ten-point-nine/freETarget/Documentation/Multi Function Switches.docx

# freETarget

Application Note: Multi Function Switches

SUMMARY

freETarget supports a pair of push button switches that can be used to customize the operation of the unit while in the target holder.

MULTIFUNCTION SWITCHES

There are two switches that can be used interchangeably, ie what can be done with A can be done with B. The JSON string {“MFS”:VVVVV} controls the function of the switches in tap or hold as shown in Table 1. The functions available are shown in Table 2.

Table 1: MFS Control

Value | Use
Vxxxx | Value controls hold on Switches 1 & 2
xVxxx | Value controls Tap on Switch 2
xxVxx | Value controls Tap on Switch 1
xxVx | Value controls Hold on Switch 2
xxxxV | Value controls Hold on Switch 1

Table 2: MFS Values

Value | Use
0 | Tap to wake up from sleep
1 | Paper feed witness paper
2 | Adjust LED brightness
3 | Advance paper one shot cycle
4 | PC Shot Test
5 | Put target to sleep or wake it up
6
7
8
9

OPERATION

The operation of the switches is controlled by how long the switches are pressed for

Tap: Press switch for less than ½ second

Hold: Press and hold the switch for more than ½ second

Holding 1&2 and resetting the power will put the configuration back to the factory defaults.

EXAMPLES

Example: 20351

2 – Hold 1 & 2 to adjust LED brightness

0 – Tap 2 to wake up from sleep

3 – Tap 1 to advance paper one shot cycle

5 – Hold 2 to put target to sleep

1 – Hold 1 to load paper feed
