ten-point-nine/freETarget/Documentation/Pictures/50 Meter Pistol Target.docx

# freETarget

Application Note: 50 Meter Pistol Target

SUMMARY

freeETarget can be used as a 50 meter pistol target with the same hardware as the conventional 10 meter target. The differences being the use of a semi-ridgid backing material and setting the sensors for the larger paper.

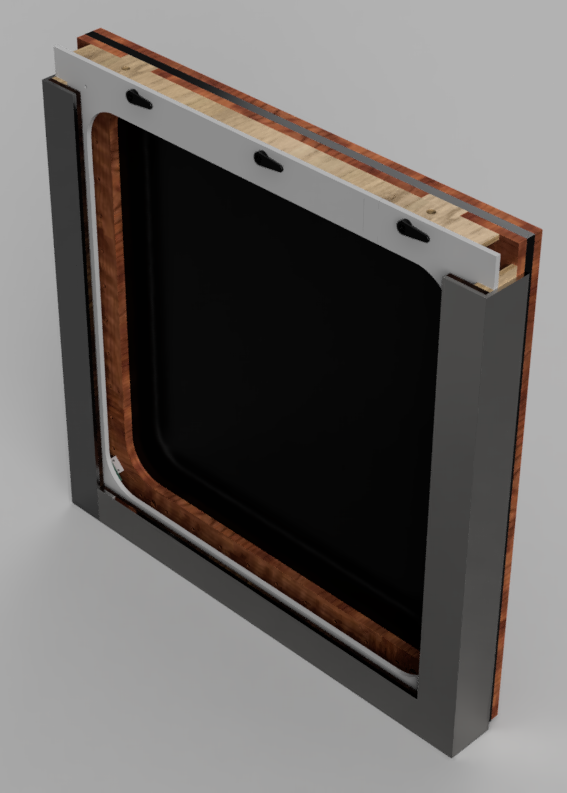
[picture p22: figure]

Figure 1” 50 Meter Pistol Target

CONSTRUCTION

Construction follows the same process as a simple 10 meter air target. The differences are:

- Larger 778 mm sensor spacing
- No lights or witness paper
- Heavy rubber mat before the bullet trap

The target is constructed by laminating a series of items together. The construction is shown in Figure 2 and itemized in Table

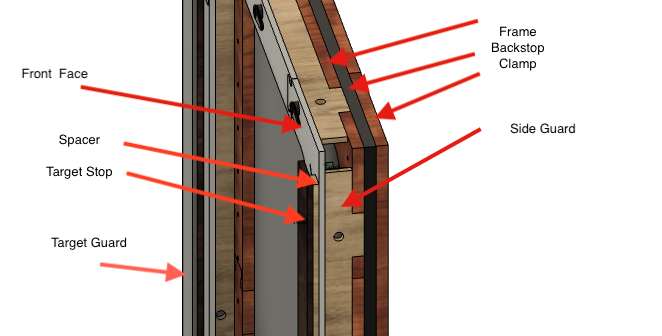
[picture p23: figure]

Figure 2: Target Build Up

Table 1: Target Components

Item | Description | Material
Frame | Rectangular frame to assemble target | ½” Plywood
Backstop | Rubber mat to sound projectile | ¼” Neoprene truck liner
Clamp | Rectangular frame to hold backstop | ½ Plywood
Sensor Mount | Plywood sensor mount (not shown) | ½” Plywood
Sensor | Electronic circuit (not shown)
Sie Guard | Prevent debris from getting to sensors | ¼” Plywood
Front Face | Rectangular frame to hold target in place | ¼” Plywood
Spacer | Strip of material spce cardboard backer | ¼” Plywood
Target Stop | Strip of material to hold target in place | ¼” Plywood
Target Guard | 1/8” Steel L bracket to protect from shots | 2”x2”x1/8 Steel L bracket

Start by construction a target frame large enough to support the target. The frame illustrated in Figure 3 is 650 mm x 650mm ½” plywood. To save on wood and fit into a small workshop, the frame is made from four hocky-stick segments

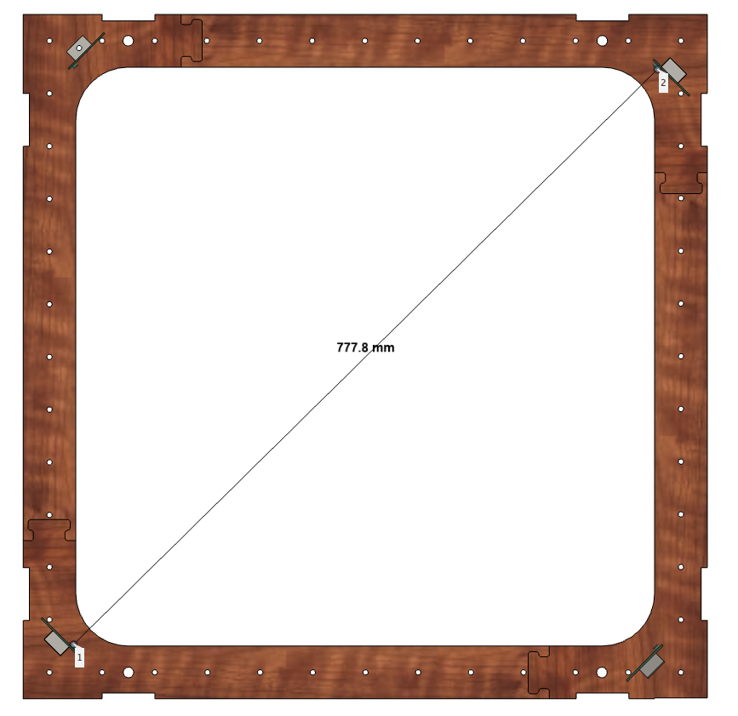
[picture p24: figure]

Figure 3: Sensor Location

Build the clamp using the same construction as the frame. If you made the frame from four segments as shown in Figure 3, reverse the segments to that the joints don’t line up.

Locate the rubber backstop between the frame and clamp. Drill 5mm holes between the frame and clamp, through the rubber every 50mm. Use 5x40mm bolts from the front to the back and tighten with nuts. When finished the target will be a ridged frame

Attach the sensors and cables to the sensor mounts

Build the front face using ¼” plywood similar to the frame.

Align the front face to the frame and drill 5mm holes through the sensor mounts
