ten-point-nine/freETarget/Documentation/Technical/freETarget Layout.pdf

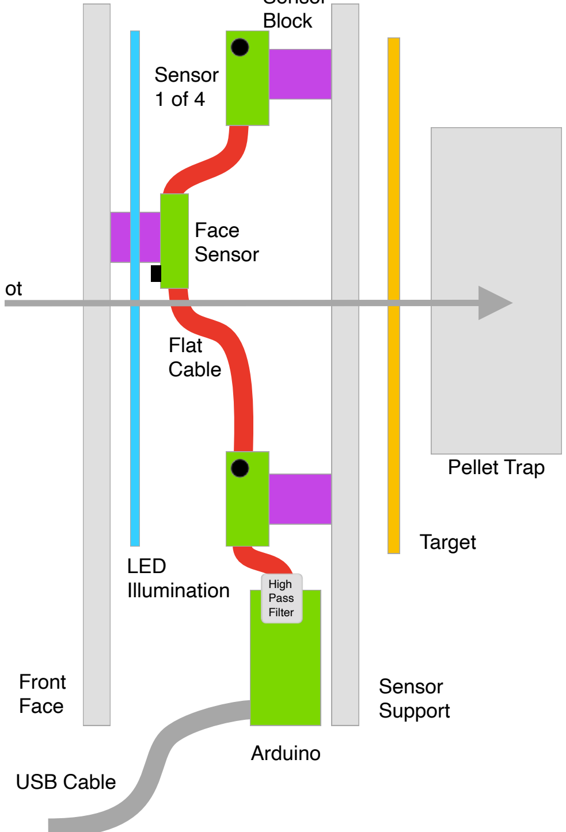
[picture p29: figure]
Front Face; LED Illumination; Flat Cable; Sensor Support; Arduino; Block; Face Sensor; Sensor 1 of 4; Target; Pellet Trap; USB Cable; High Pass Filter; Shot

Sensor
