ten-point-nine/freETarget/Documentation/Technical/Sensor Geometry.pdf

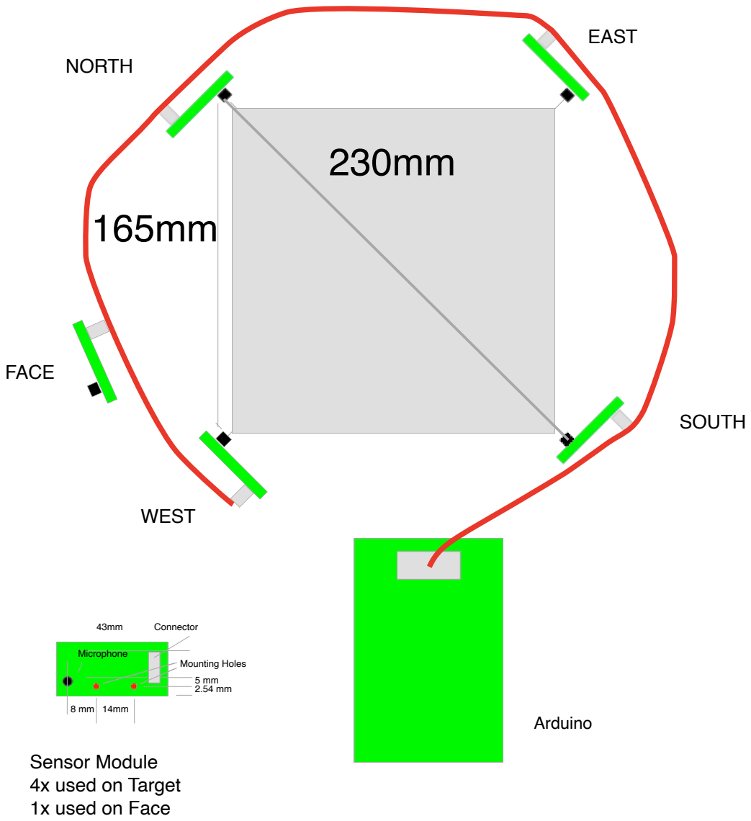
[picture p30: figure]
EAST; NORTH; SOUTH; WEST; 230 mm Dia; Microphone; Mounting Holes; Sensor Module 4x used on Target 1x used on Face; Arduino; Connector; FACE
