ten-point-nine/freETarget/Documentation/Pictures/Illustrations/Sensor Template.pdf

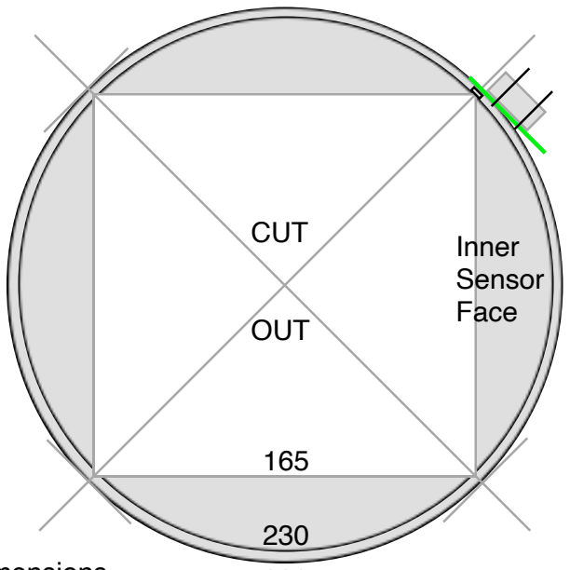
[picture p32: figure]
CUT; OUT; Inner Sensor Face

45.5

2.5
15 14

3dia

7.5

23

7.5

50mm
x
50mm
Print
Reference
All dimensions | 239
in mm

Outer
Block
Face
