ten-point-nine/freETarget/Mechanical/CNC/6mm Panel/Door Dimensions.pdf

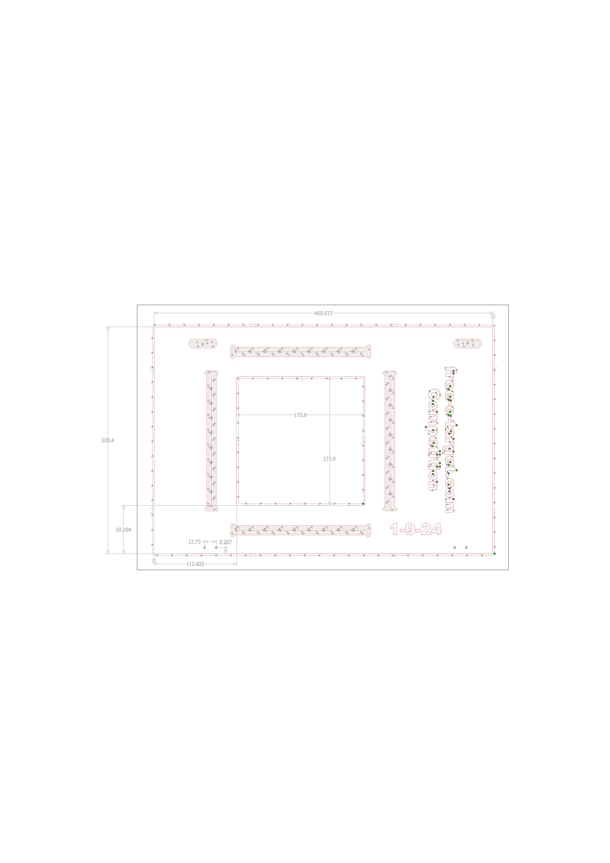
[picture p33: page 1]
