ten-point-nine/freETarget/Documentation/Technical/Sample Calculations.pdf

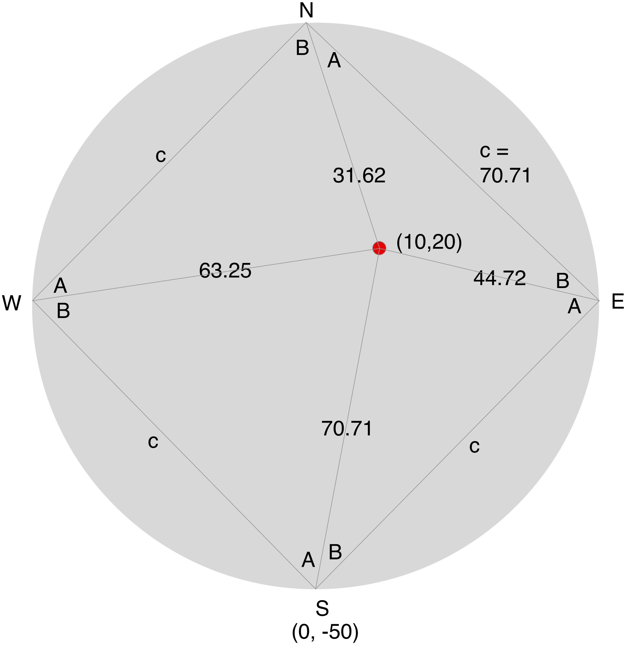
[picture p34: figure]

(50,0)
(-50,0)

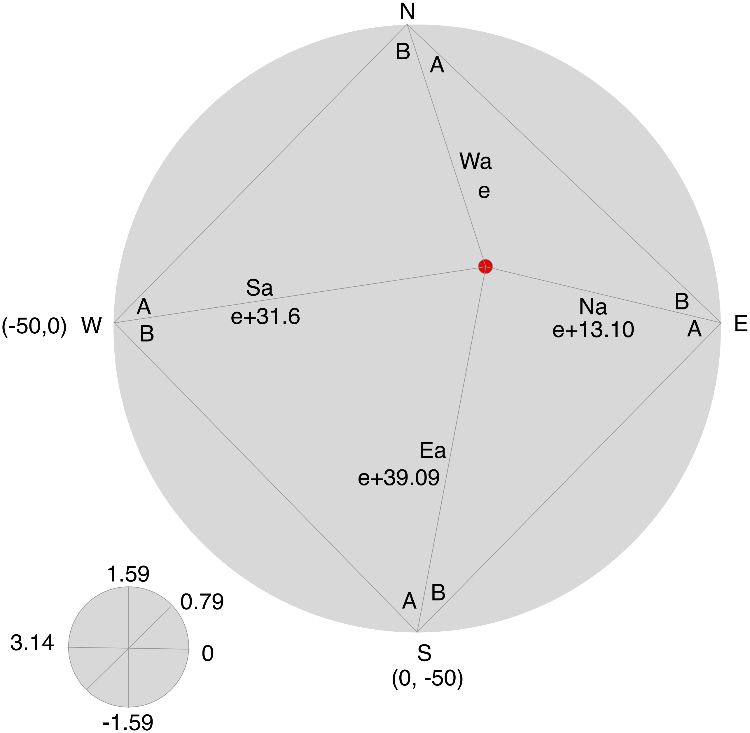
[picture p35: figure]

(50,0)

(50,0)

A

a

C

B

b

c

a^2 = b^2 + c^2 - 2bc*cos(A)

cos(A) = a^2 - b^2 -c^2
-2bc

( a^2 - b^2 - c^2 )
( | -2bc. | )

A = cos-1
