ten-point-nine/freETarget/Documentation/Pictures/Illustrations/Annotated Circuit.pdf

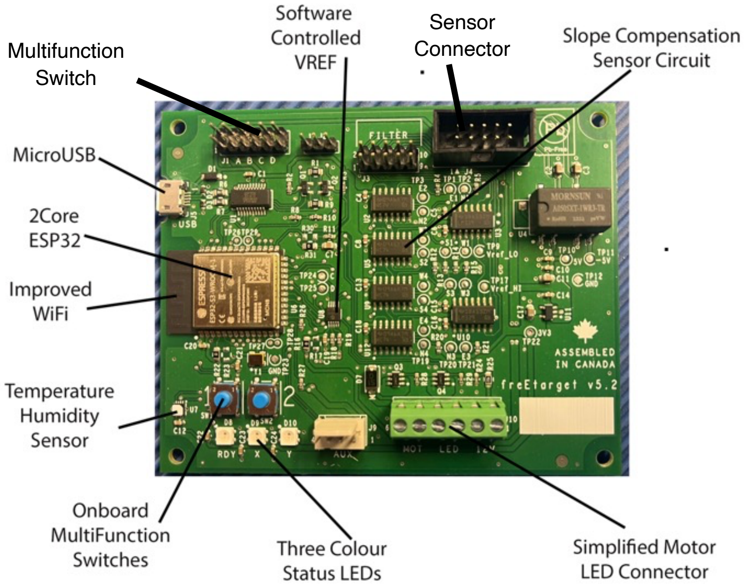
[picture p36: page 1]
