ten-point-nine/freETarget/Documentation/Pictures/15 Meter USB Cable.jpg

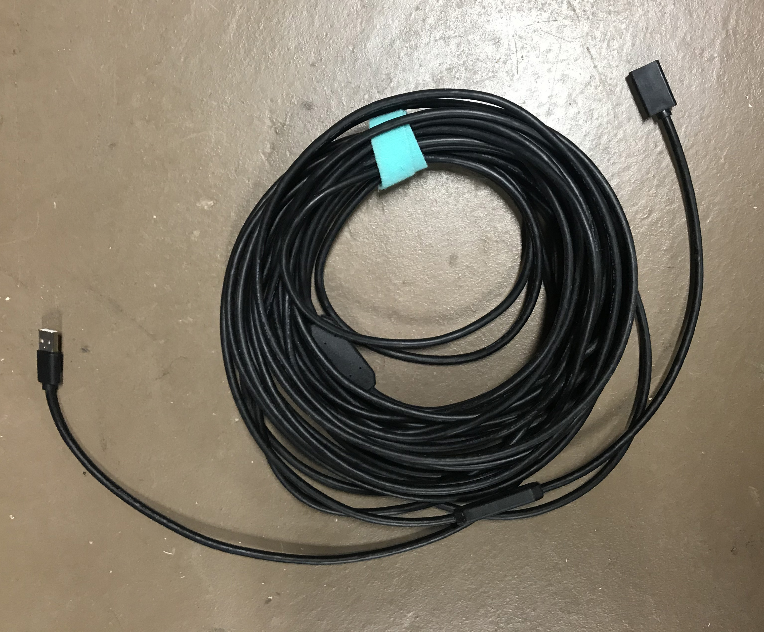
Documentation/Pictures/15 Meter USB Cable.jpg
