ten-point-nine/freETarget/Documentation/Pictures/Accessory Connector.png

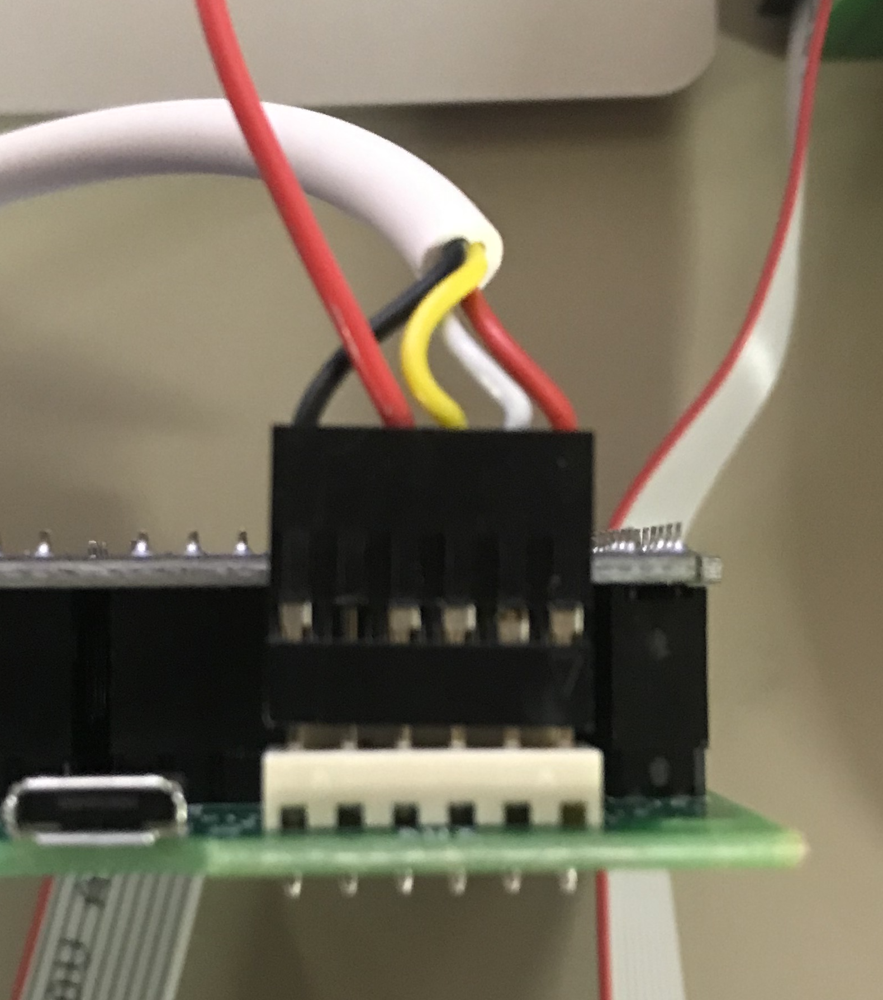
Documentation/Pictures/Accessory Connector.png
