ten-point-nine/freETarget/Documentation/Pictures/Board.jpg

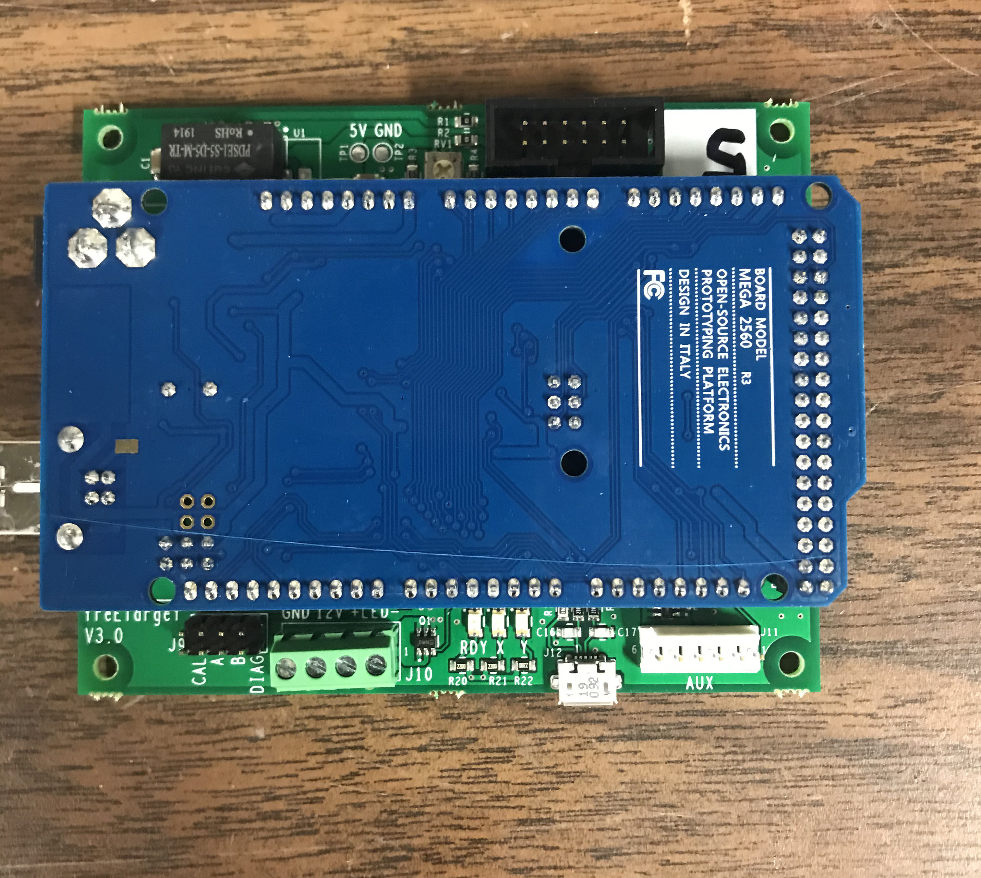
Documentation/Pictures/Board.jpg
