ten-point-nine/freETarget/Documentation/Pictures/Cut Cardboard.png

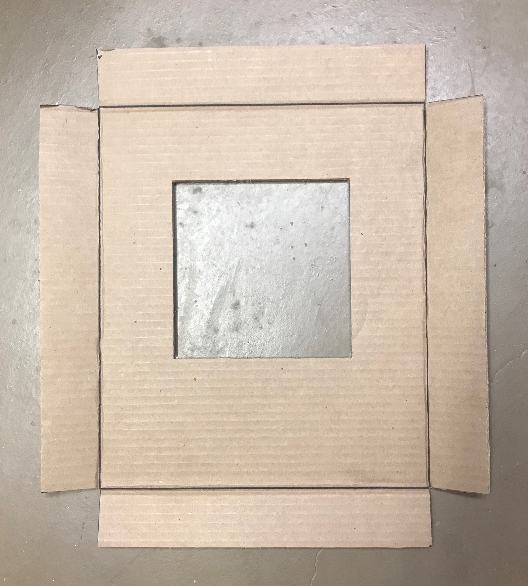
Documentation/Pictures/Cut Cardboard.png
