ten-point-nine/freETarget/Documentation/Pictures/DC Motor Connection II.png

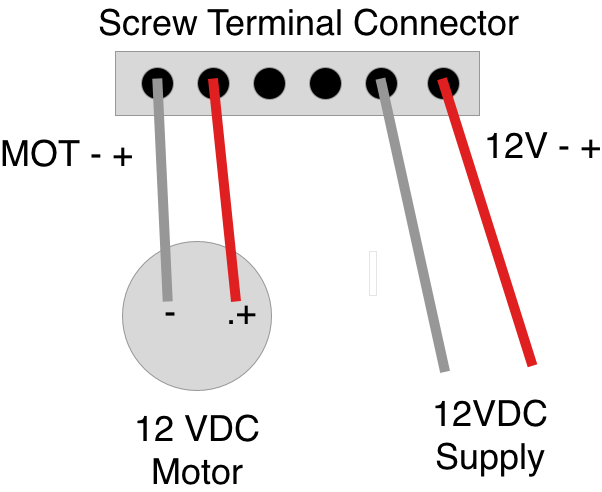
Documentation/Pictures/DC Motor Connection II.png
