ten-point-nine/freETarget/Documentation/Pictures/Folded Cardboard.png

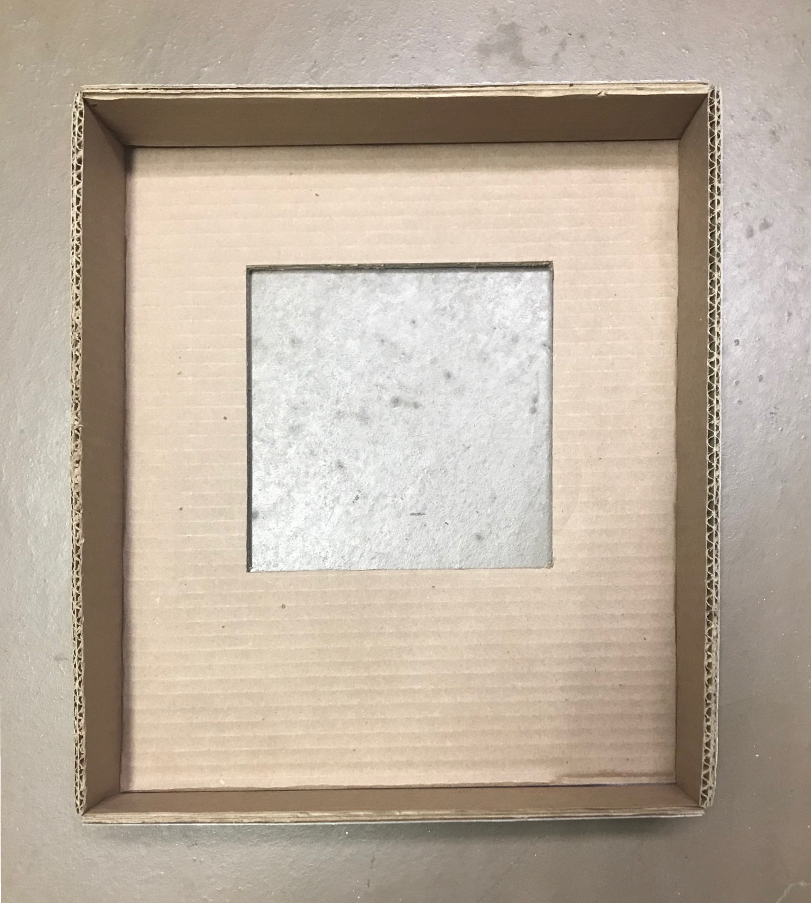
Documentation/Pictures/Folded Cardboard.png
