ten-point-nine/freETarget/Documentation/Pictures/freETarget Rapid Fire.png

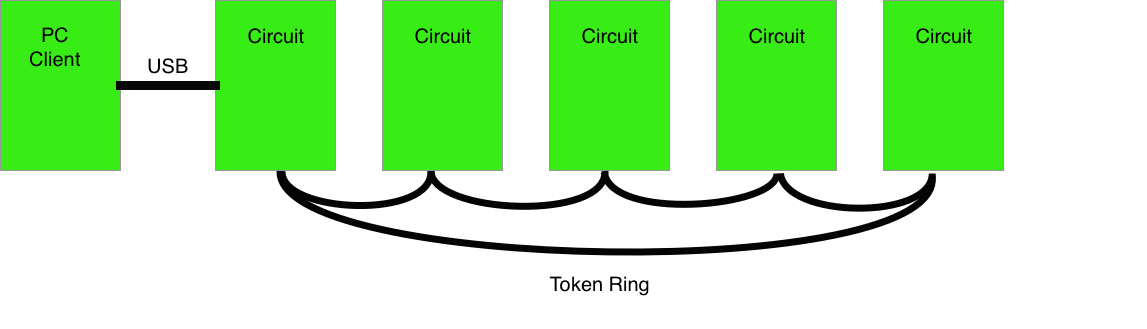
Documentation/Pictures/freETarget Rapid Fire.png
