ten-point-nine/freETarget/Documentation/Pictures/freETarget.jpg

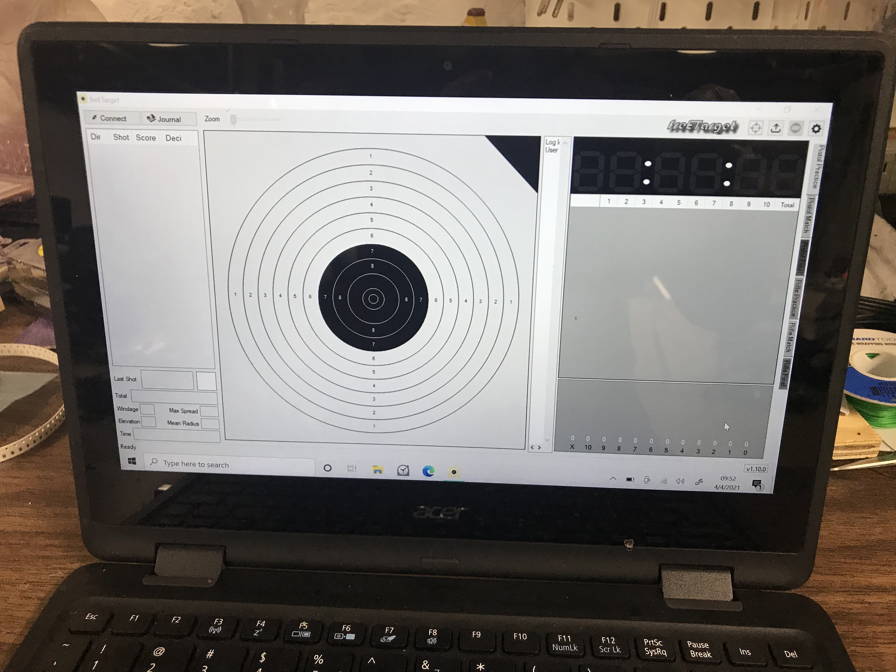
Documentation/Pictures/freETarget.jpg
