ten-point-nine/freETarget/Documentation/Pictures/GRID_PATTERN.jpg

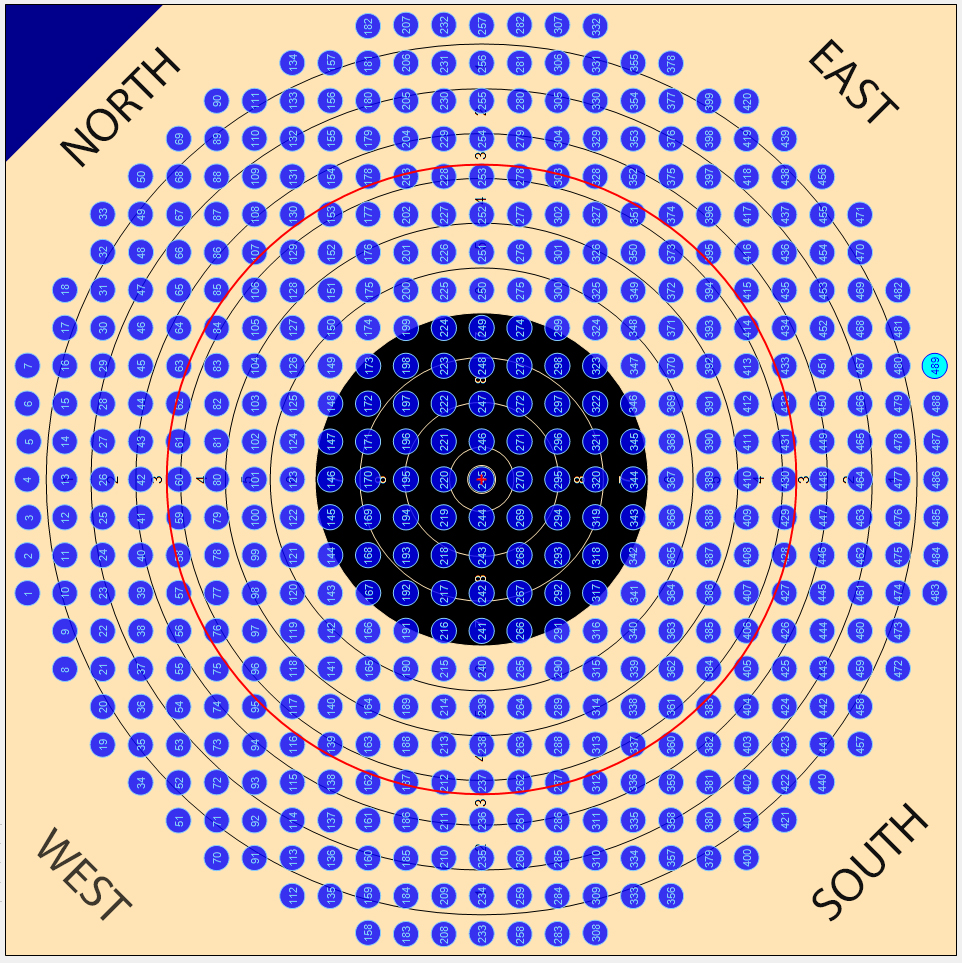
Documentation/Pictures/GRID_PATTERN.jpg
