ten-point-nine/freETarget/Documentation/Pictures/Illustrations/Application Configuration.png

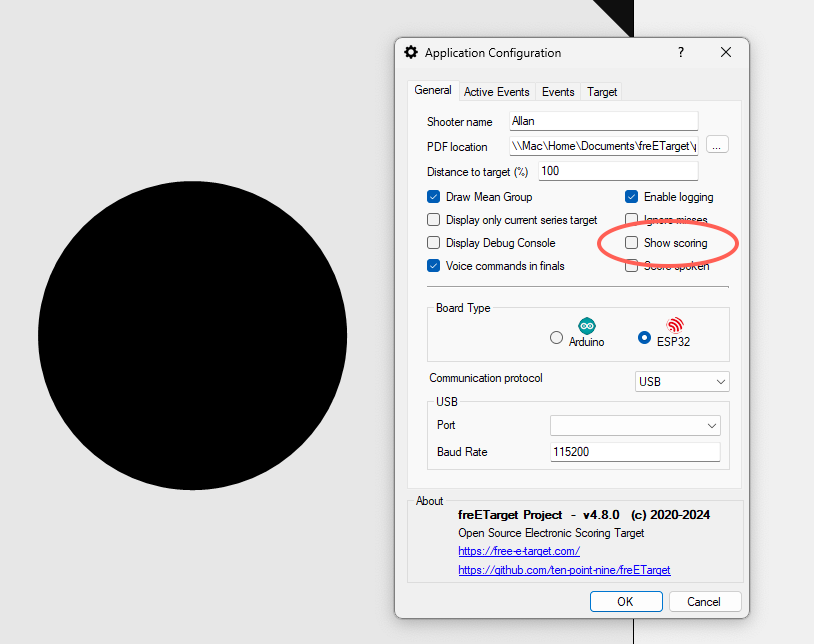
Documentation/Pictures/Illustrations/Application Configuration.png
