ten-point-nine/freETarget/Documentation/Pictures/Illustrations/Ethernet Cable V5 Harness.png

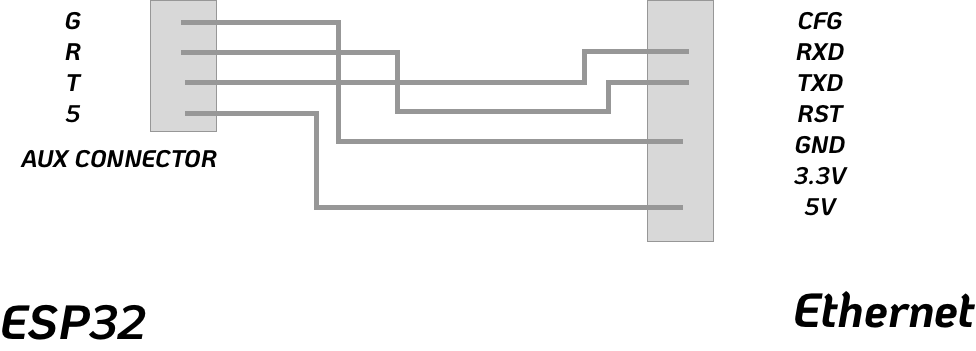
Documentation/Pictures/Illustrations/Ethernet Cable V5 Harness.png
