ten-point-nine/freETarget/Documentation/Pictures/Illustrations/Flat Cable.png

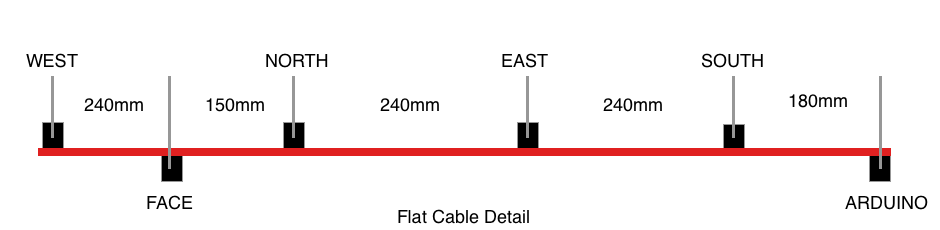
Documentation/Pictures/Illustrations/Flat Cable.png
