ten-point-nine/freETarget/Documentation/Pictures/Illustrations/freETarget Basic Layout.png

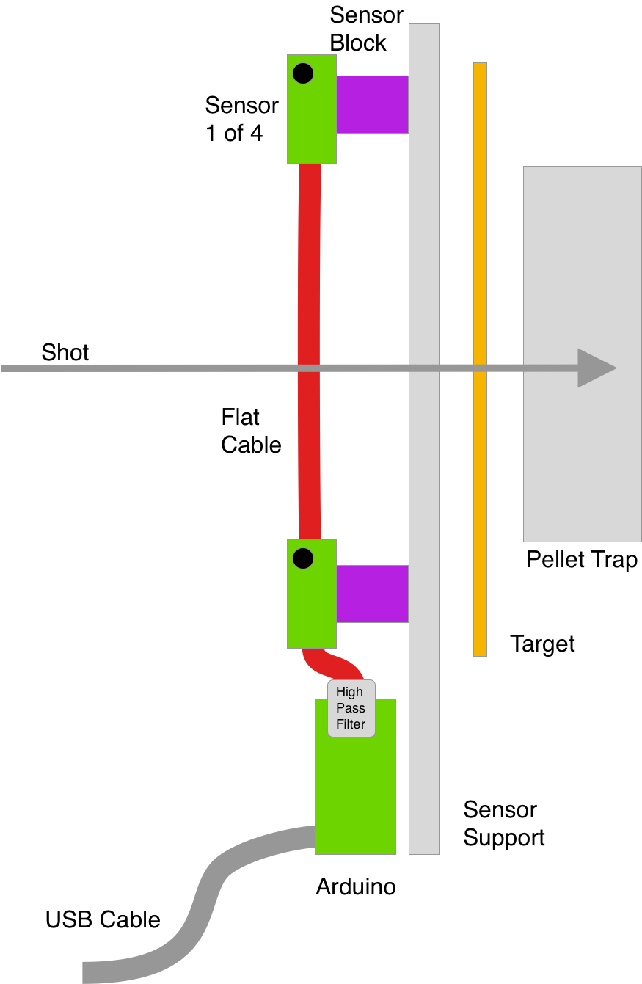
Documentation/Pictures/Illustrations/freETarget Basic Layout.png
