ten-point-nine/freETarget/Documentation/Pictures/Illustrations/freETarget Layout.png

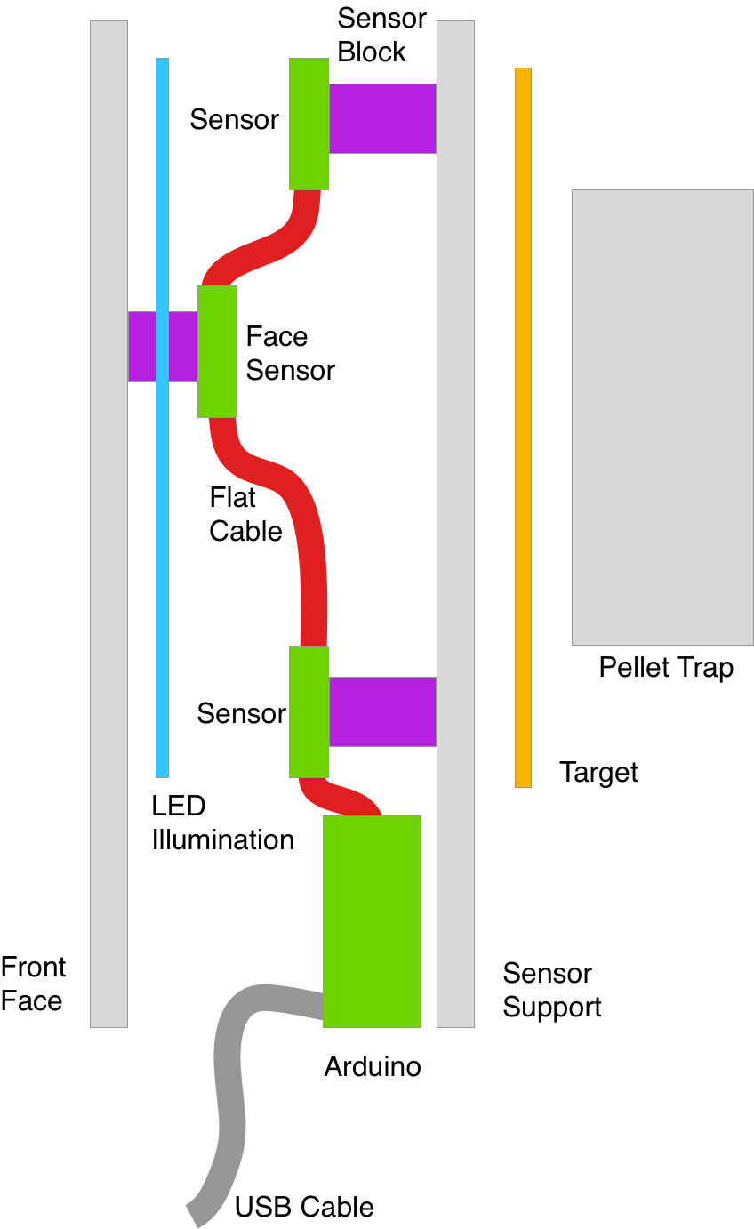
Documentation/Pictures/Illustrations/freETarget Layout.png
