ten-point-nine/freETarget/Documentation/Pictures/Illustrations/Front View.png

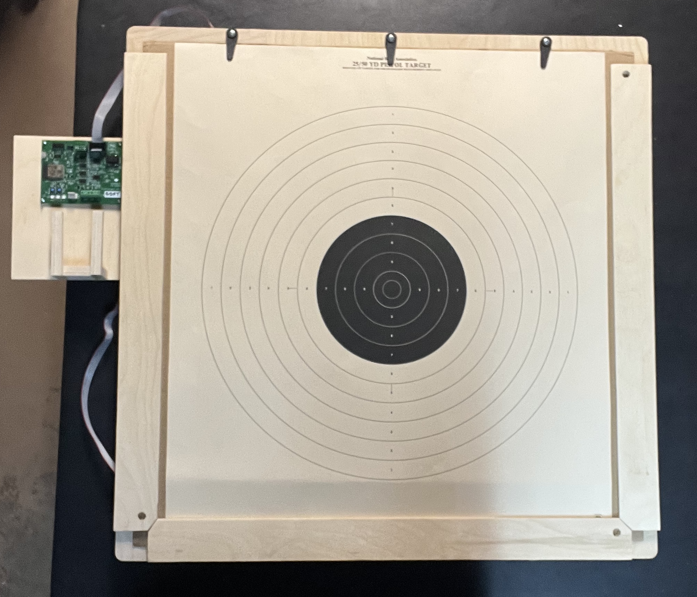
Documentation/Pictures/Illustrations/Front View.png
