ten-point-nine/freETarget/Documentation/Pictures/Illustrations/Interiour Sheves.png

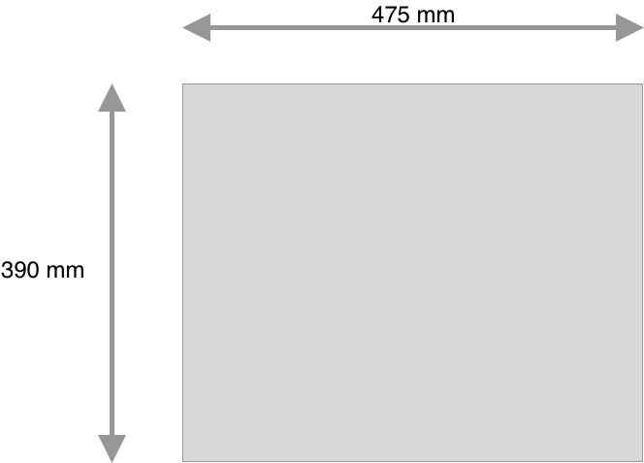
Documentation/Pictures/Illustrations/Interiour Sheves.png
