ten-point-nine/freETarget/Documentation/Pictures/Illustrations/LiveTarget.png

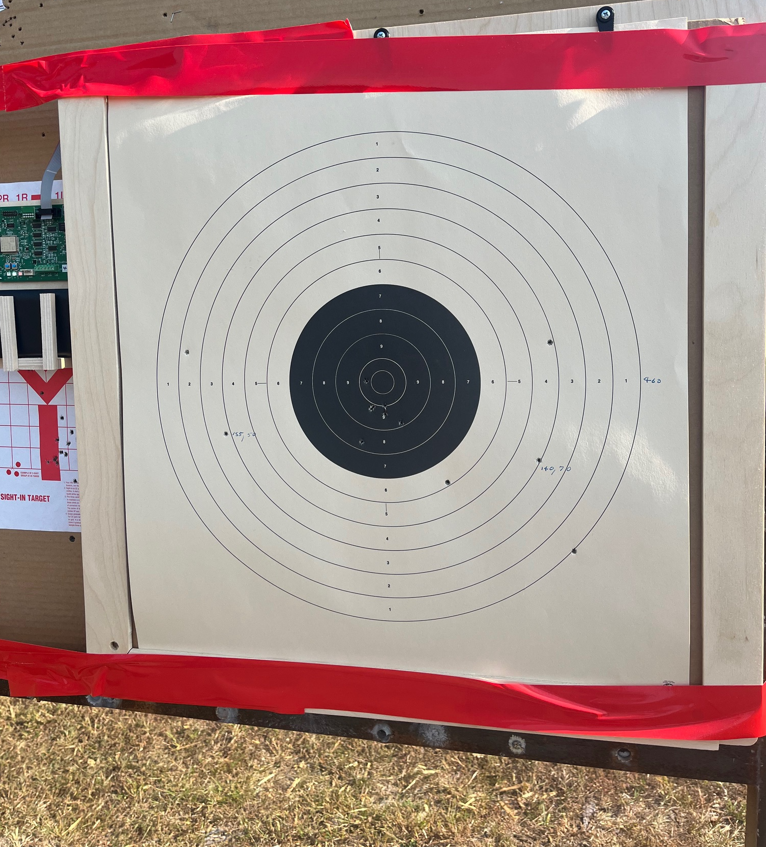
Documentation/Pictures/Illustrations/LiveTarget.png
