ten-point-nine/freETarget/Documentation/Pictures/Illustrations/Multi Function Connector.png

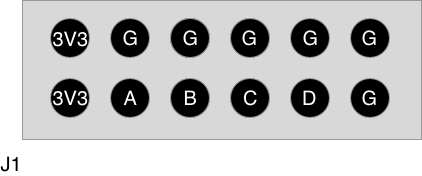
Documentation/Pictures/Illustrations/Multi Function Connector.png
