ten-point-nine/freETarget/Documentation/Pictures/Illustrations/PC Client.png

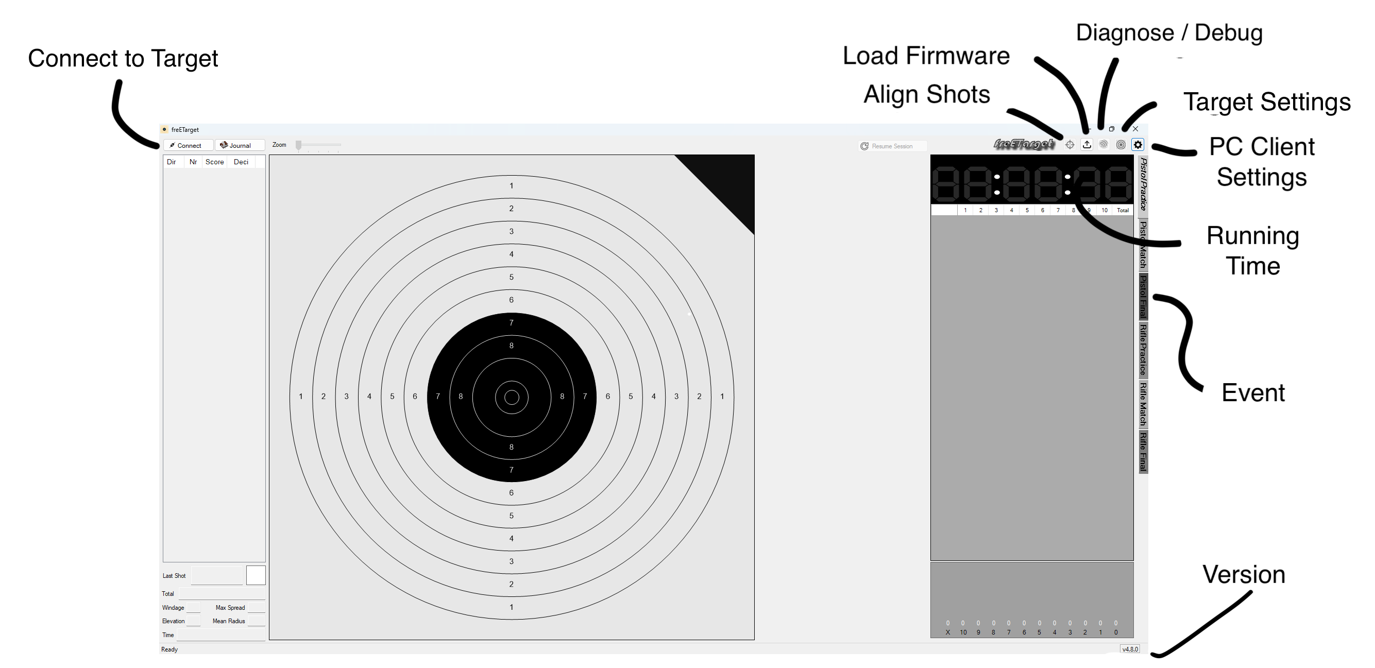
Documentation/Pictures/Illustrations/PC Client.png
