ten-point-nine/freETarget/Documentation/Pictures/Illustrations/Ribbon Cable.png

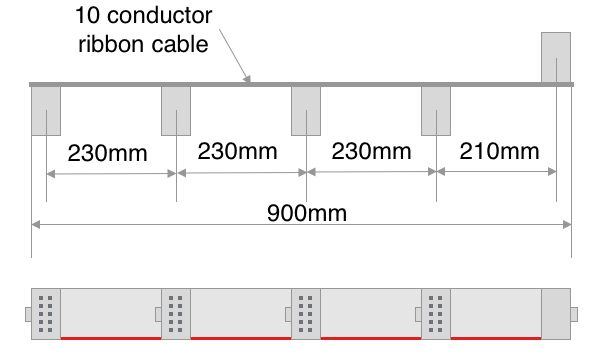
Documentation/Pictures/Illustrations/Ribbon Cable.png
