ten-point-nine/freETarget/Documentation/Pictures/Illustrations/RS485 Cable Harness.png

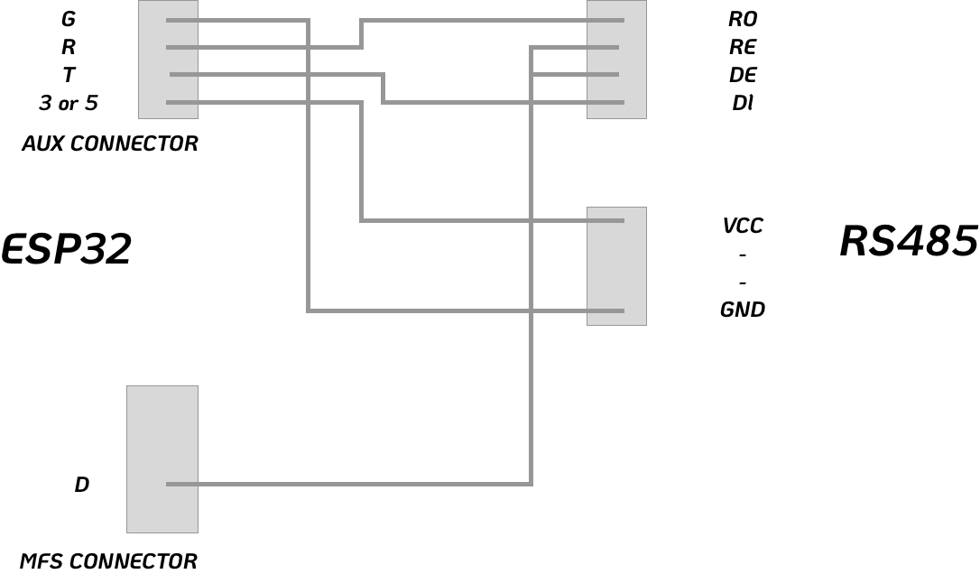
Documentation/Pictures/Illustrations/RS485 Cable Harness.png
