ten-point-nine/freETarget/Documentation/Pictures/Illustrations/RS485.png

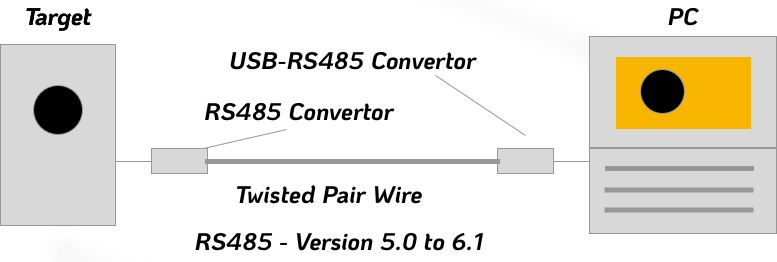
Documentation/Pictures/Illustrations/RS485.png
