ten-point-nine/freETarget/Documentation/Pictures/Illustrations/RS485V5.png

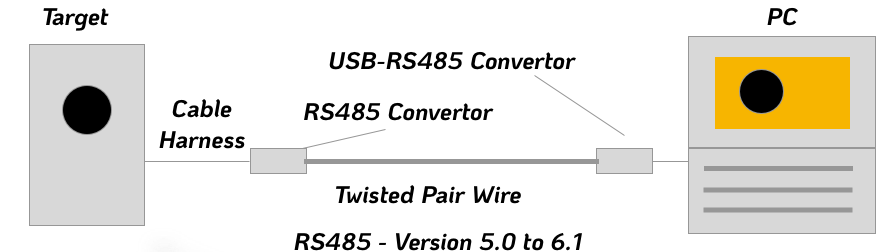
Documentation/Pictures/Illustrations/RS485V5.png
