ten-point-nine/freETarget/Documentation/Pictures/Illustrations/RS485V6.png

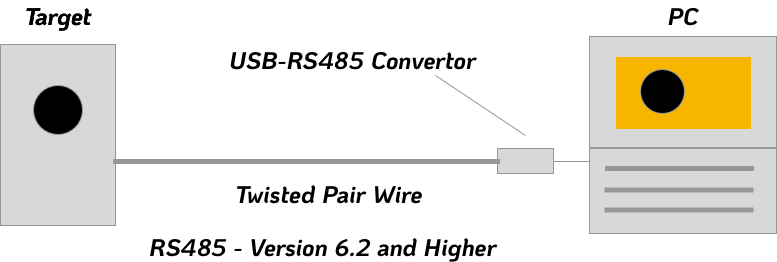
Documentation/Pictures/Illustrations/RS485V6.png
