ten-point-nine/freETarget/Documentation/Pictures/Illustrations/RS488 Cable Harness.png

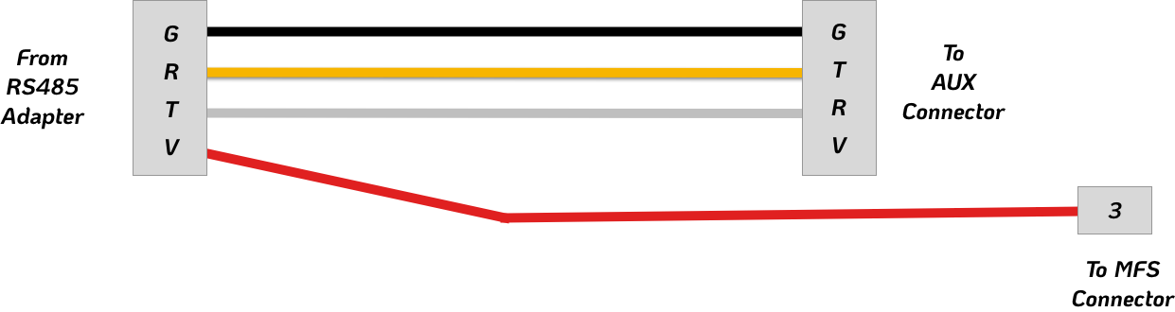
Documentation/Pictures/Illustrations/RS488 Cable Harness.png
