ten-point-nine/freETarget/Documentation/Pictures/Illustrations/Sensor Dimensions.png

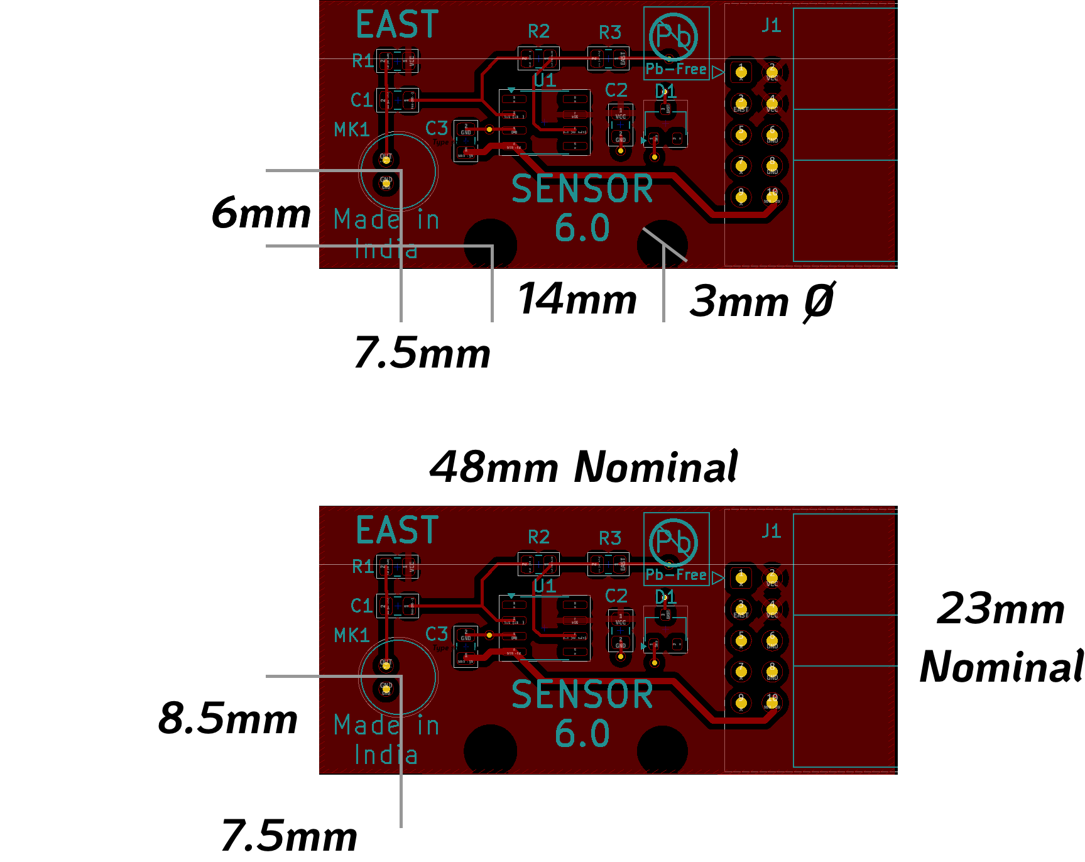
Documentation/Pictures/Illustrations/Sensor Dimensions.png
