ten-point-nine/freETarget/Documentation/Pictures/Illustrations/Shelves.png

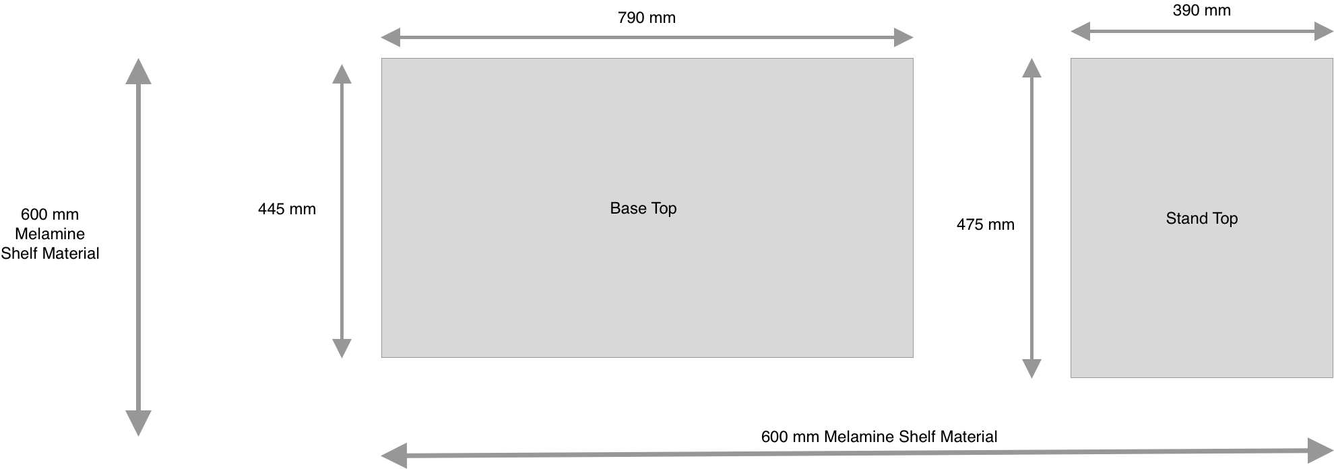
Documentation/Pictures/Illustrations/Shelves.png
