ten-point-nine/freETarget/Documentation/Pictures/Illustrations/Shooting Table.png

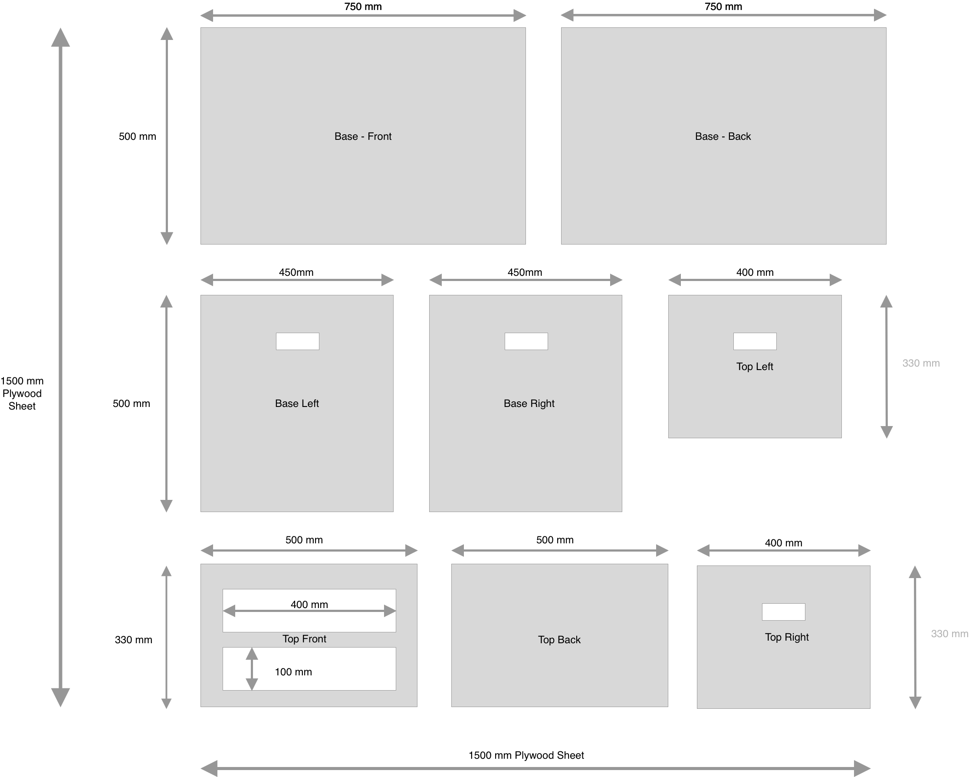
Documentation/Pictures/Illustrations/Shooting Table.png
