ten-point-nine/freETarget/Documentation/Pictures/Illustrations/Stepper Motor Drive.png

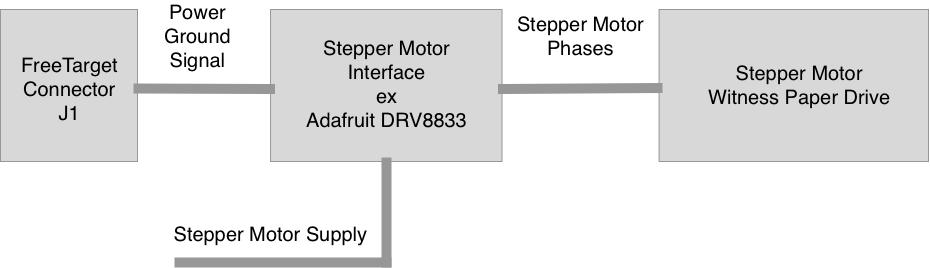
Documentation/Pictures/Illustrations/Stepper Motor Drive.png
