ten-point-nine/freETarget/Documentation/Pictures/Illustrations/Target Range Basic.png

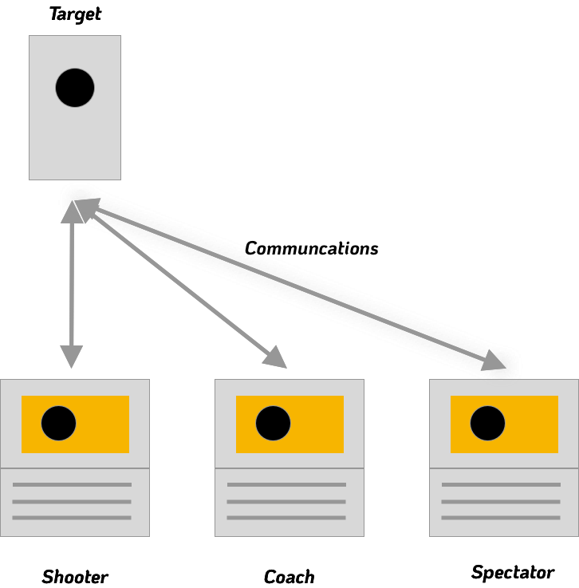
Documentation/Pictures/Illustrations/Target Range Basic.png
