ten-point-nine/freETarget/Documentation/Pictures/Illustrations/Target Range Ethernet Adapter.png

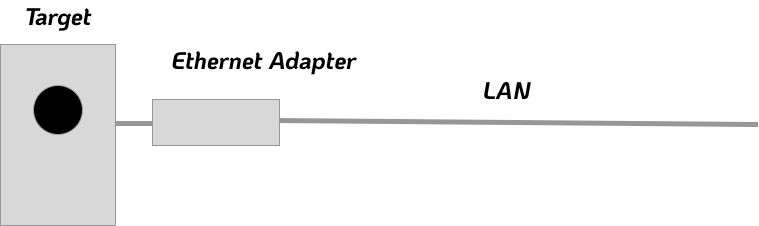
Documentation/Pictures/Illustrations/Target Range Ethernet Adapter.png
