ten-point-nine/freETarget/Documentation/Pictures/Illustrations/Target Range Ethernet.png

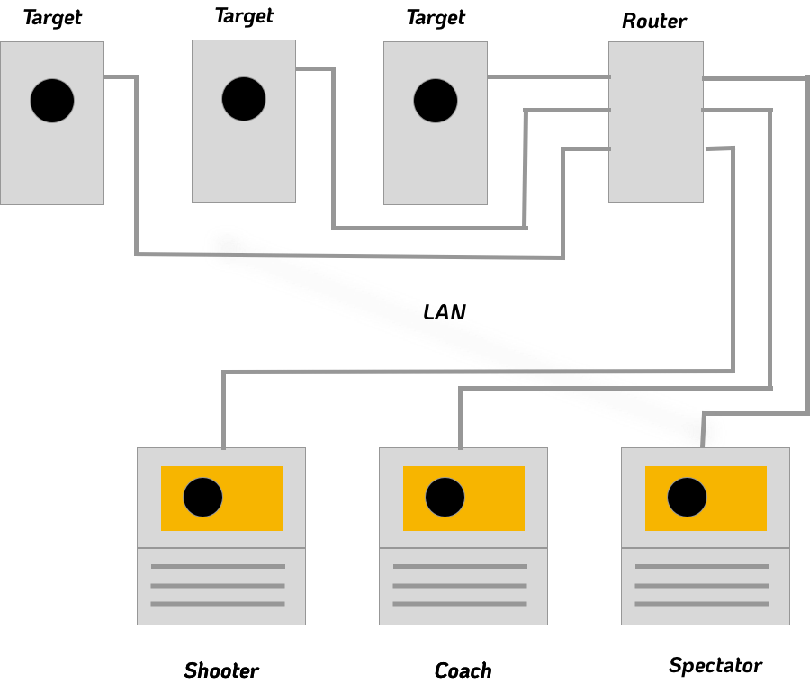
Documentation/Pictures/Illustrations/Target Range Ethernet.png
