ten-point-nine/freETarget/Documentation/Pictures/Illustrations/Target Range Simple.png

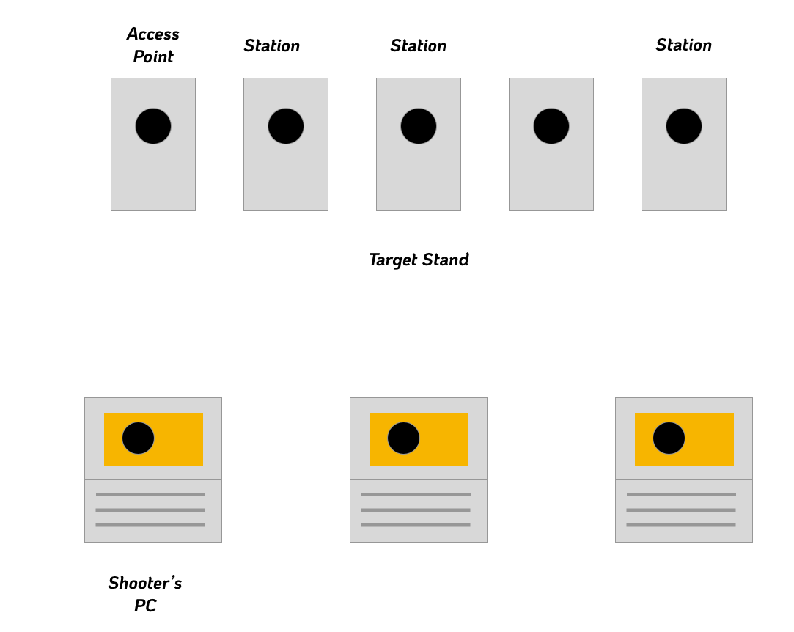
Documentation/Pictures/Illustrations/Target Range Simple.png
