ten-point-nine/freETarget/Documentation/Pictures/Illustrations/Target Range Single.png

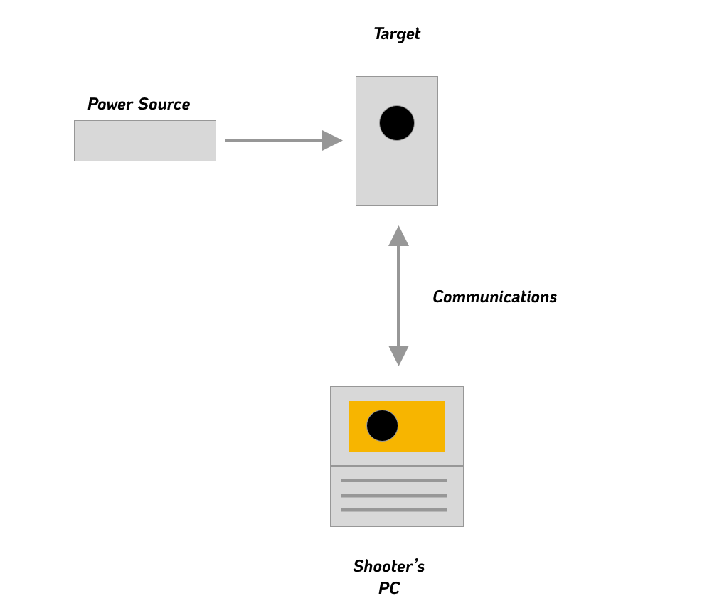
Documentation/Pictures/Illustrations/Target Range Single.png
