ten-point-nine/freETarget/Documentation/Pictures/Illustrations/Target Range.png

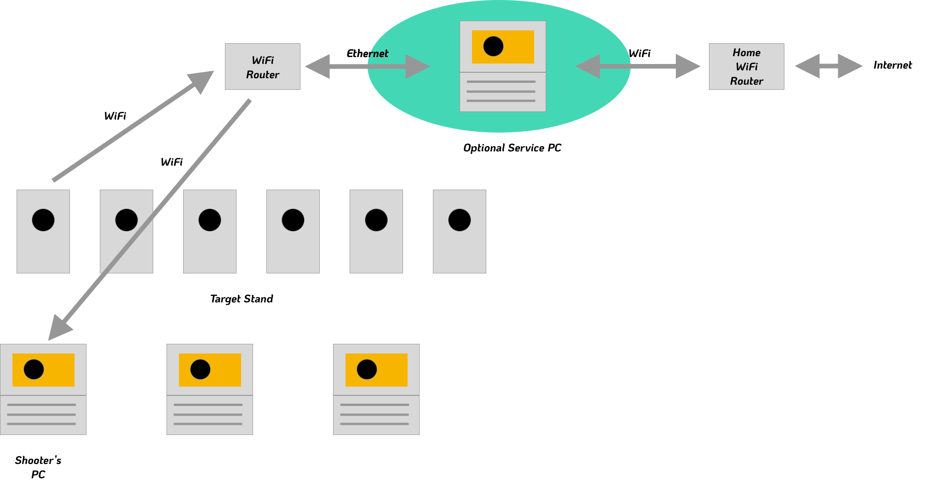
Documentation/Pictures/Illustrations/Target Range.png
