ten-point-nine/freETarget/Documentation/Pictures/Illustrations/USB Extender.png

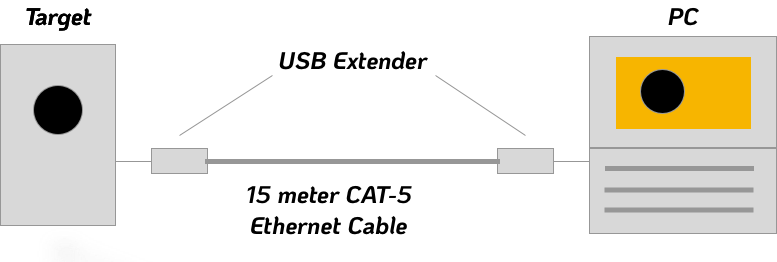
Documentation/Pictures/Illustrations/USB Extender.png
