ten-point-nine/freETarget/Documentation/Pictures/Illustrations/Z_OFFSET.png

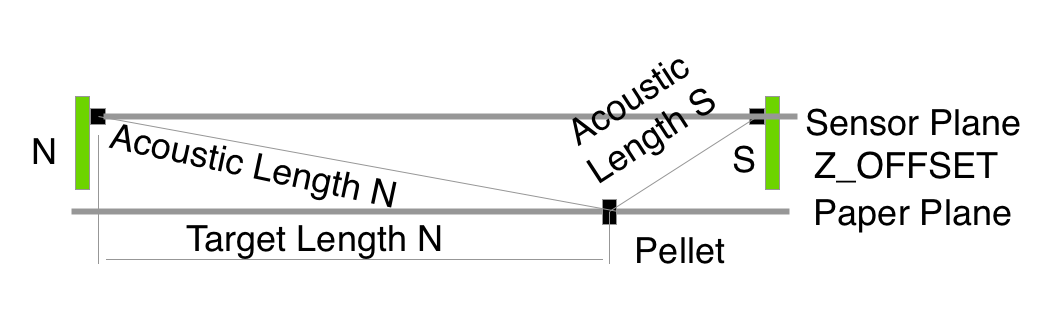
Documentation/Pictures/Illustrations/Z_OFFSET.png
