ten-point-nine/freETarget/Documentation/Pictures/Laptop.jpg

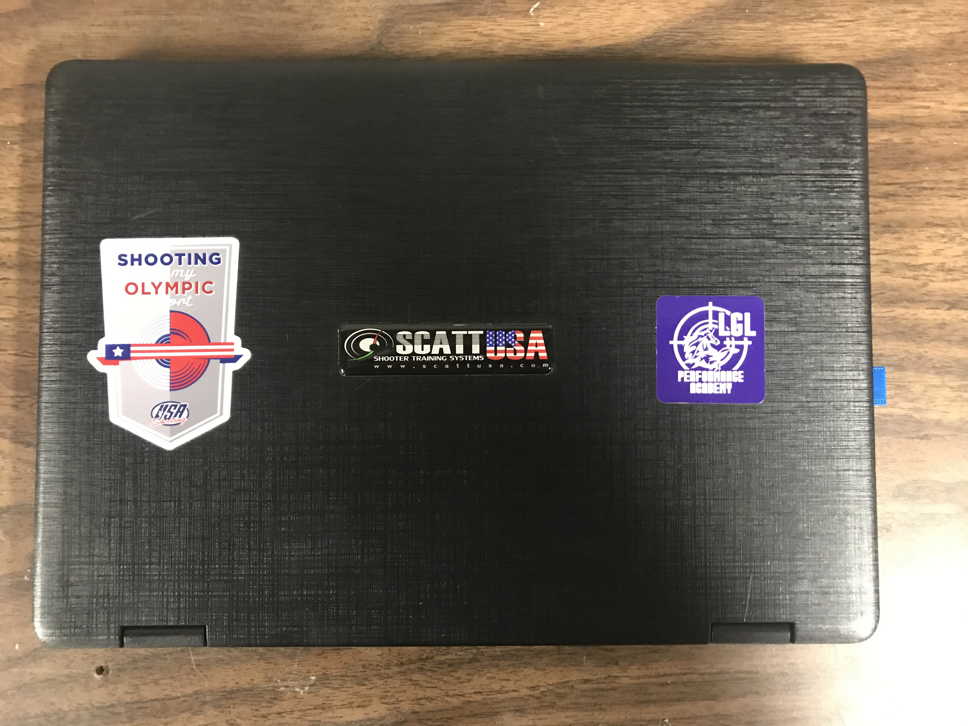
Documentation/Pictures/Laptop.jpg
