ten-point-nine/freETarget/Documentation/Pictures/Marked Cardboard.png

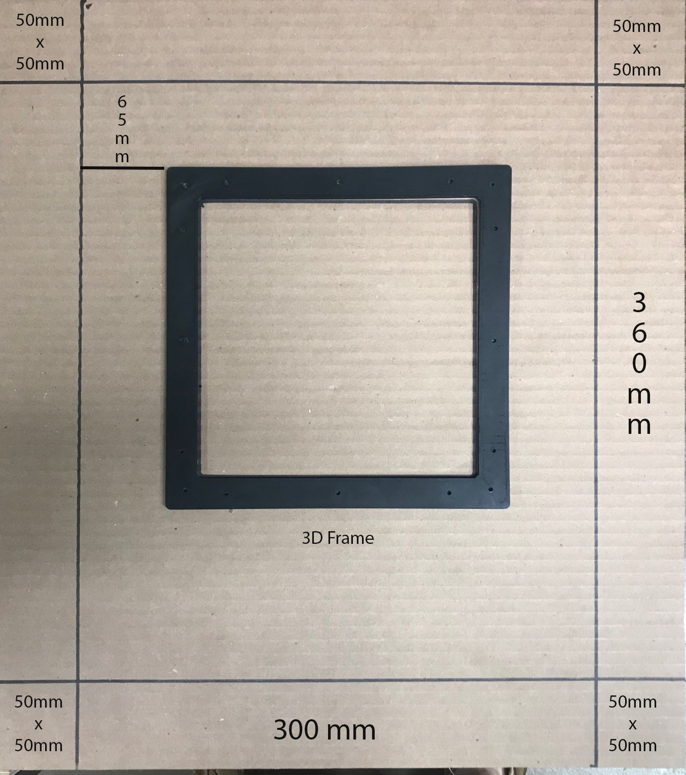
Documentation/Pictures/Marked Cardboard.png
