ten-point-nine/freETarget/Documentation/Pictures/Overlay_60.jpg

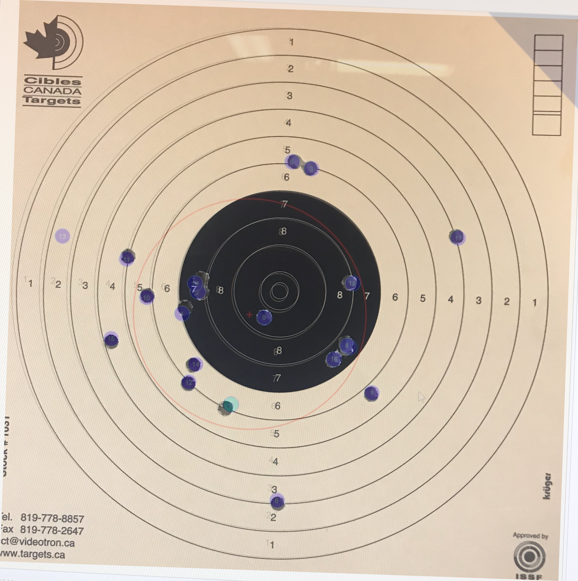
Documentation/Pictures/Overlay_60.jpg
