ten-point-nine/freETarget/Documentation/Pictures/Sample Target.png

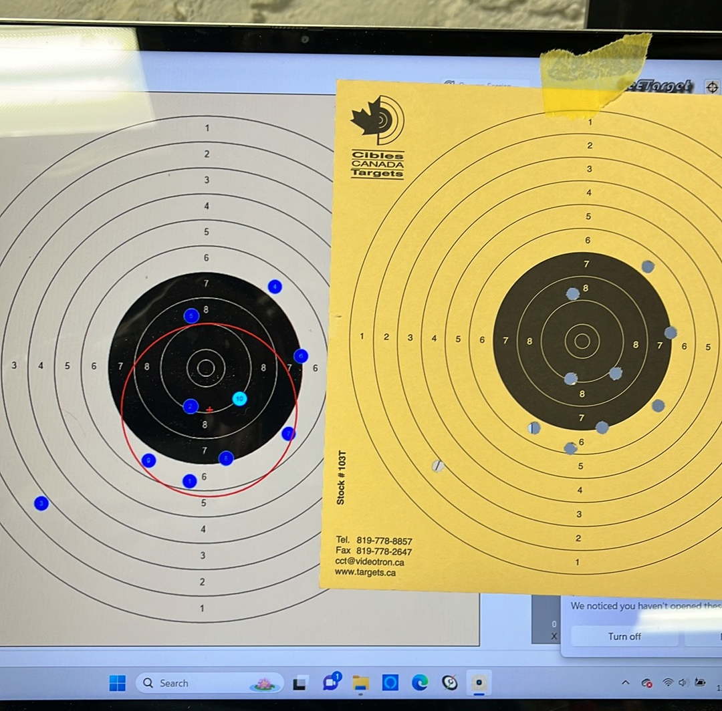
Documentation/Pictures/Sample Target.png
