ten-point-nine/freETarget/Documentation/Pictures/scope traces/SDS00003.bmp

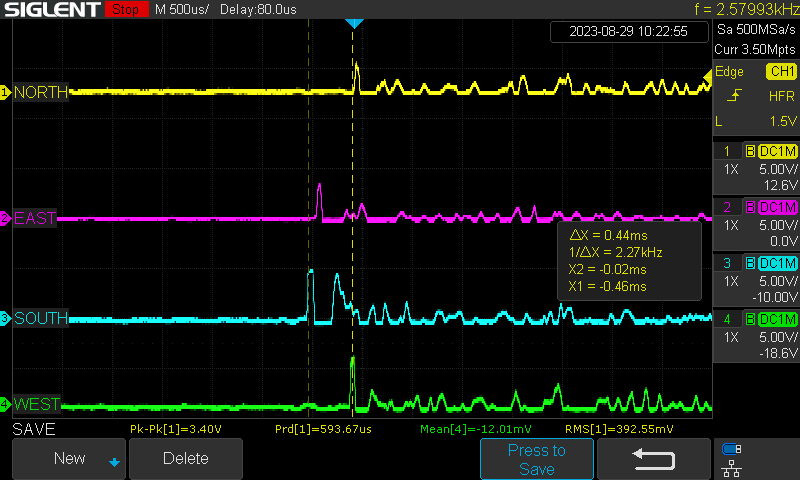
Documentation/Pictures/scope traces/SDS00003.bmp
