ten-point-nine/freETarget/Documentation/Pictures/scope traces/SDS00005.bmp

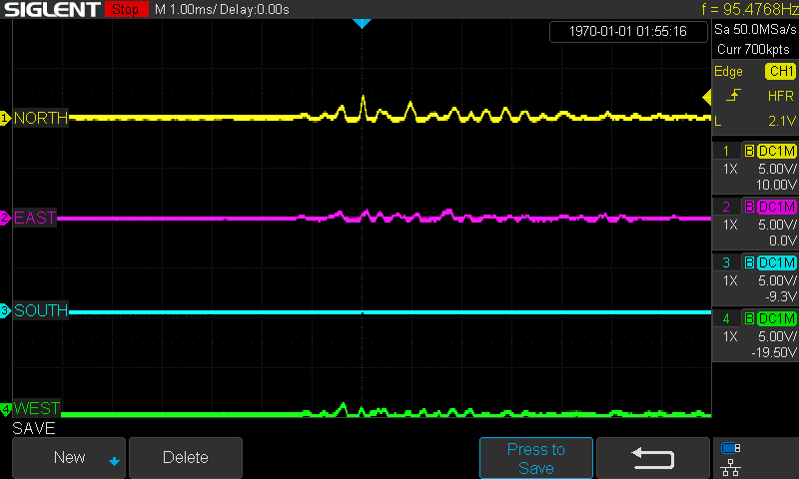
Documentation/Pictures/scope traces/SDS00005.bmp
