ten-point-nine/freETarget/Documentation/Pictures/scope traces/SDS00006.bmp

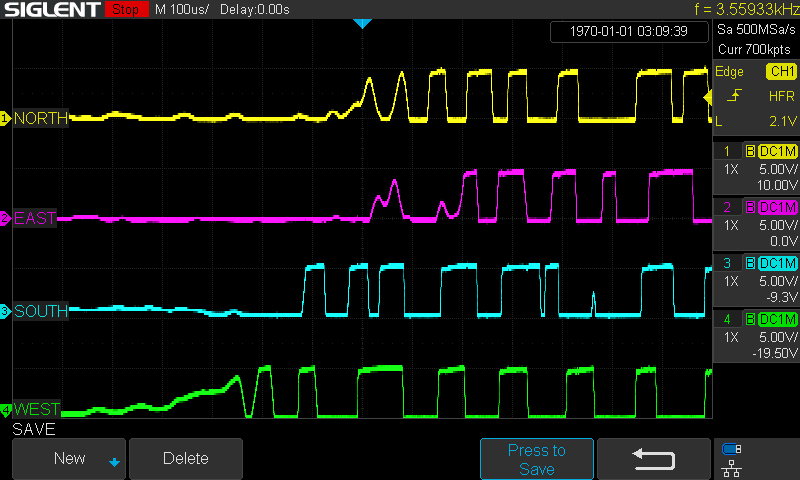
Documentation/Pictures/scope traces/SDS00006.bmp
