ten-point-nine/freETarget/Documentation/Pictures/scope traces/SDS00007.bmp

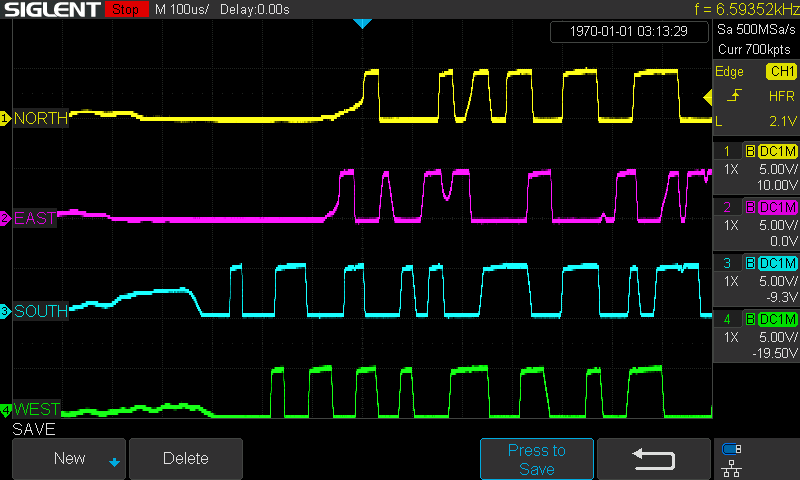
Documentation/Pictures/scope traces/SDS00007.bmp
