ten-point-nine/freETarget/Documentation/Pictures/scope traces/SDS00008.bmp

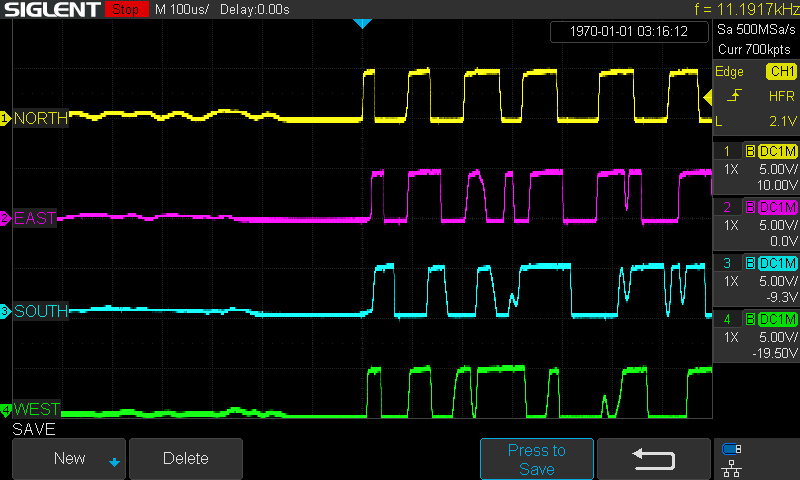
Documentation/Pictures/scope traces/SDS00008.bmp
