ten-point-nine/freETarget/Documentation/Pictures/scope traces/SDS00009.bmp

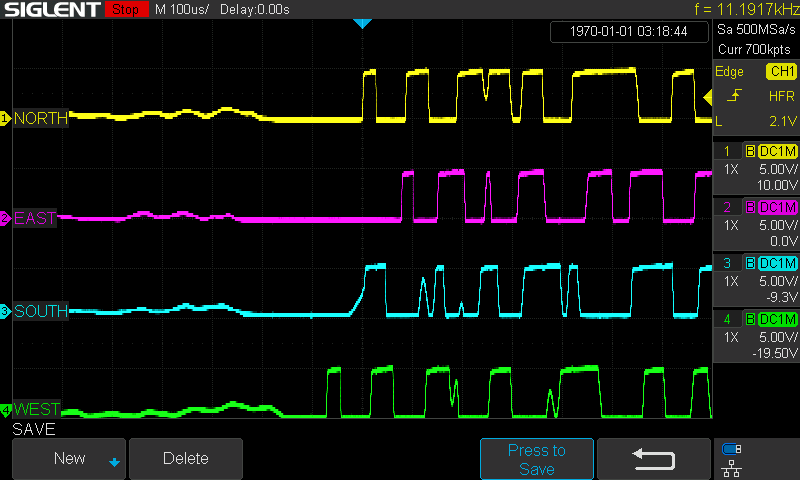
Documentation/Pictures/scope traces/SDS00009.bmp
