ten-point-nine/freETarget/Documentation/Pictures/scope traces/SDS00010.bmp

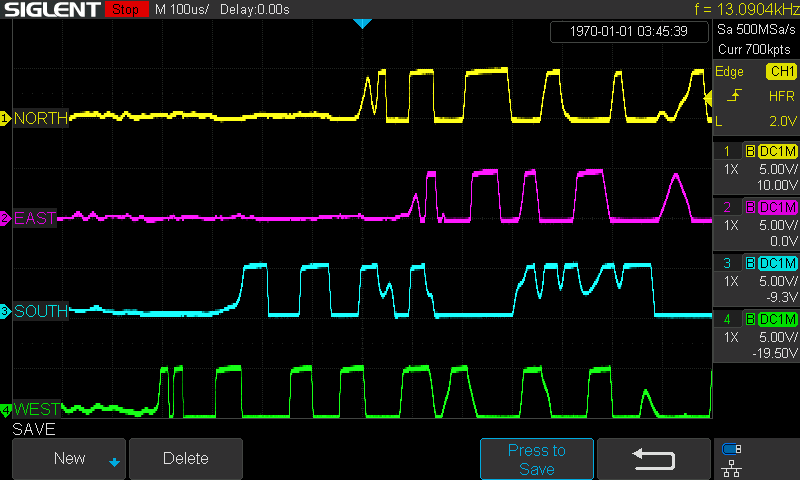
Documentation/Pictures/scope traces/SDS00010.bmp
