ten-point-nine/freETarget/Documentation/Pictures/scope traces/SDS00011.bmp

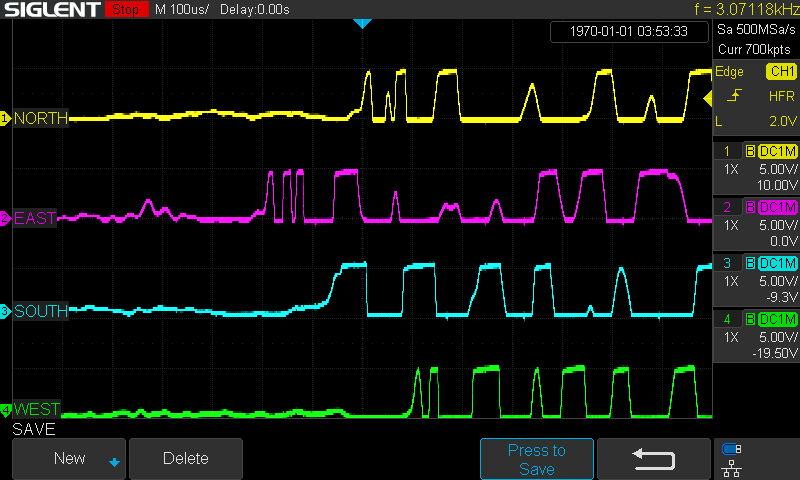
Documentation/Pictures/scope traces/SDS00011.bmp
