ten-point-nine/freETarget/Documentation/Pictures/scope traces/SDS00012.bmp

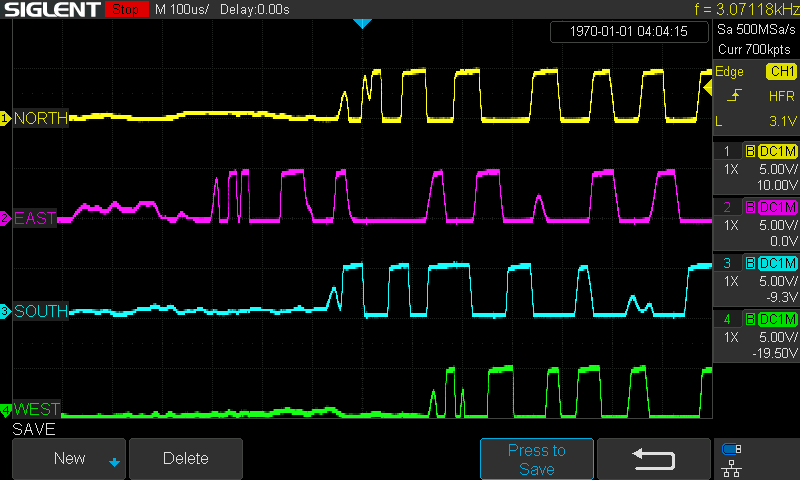
Documentation/Pictures/scope traces/SDS00012.bmp
