ten-point-nine/freETarget/Documentation/Pictures/scope traces/SDS00013.bmp

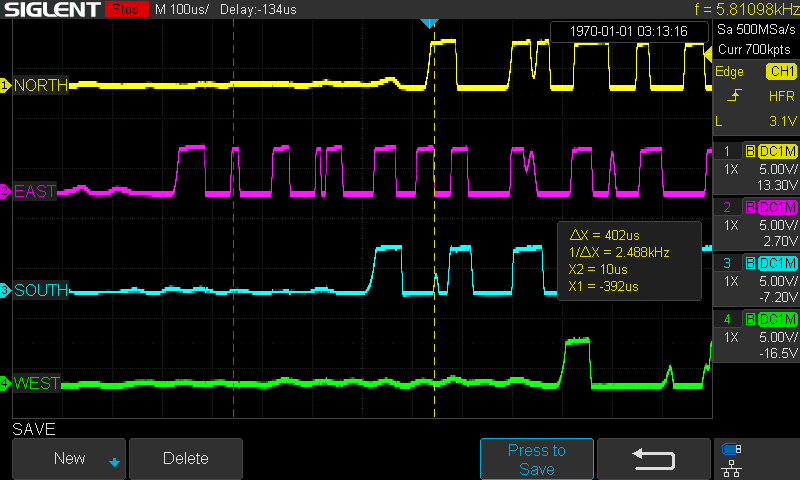
Documentation/Pictures/scope traces/SDS00013.bmp
