ten-point-nine/freETarget/Documentation/Pictures/scope traces/SDS00014.bmp

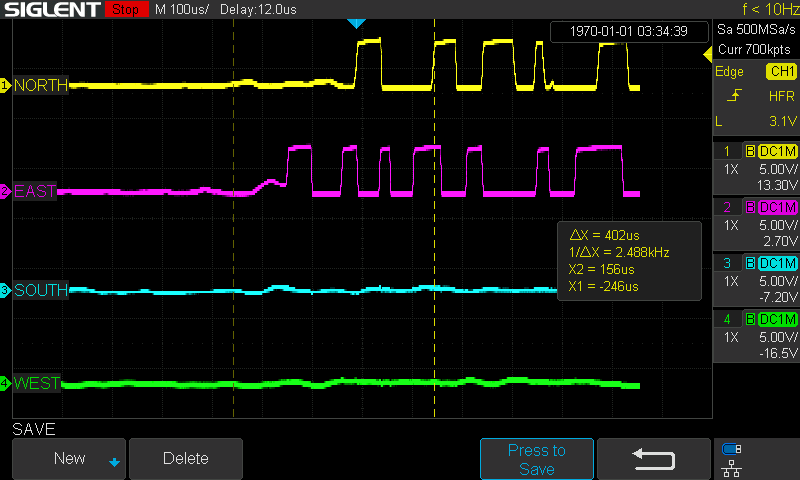
Documentation/Pictures/scope traces/SDS00014.bmp
