ten-point-nine/freETarget/Documentation/Pictures/scope traces/SDS00016.bmp

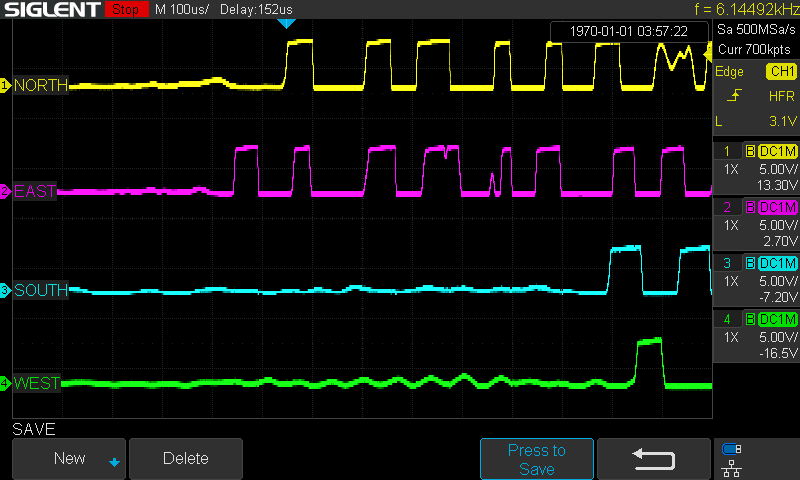
Documentation/Pictures/scope traces/SDS00016.bmp
