ten-point-nine/freETarget/Documentation/Pictures/scope traces/SDS00017.bmp

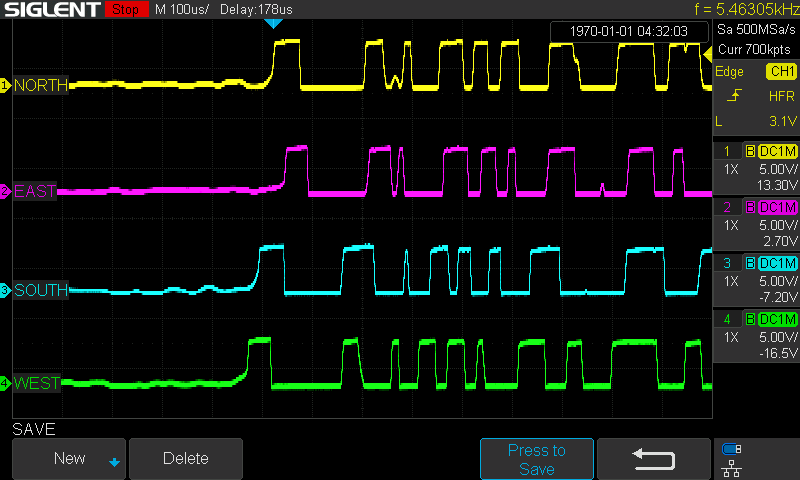
Documentation/Pictures/scope traces/SDS00017.bmp
