ten-point-nine/freETarget/Documentation/Pictures/scope traces/SDS00019.bmp

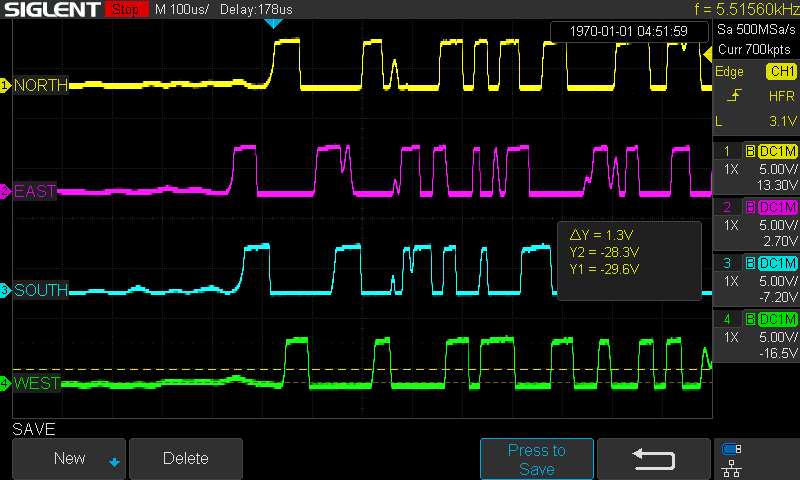
Documentation/Pictures/scope traces/SDS00019.bmp
