ten-point-nine/freETarget/Documentation/Pictures/scope traces/SDS00020.bmp

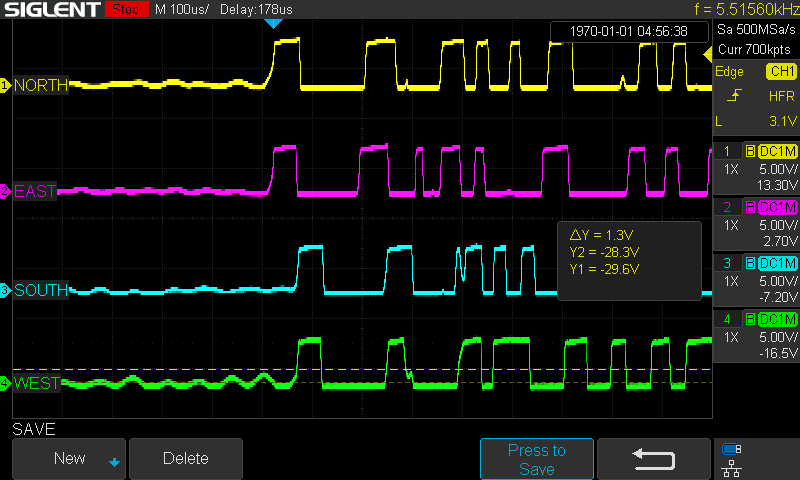
Documentation/Pictures/scope traces/SDS00020.bmp
