ten-point-nine/freETarget/Documentation/Pictures/scope traces/SDS00021.bmp

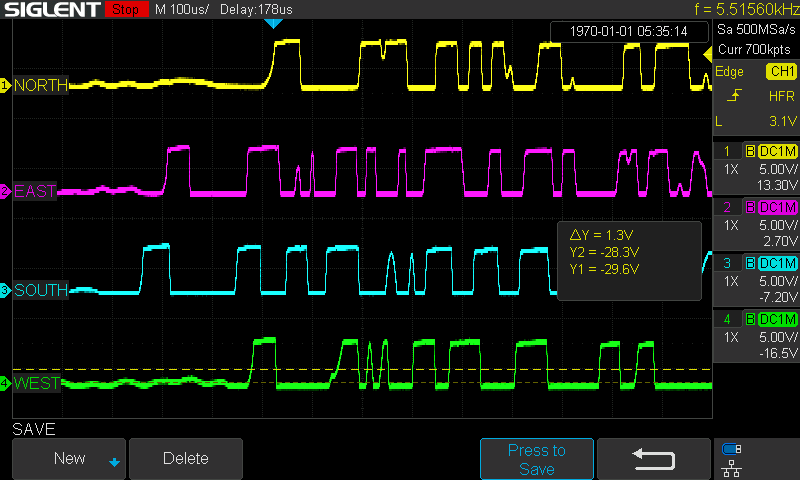
Documentation/Pictures/scope traces/SDS00021.bmp
