ten-point-nine/freETarget/Documentation/Pictures/scope traces/Shot_2.bmp

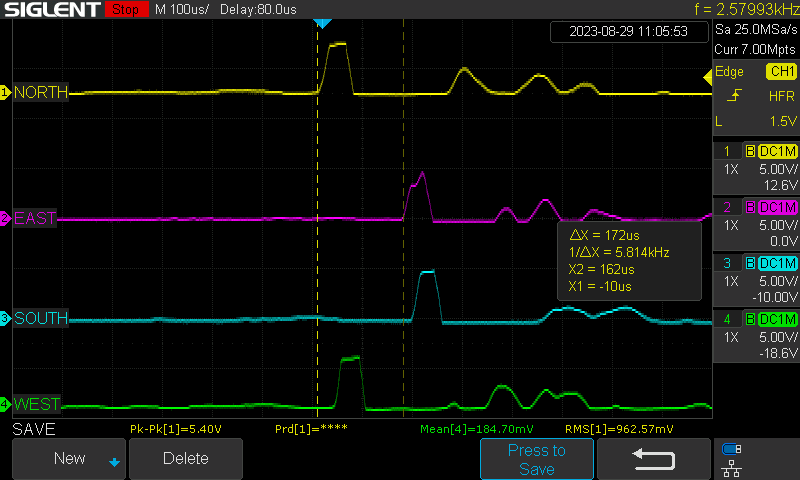
Documentation/Pictures/scope traces/Shot_2.bmp
