ten-point-nine/freETarget/Documentation/Pictures/Sensor Geometry.png

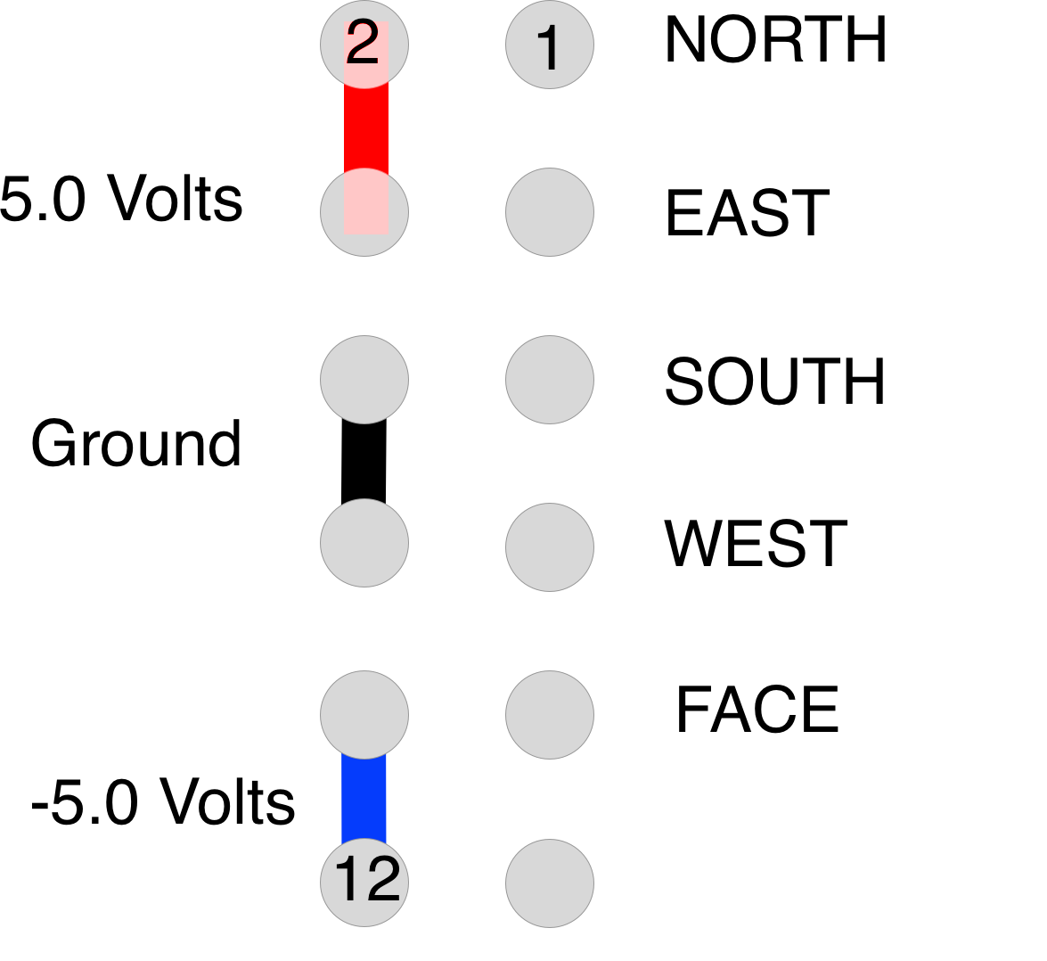
Documentation/Pictures/Sensor Geometry.png
