ten-point-nine/freETarget/Documentation/Pictures/Sensor Template.png

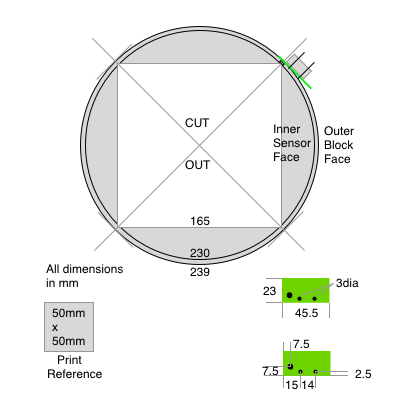
Documentation/Pictures/Sensor Template.png
