ten-point-nine/freETarget/Documentation/Pictures/Target Elements.png

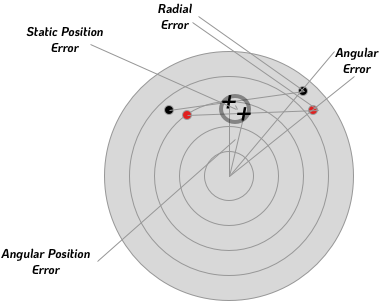
Documentation/Pictures/Target Elements.png
