ten-point-nine/freETarget/Documentation/Pictures/Target Holder.jpg

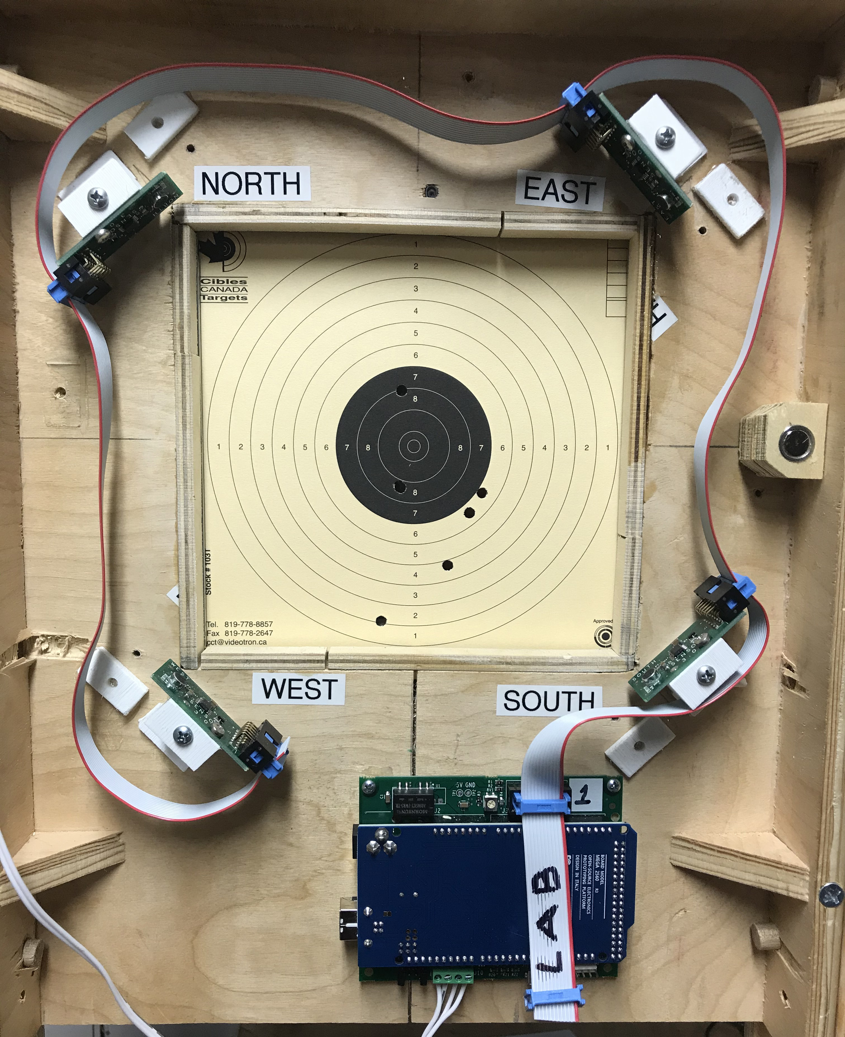
Documentation/Pictures/Target Holder.jpg
