ten-point-nine/freETarget/Documentation/Pictures/TokenRing.png

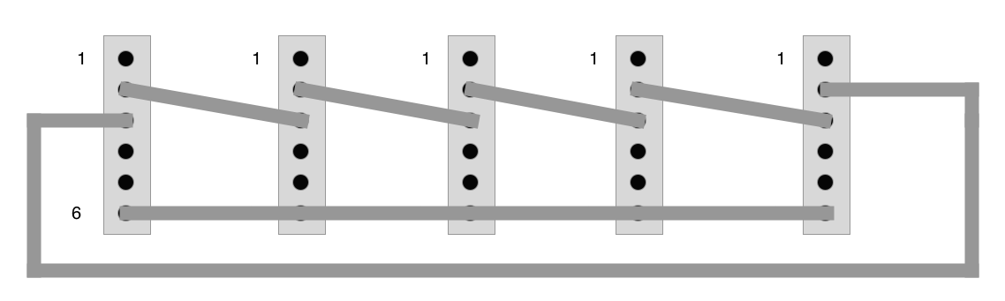
Documentation/Pictures/TokenRing.png
