ten-point-nine/freETarget/Documentation/Pictures/Triangles.png

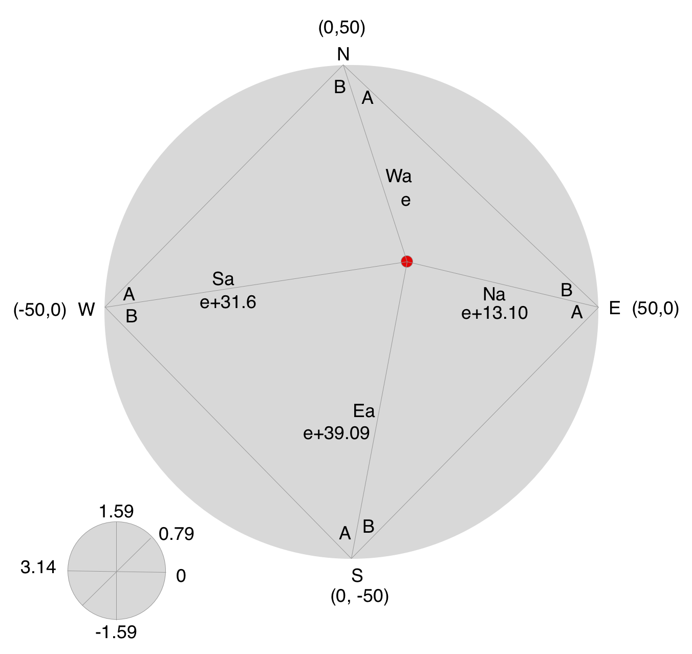
Documentation/Pictures/Triangles.png
