ten-point-nine/freETarget/Documentation/Pictures/UK1.JPG

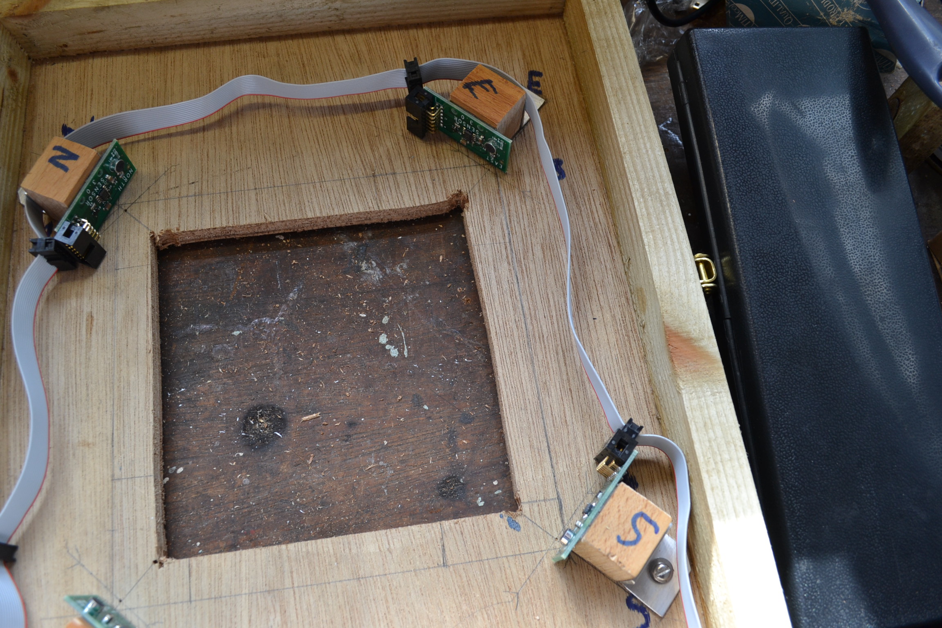
Documentation/Pictures/UK1.JPG
