ten-point-nine/freETarget/Documentation/Pictures/UK2.JPG

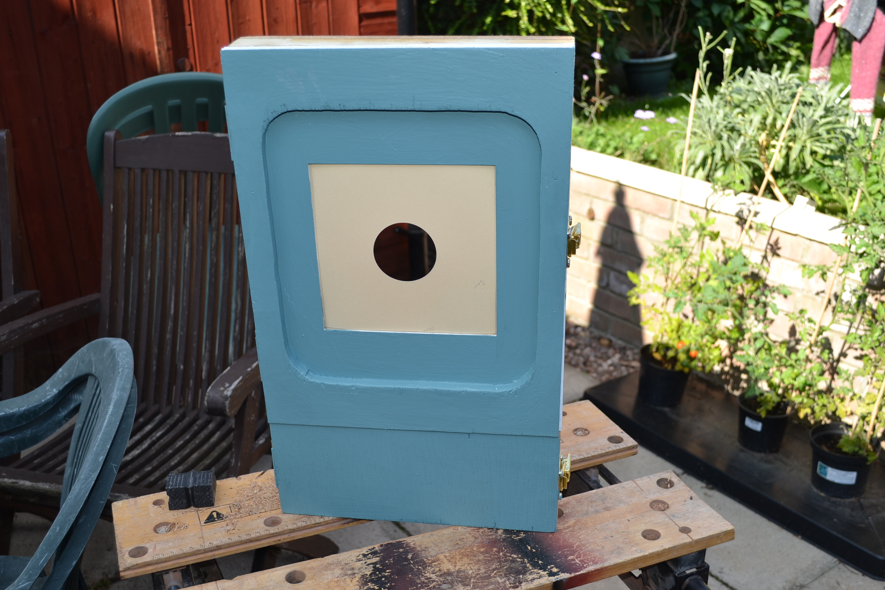
Documentation/Pictures/UK2.JPG
