ten-point-nine/freETarget/Documentation/Pictures/USB A to B.jpg

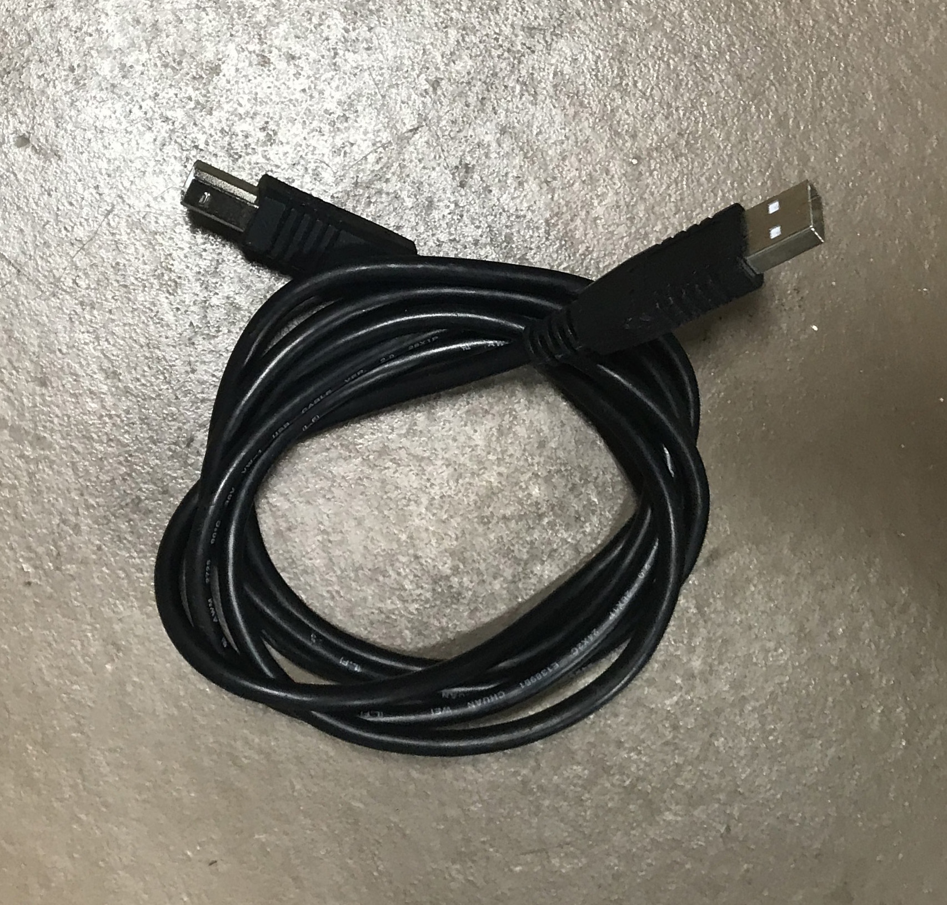
Documentation/Pictures/USB A to B.jpg
