ten-point-nine/freETarget/Mechanical/CAD Files/Club Target Holder.png

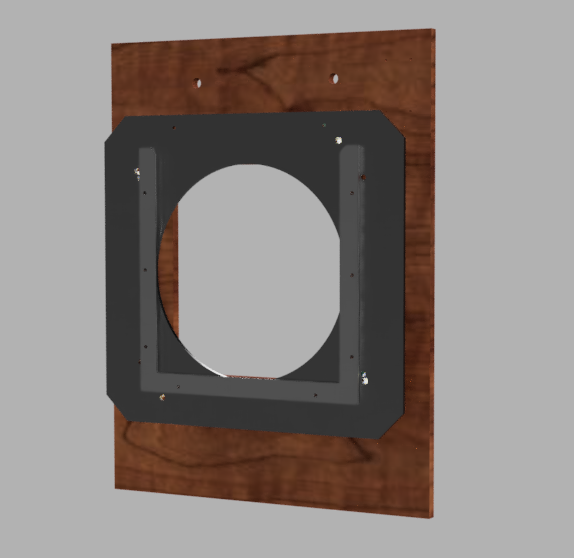
Mechanical/CAD Files/Club Target Holder.png
