ten-point-nine/freETarget/Mechanical/CAD Files/Club_Target_Holder.png

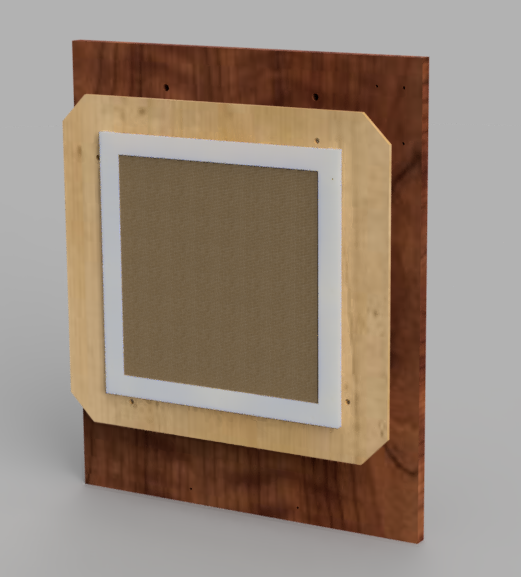
Mechanical/CAD Files/Club_Target_Holder.png
