ten-point-nine/freETarget/Software/C#/freETarget/cog-512.png

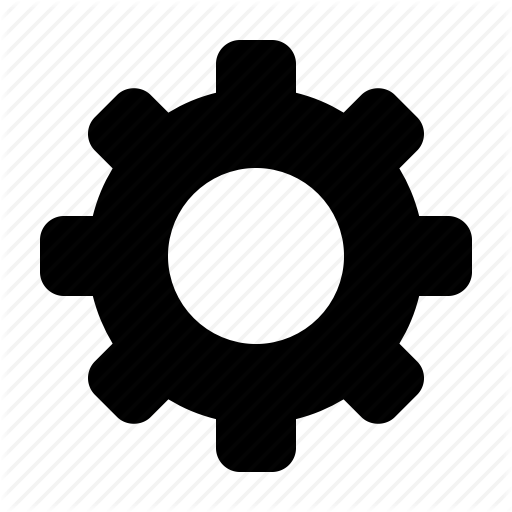
Software/C#/freETarget/cog-512.png
