ten-point-nine/freETarget/Software/C#/freETarget/divider.jpg

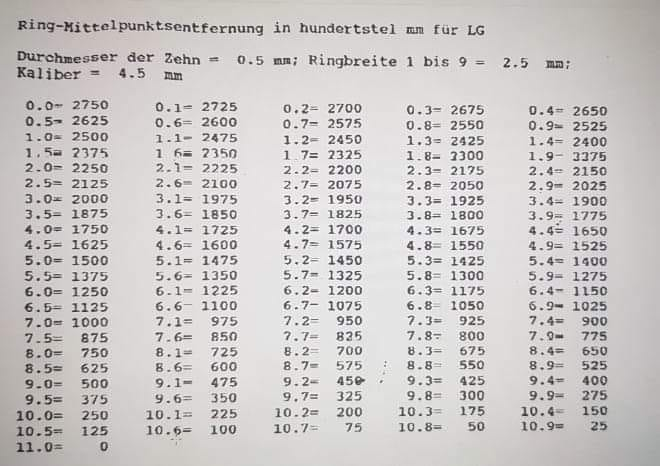
Software/C#/freETarget/divider.jpg
