ten-point-nine/freETarget/Software/C#/freETarget/page2.jpg

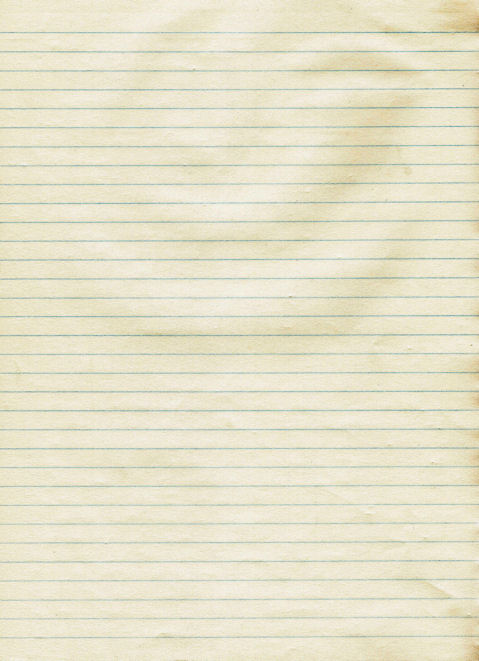
Software/C#/freETarget/page2.jpg
