ten-point-nine/freETarget/Software/C#/freETarget/page.jpg

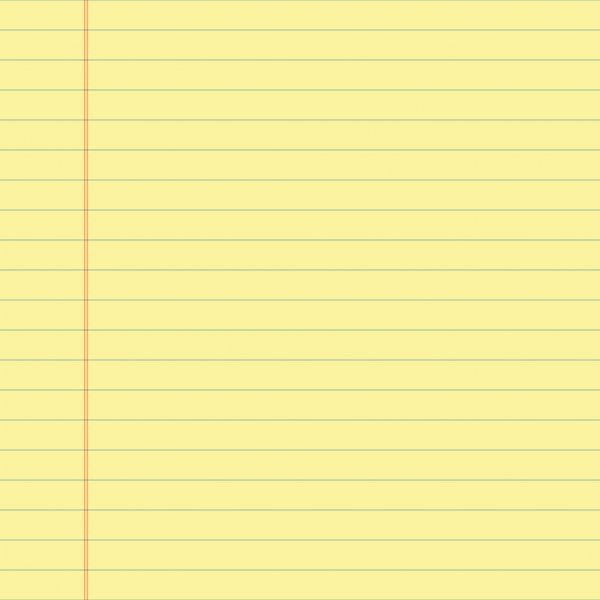
Software/C#/freETarget/page.jpg
