ten-point-nine/freETarget/Software/C#/freETarget/pistol_target.png

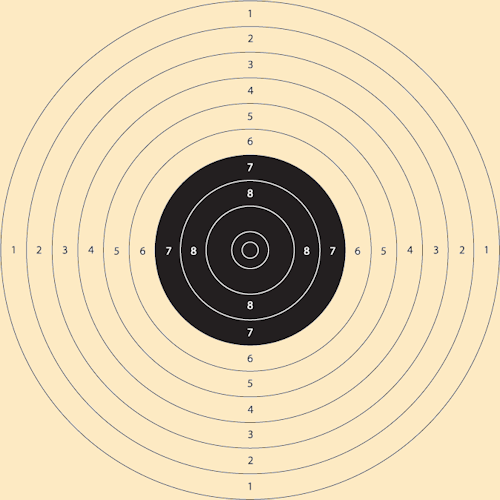
Software/C#/freETarget/pistol_target.png
