ten-point-nine/freETarget/Software/C#/freETarget/rifle_target.png

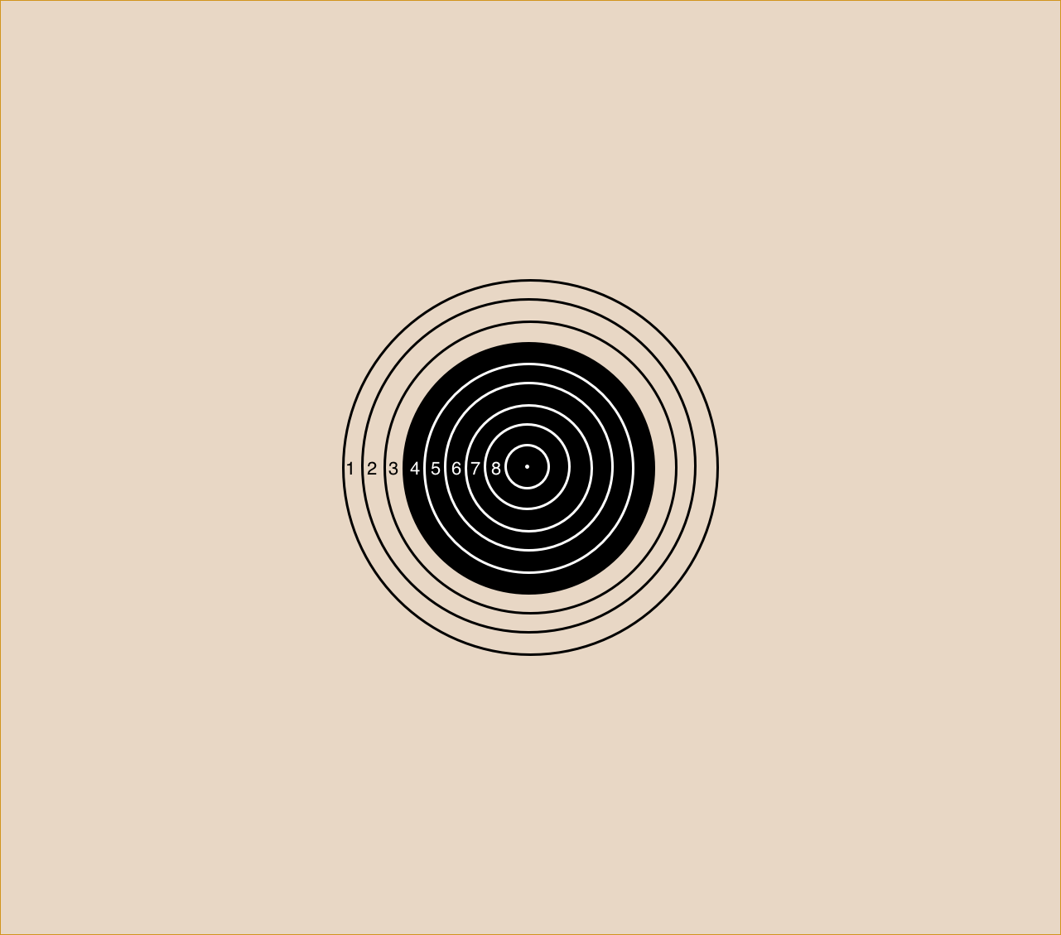
Software/C#/freETarget/rifle_target.png
