ten-point-nine/freETarget/Software/C#/freETarget/sensors2.png

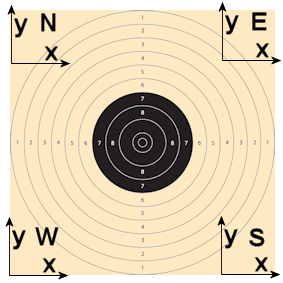
Software/C#/freETarget/sensors2.png
