ten-point-nine/freETarget/Software/C#/freETarget/sensors.png

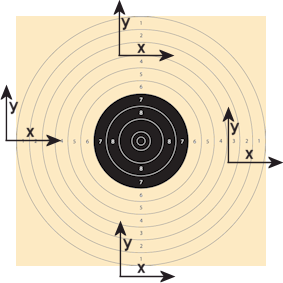
Software/C#/freETarget/sensors.png
