ten-point-nine/freETarget/Software/C#/freETarget/target.png

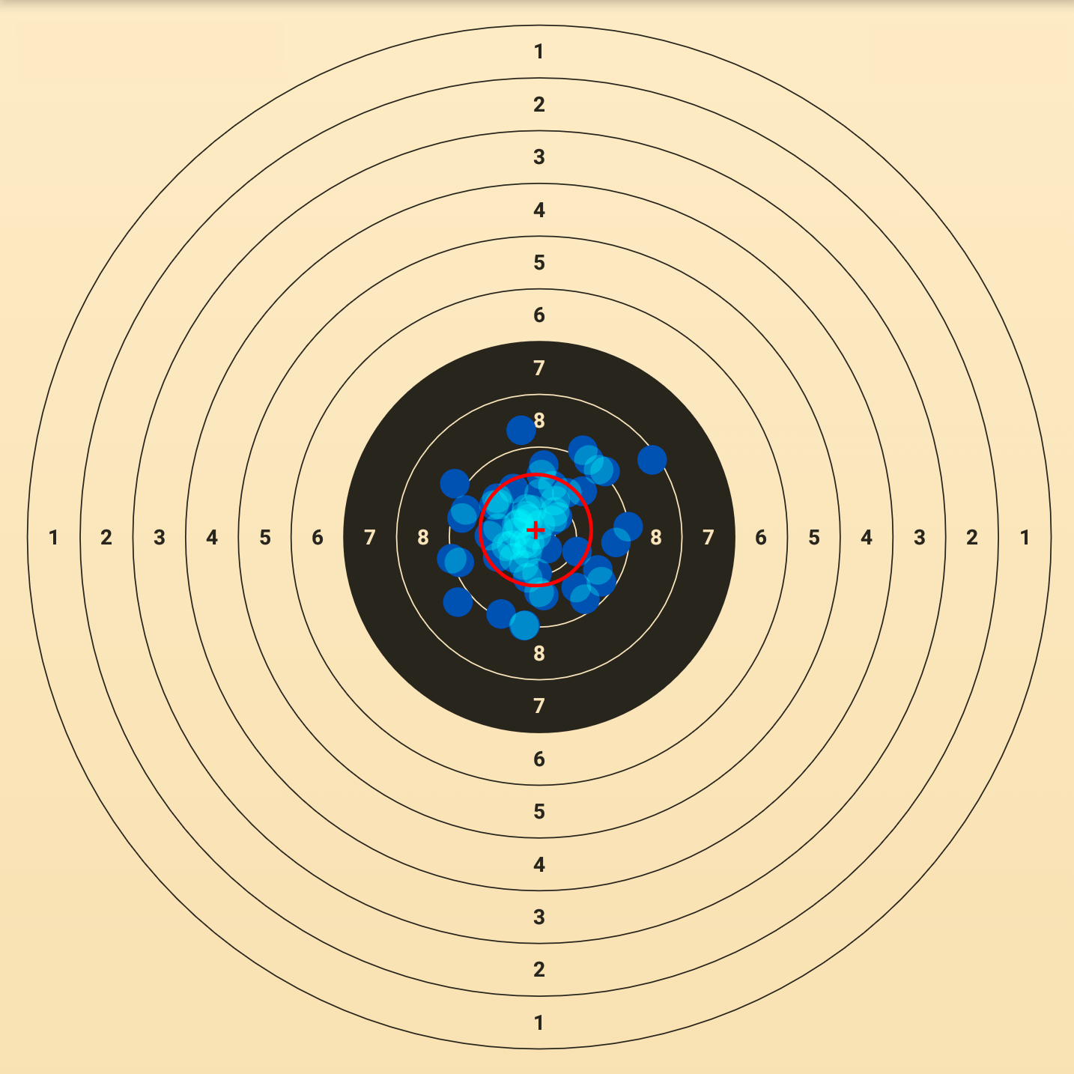
Software/C#/freETarget/target.png
