ten-point-nine/freETarget/Software/C#/freETarget/upload.png

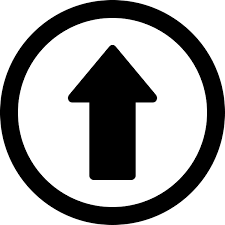
Software/C#/freETarget/upload.png
