ten-point-nine/freETarget/Documentation/Pictures/3D Parts Installed.png

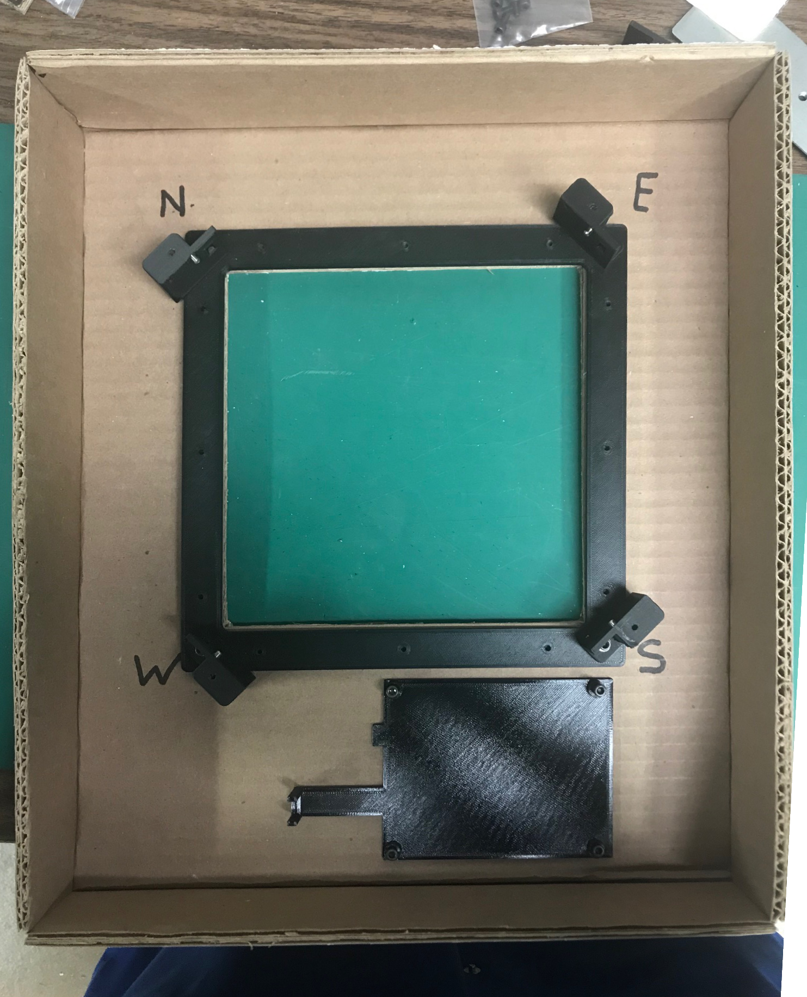
Documentation/Pictures/3D Parts Installed.png
