ten-point-nine/freETarget/Mechanical/Community Parts/Piece Parts/ArduinoBase.JPG

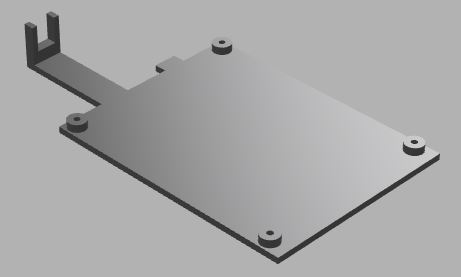
Mechanical/Community Parts/Piece Parts/ArduinoBase.JPG
