ten-point-nine/freETarget/Mechanical/Community Parts/Piece Parts/ArduinoCover.jpg

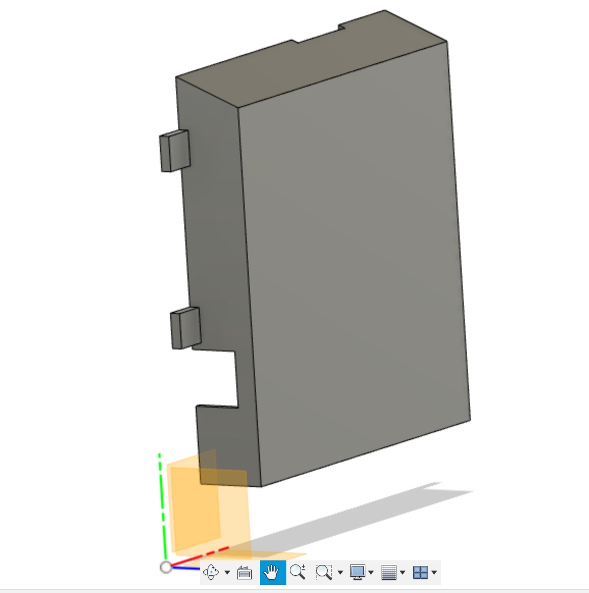
Mechanical/Community Parts/Piece Parts/ArduinoCover.jpg
