ten-point-nine/freETarget/Mechanical/Community Parts/Piece Parts/Cover and Face.png

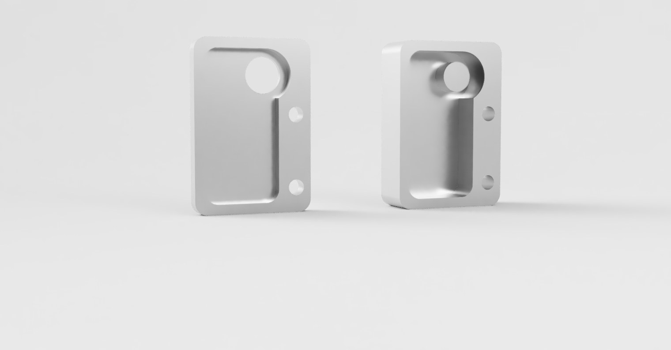
Mechanical/Community Parts/Piece Parts/Cover and Face.png
