ten-point-nine/freETarget/Mechanical/Community Parts/Piece Parts/ESP-01WiFIMount.JPG

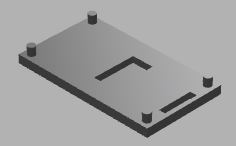
Mechanical/Community Parts/Piece Parts/ESP-01WiFIMount.JPG
