ten-point-nine/freETarget/Mechanical/Community Parts/Piece Parts/LightClip.JPG

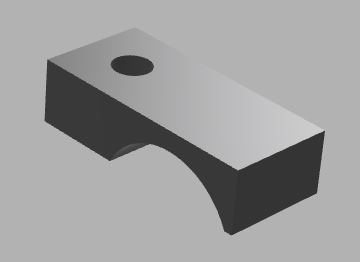
Mechanical/Community Parts/Piece Parts/LightClip.JPG
