ten-point-nine/freETarget/Mechanical/Community Parts/Sensor Mounts/ClipOn.png

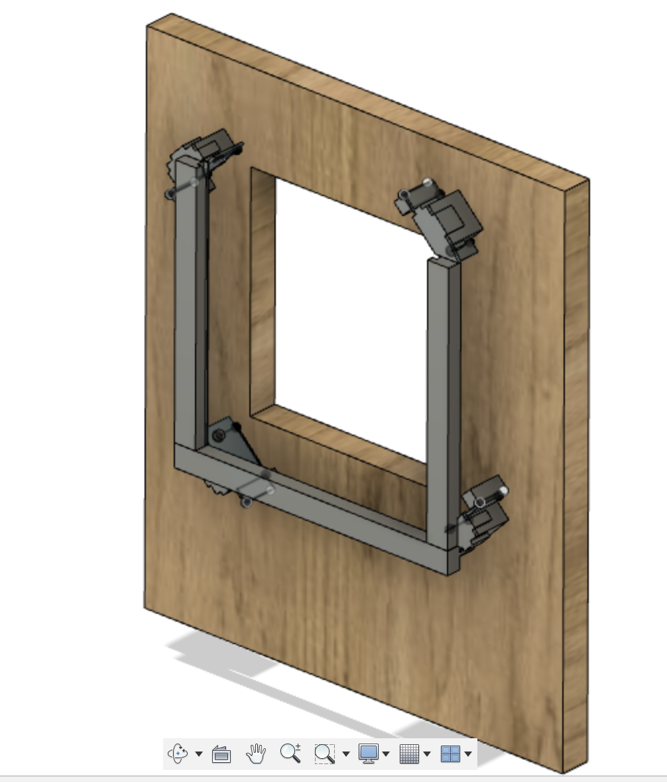
Mechanical/Community Parts/Sensor Mounts/ClipOn.png
