ten-point-nine/freETarget/Mechanical/Community Parts/Sensor Mounts/sensor holder.jpeg

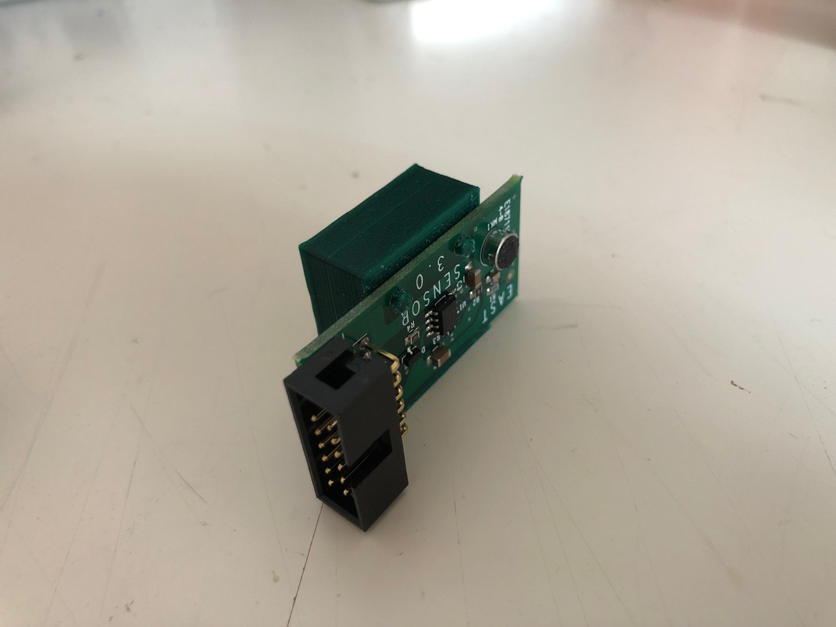
Mechanical/Community Parts/Sensor Mounts/sensor holder.jpeg
