ten-point-nine/freETarget/Mechanical/Community Parts/Sensor Mounts/SensorBase.JPG

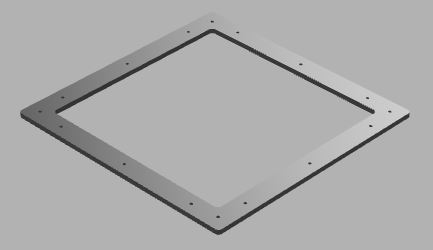
Mechanical/Community Parts/Sensor Mounts/SensorBase.JPG
