ten-point-nine/freETarget/Mechanical/Community Parts/Sensor Mounts/SensorMount.JPG

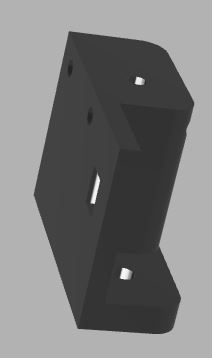
Mechanical/Community Parts/Sensor Mounts/SensorMount.JPG
