ten-point-nine/freETarget/Mechanical/Community Parts/Target Holders/Air Rifle Target Plate.jpg

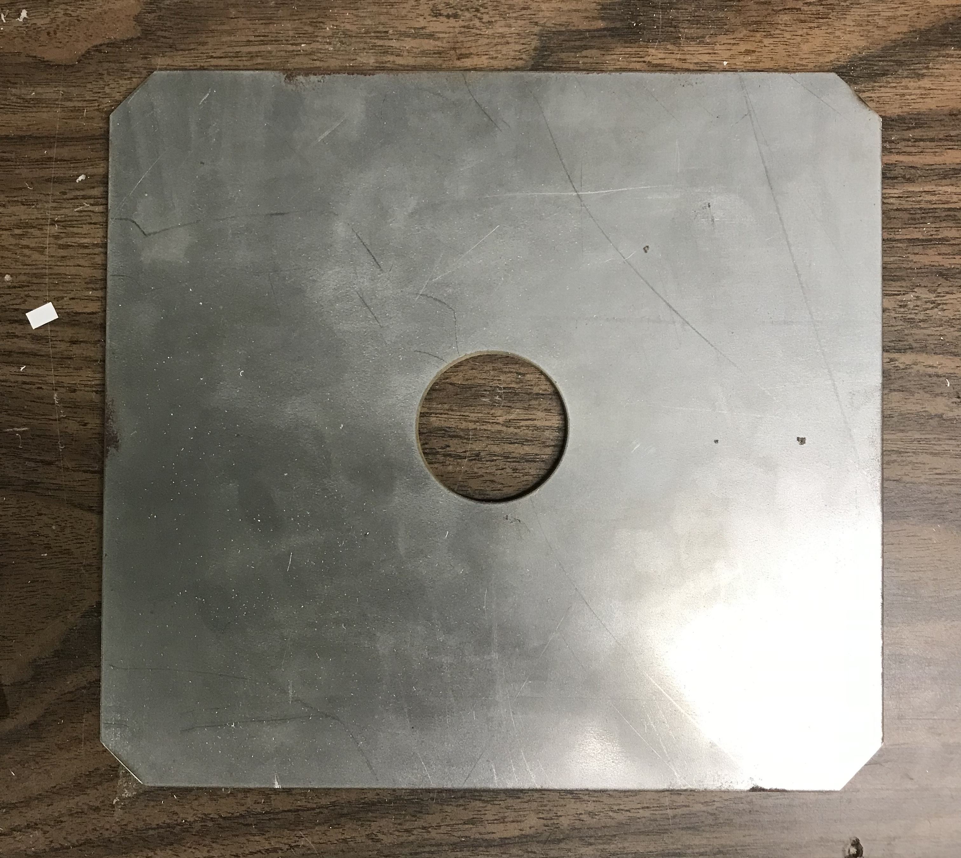
Mechanical/Community Parts/Target Holders/Air Rifle Target Plate.jpg
