ten-point-nine/freETarget/Mechanical/Community Parts/Target Holders/target holder bottom left and right.jpeg

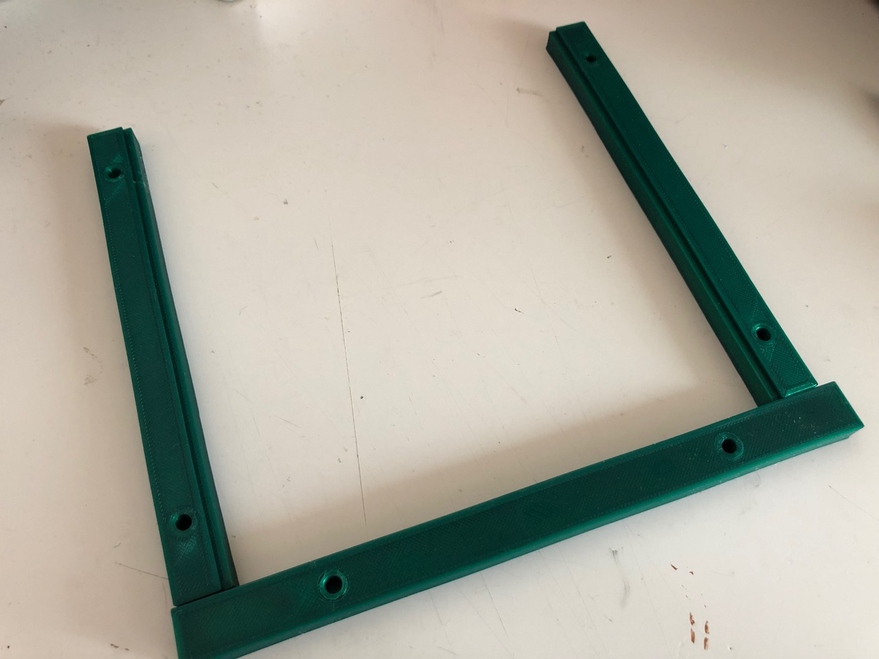
Mechanical/Community Parts/Target Holders/target holder bottom left and right.jpeg
