ten-point-nine/freETarget/Mechanical/CNC/50m Pistol/corner.stl

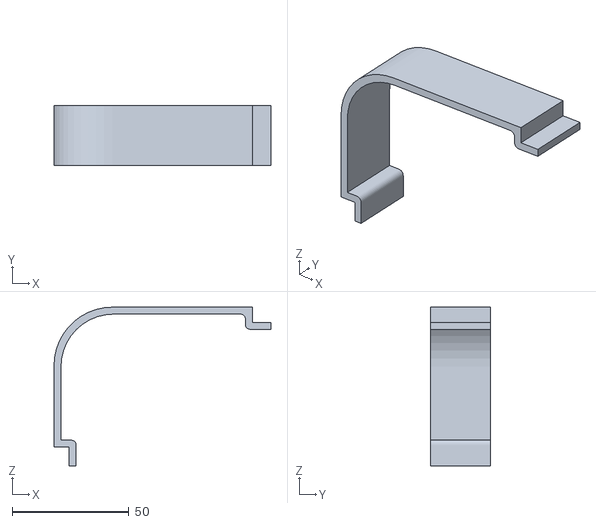
[picture p146: CAD file, 2026-05-19]
Mechanical/CNC/50m Pistol/corner.stl
93.0 x 25.5 x 68.0
