ten-point-nine/freETarget/Mechanical/CNC/6mm Panel/6mm Panel Back.dxf

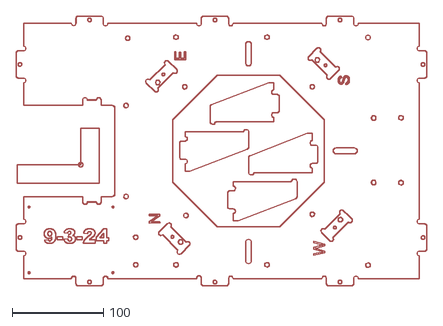
[picture p147: CAD file, 2024-10-11]
Mechanical/CNC/6mm Panel/6mm Panel Back.dxf
450.6 x 296.0
