ten-point-nine/freETarget/Mechanical/CNC/Metal - Plastic/Pellet Holder 2.stl

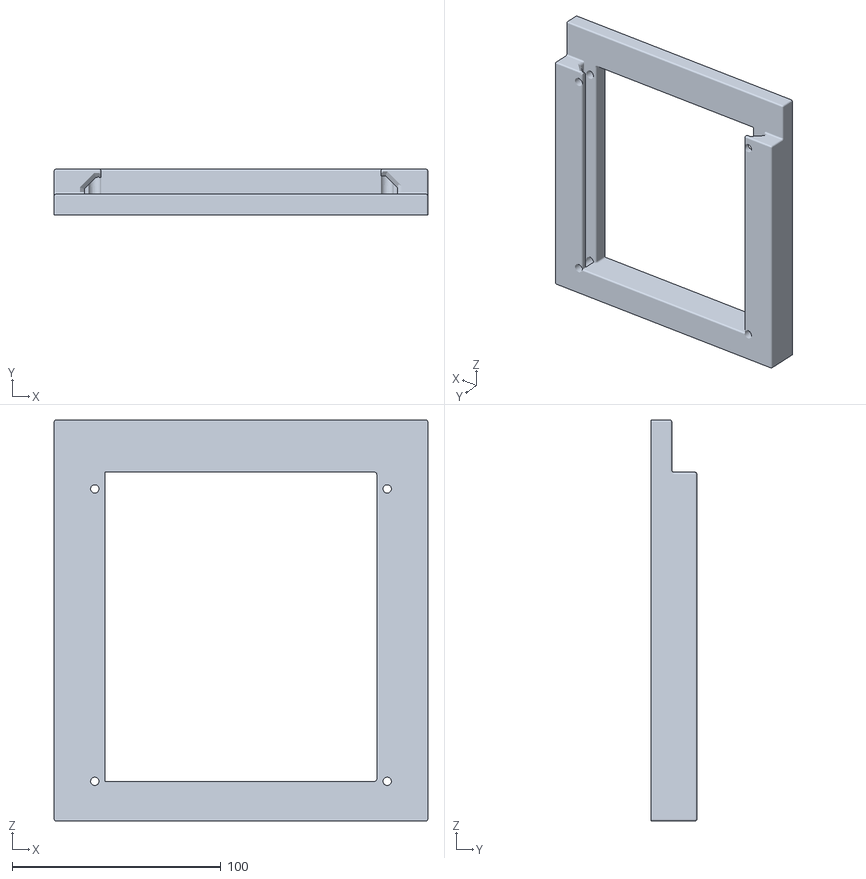
[picture p148: CAD file, 2026-08-26]
Mechanical/CNC/Metal - Plastic/Pellet Holder 2.stl
179.0 x 22.0 x 192.0
