ten-point-nine/freETarget/Mechanical/CNC/Traffic Lights/Traffic Lights.3mf

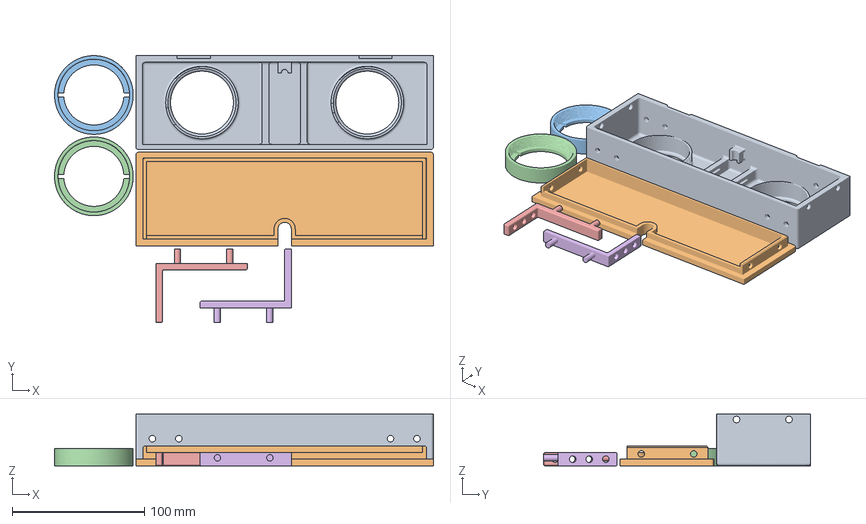
[picture p149: CAD file, 2026-05-19]
Mechanical/CNC/Traffic Lights/Traffic Lights.3mf
286.5 x 201.7 x 39.0 mm
Traffic Lights.stl_1
Back Cover.stl
Traffic Lights.stl_3 x 2
Mounts.stl_2 x 2
