ten-point-nine/freETarget/Mechanical/CNC/Witness Paper Transport/Paper Transport 90mm.dxf

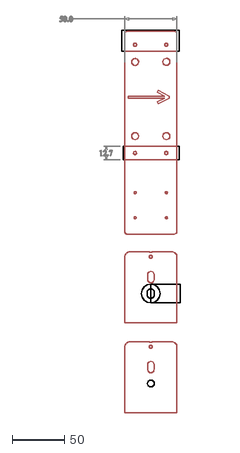
[picture p150: CAD file, 2023-03-27]
Mechanical/CNC/Witness Paper Transport/Paper Transport 90mm.dxf
115.8 x 379.5
