ten-point-nine/freETarget/Mechanical/Community Parts/Piece Parts/LightClip.stl

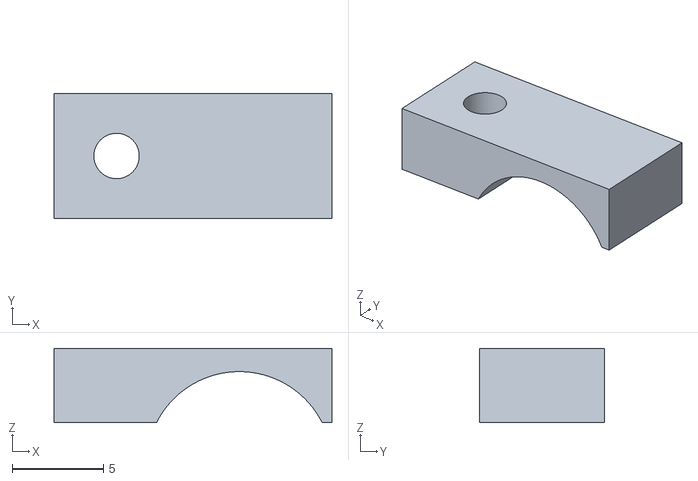
[picture p151: CAD file, 2021-08-28]
Mechanical/Community Parts/Piece Parts/LightClip.stl
15.2 x 6.86 x 4.06
