ten-point-nine/freETarget/Mechanical/Community Parts/Sensor Mounts/Sensor Cover.stl

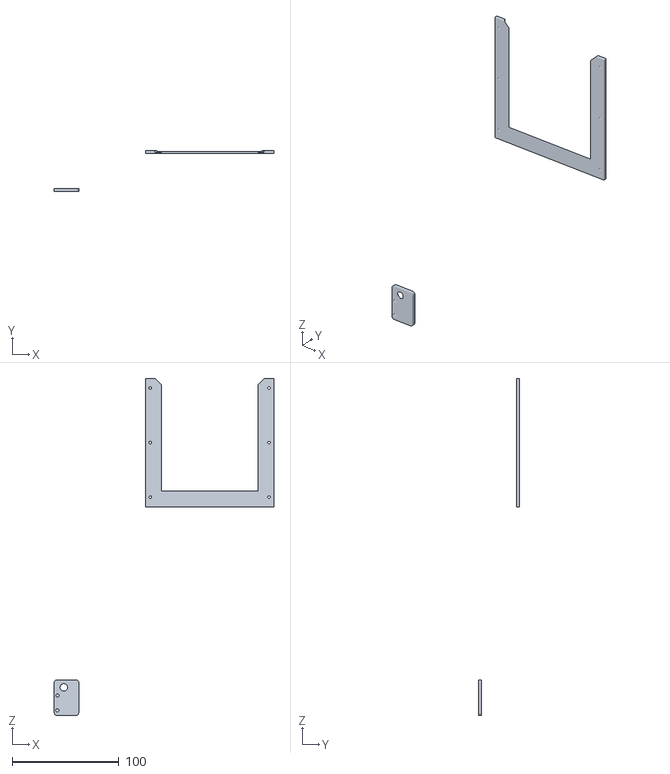
[picture p152: CAD file, 2022-10-30]
Mechanical/Community Parts/Sensor Mounts/Sensor Cover.stl
205.3 x 38.5 x 315.1
