ten-point-nine/freETarget/Mechanical/Community Parts/Target Holders/Pistol Target Holder.stl

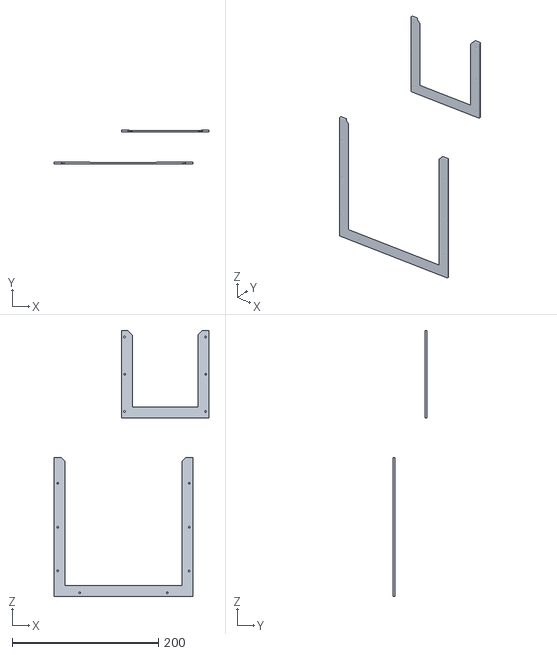
[picture p153: CAD file, 2022-10-30]
Mechanical/Community Parts/Target Holders/Pistol Target Holder.stl
212.1 x 46.6 x 364.2
