ten-point-nine/freETarget/Mechanical/Community Parts/Traffic Lights Cable Clamp.stl

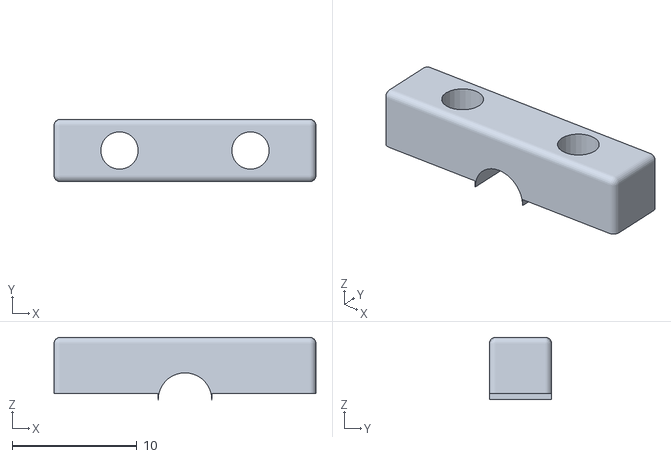
[picture p154: CAD file, 2025-02-21]
Mechanical/Community Parts/Traffic Lights Cable Clamp.stl
21.0 x 5.00 x 5.00
