ten-point-nine/freETarget/Mechanical/CNC/50m Pistol/50m Corners.stl.cxprj.3mf

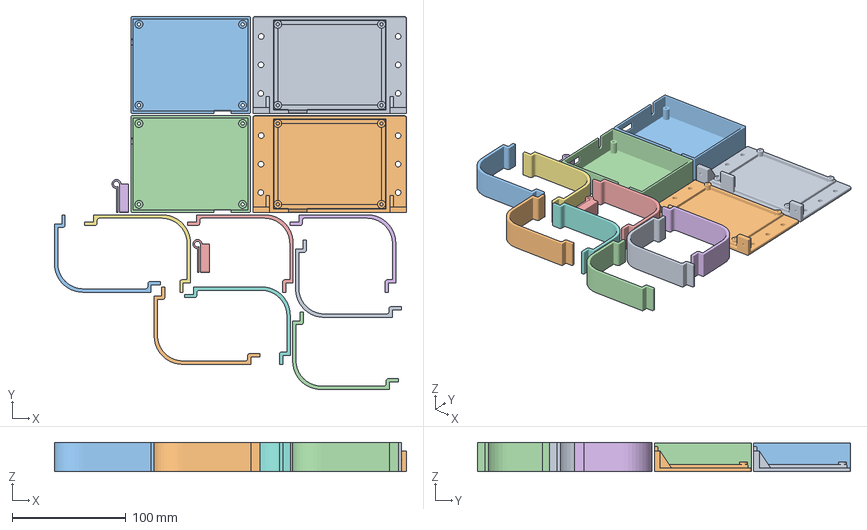
[picture p155: CAD file, 2026-05-19]
Mechanical/CNC/50m Pistol/50m Corners.stl.cxprj.3mf
309.1 x 327.3 x 25.5 mm
50m Pistol.stl_1 x 2
50m Pistol.stl_2 x 2
corner.stl x 8
Cable Clamp.stl x 2
