ten-point-nine/freETarget/Mechanical/CNC/Metal - Plastic/Cable Clamp.stl

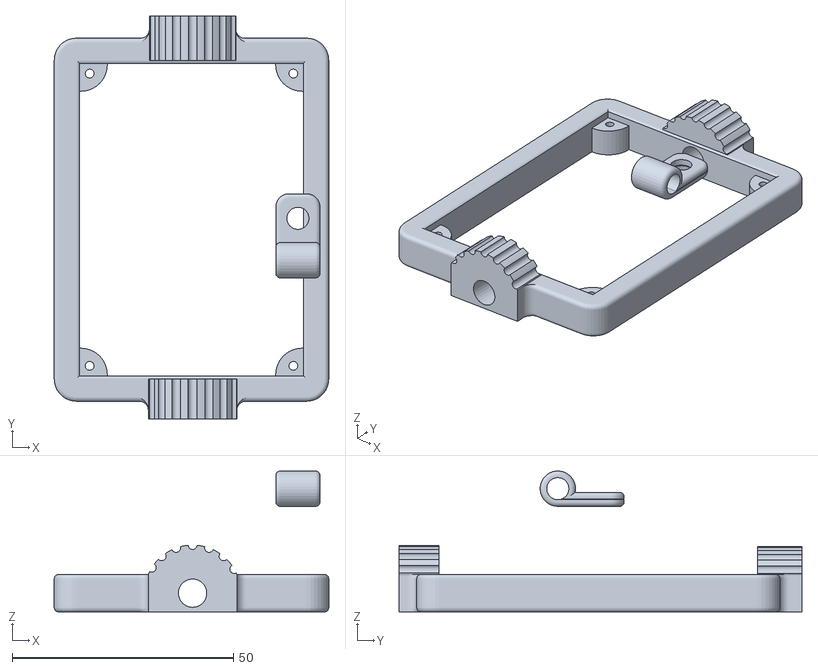
[picture p156: CAD file, 2026-05-19]
Mechanical/CNC/Metal - Plastic/Cable Clamp.stl
62.0 x 91.0 x 31.8
