ten-point-nine/freETarget/Mechanical/CNC/Traffic Lights/Traffic Lights_1.stl

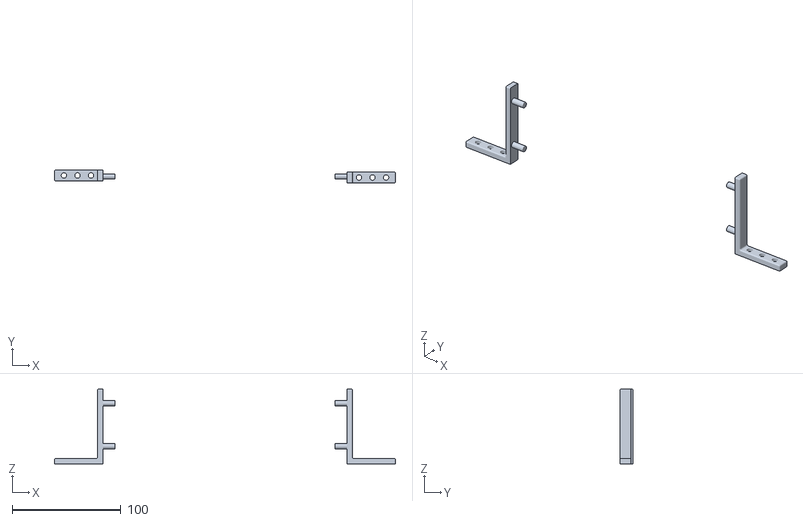
[picture p157: CAD file, 2026-05-19]
Mechanical/CNC/Traffic Lights/Traffic Lights_1.stl
314.3 x 12.0 x 69.0
