ten-point-nine/freETarget/Mechanical/Community Parts/Piece Parts/ArduinoBase.stl

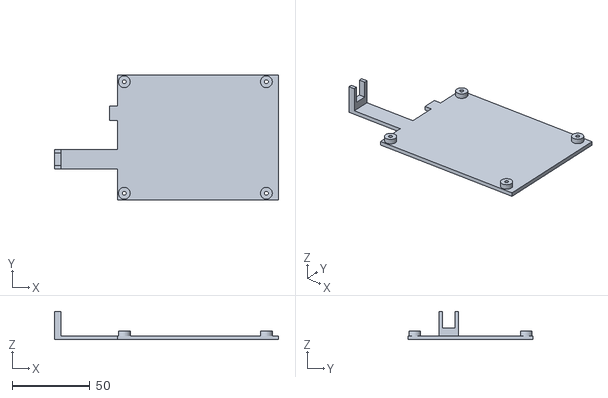
[picture p158: CAD file, 2021-08-28]
Mechanical/Community Parts/Piece Parts/ArduinoBase.stl
143.8 x 80.5 x 18.3
