ten-point-nine/freETarget/Mechanical/Community Parts/Sensor Mounts/sensorFramework.stl

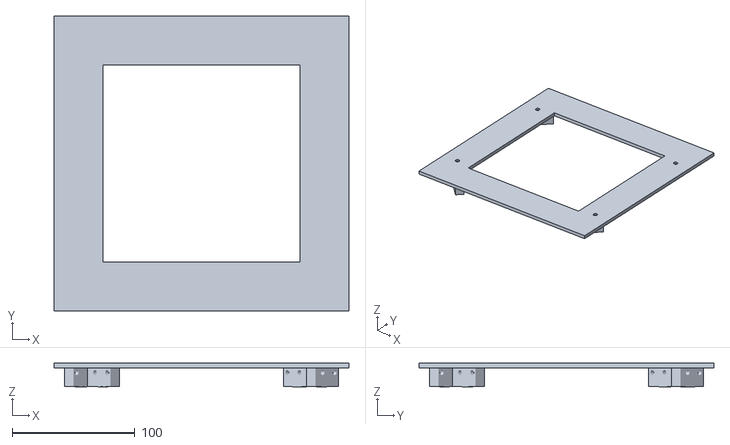
[picture p159: CAD file, 2022-10-30]
Mechanical/Community Parts/Sensor Mounts/sensorFramework.stl
240.0 x 240.0 x 19.5
