ten-point-nine/freETarget/Mechanical/Community Parts/Traffic Lights Cover.stl

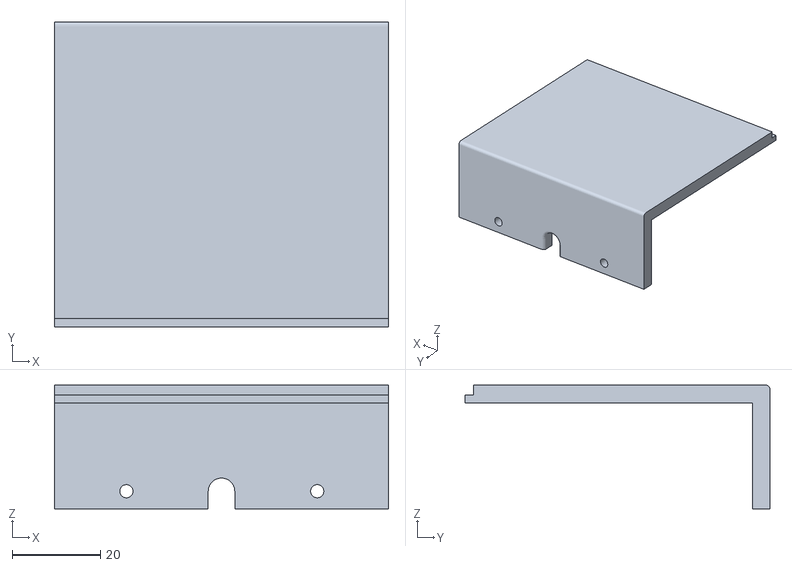
[picture p160: CAD file, 2025-02-21]
Mechanical/Community Parts/Traffic Lights Cover.stl
75.5 x 69.0 x 28.0
