ten-point-nine/freETarget/Mechanical/CNC/50m Pistol/Cable Clamp.stl

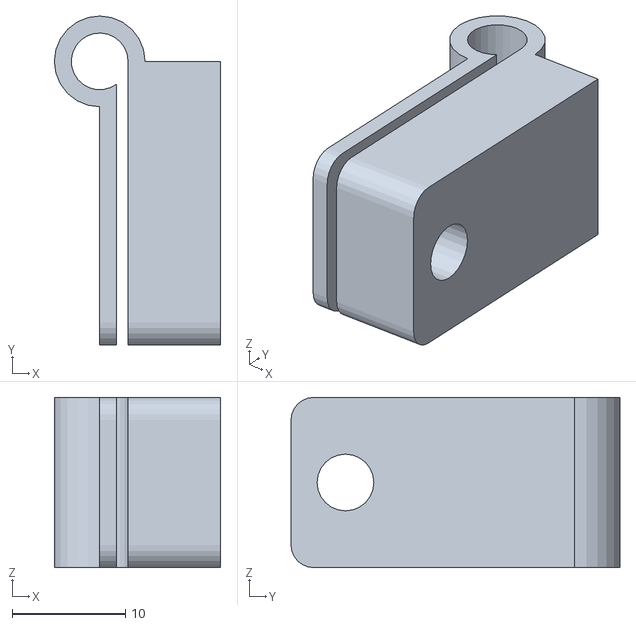
[picture p161: CAD file, 2026-05-19]
Mechanical/CNC/50m Pistol/Cable Clamp.stl
14.7 x 29.0 x 15.0
