ten-point-nine/freETarget/Mechanical/CNC/Metal - Plastic/clamp.stl

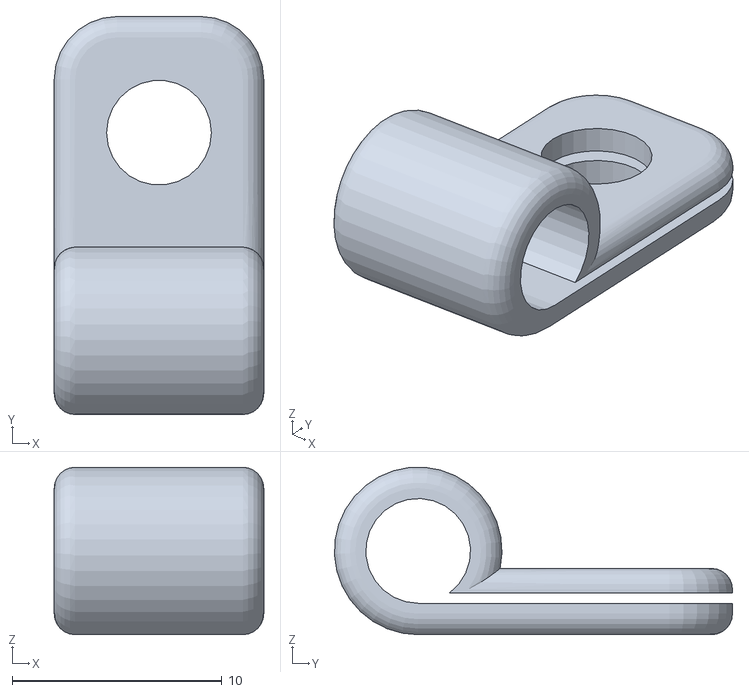
[picture p162: CAD file, 2026-05-19]
Mechanical/CNC/Metal - Plastic/clamp.stl
10.0 x 19.0 x 7.99
