ten-point-nine/freETarget/Mechanical/CNC/Traffic Lights/Mounts.stl

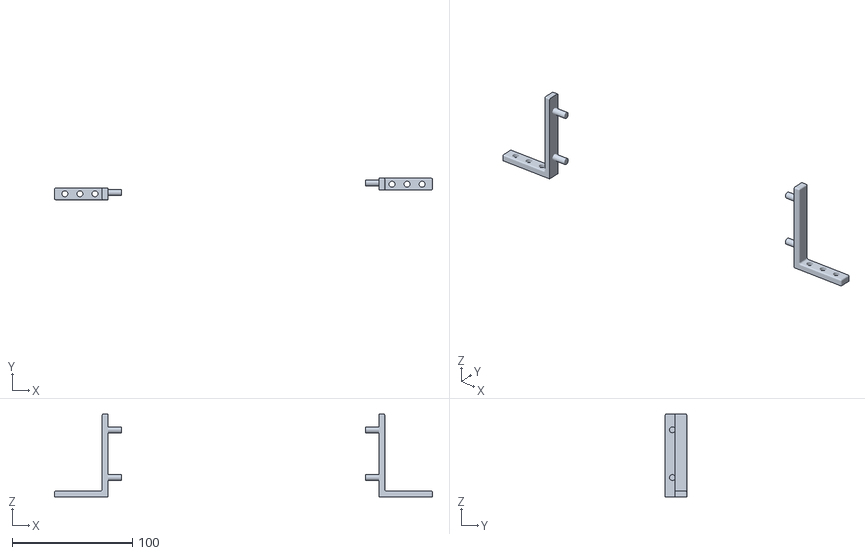
[picture p163: CAD file, 2026-05-19]
Mechanical/CNC/Traffic Lights/Mounts.stl
314.3 x 18.0 x 69.0
