ten-point-nine/freETarget/Mechanical/Community Parts/Piece Parts/ESP-01WiFIMount.stl

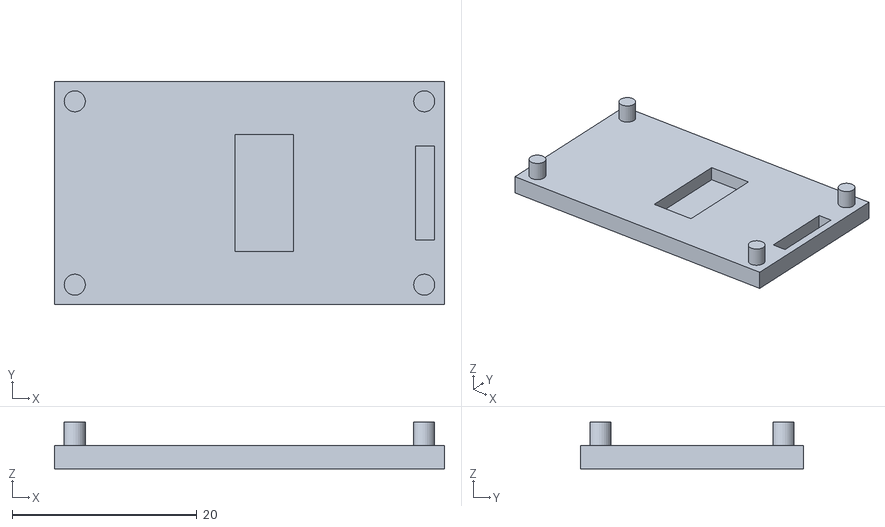
[picture p164: CAD file, 2021-08-28]
Mechanical/Community Parts/Piece Parts/ESP-01WiFIMount.stl
42.2 x 24.2 x 5.08
