ten-point-nine/freETarget/Mechanical/Community Parts/Sensor Mounts/Face Sensor Mount.stl

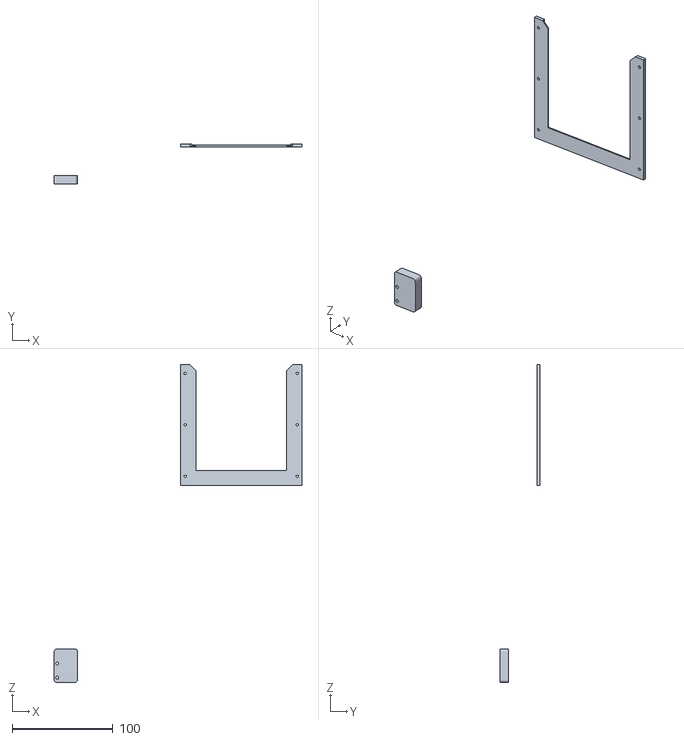
[picture p165: CAD file, 2022-10-30]
Mechanical/Community Parts/Sensor Mounts/Face Sensor Mount.stl
245.3 x 39.5 x 315.1
