ten-point-nine/freETarget/Mechanical/Community Parts/Target Holders/Rifle Target Holder v17.stl

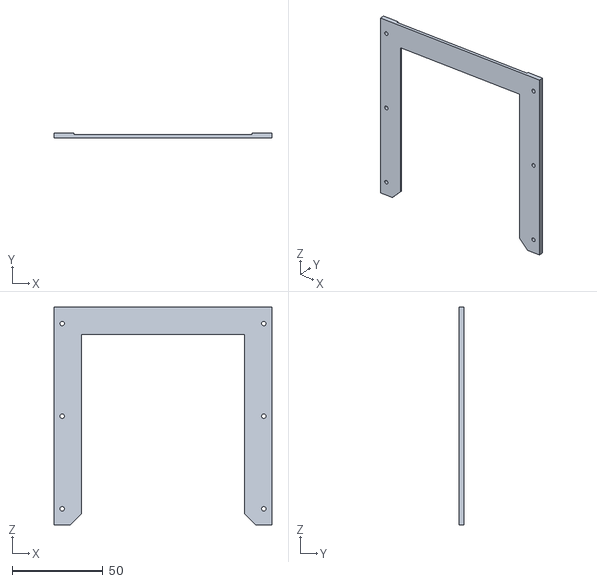
[picture p166: CAD file, 2022-03-11]
Mechanical/Community Parts/Target Holders/Rifle Target Holder v17.stl
120.0 x 3.00 x 120.0
