ten-point-nine/freETarget/Mechanical/Community Parts/Traffic Lights Base.stl

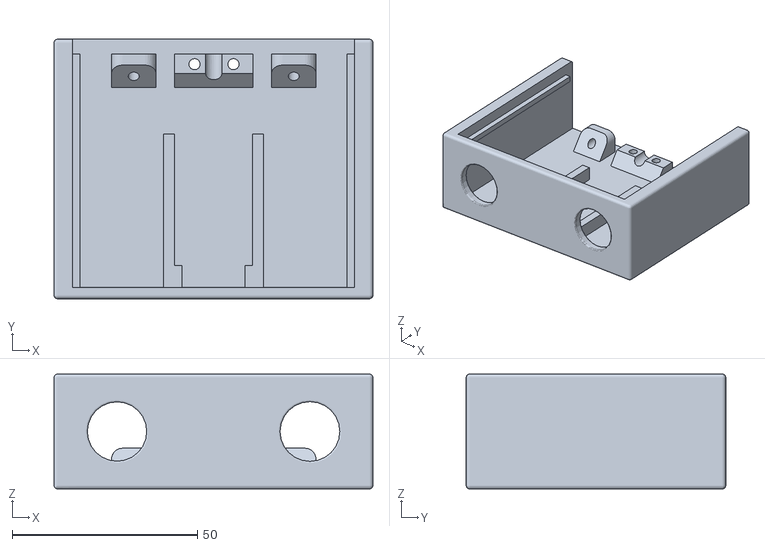
[picture p167: CAD file, 2025-02-21]
Mechanical/Community Parts/Traffic Lights Base.stl
86.0 x 70.0 x 31.0
