ten-point-nine/freETarget/Mechanical/CNC/Metal - Plastic/Face Sensor Spacer.stl

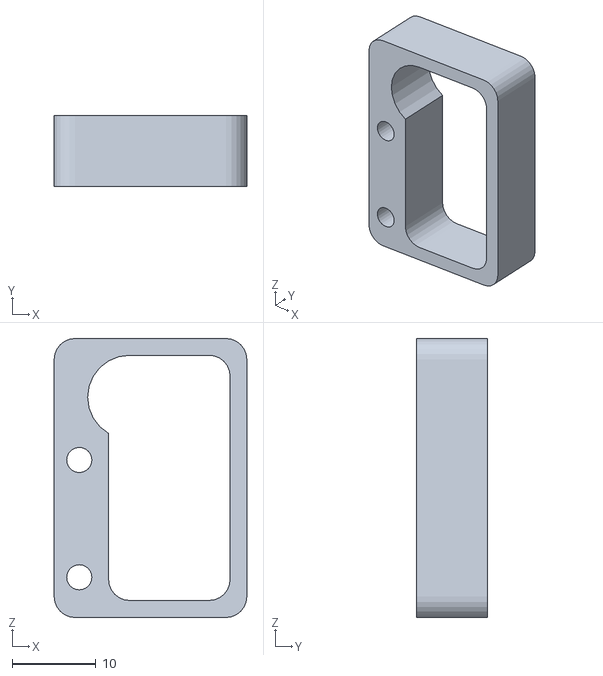
[picture p168: CAD file, 2026-05-12]
Mechanical/CNC/Metal - Plastic/Face Sensor Spacer.stl
23.0 x 8.50 x 33.3
