ten-point-nine/freETarget/Mechanical/CNC/Traffic Lights/Back Cover.stl

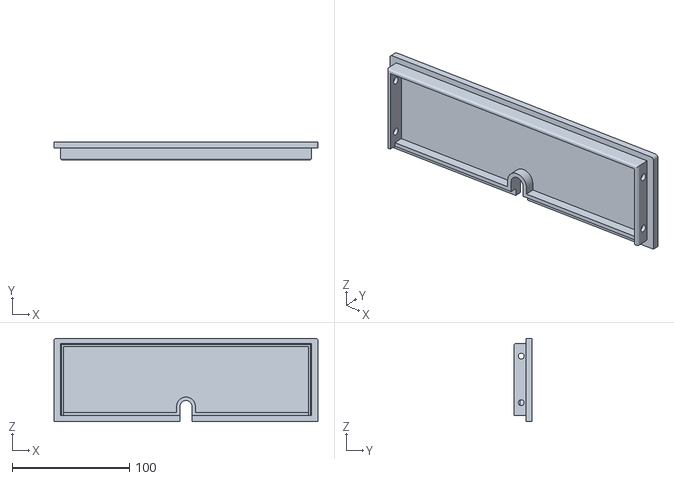
[picture p169: CAD file, 2026-05-12]
Mechanical/CNC/Traffic Lights/Back Cover.stl
225.0 x 15.0 x 71.0
