ten-point-nine/freETarget/Mechanical/Community Parts/Piece Parts/target holder left.stl

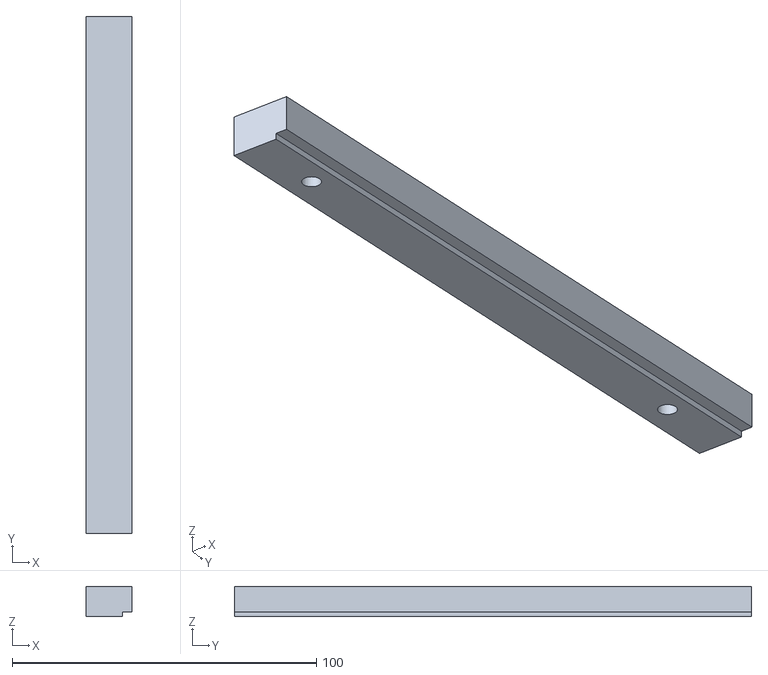
[picture p170: CAD file, 2021-08-04]
Mechanical/Community Parts/Piece Parts/target holder left.stl
15.0 x 170.0 x 10.0
