ten-point-nine/freETarget/Mechanical/Community Parts/Sensor Mounts/ClipOn Target holder right.stl

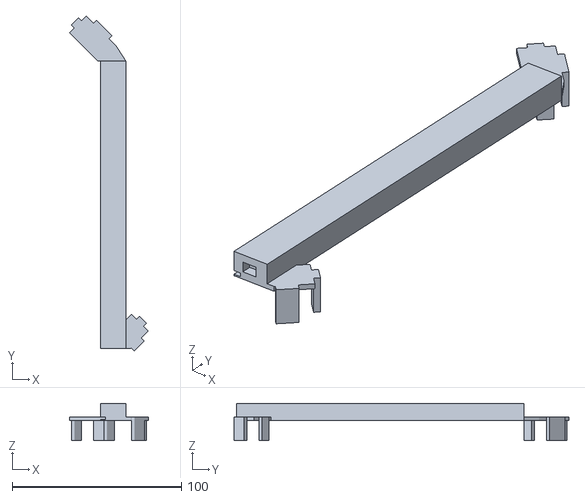
[picture p171: CAD file, 2021-10-19]
Mechanical/Community Parts/Sensor Mounts/ClipOn Target holder right.stl
46.7 x 197.9 x 22.0
