ten-point-nine/freETarget/Mechanical/Community Parts/Target Holders/Target Plate Alignment.DXF

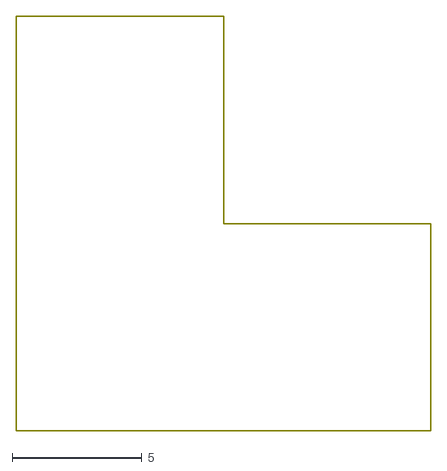
[picture p172: CAD file, 2021-08-28]
Mechanical/Community Parts/Target Holders/Target Plate Alignment.DXF
16.0 x 16.0
