ten-point-nine/freETarget/Mechanical/CNC/50m Pistol/50m Pistol PCB Cover.stl

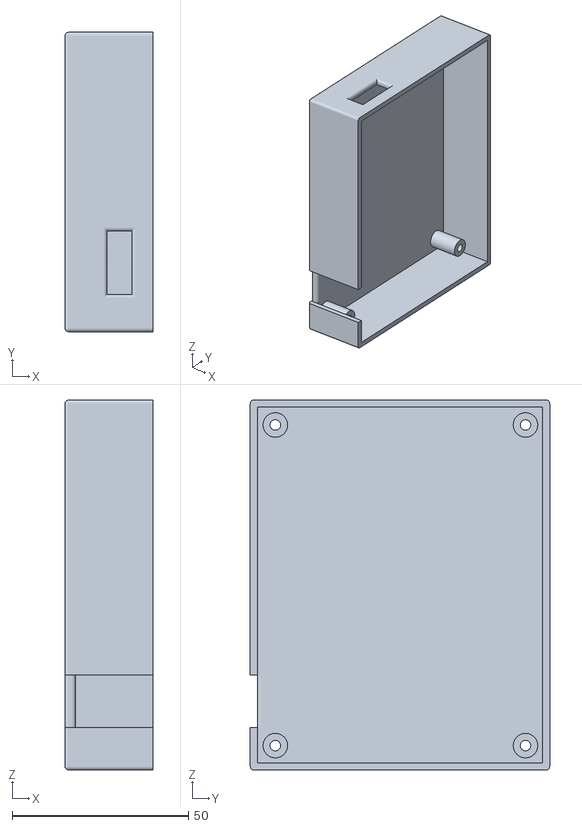
[picture p173: CAD file, 2026-03-02]
Mechanical/CNC/50m Pistol/50m Pistol PCB Cover.stl
25.0 x 85.0 x 105.0
