ten-point-nine/freETarget/Mechanical/CNC/Metal - Plastic/Magnetic Rifle Target.stl

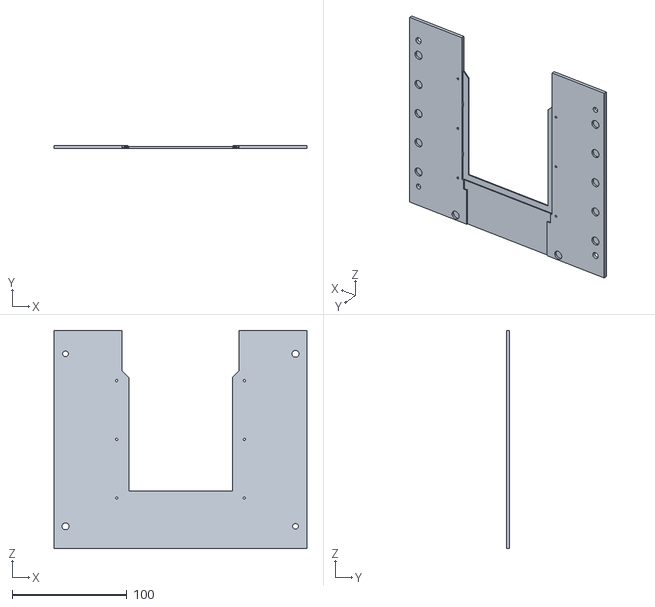
[picture p174: CAD file, 2026-03-23]
Mechanical/CNC/Metal - Plastic/Magnetic Rifle Target.stl
220.0 x 3.00 x 190.0
