ten-point-nine/freETarget/Mechanical/Community Parts/Sensor Mounts/ClipOn Target holder left.stl

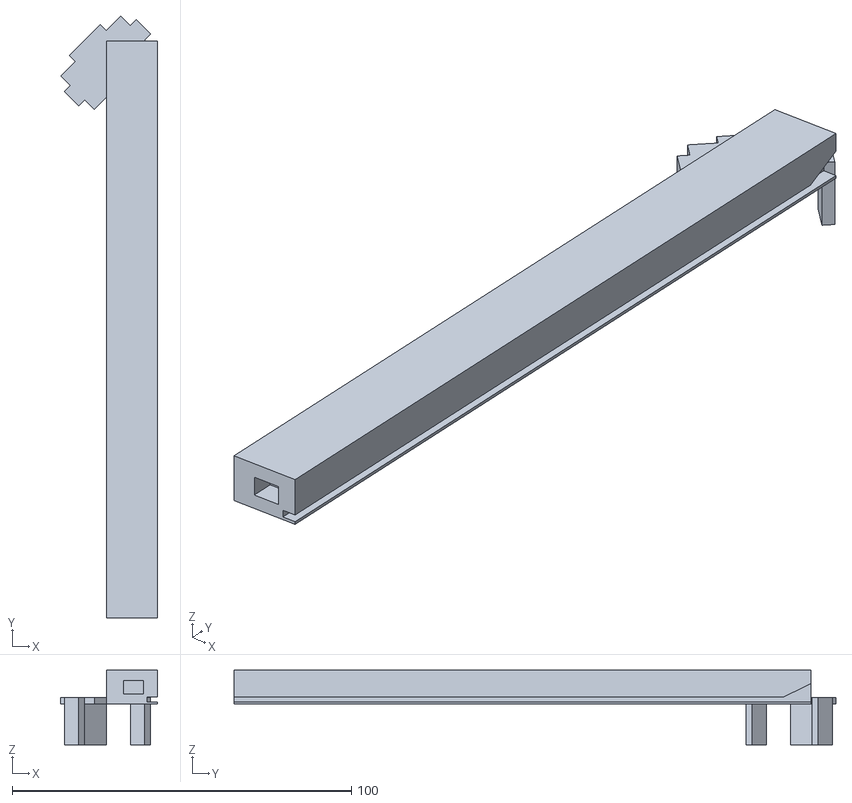
[picture p175: CAD file, 2021-10-19]
Mechanical/Community Parts/Sensor Mounts/ClipOn Target holder left.stl
28.5 x 177.4 x 22.0
