ten-point-nine/freETarget/Mechanical/Community Parts/Target Holders/Air Rifle Target Plate.DXF

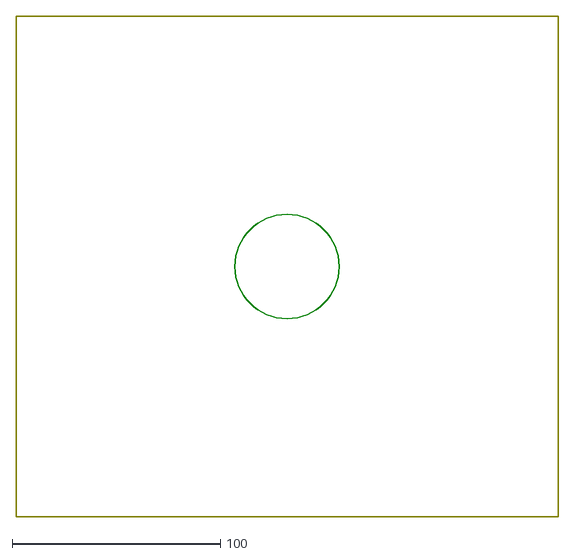
[picture p176: CAD file, 2021-08-28]
Mechanical/Community Parts/Target Holders/Air Rifle Target Plate.DXF
260.0 x 240.0
