ten-point-nine/freETarget/Mechanical/CNC/50m Pistol/PCB Case.stl

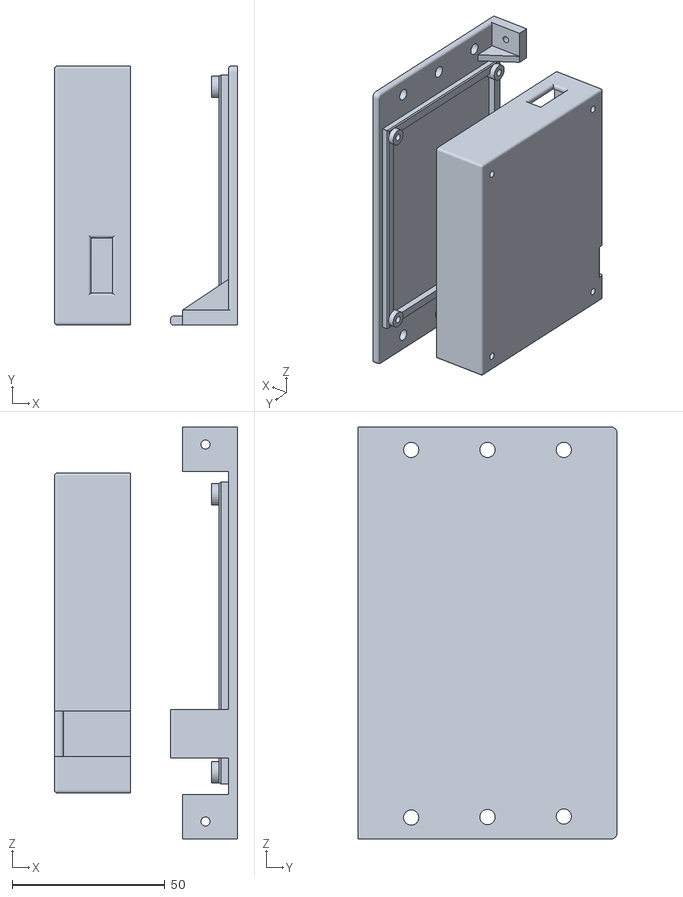
[picture p177: CAD file, 2026-03-02]
Mechanical/CNC/50m Pistol/PCB Case.stl
60.0 x 85.0 x 135.0
