ten-point-nine/freETarget/Mechanical/Community Parts/Sensor Mounts/ClipOn Sensor-Holder.stl

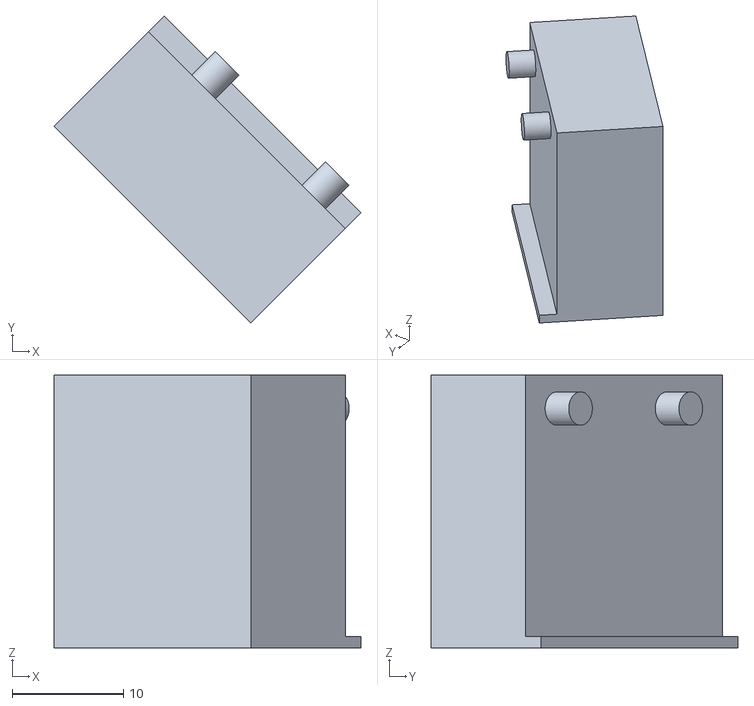
[picture p178: CAD file, 2021-10-19]
Mechanical/Community Parts/Sensor Mounts/ClipOn Sensor-Holder.stl
27.6 x 27.6 x 24.5
