ten-point-nine/freETarget/Mechanical/Community Parts/Target Holders/Air Pistol Target Plate.DXF

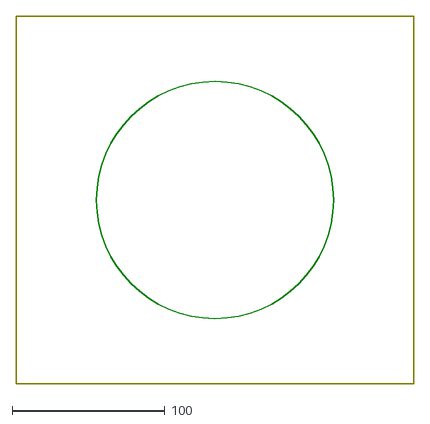
[picture p179: CAD file, 2021-08-28]
Mechanical/Community Parts/Target Holders/Air Pistol Target Plate.DXF
260.0 x 240.0
