ten-point-nine/freETarget/Mechanical/Community Parts/Sensor Mounts/ClipOn Target holder bottom.stl

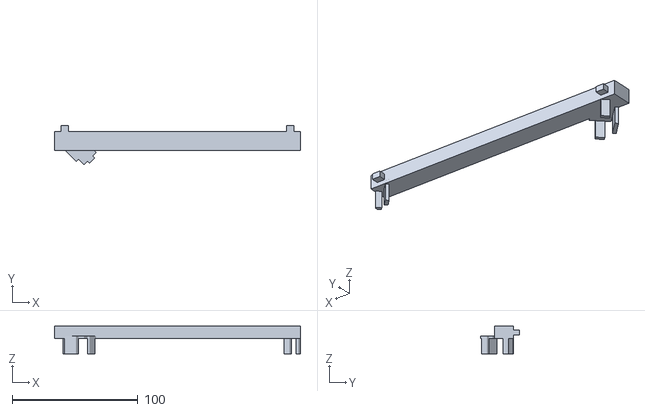
[picture p181: CAD file, 2021-10-19]
Mechanical/Community Parts/Sensor Mounts/ClipOn Target holder bottom.stl
196.0 x 31.4 x 22.0
