ten-point-nine/freETarget/Mechanical/Community Parts/Target Holders/target holder bottom.stl

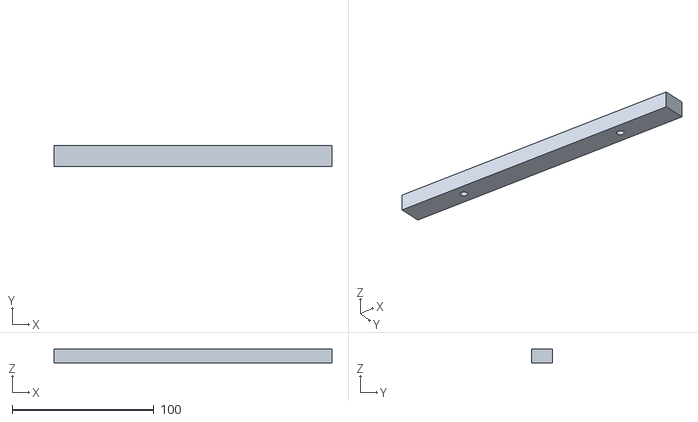
[picture p182: CAD file, 2021-08-04]
Mechanical/Community Parts/Target Holders/target holder bottom.stl
196.0 x 15.0 x 10.0
