ten-point-nine/freETarget/Mechanical/CNC/Metal - Plastic/Pistol Target.3mf

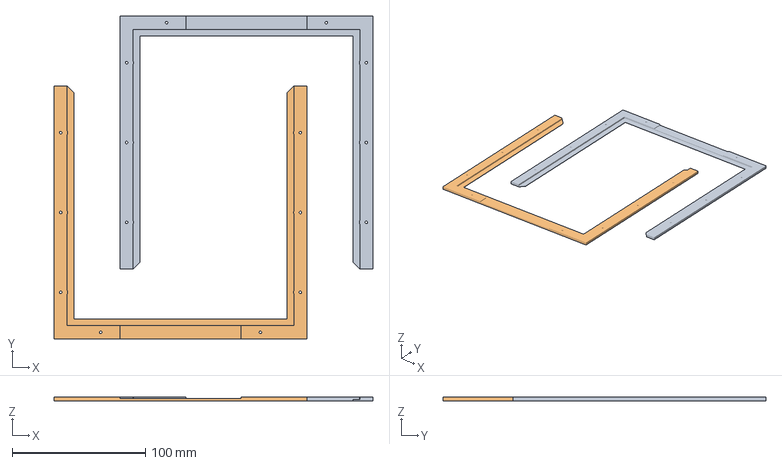
[picture p183: CAD file, 2026-03-23]
Mechanical/CNC/Metal - Plastic/Pistol Target.3mf
239.5 x 242.5 x 3.00 mm
Pistol Target.stl x 2
