ten-point-nine/freETarget/Mechanical/Community Parts/Sensor Mounts/SensorBase.stl

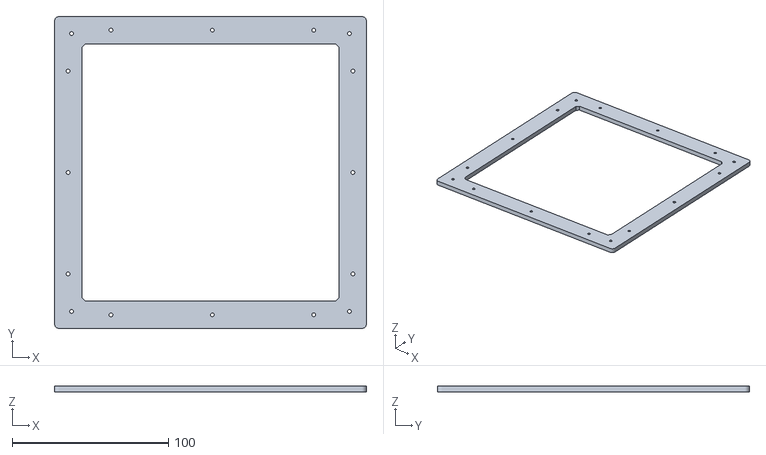
[picture p184: CAD file, 2021-08-28]
Mechanical/Community Parts/Sensor Mounts/SensorBase.stl
200.0 x 200.0 x 4.00
