ten-point-nine/freETarget/Mechanical/CNC/Metal - Plastic/Witness Paper Spacer.stl

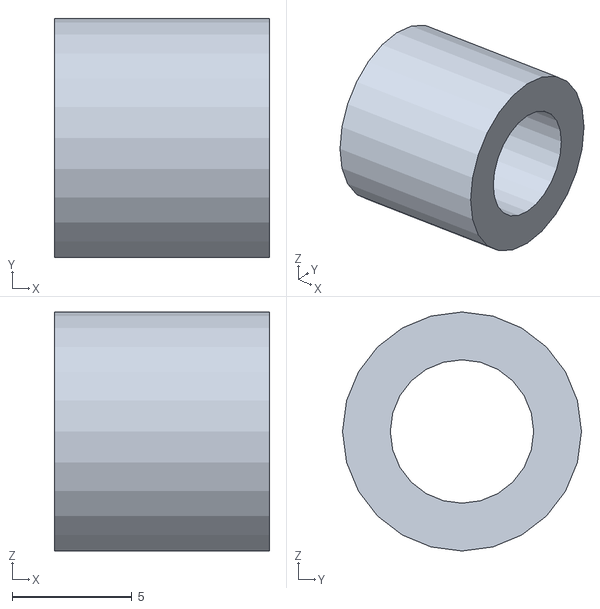
[picture p185: CAD file, 2026-03-23]
Mechanical/CNC/Metal - Plastic/Witness Paper Spacer.stl
9.00 x 10.0 x 10.0
