ten-point-nine/freETarget/Mechanical/Community Parts/Sensor Mounts/quarter sensor holder .stl

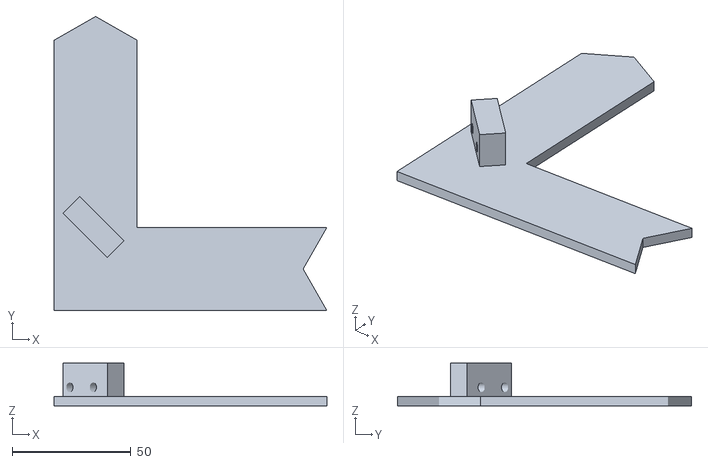
[picture p186: CAD file, 2021-08-28]
Mechanical/Community Parts/Sensor Mounts/quarter sensor holder .stl
115.0 x 124.0 x 18.0
