ten-point-nine/freETarget/Mechanical/Community Parts/Sensor Mounts/SensorMount.stl

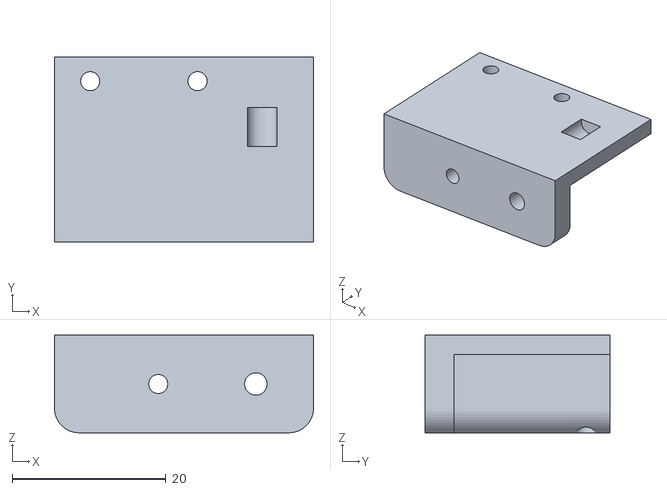
[picture p187: CAD file, 2021-08-28]
Mechanical/Community Parts/Sensor Mounts/SensorMount.stl
33.7 x 24.1 x 12.7
