ten-point-nine/freETarget/Mechanical/Community Parts/Sensor Mounts/sensor holder.stl

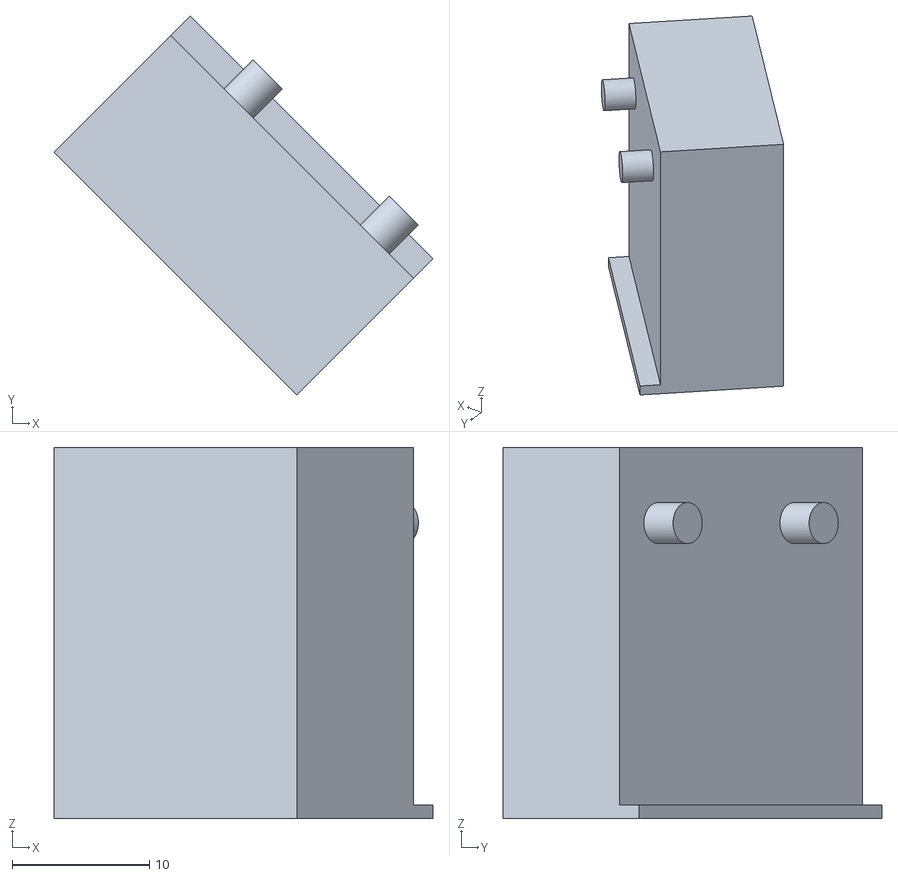
[picture p188: CAD file, 2021-08-04]
Mechanical/Community Parts/Sensor Mounts/sensor holder.stl
27.6 x 27.6 x 27.0
