ten-point-nine/freETarget/Mechanical/CNC/Metal - Plastic/Traffic Lights Case.stl

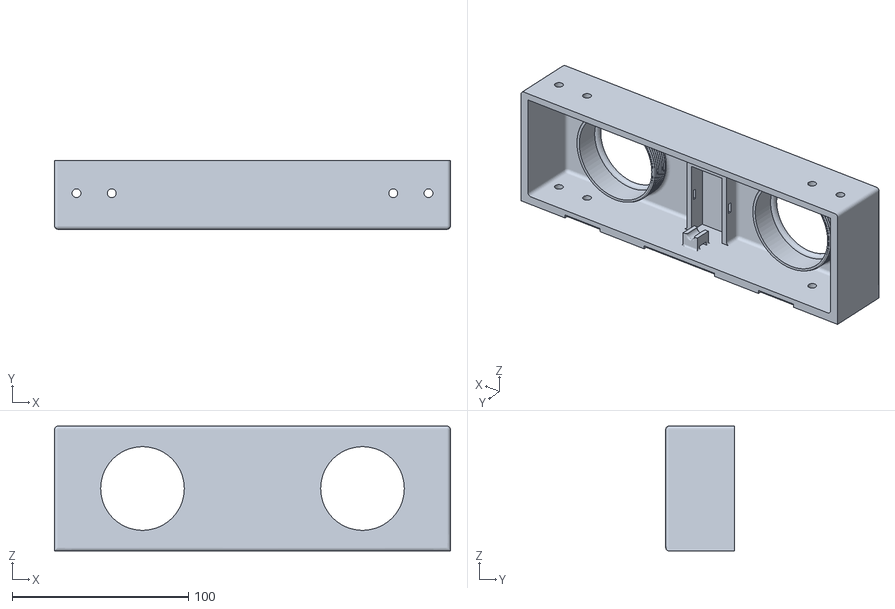
[picture p189: CAD file, 2025-10-30]
Mechanical/CNC/Metal - Plastic/Traffic Lights Case.stl
225.0 x 39.0 x 71.0
