ten-point-nine/freETarget/Mechanical/CNC/Metal - Plastic/Pistol Test Holder.stl

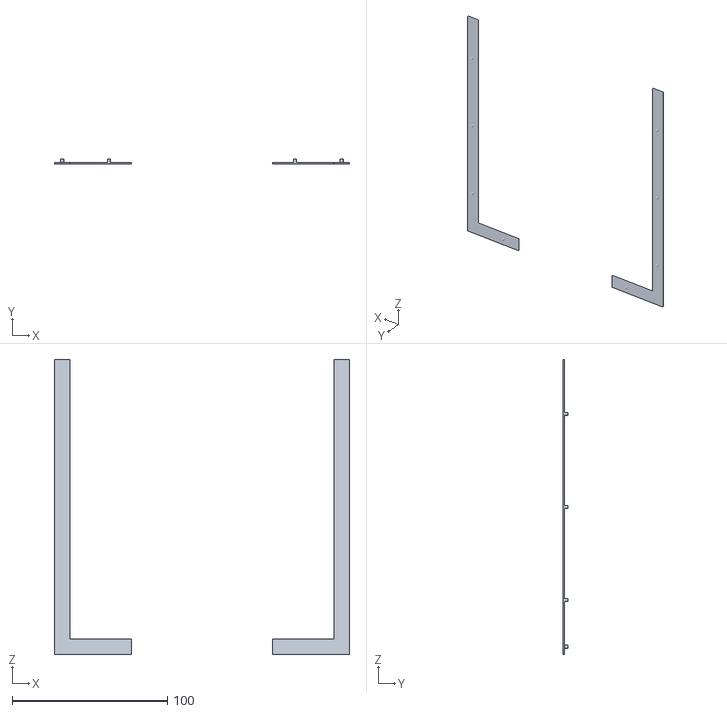
[picture p190: CAD file, 2025-10-30]
Mechanical/CNC/Metal - Plastic/Pistol Test Holder.stl
190.0 x 3.00 x 190.0
