ten-point-nine/freETarget/Mechanical/CNC/Metal - Plastic/Traffic Lights Lock Ring.stl

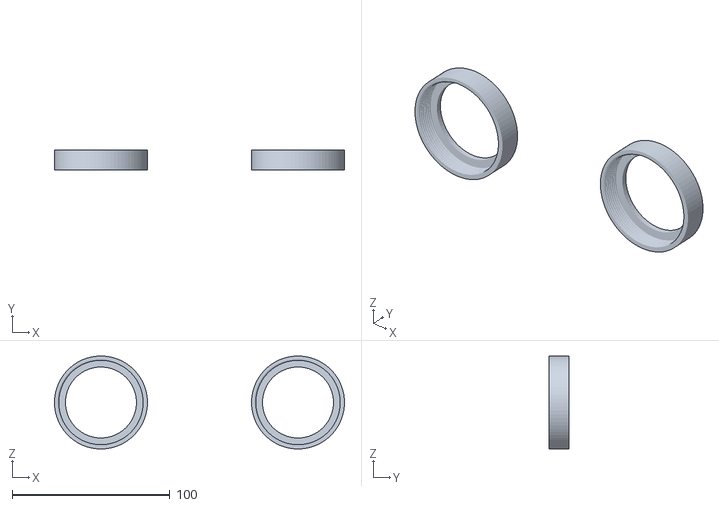
[picture p191: CAD file, 2025-10-30]
Mechanical/CNC/Metal - Plastic/Traffic Lights Lock Ring.stl
184.0 x 13.0 x 59.0
