ten-point-nine/freETarget/Mechanical/CNC/Metal - Plastic/Traffic Lights Back Cover.stl

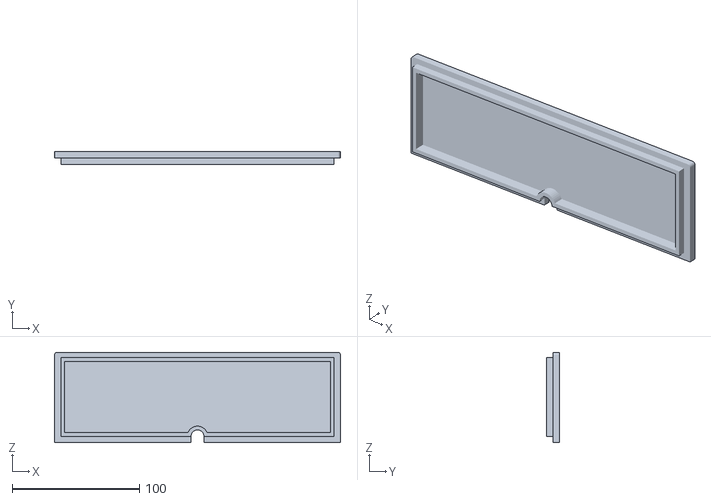
[picture p192: CAD file, 2025-10-30]
Mechanical/CNC/Metal - Plastic/Traffic Lights Back Cover.stl
225.0 x 10.0 x 71.0
