ten-point-nine/freETarget/Mechanical/CNC/Metal - Plastic/ISSF 50m Rifle Target Cover.stl

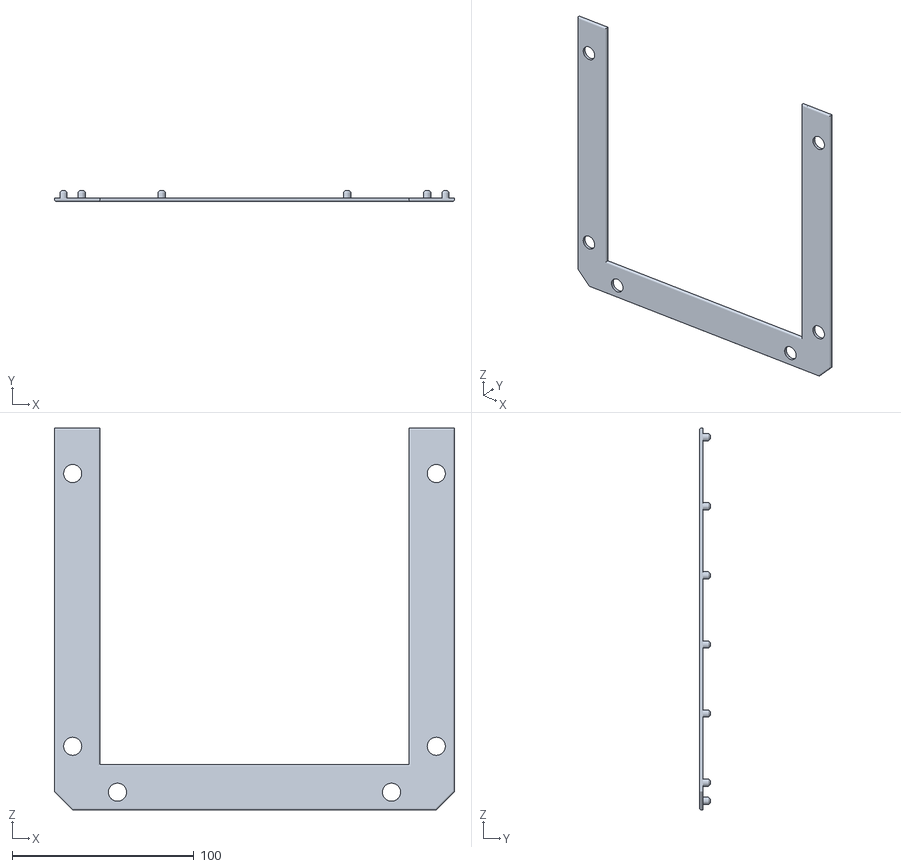
[picture p193: CAD file, 2025-09-09]
Mechanical/CNC/Metal - Plastic/ISSF 50m Rifle Target Cover.stl
220.0 x 6.00 x 210.0
