ten-point-nine/freETarget/Mechanical/CNC/Metal - Plastic/Cover Sprue.stl

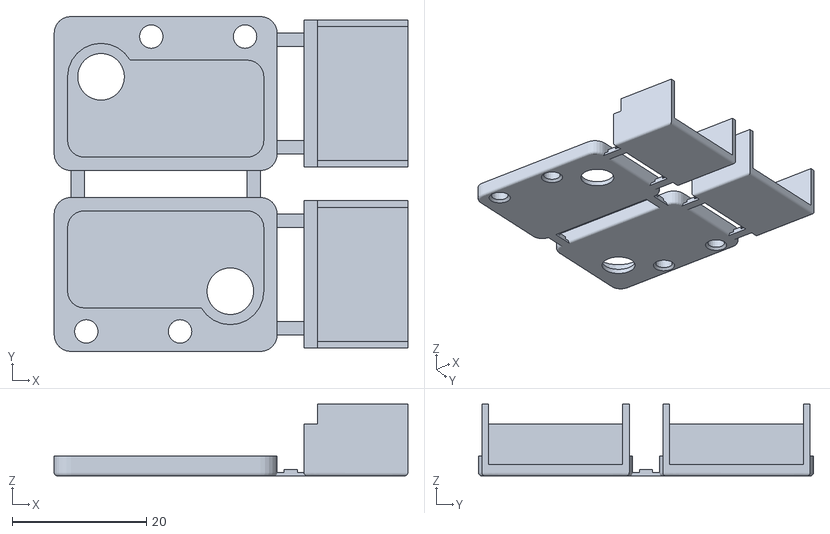
[picture p194: CAD file, 2025-09-09]
Mechanical/CNC/Metal - Plastic/Cover Sprue.stl
52.8 x 50.0 x 10.7
