ten-point-nine/freETarget/Mechanical/CNC/Metal - Plastic/Cable Tie.stl

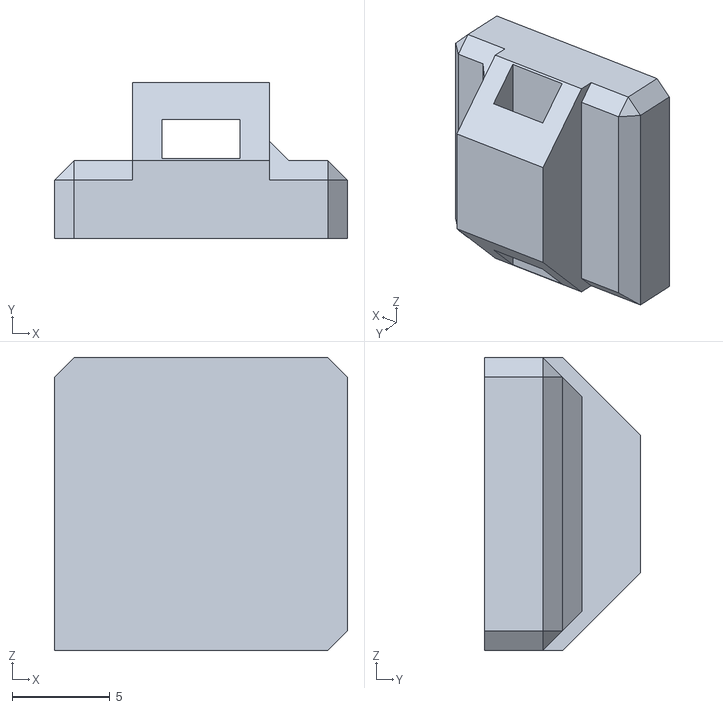
[picture p195: CAD file, 2025-09-09]
Mechanical/CNC/Metal - Plastic/Cable Tie.stl
15.0 x 8.00 x 15.0
