ten-point-nine/freETarget/Mechanical/CNC/Metal - Plastic/50m Corners 2.stl

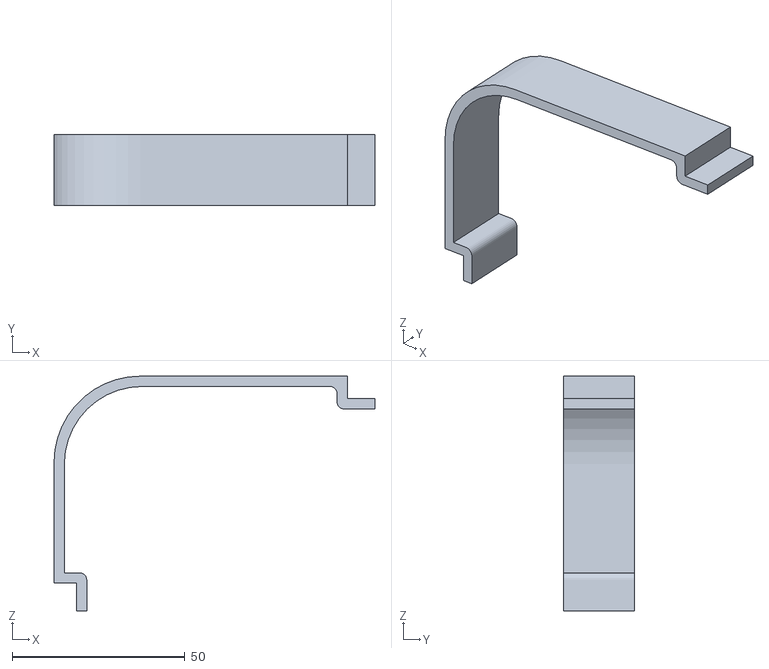
[picture p196: CAD file, 2025-05-21]
Mechanical/CNC/Metal - Plastic/50m Corners 2.stl
93.0 x 20.5 x 68.0
