ten-point-nine/freETarget/Mechanical/CNC/Metal - Plastic/PCB Base 2.stl

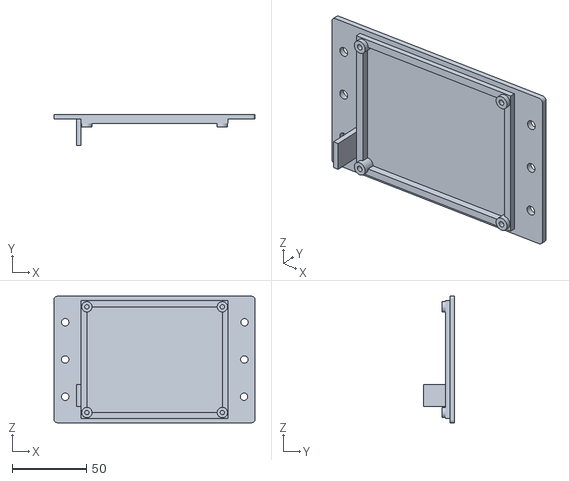
[picture p197: CAD file, 2025-05-21]
Mechanical/CNC/Metal - Plastic/PCB Base 2.stl
135.0 x 21.0 x 85.0
