ten-point-nine/freETarget/Mechanical/CNC/Metal - Plastic/Connector Cover 2.stl

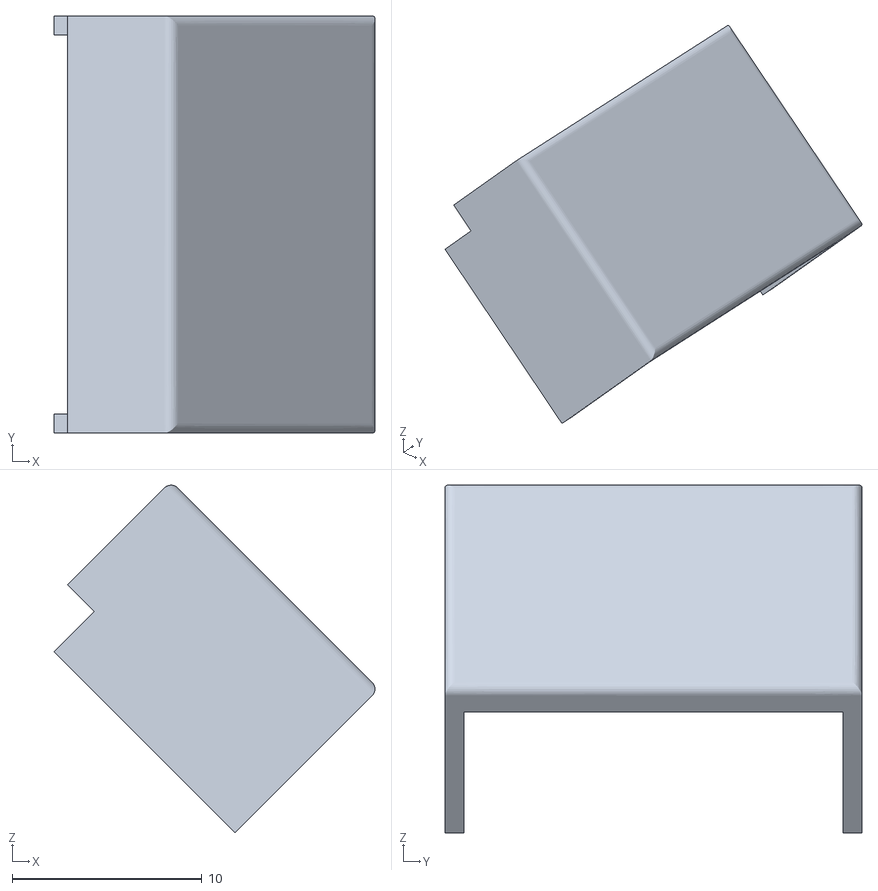
[picture p198: CAD file, 2025-05-21]
Mechanical/CNC/Metal - Plastic/Connector Cover 2.stl
16.9 x 22.0 x 18.3
