ten-point-nine/freETarget/Mechanical/CNC/Metal - Plastic/Sensor Cover.stl

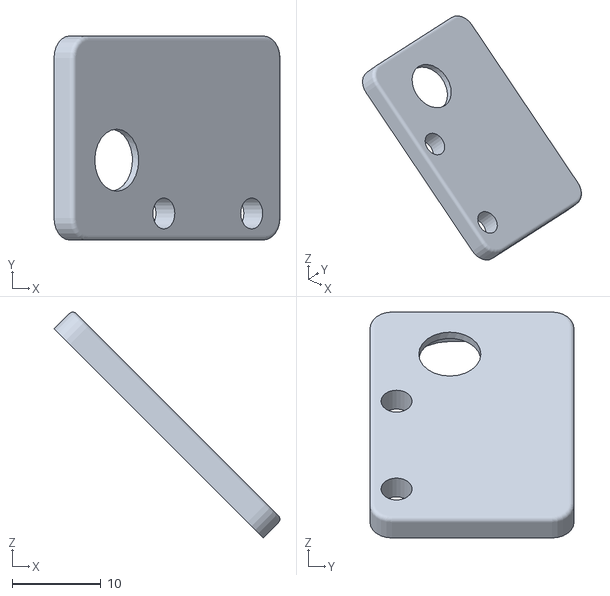
[picture p199: CAD file, 2025-05-21]
Mechanical/CNC/Metal - Plastic/Sensor Cover.stl
25.5 x 23.0 x 25.5
