ten-point-nine/freETarget/Mechanical/CNC/Metal - Plastic/Suis.stl

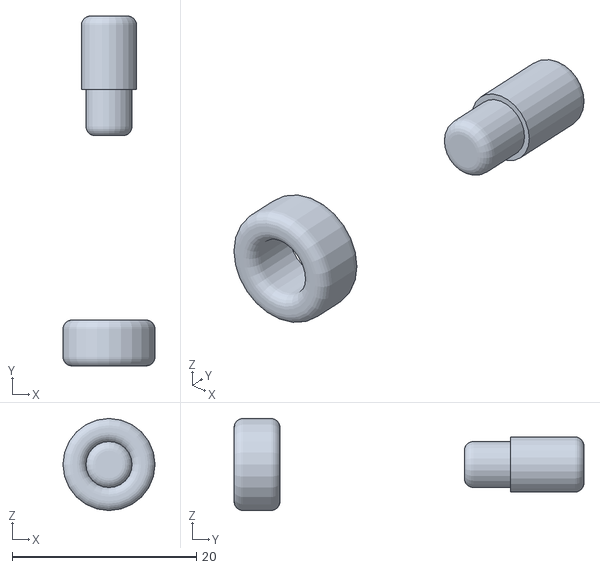
[picture p200: CAD file, 2024-12-17]
Mechanical/CNC/Metal - Plastic/Suis.stl
10.0 x 38.0 x 10.0
