ten-point-nine/freETarget/Mechanical/CNC/Metal - Plastic/50m Pistol Bushing.stl

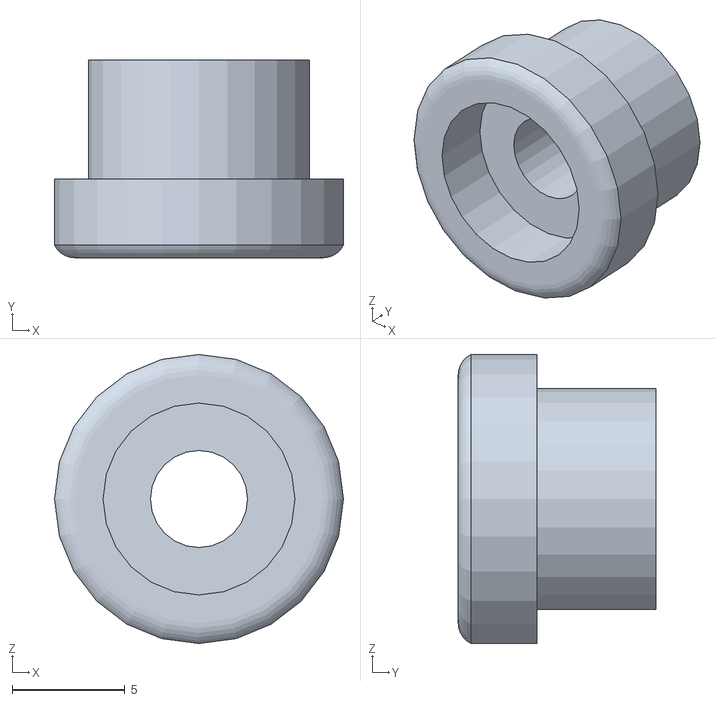
[picture p201: CAD file, 2024-12-17]
Mechanical/CNC/Metal - Plastic/50m Pistol Bushing.stl
12.8 x 8.75 x 12.8
