ten-point-nine/freETarget/Mechanical/CNC/Metal - Plastic/50m Pistol Clamp.stl

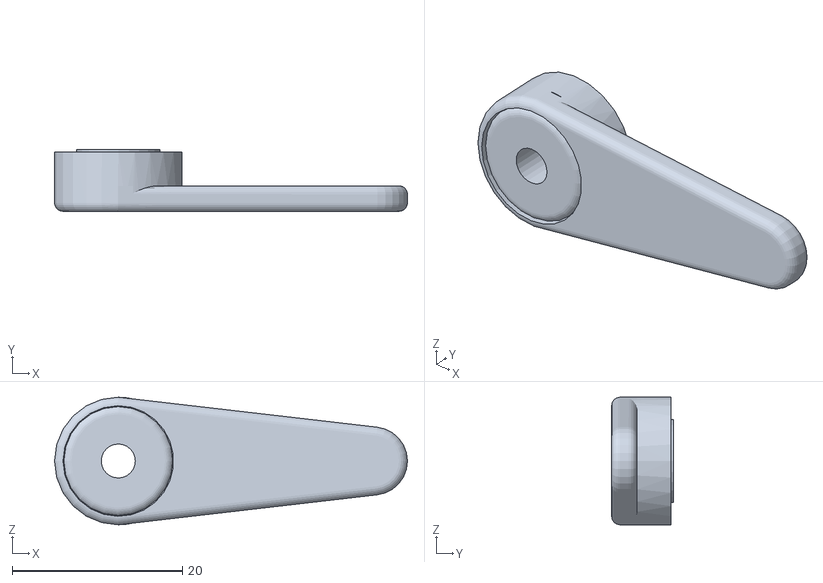
[picture p202: CAD file, 2024-12-17]
Mechanical/CNC/Metal - Plastic/50m Pistol Clamp.stl
41.5 x 7.25 x 15.0
