ten-point-nine/freETarget/Documentation/Pictures/ Cabling Installed.png

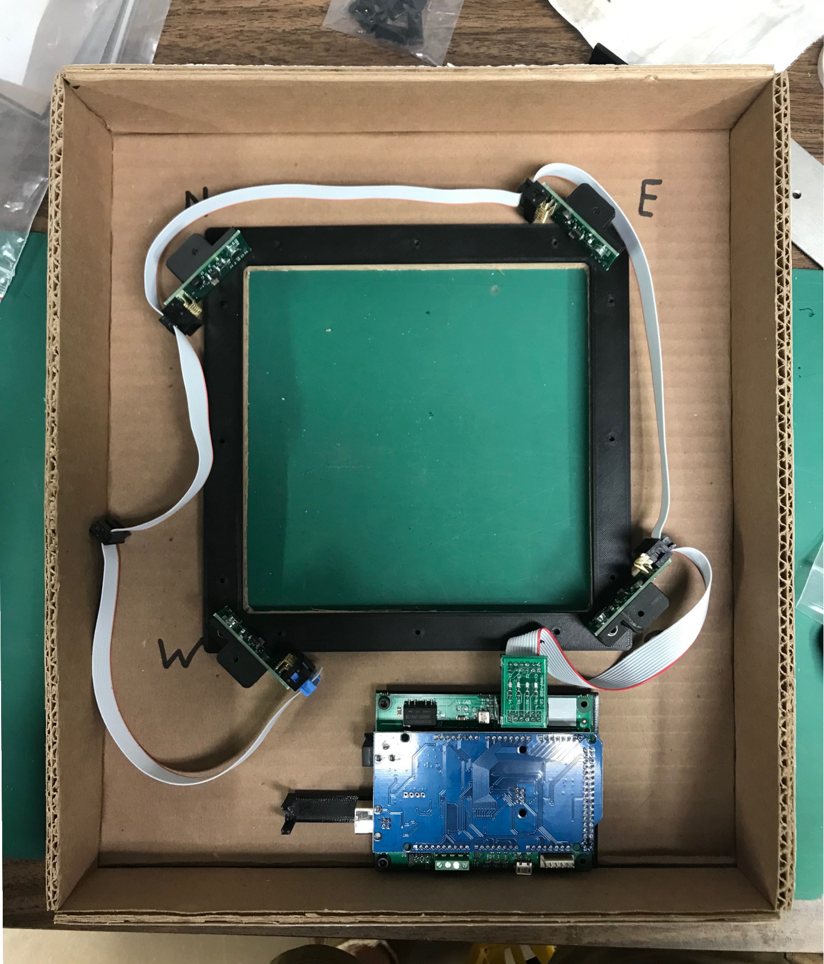
Documentation/Pictures/ Cabling Installed.png
