ten-point-nine/freETarget/Documentation/Pictures/Target Assembly.png

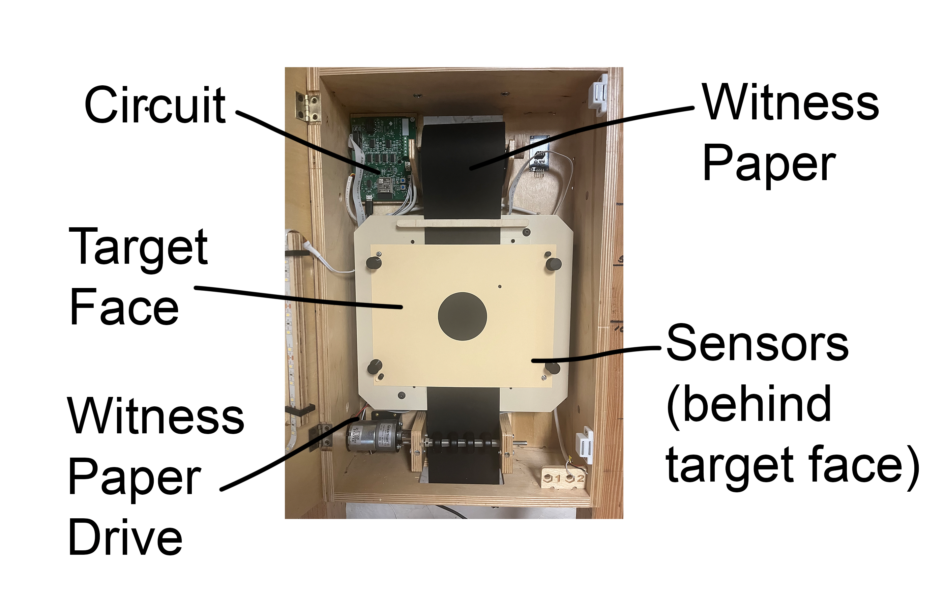
Documentation/Pictures/Target Assembly.png
