ten-point-nine/freETarget/Mechanical/CAD Files/Assembled.png

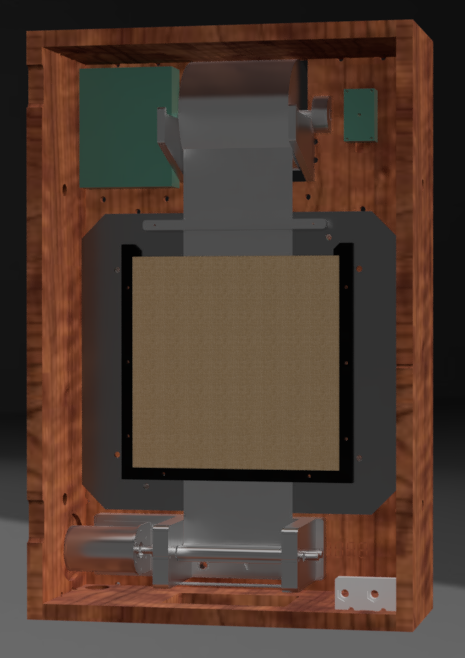
Mechanical/CAD Files/Assembled.png
