ten-point-nine/freETarget/KiCad/Version 3.1 Schematics/SCHEMATIC_freETarget3p1.pdf

INSTALL R10 ONLY HIGH PASS CABLE | FILTER
10 | 13579 R2 | 0R

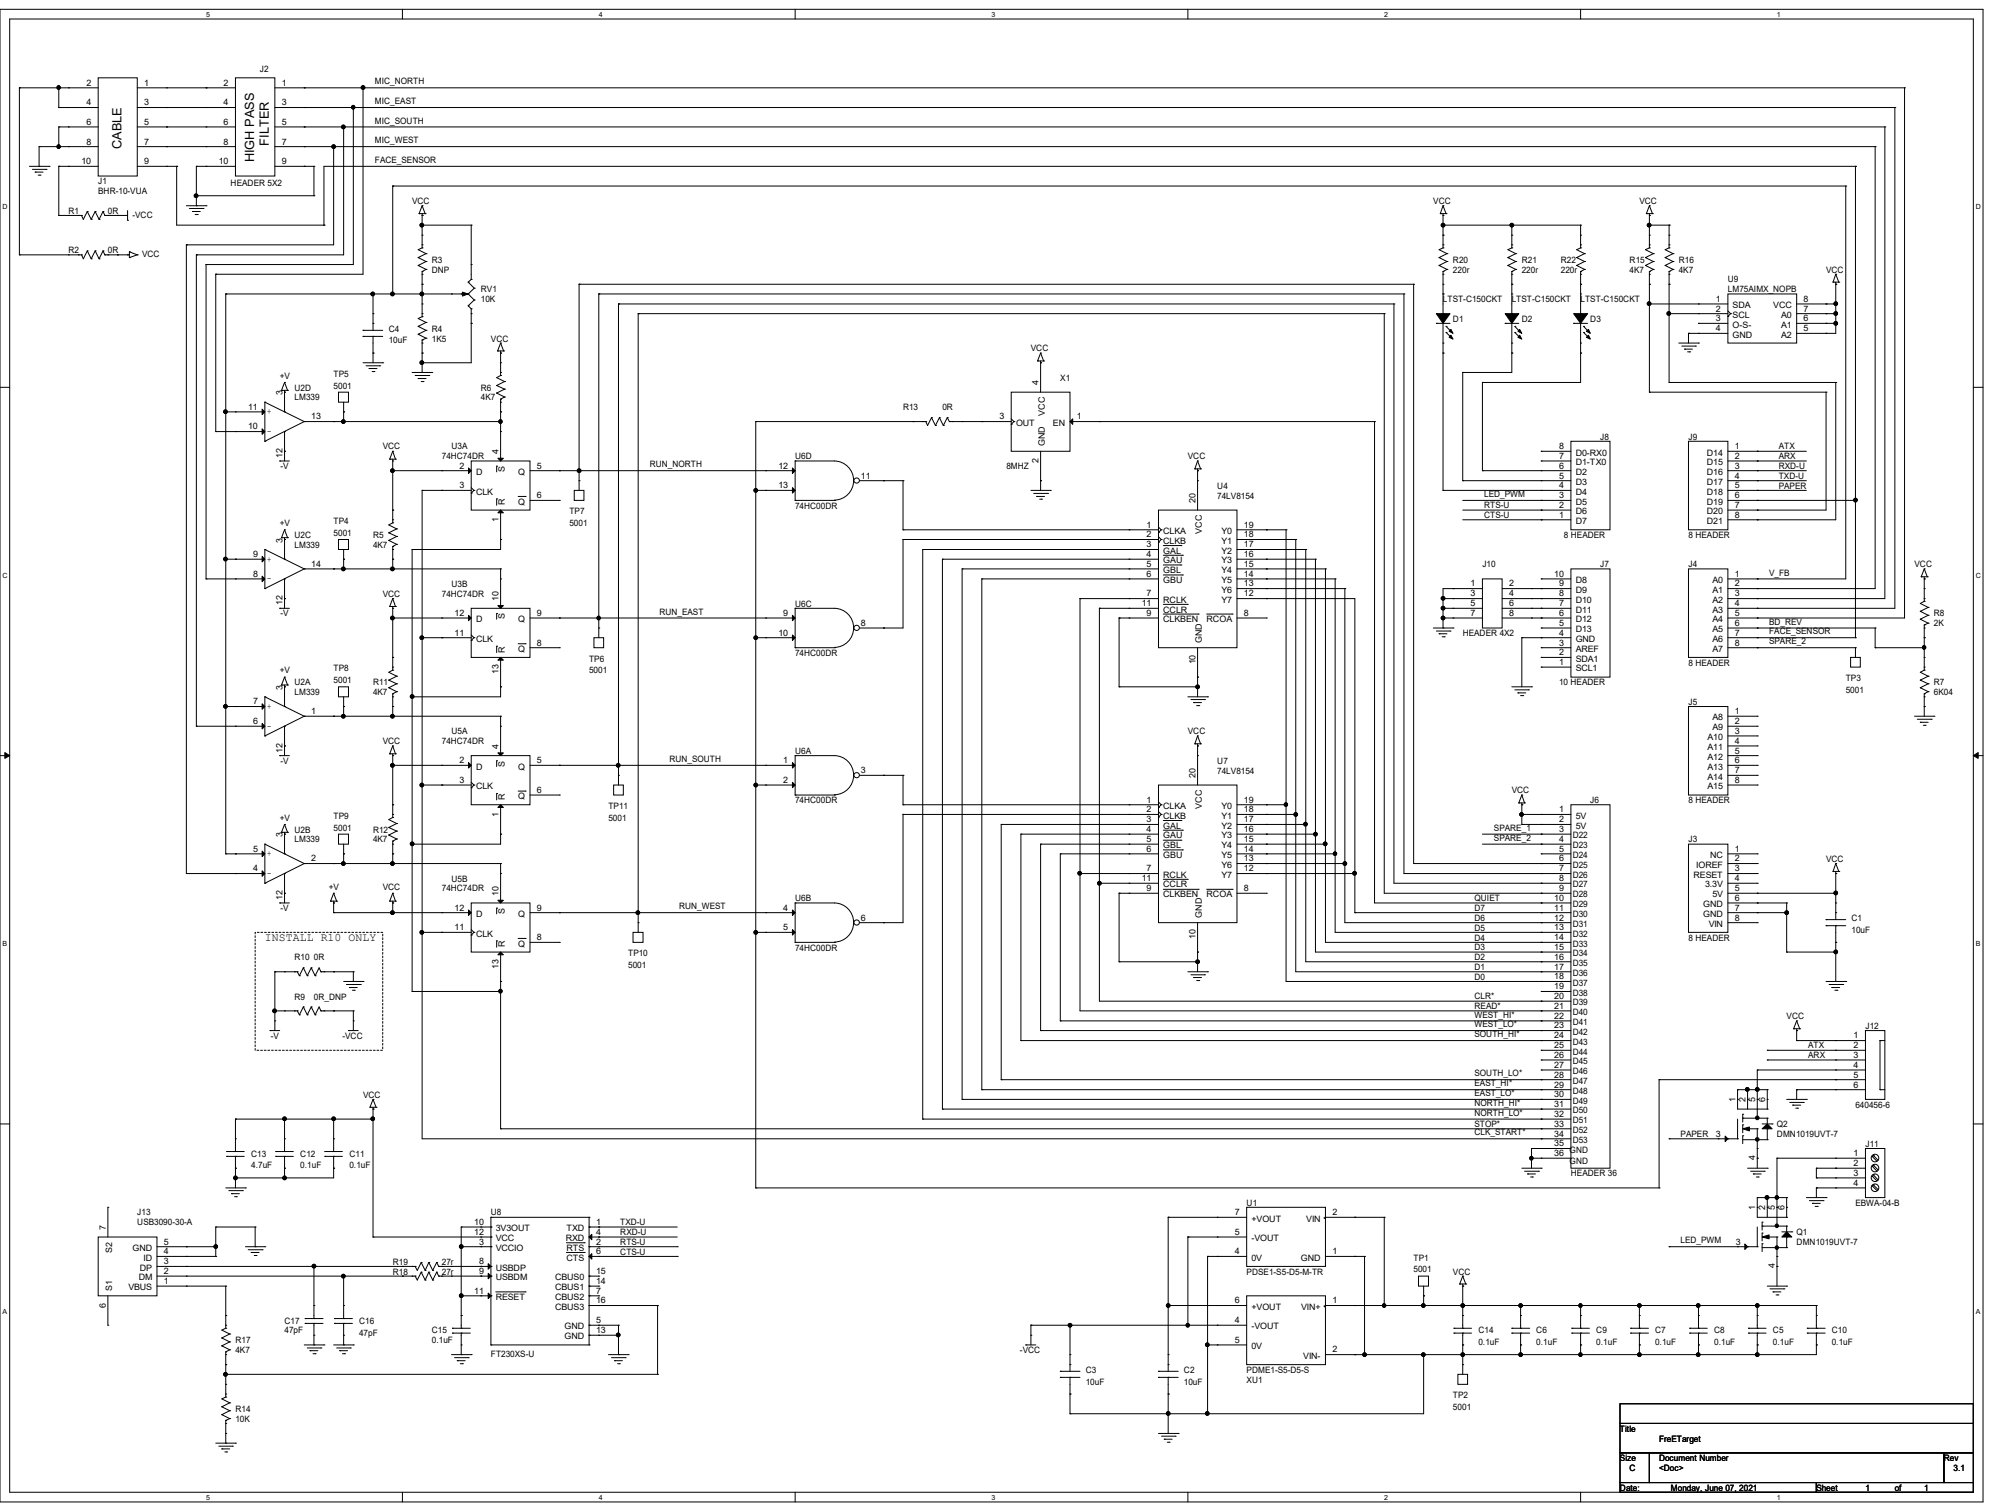
[picture p266: page 1]
