ten-point-nine/freETarget/Mechanical/Dimensioned Drawings/Shooting Table/FET-0225 BASE SHOOTING TAGLE ASSEMBLY.PDF

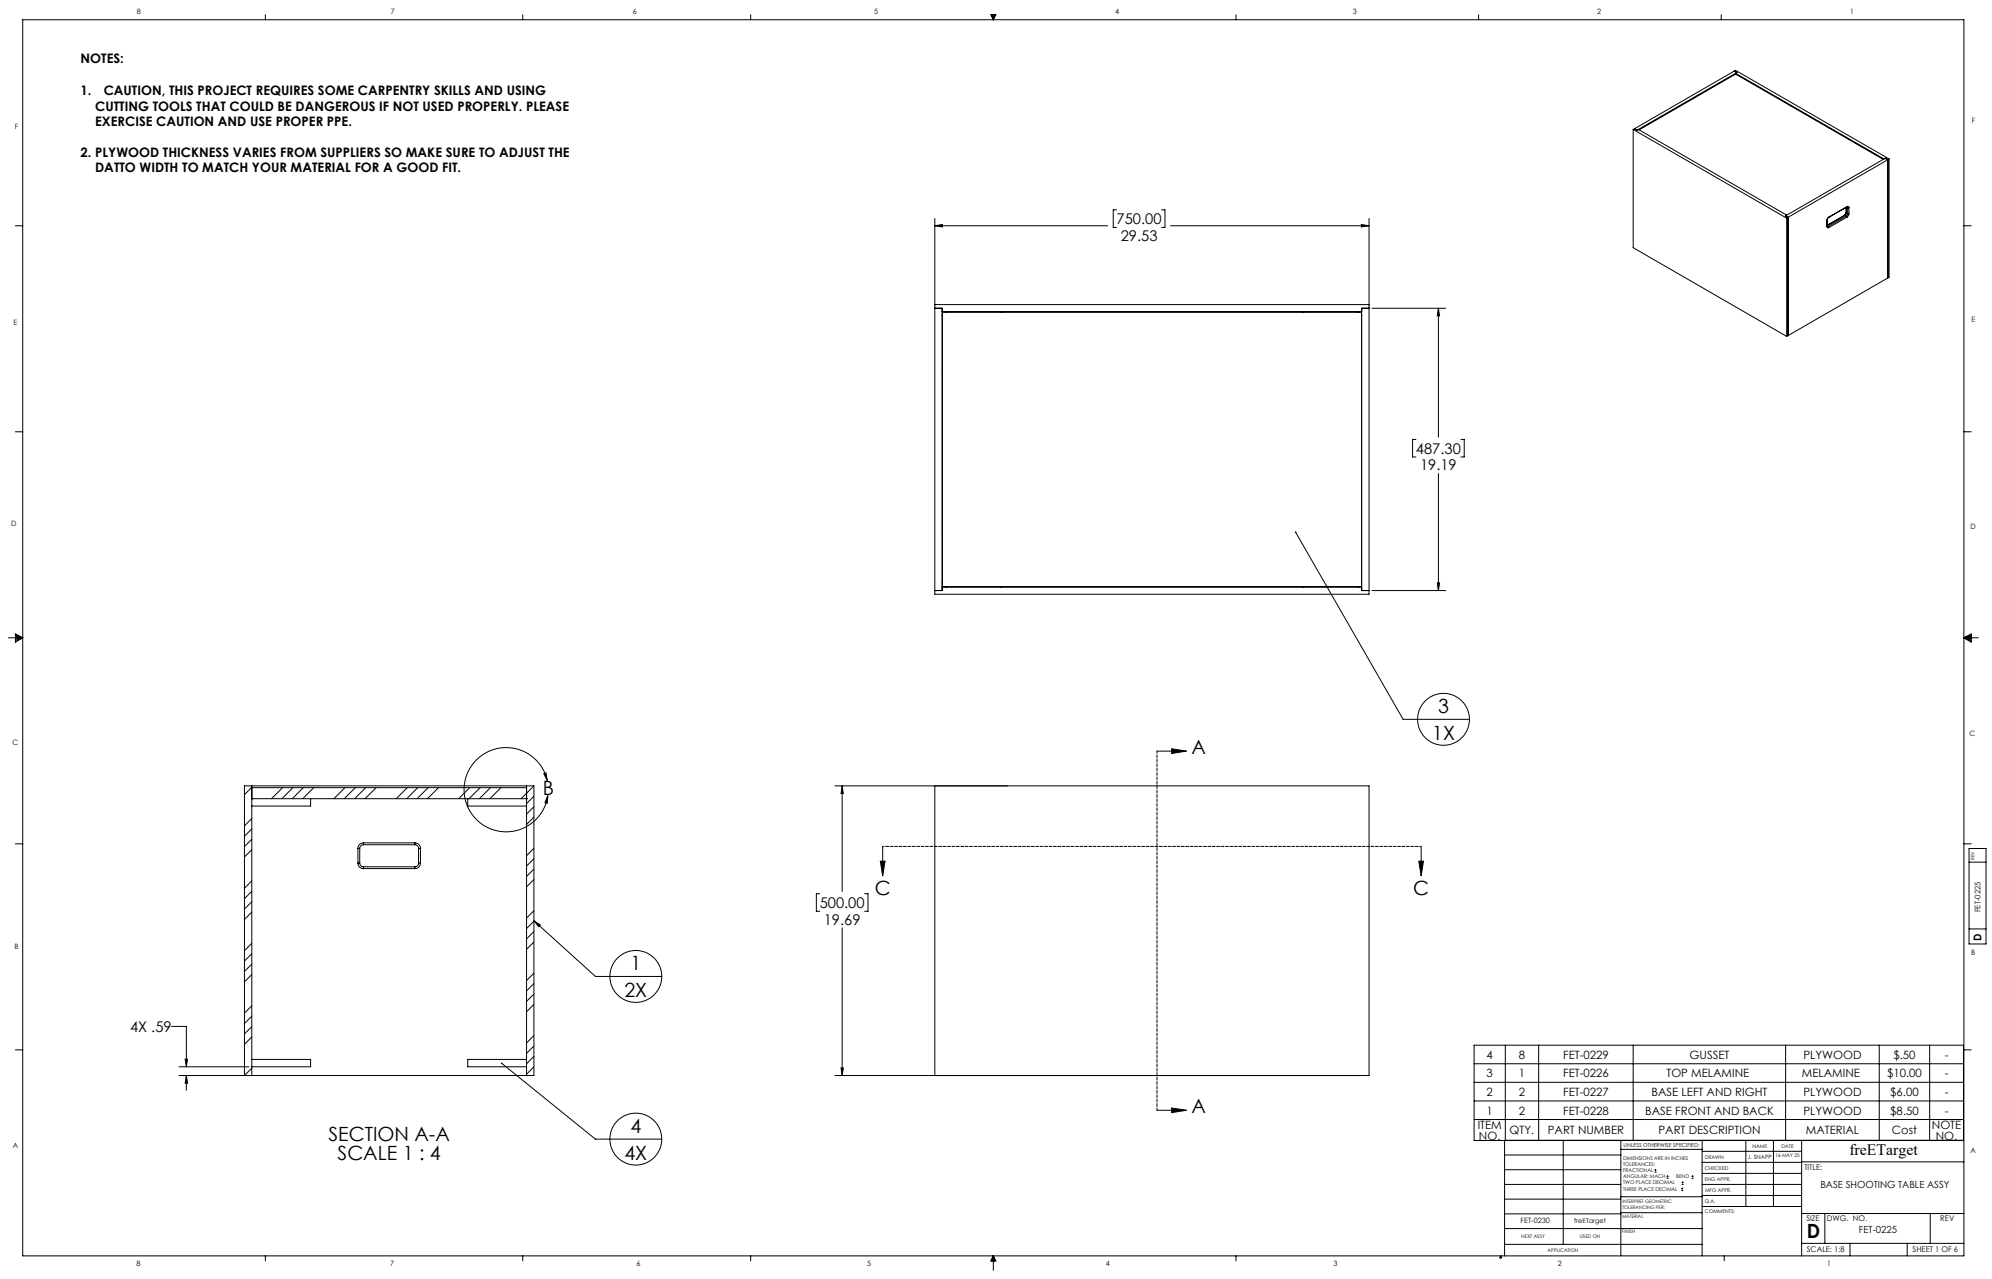
[picture p267: page 1]
SECTION A-A SCALE 1 : 4 A A; FREV FET-0225; SHEET 1 OF 6; J. SNAPP 16 MAY 25; SCALE: 1:8; DWG. NO.; REV; freETarget NAME; DATE; MFG APPR.; ENG APPR.; INTERPRET GEOMETRIC TOLERANCING PER:; ANGULAR: MACH; BEND; NEXT ASSY; USED ON

NOTES:
1. CAUTION, THIS PROJECT REQUIRES SOME CARPENTRY SKILLS AND USING
CUTTING TOOLS THAT COULD BE DANGEROUS IF NOT USED PROPERLY. PLEASE
EXERCISE CAUTION AND USE PROPER PPE.
2. PLYWOOD THICKNESS VARIES FROM SUPPLIERS SO MAKE SURE TO ADJUST THE
DATTO WIDTH TO MATCH YOUR MATERIAL FOR A GOOD FIT.

4 | 8 | FET-0229 | GUSSET | PLYWOOD | $.50 | -
3 | 1 | FET-0226 | TOP MELAMINE | MELAMINE | $10.00 | -
2 | 2 | FET-0227 | BASE LEFT AND RIGHT | PLYWOOD | $6.00 | -
1 | 2 | FET-0228 | BASE FRONT AND BACK | PLYWOOD | $8.50 | -
ITEM NO. | QTY. | PART NUMBER | PART DESCRIPTION | MATERIAL | Cost | NOTE NO.

UNLESS OTHERWISE SPECIFIED:

DIMENSIONS ARE IN INCHES
TOLERANCES:
FRACTIONAL
TWO PLACE DECIMAL
THREE PLACE DECIMAL

TITLE:
BASE SHOOTING TABLE ASSY

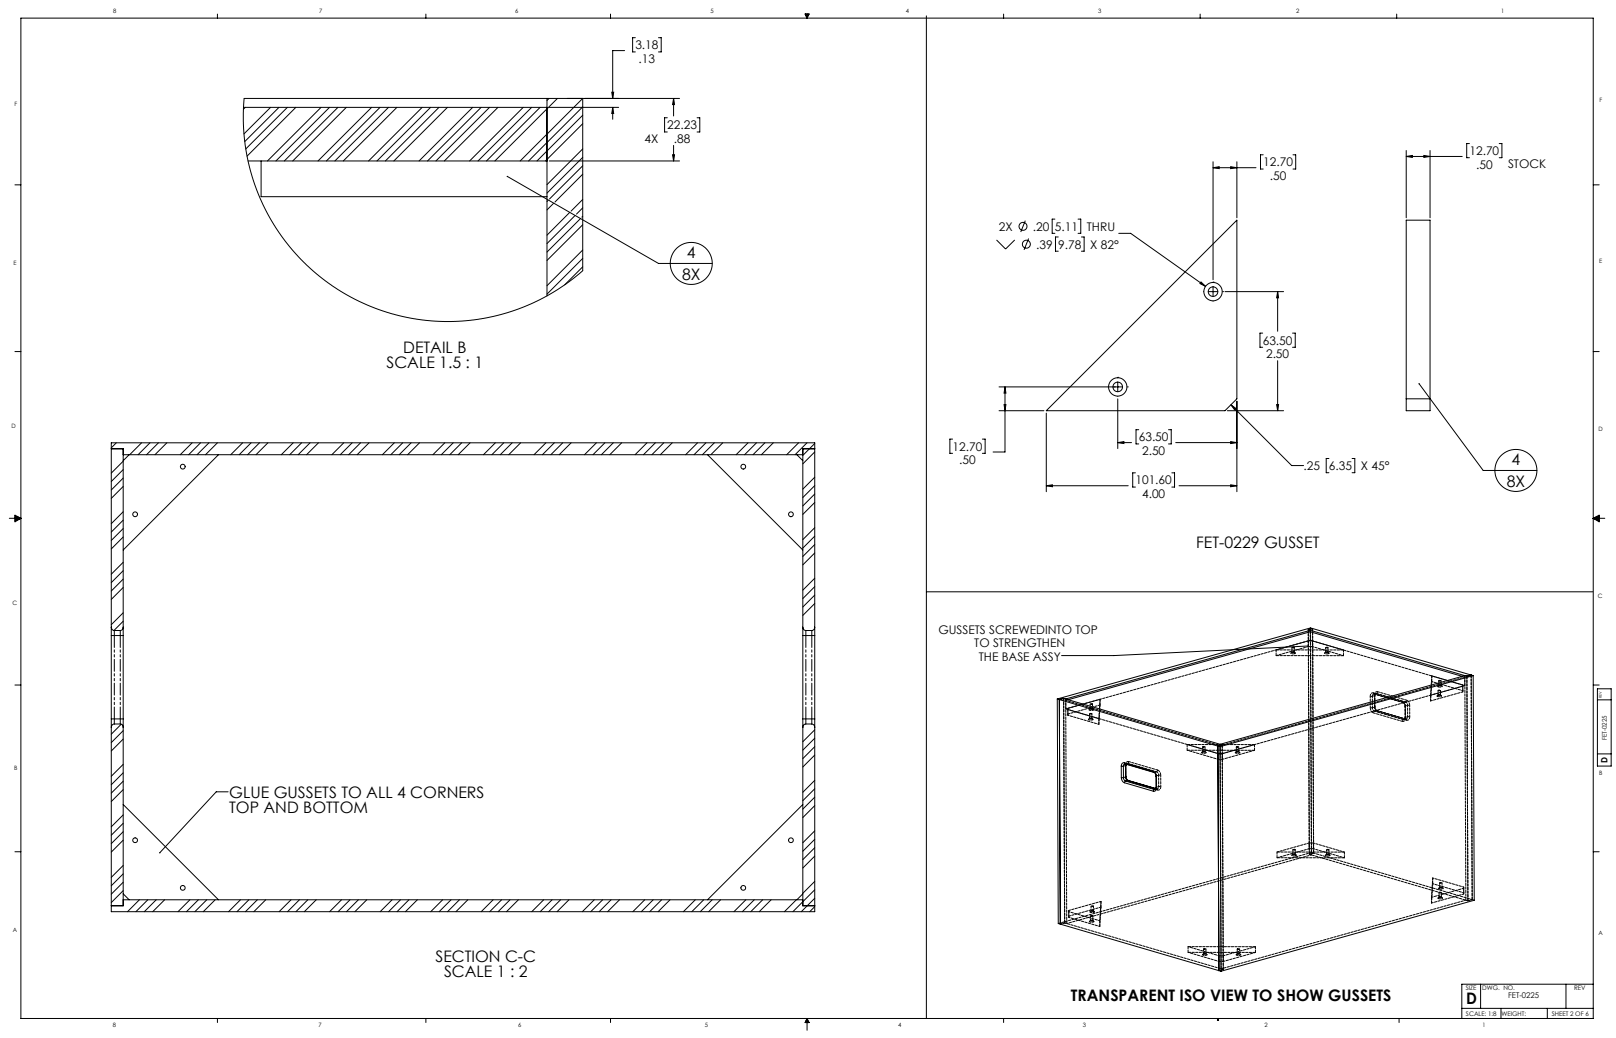
[picture p268: page 2]
SECTION C-C SCALE 1 : 2; .20 5.11 THRU; .50 STOCK; DETAIL B SCALE 1.5 : 1; FET-0229 GUSSET; FREV FET-0225; SCALE: 1:8 WEIGHT:; SHEET 2 OF 6

GUSSETS SCREWEDINTO TOP
TO STRENGTHEN
THE BASE ASSY

GLUE GUSSETS TO ALL 4 CORNERS
TOP AND BOTTOM

TRANSPARENT ISO VIEW TO SHOW GUSSETS

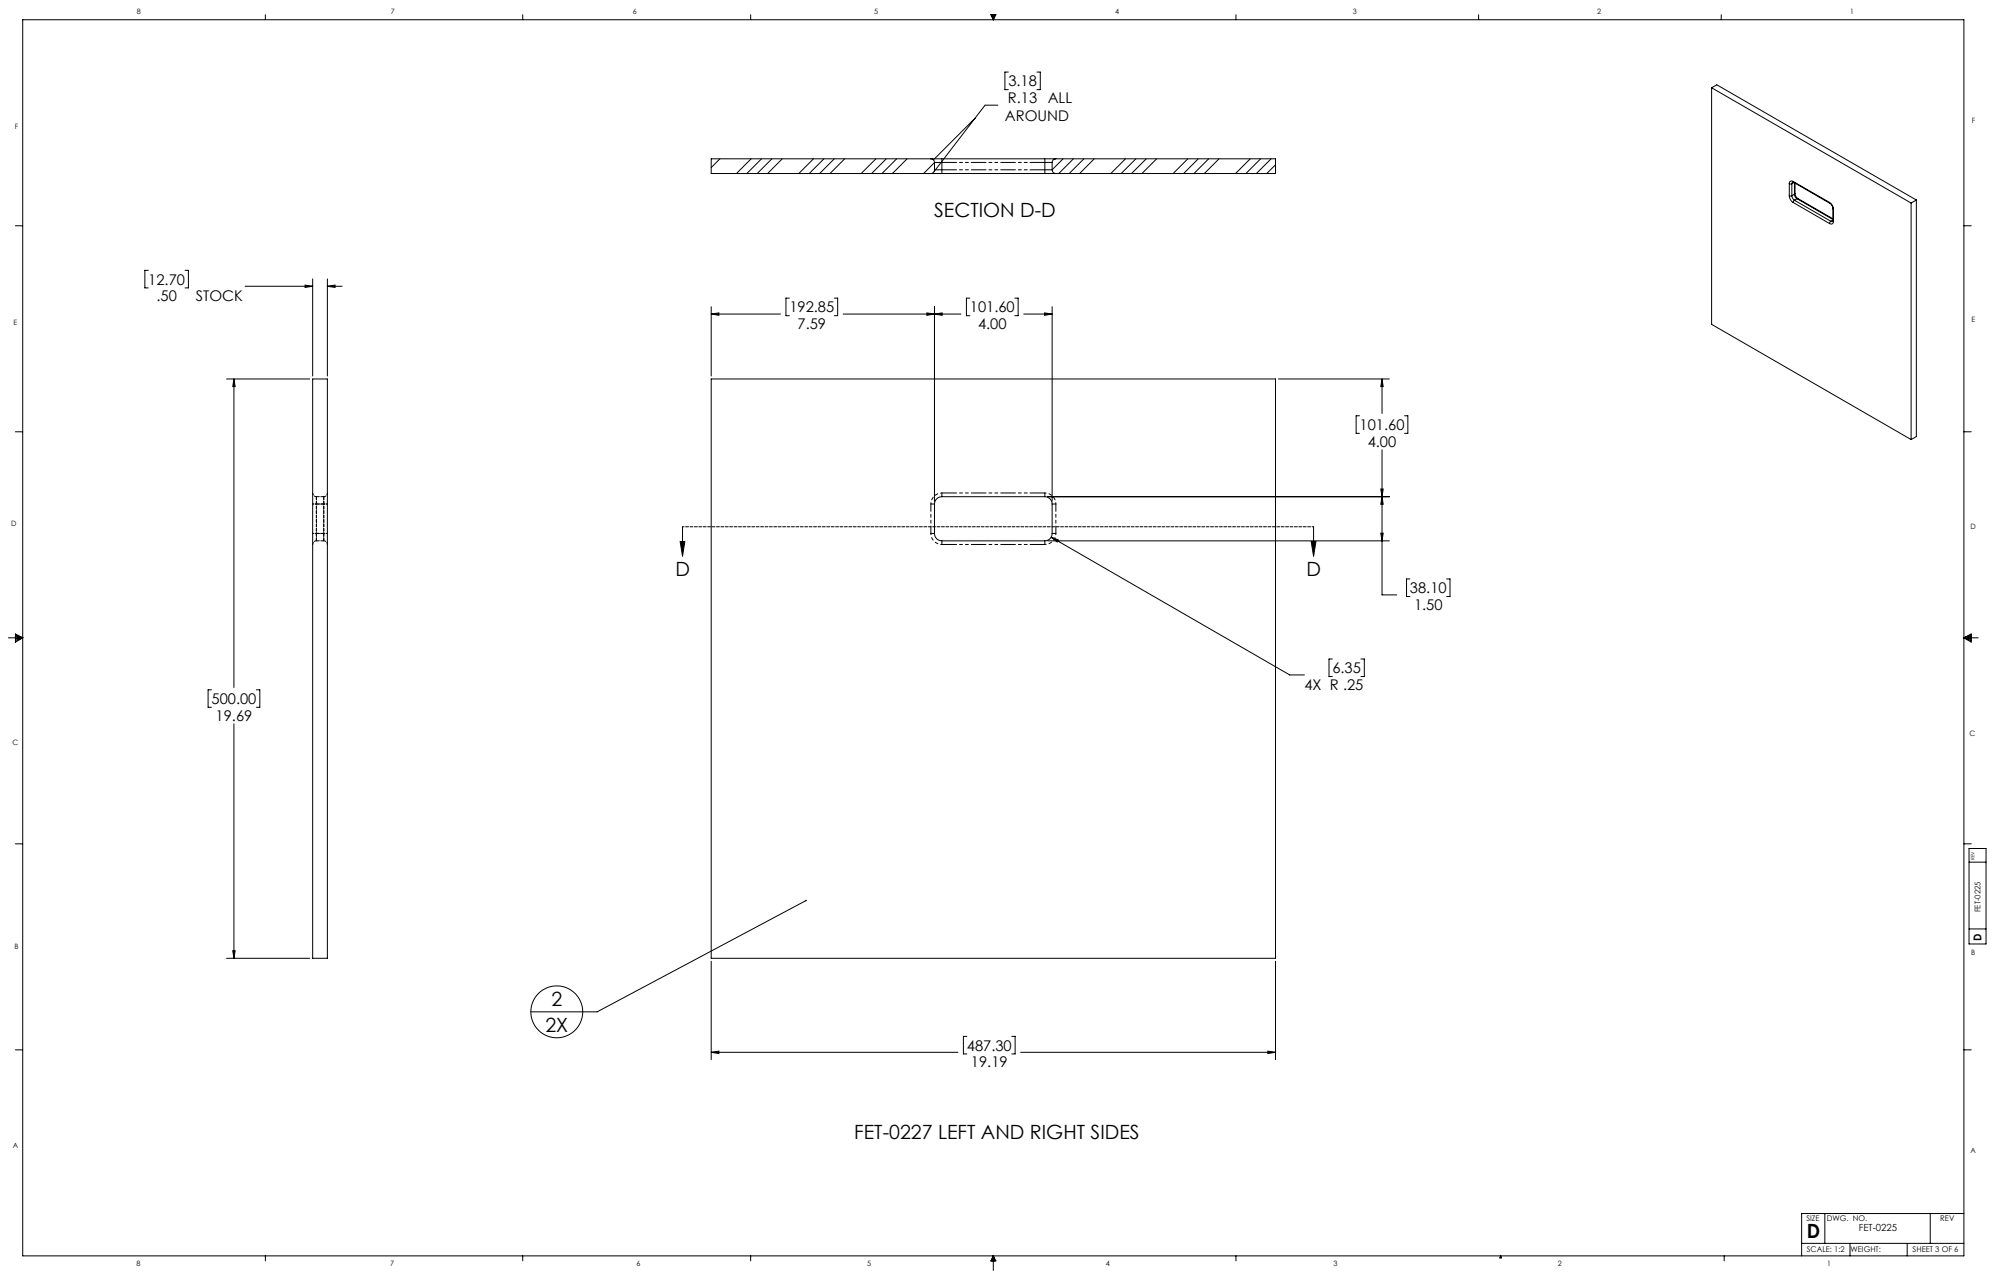
[picture p269: page 3]
.50 STOCK; R.13 ALL; SECTION D-D; FREV FET-0225; SCALE: 1:2 WEIGHT:; SHEET 3 OF 6

FET-0227 LEFT AND RIGHT SIDES

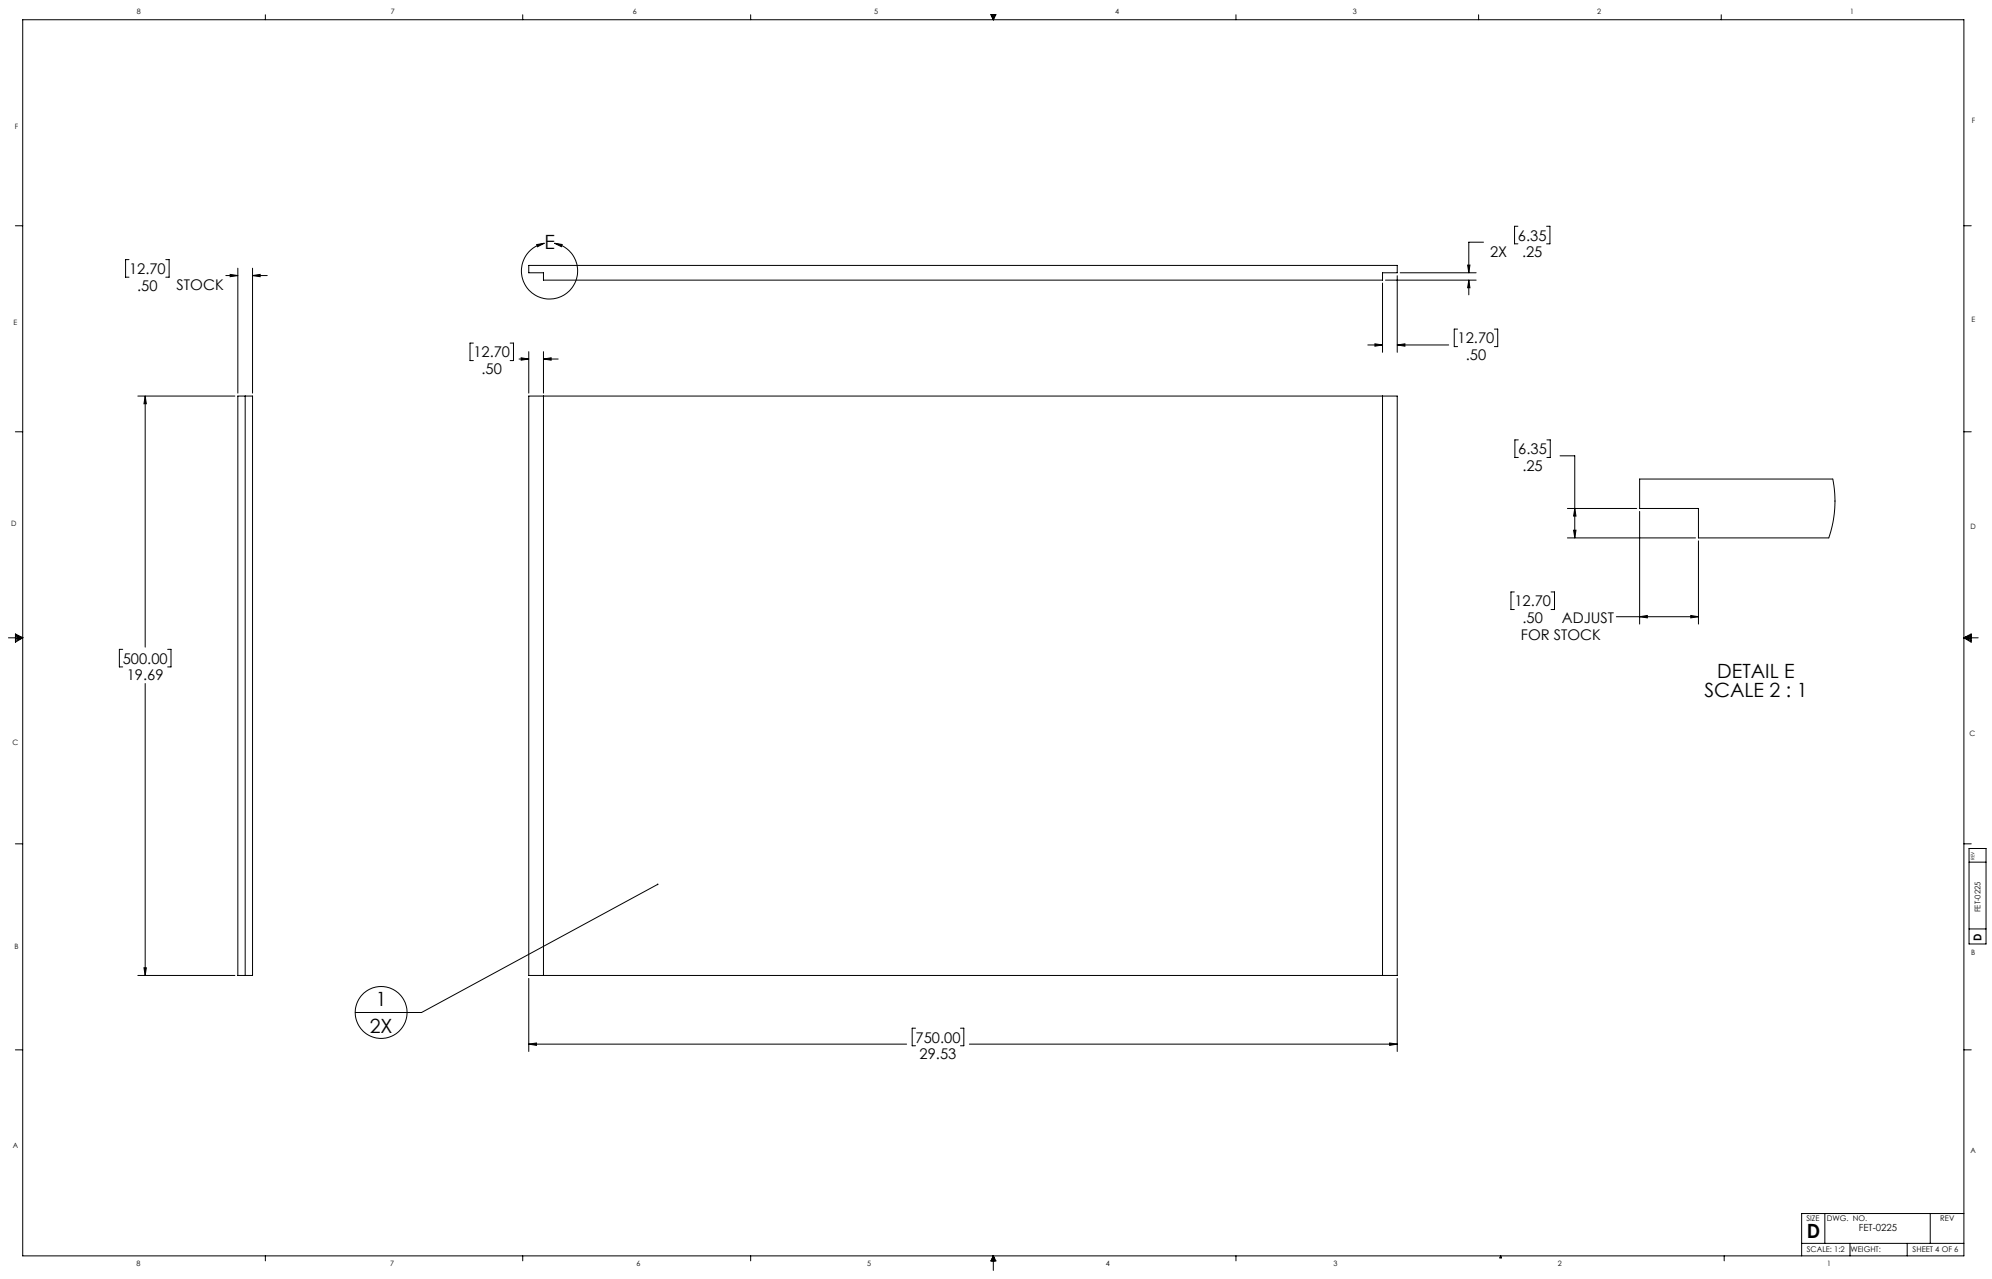
[picture p270: page 4]
.50 STOCK; .50 ADJUST FOR STOCK; DETAIL E SCALE 2 : 1; FREV FET-0225; SCALE: 1:2 WEIGHT:; SHEET 4 OF 6

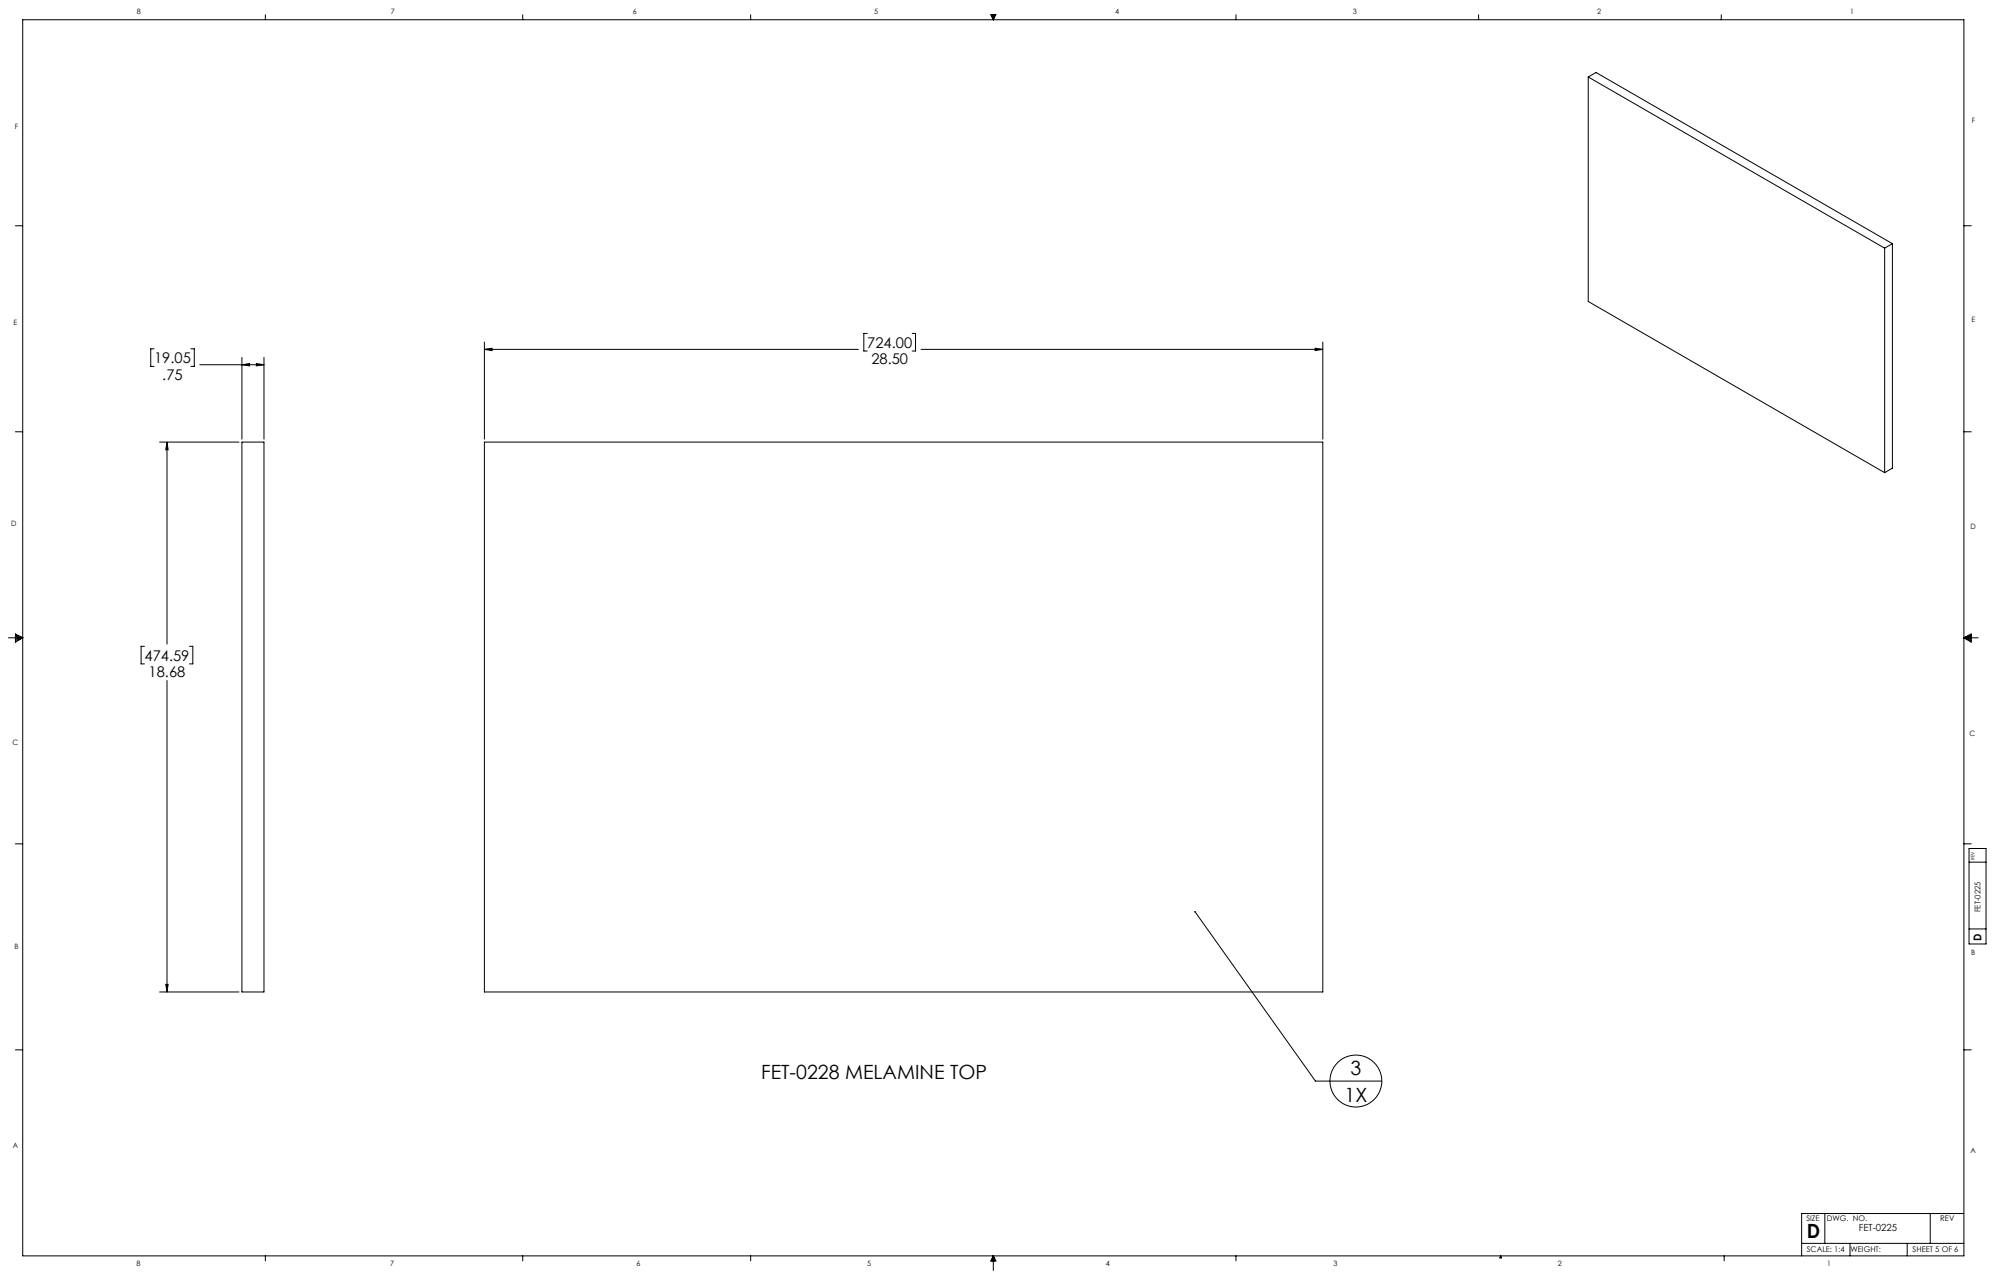
[picture p271: page 5]
FET-0228 MELAMINE TOP; FREV FET-0225; SCALE: 1:4 WEIGHT:; SHEET 5 OF 6

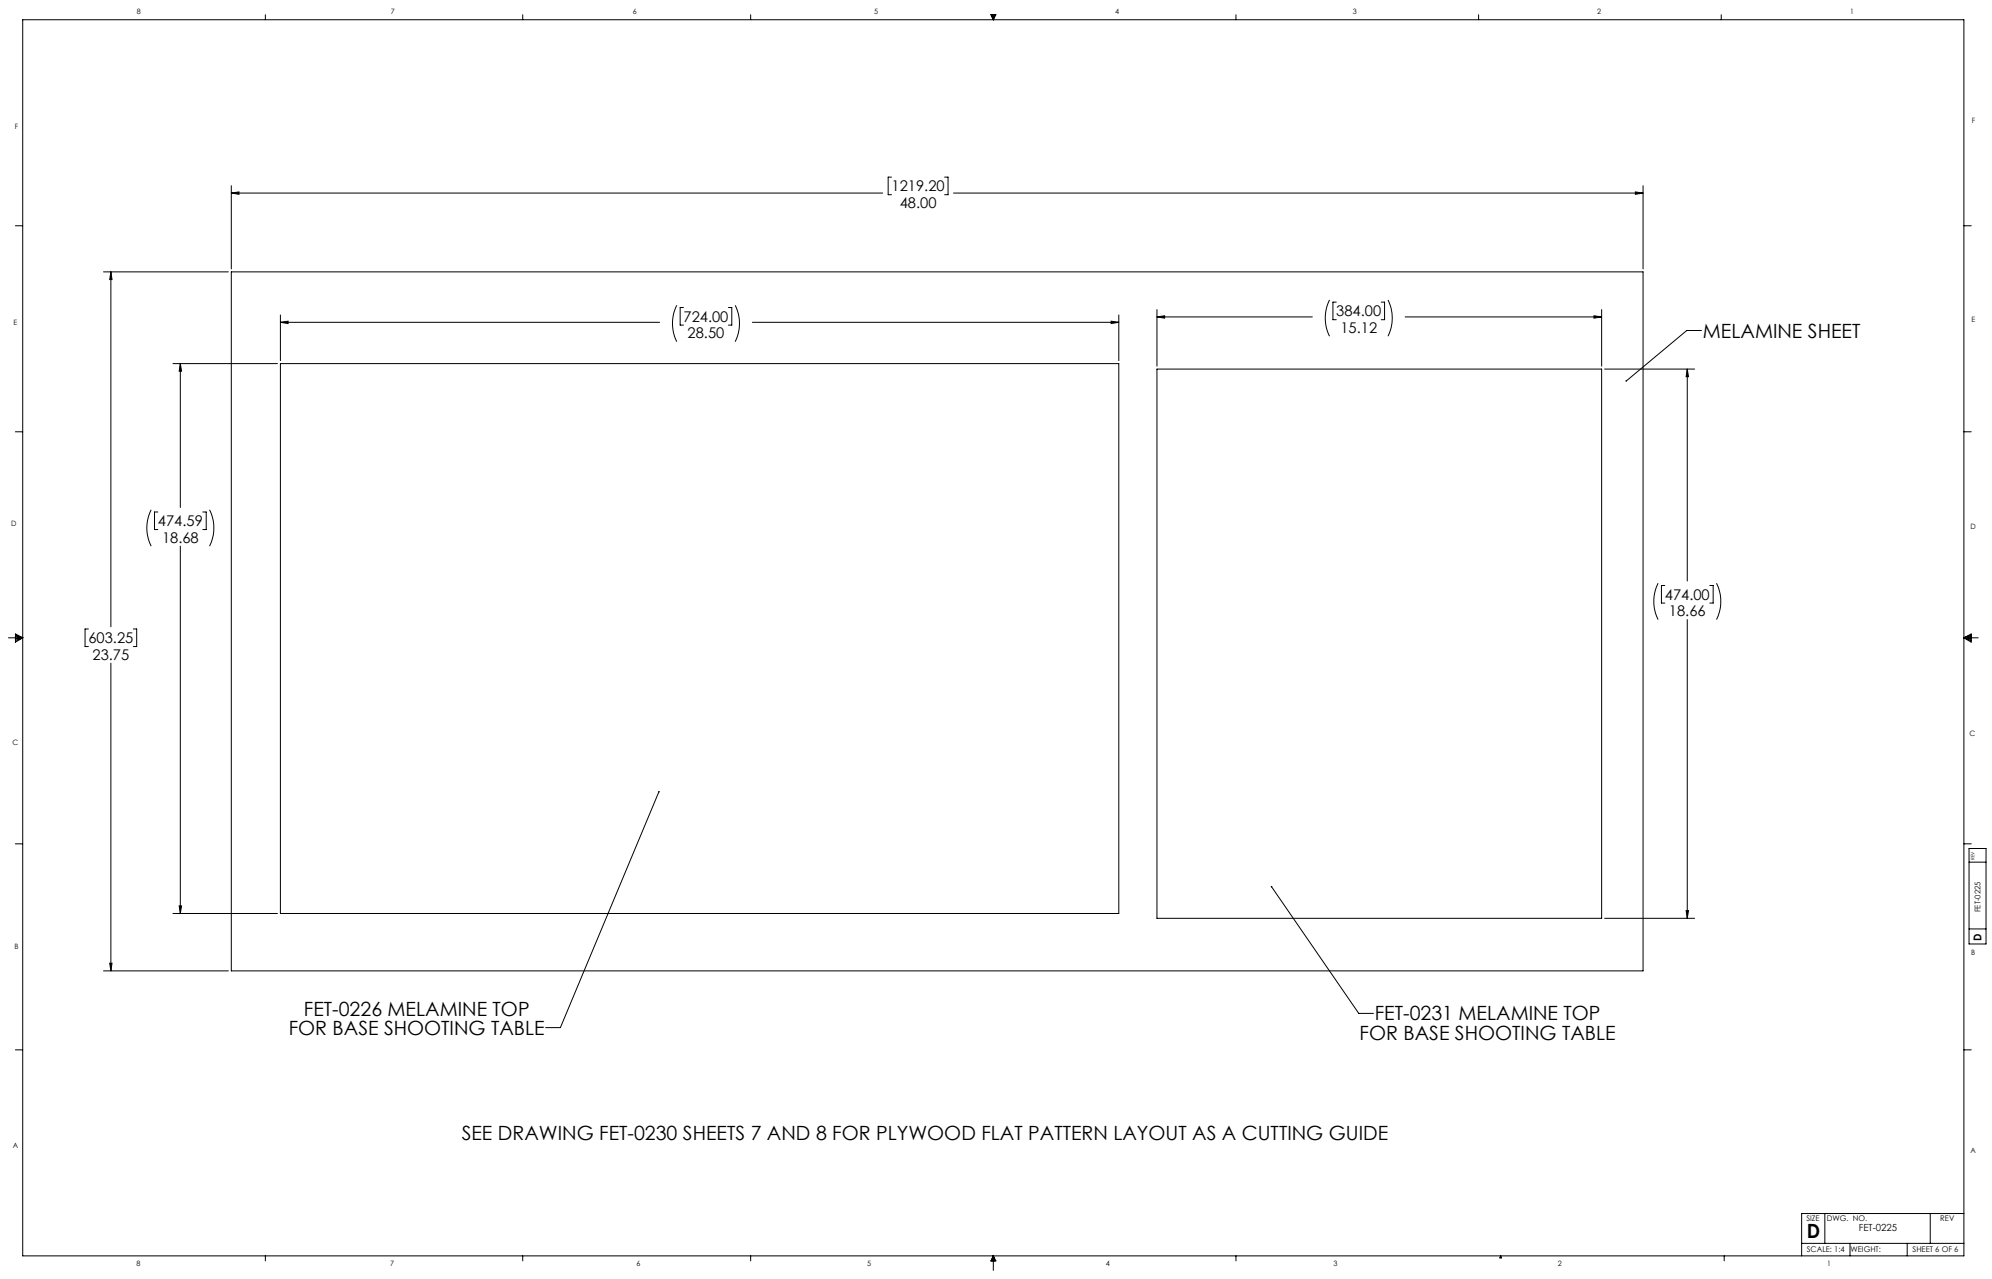
[picture p272: page 6]
MELAMINE SHEET; FOR BASE SHOOTING TABLE; FET-0231 MELAMINE TOP; FREV FET-0225; SCALE: 1:4 WEIGHT:; SHEET 6 OF 6

FET-0226 MELAMINE TOP

FOR BASE SHOOTING TABLE

SEE DRAWING FET-0230 SHEETS 7 AND 8 FOR PLYWOOD FLAT PATTERN LAYOUT AS A CUTTING GUIDE
