ten-point-nine/freETarget/Mechanical/Dimensioned Drawings/Shooting Table/FET-0230 TOP SHOOTING TABLE ASSEMBLY.PDF

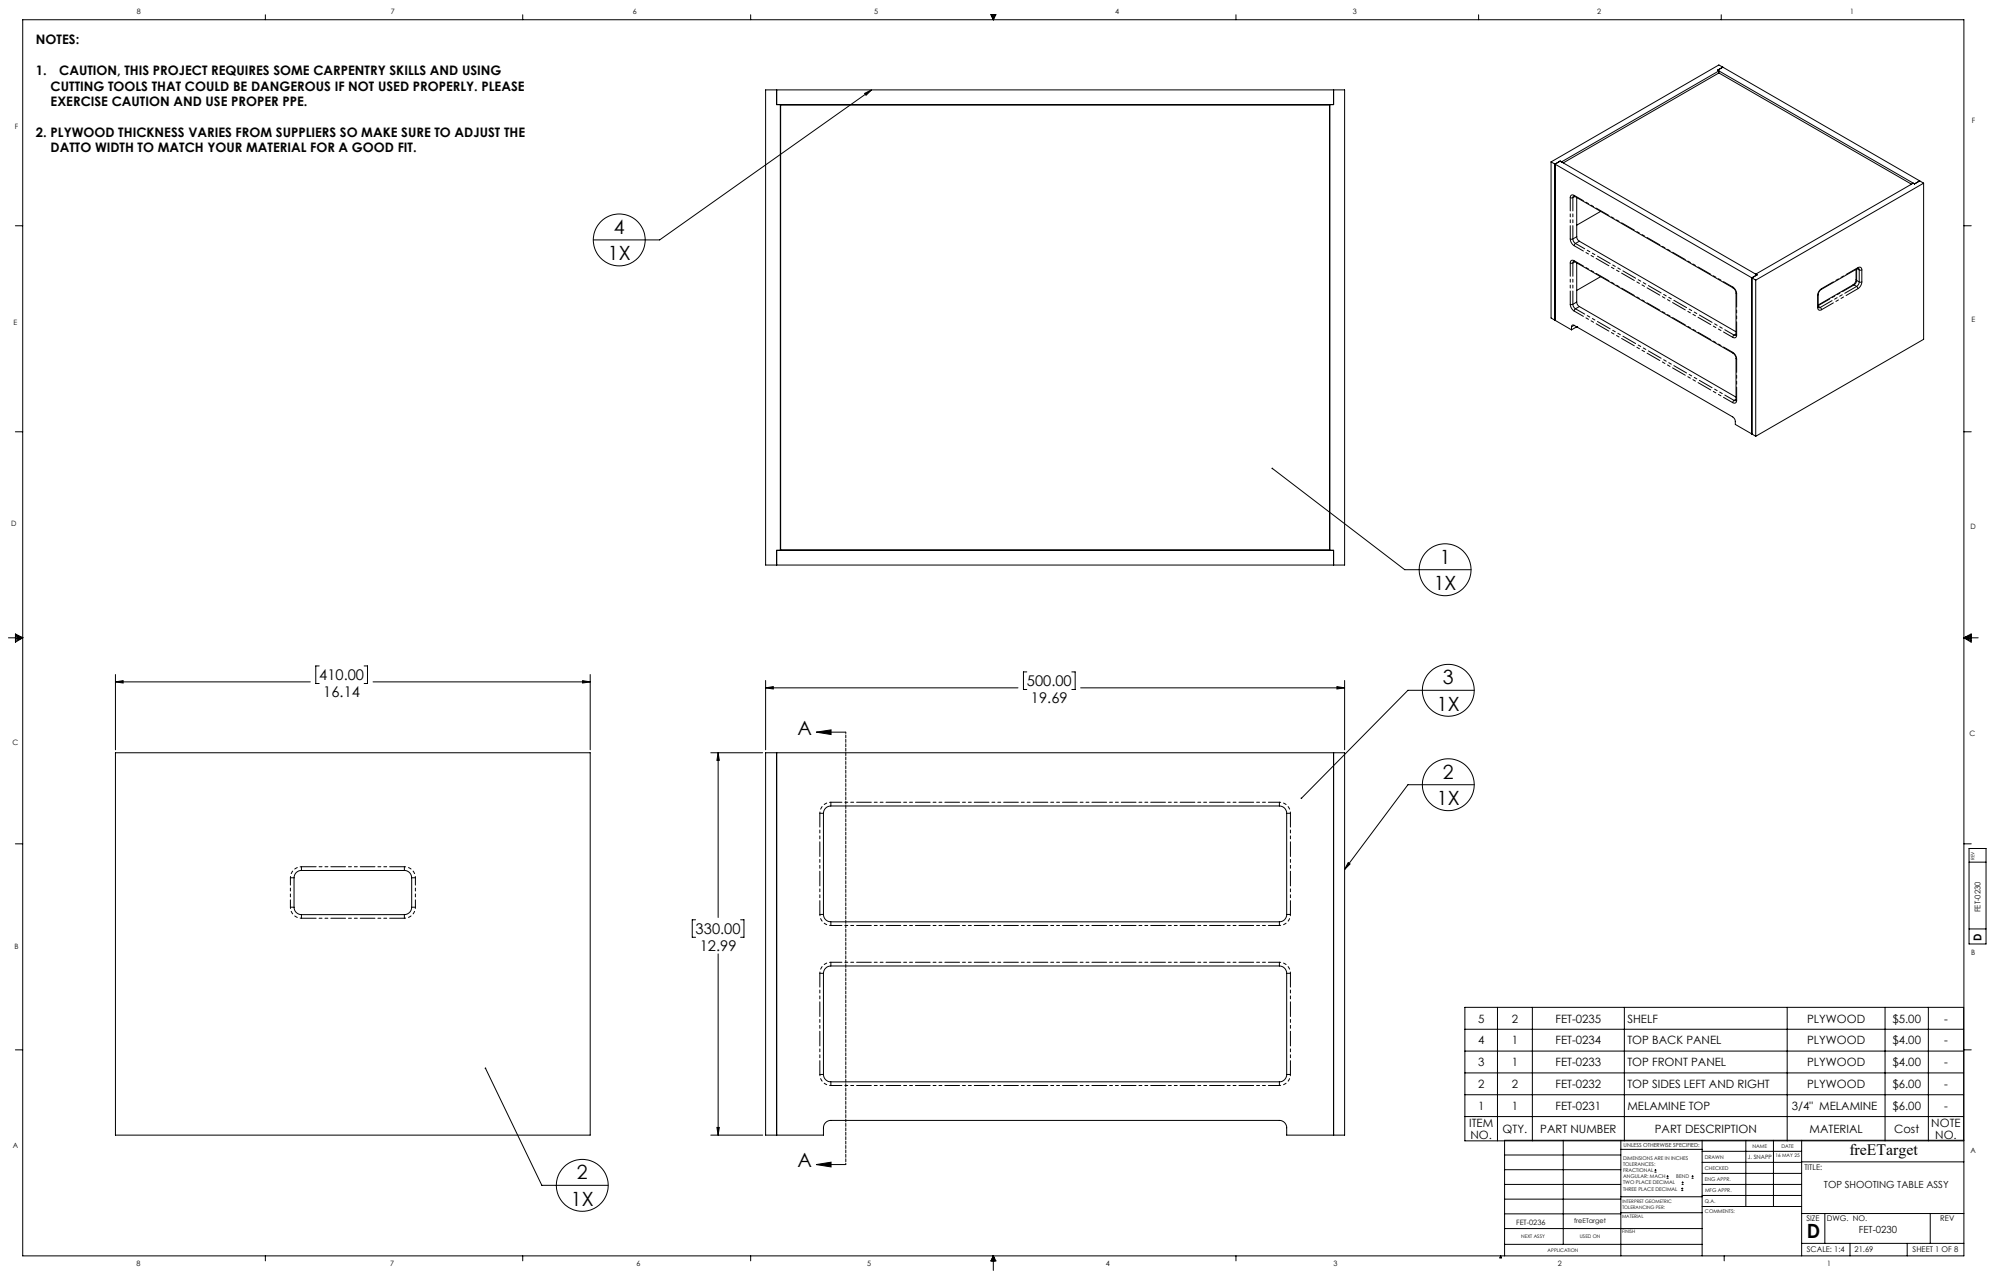
[picture p273: page 1]
FREV FET-0230; SHEET 1 OF 8; J. SNAPP 16 MAY 25; SCALE: 1:4 21.69; DWG. NO.; REV; freETarget NAME; DATE; MFG APPR.; ENG APPR.; INTERPRET GEOMETRIC TOLERANCING PER:; ANGULAR: MACH; BEND; NEXT ASSY; USED ON

NOTES:
1. CAUTION, THIS PROJECT REQUIRES SOME CARPENTRY SKILLS AND USING
CUTTING TOOLS THAT COULD BE DANGEROUS IF NOT USED PROPERLY. PLEASE
EXERCISE CAUTION AND USE PROPER PPE.
2. PLYWOOD THICKNESS VARIES FROM SUPPLIERS SO MAKE SURE TO ADJUST THE
DATTO WIDTH TO MATCH YOUR MATERIAL FOR A GOOD FIT.

5 | 2 | FET-0235 | SHELF | PLYWOOD | $5.00 | -
4 | 1 | FET-0234 | TOP BACK PANEL | PLYWOOD | $4.00 | -
3 | 1 | FET-0233 | TOP FRONT PANEL | PLYWOOD | $4.00 | -
2 | 2 | FET-0232 | TOP SIDES LEFT AND RIGHT | PLYWOOD | $6.00 | -
1 | 1 | FET-0231 | MELAMINE TOP | 3/4" MELAMINE | $6.00 | -
ITEM NO. | QTY. | PART NUMBER | PART DESCRIPTION | MATERIAL | Cost | NOTE NO.

UNLESS OTHERWISE SPECIFIED:

DIMENSIONS ARE IN INCHES
TOLERANCES:
FRACTIONAL
TWO PLACE DECIMAL
THREE PLACE DECIMAL

TITLE:
TOP SHOOTING TABLE ASSY

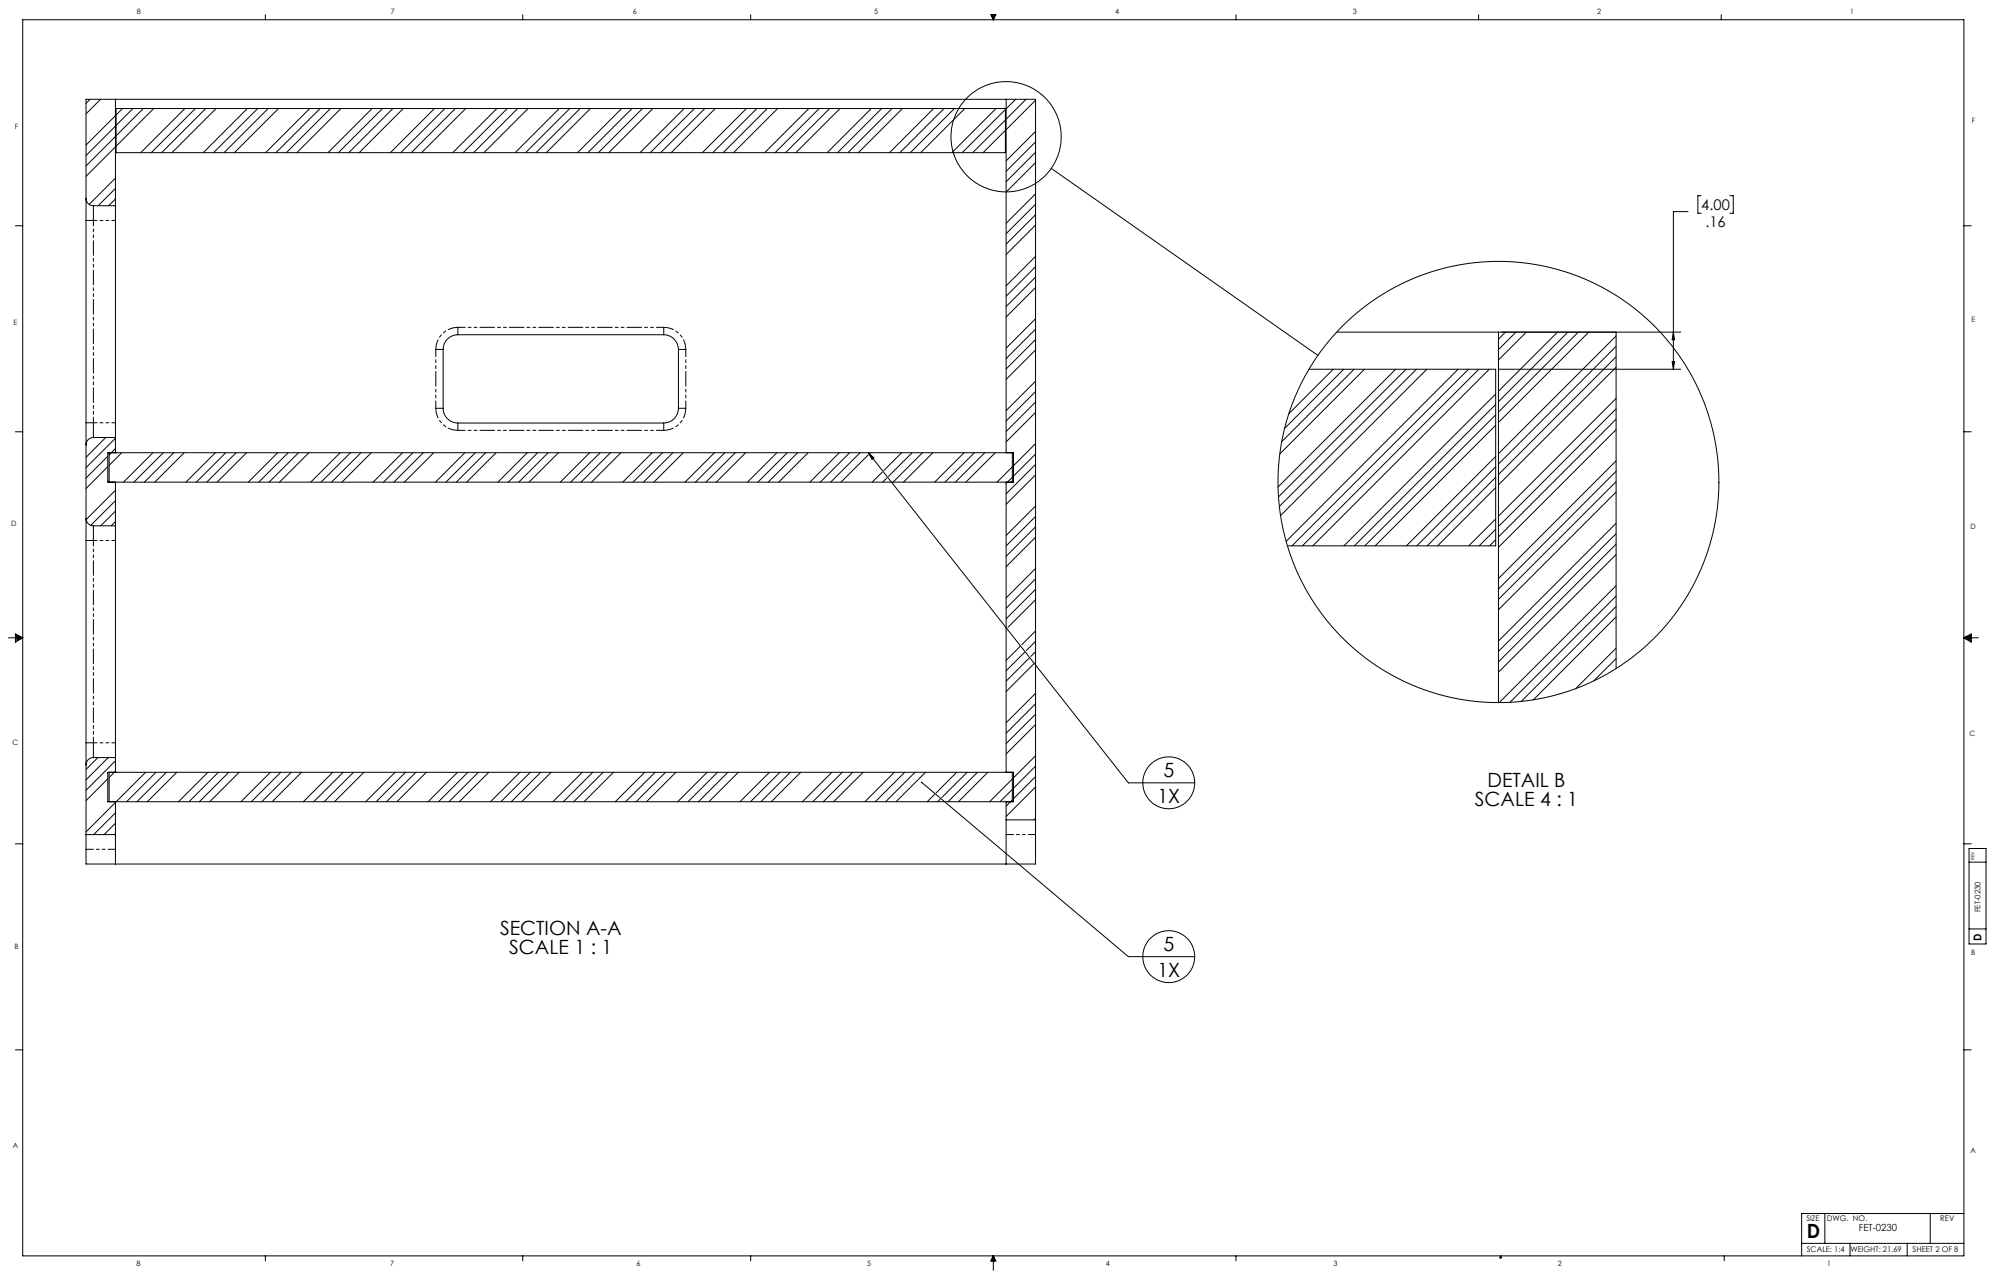
[picture p274: page 2]
SECTION A-A SCALE 1 : 1; DETAIL B SCALE 4 : 1; FREV FET-0230

SCALE: 1:4 WEIGHT: 21.69 SHEET 2 OF 8

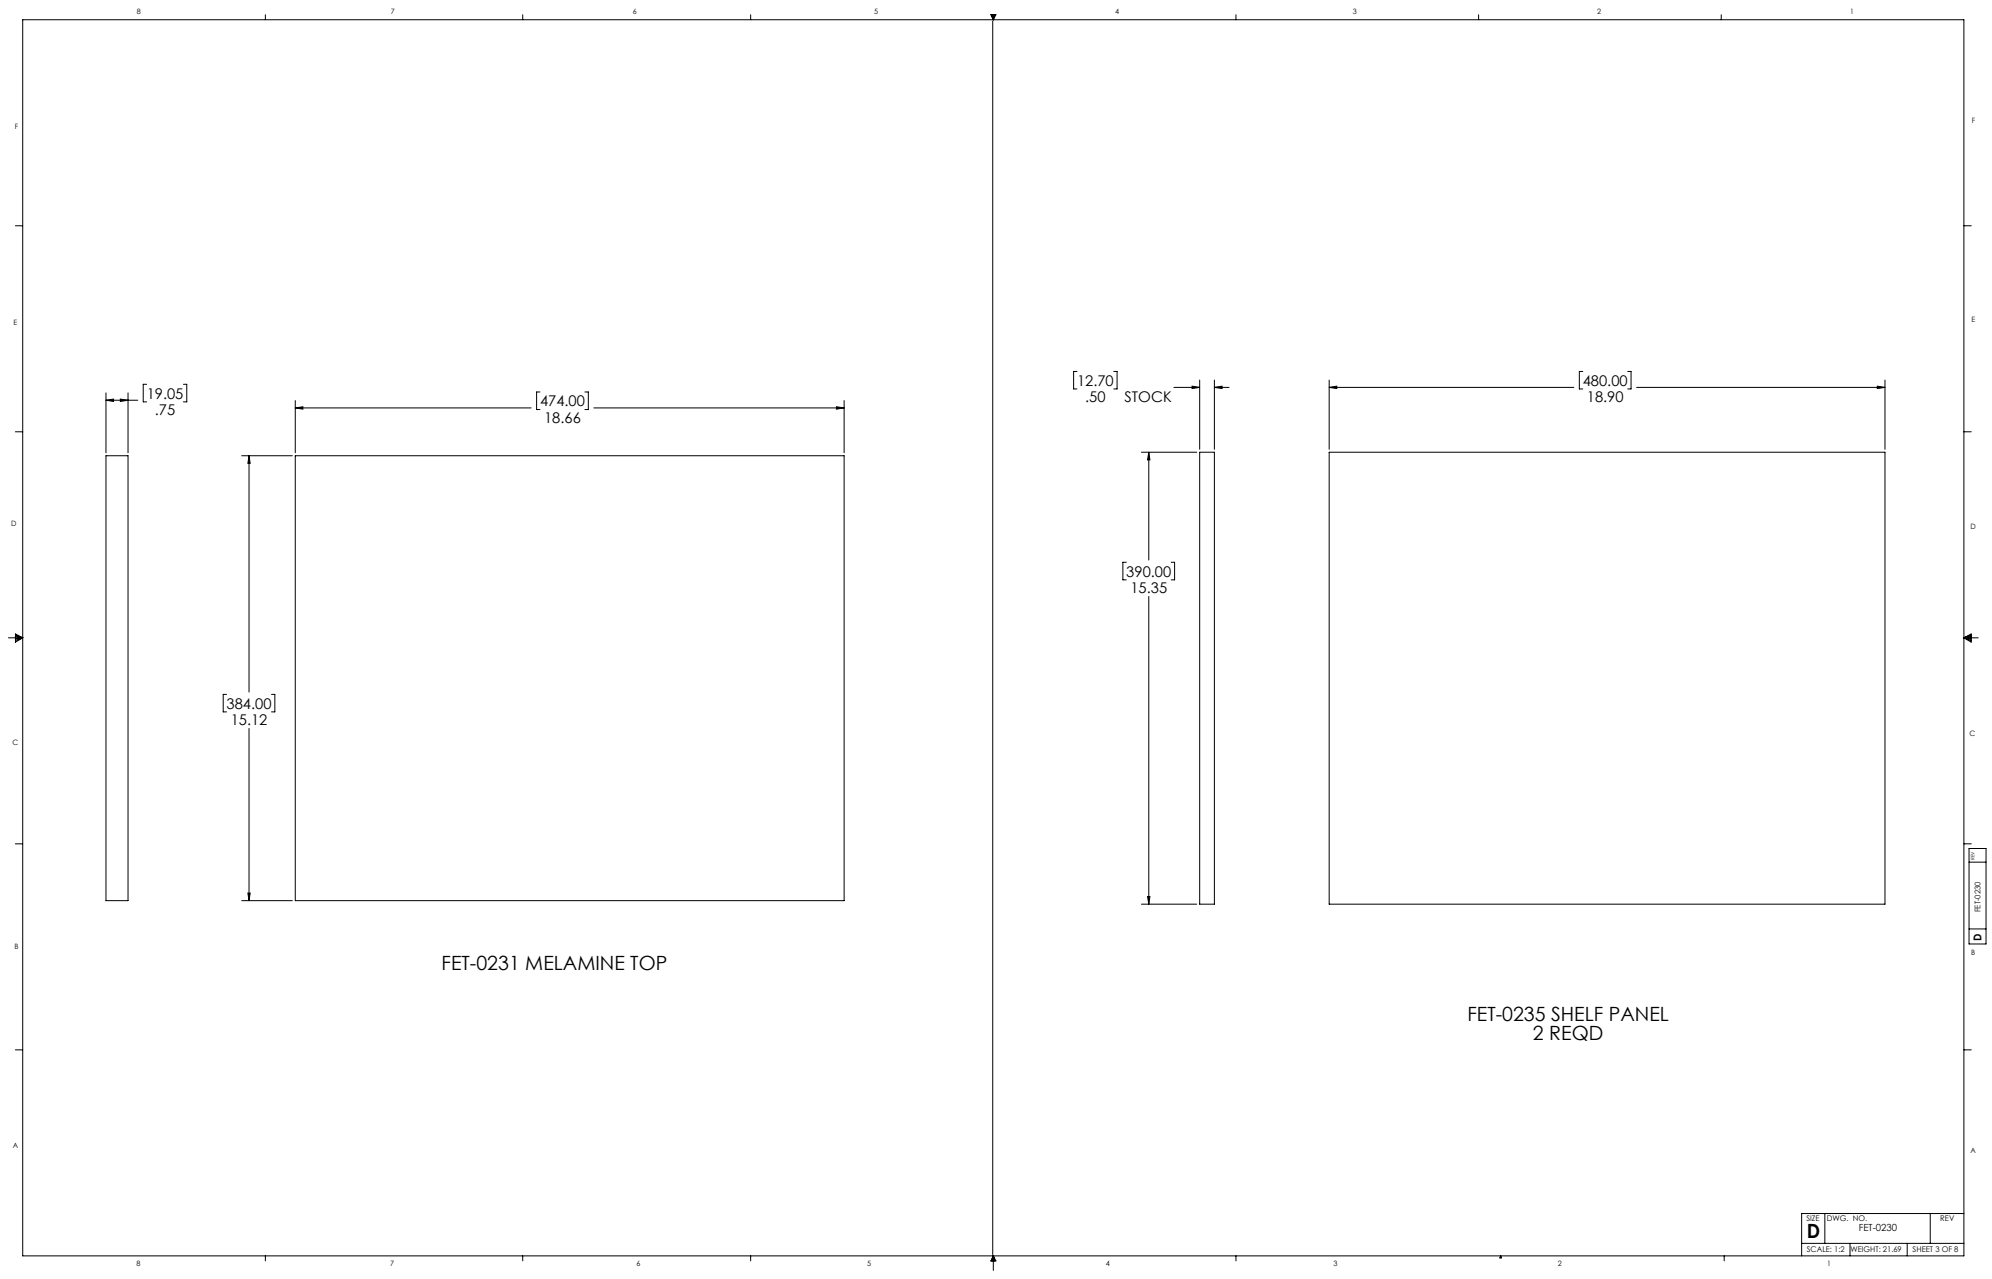
[picture p275: page 3]
.50 STOCK; FREV FET-0230

FET-0231 MELAMINE TOP

FET-0235 SHELF PANEL
2 REQD

SCALE: 1:2 WEIGHT: 21.69 SHEET 3 OF 8

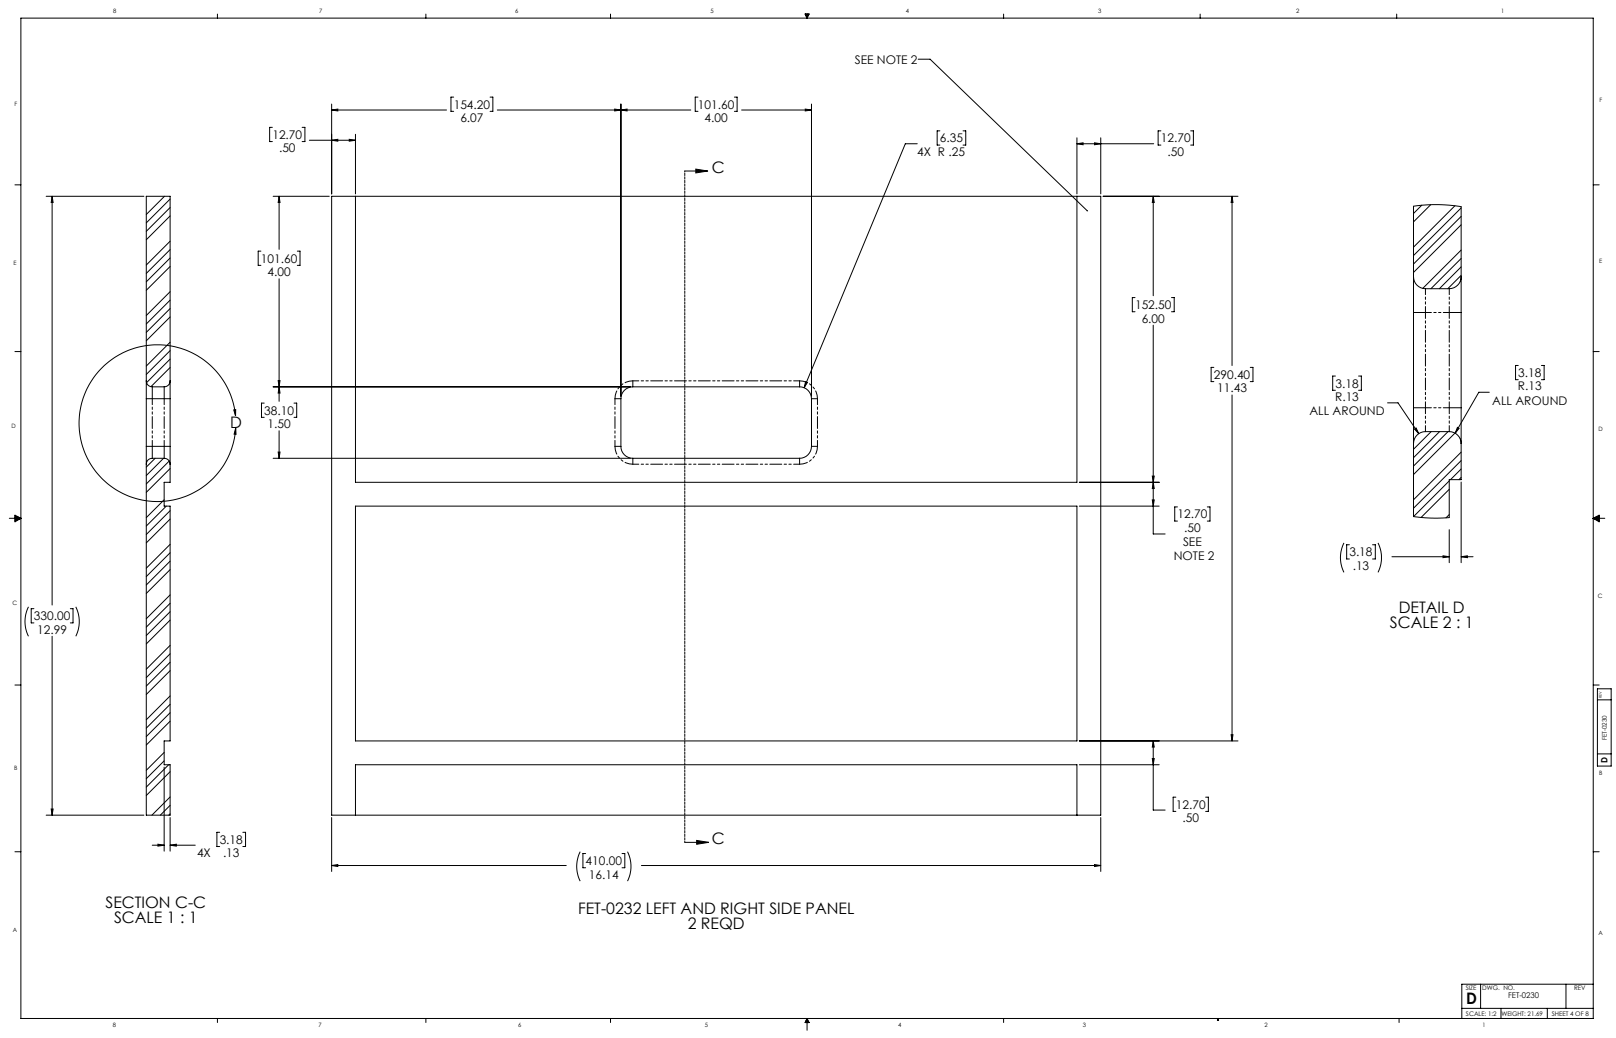
[picture p276: page 4]
NOTE 2; 2 REQD; SEE NOTE 2; SECTION C-C SCALE 1 : 1; ALL AROUND; DETAIL D SCALE 2 : 1; FREV FET-0230

FET-0232 LEFT AND RIGHT SIDE PANEL

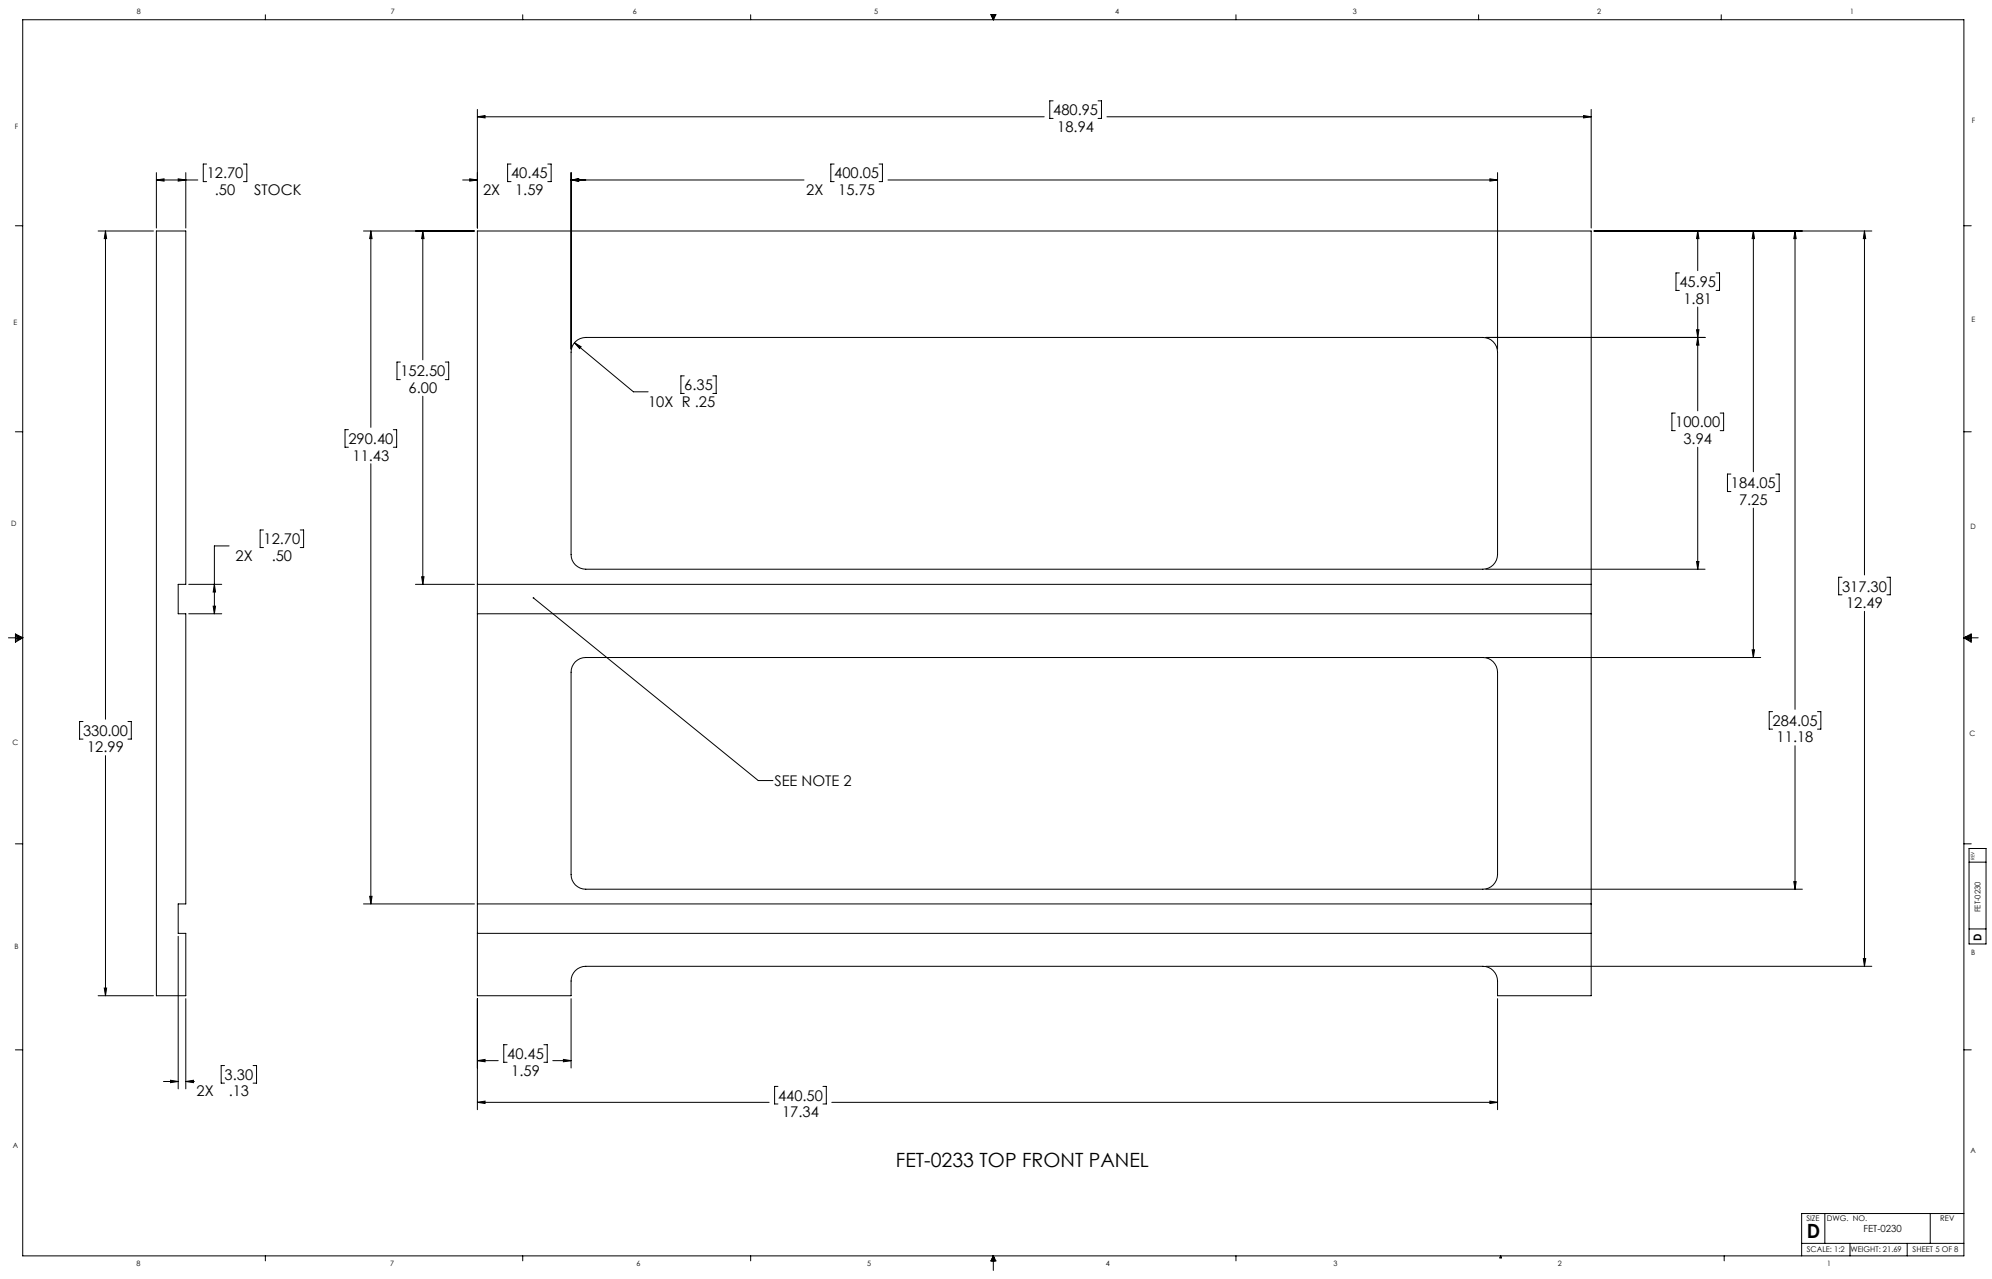
[picture p277: page 5]
SEE NOTE 2; .50 STOCK; FREV FET-0230

FET-0233 TOP FRONT PANEL

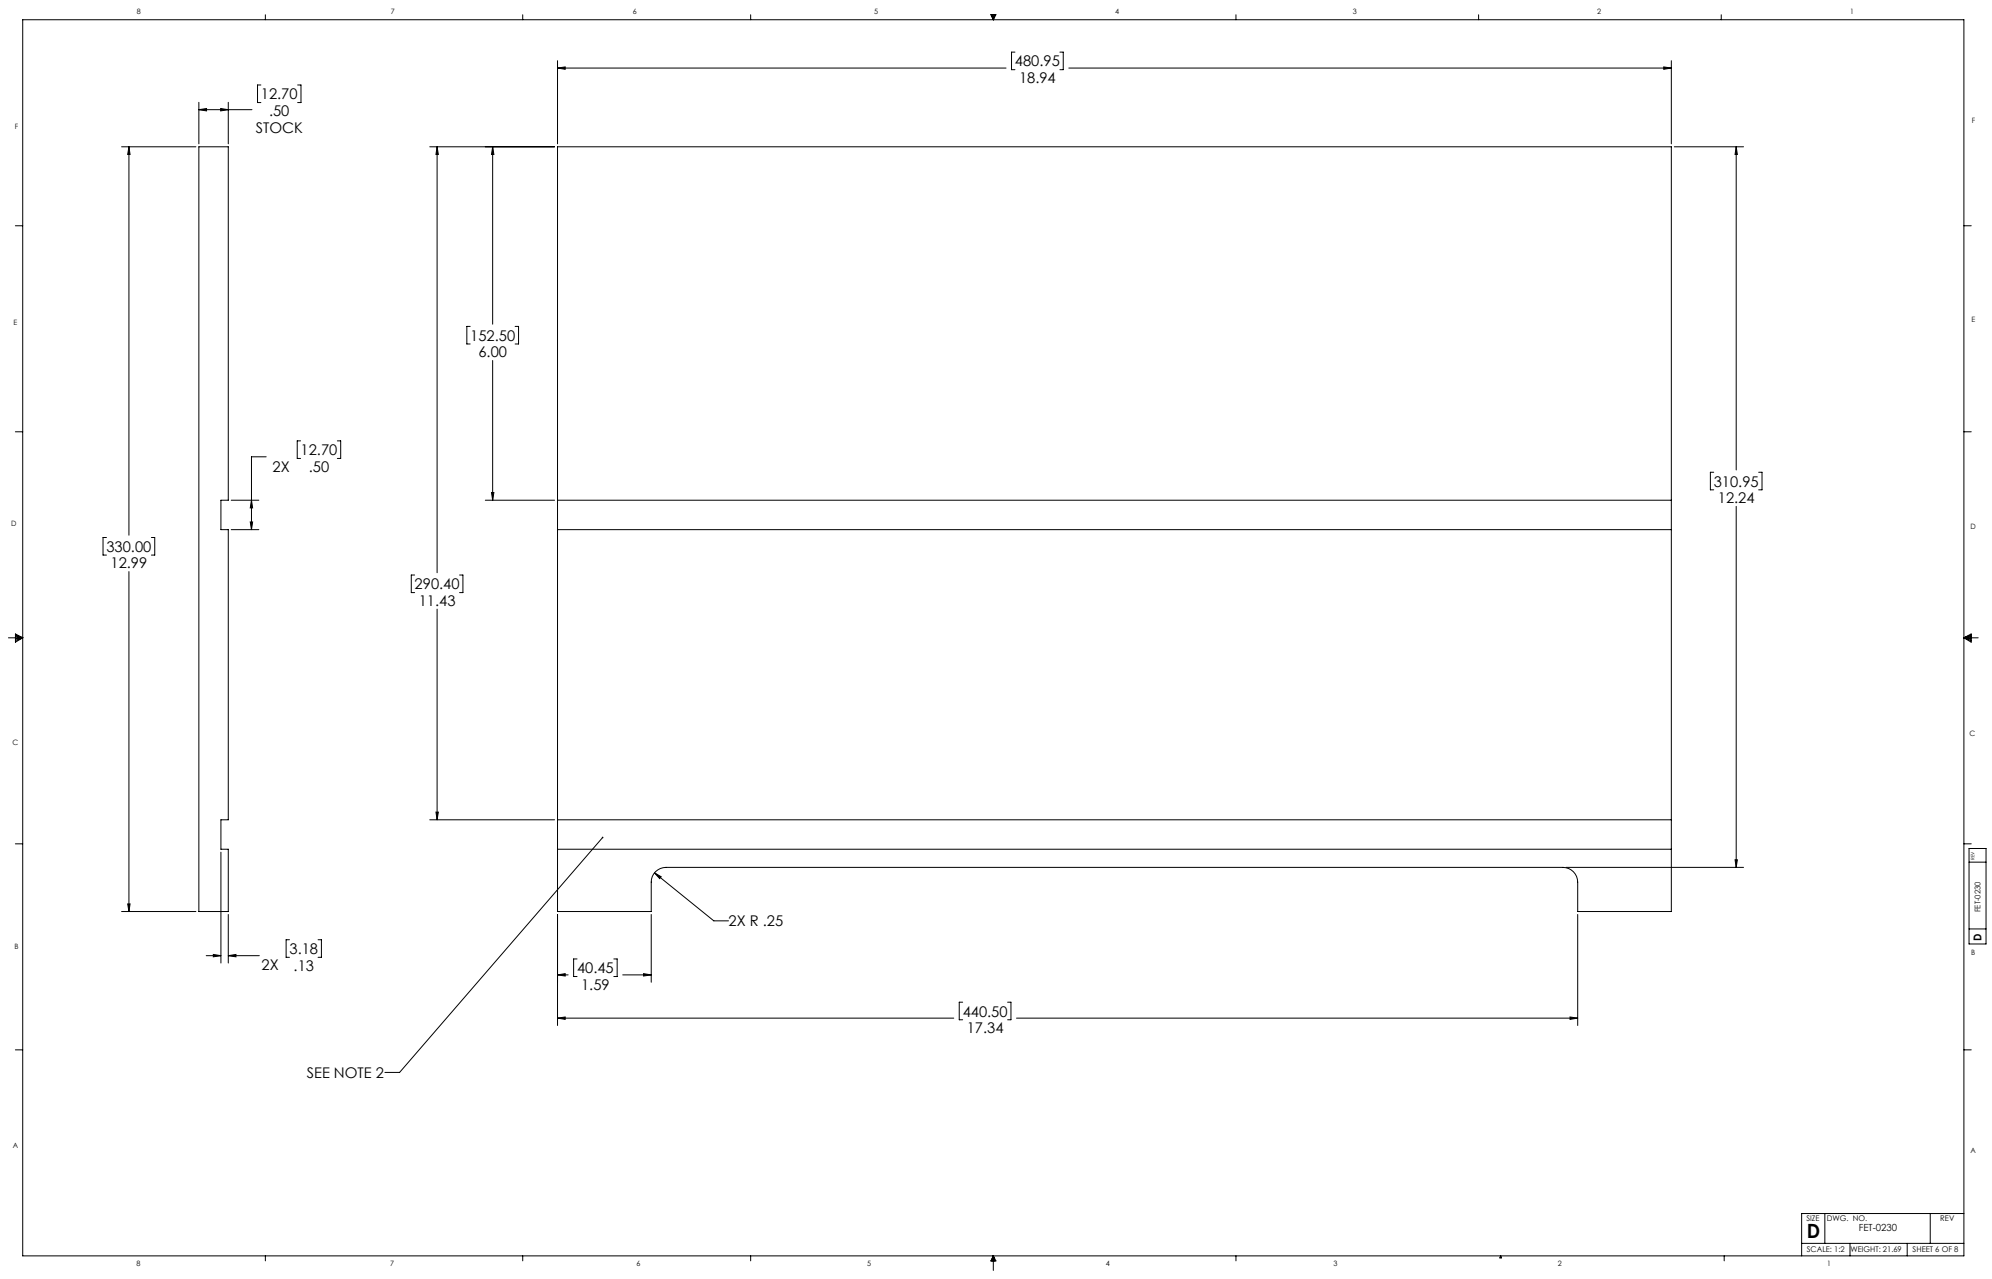
[picture p278: page 6]
SEE NOTE 2; FREV FET-0230

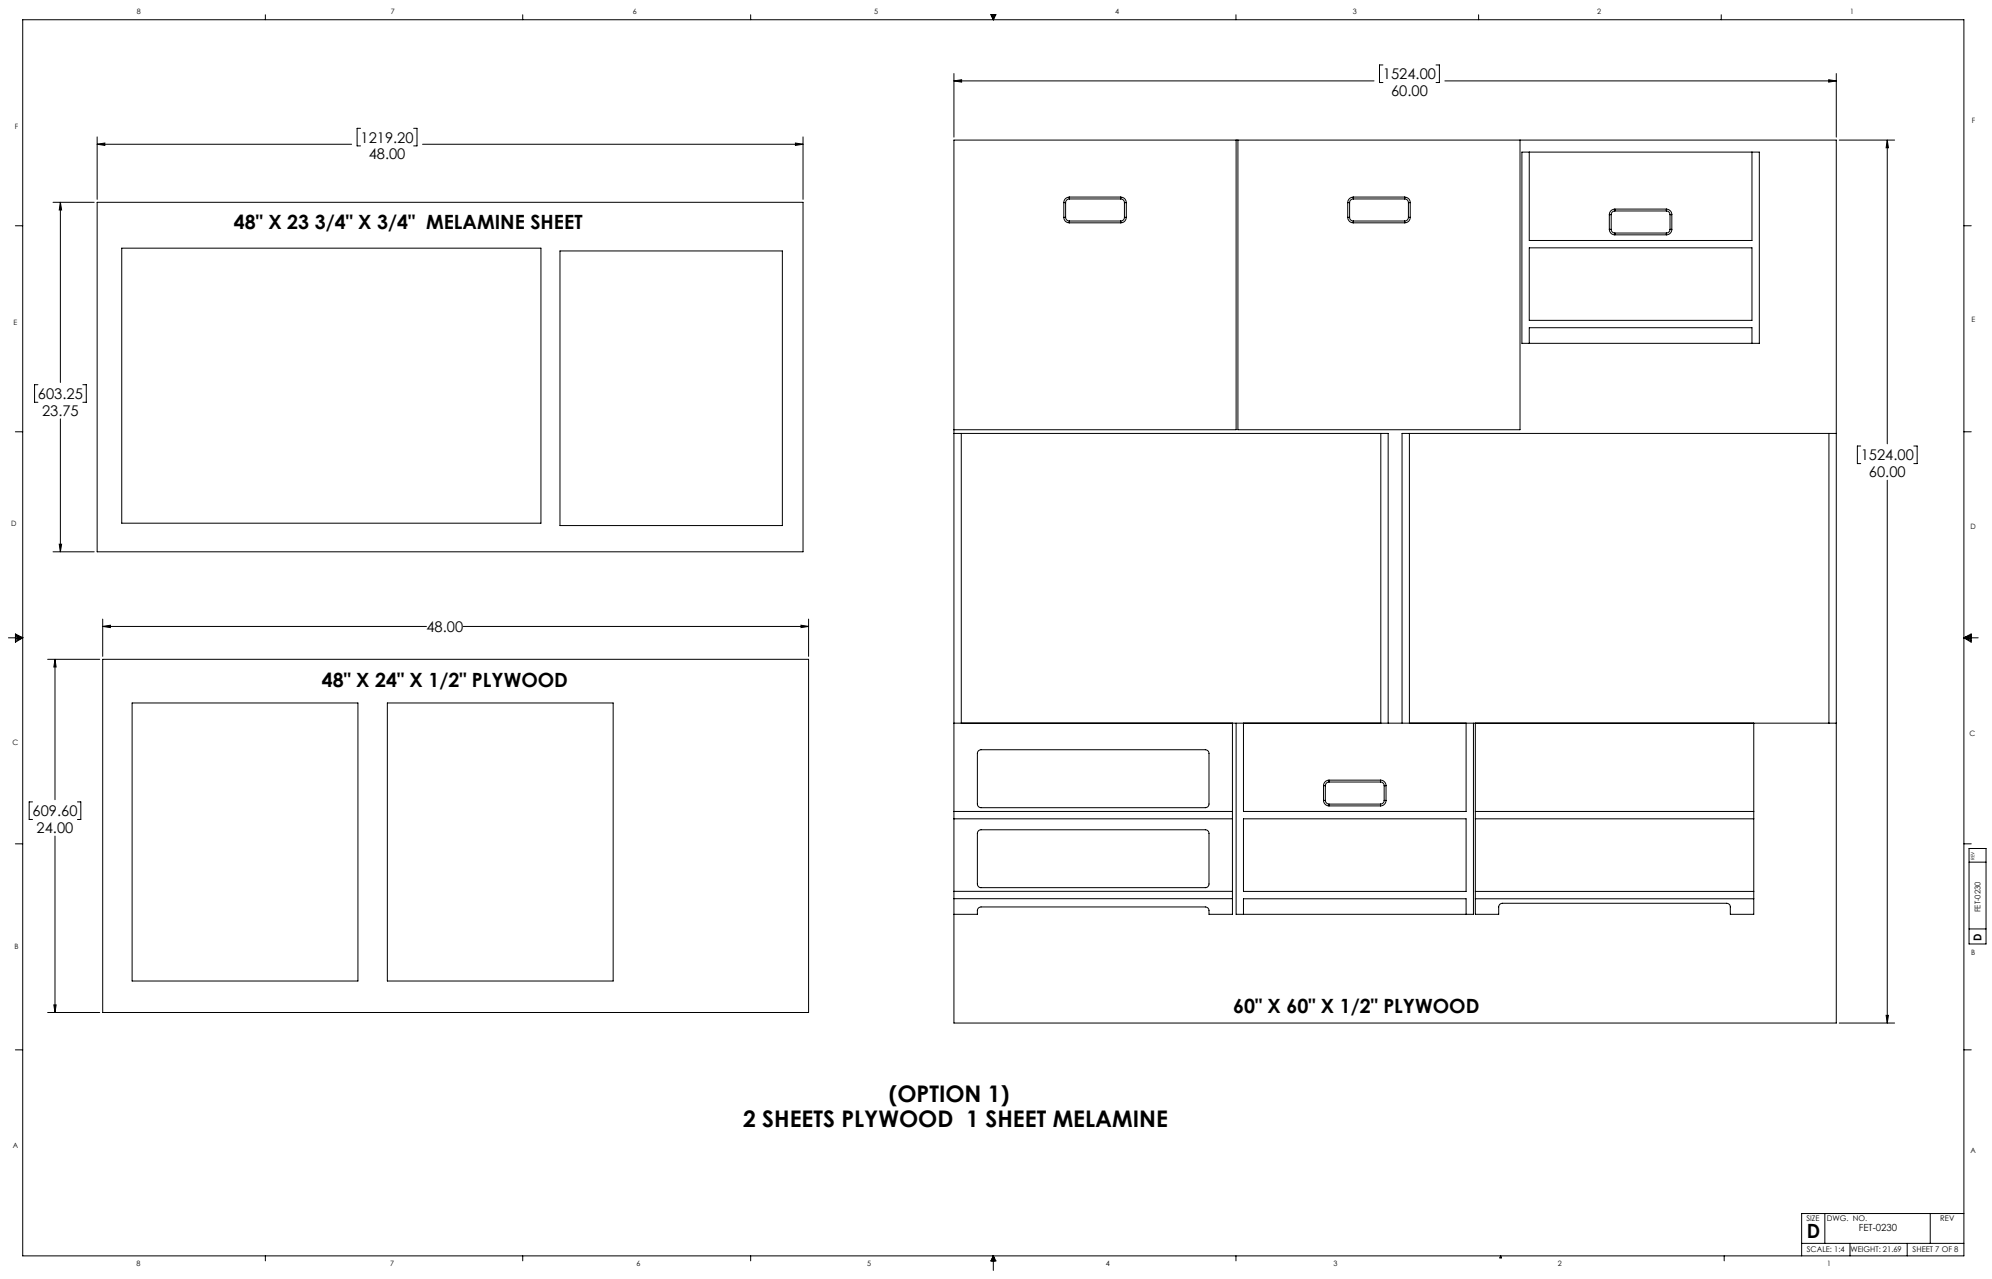
[picture p279: page 7]
48" X 23 3/4" X 3/4" MELAMINE SHEET; 60" X 60" X 1/2" PLYWOOD; 48" X 24" X 1/2" PLYWOOD; (OPTION 1); FREV FET-0230

2 SHEETS PLYWOOD 1 SHEET MELAMINE

SCALE: 1:4 WEIGHT: 21.69 SHEET 7 OF 8

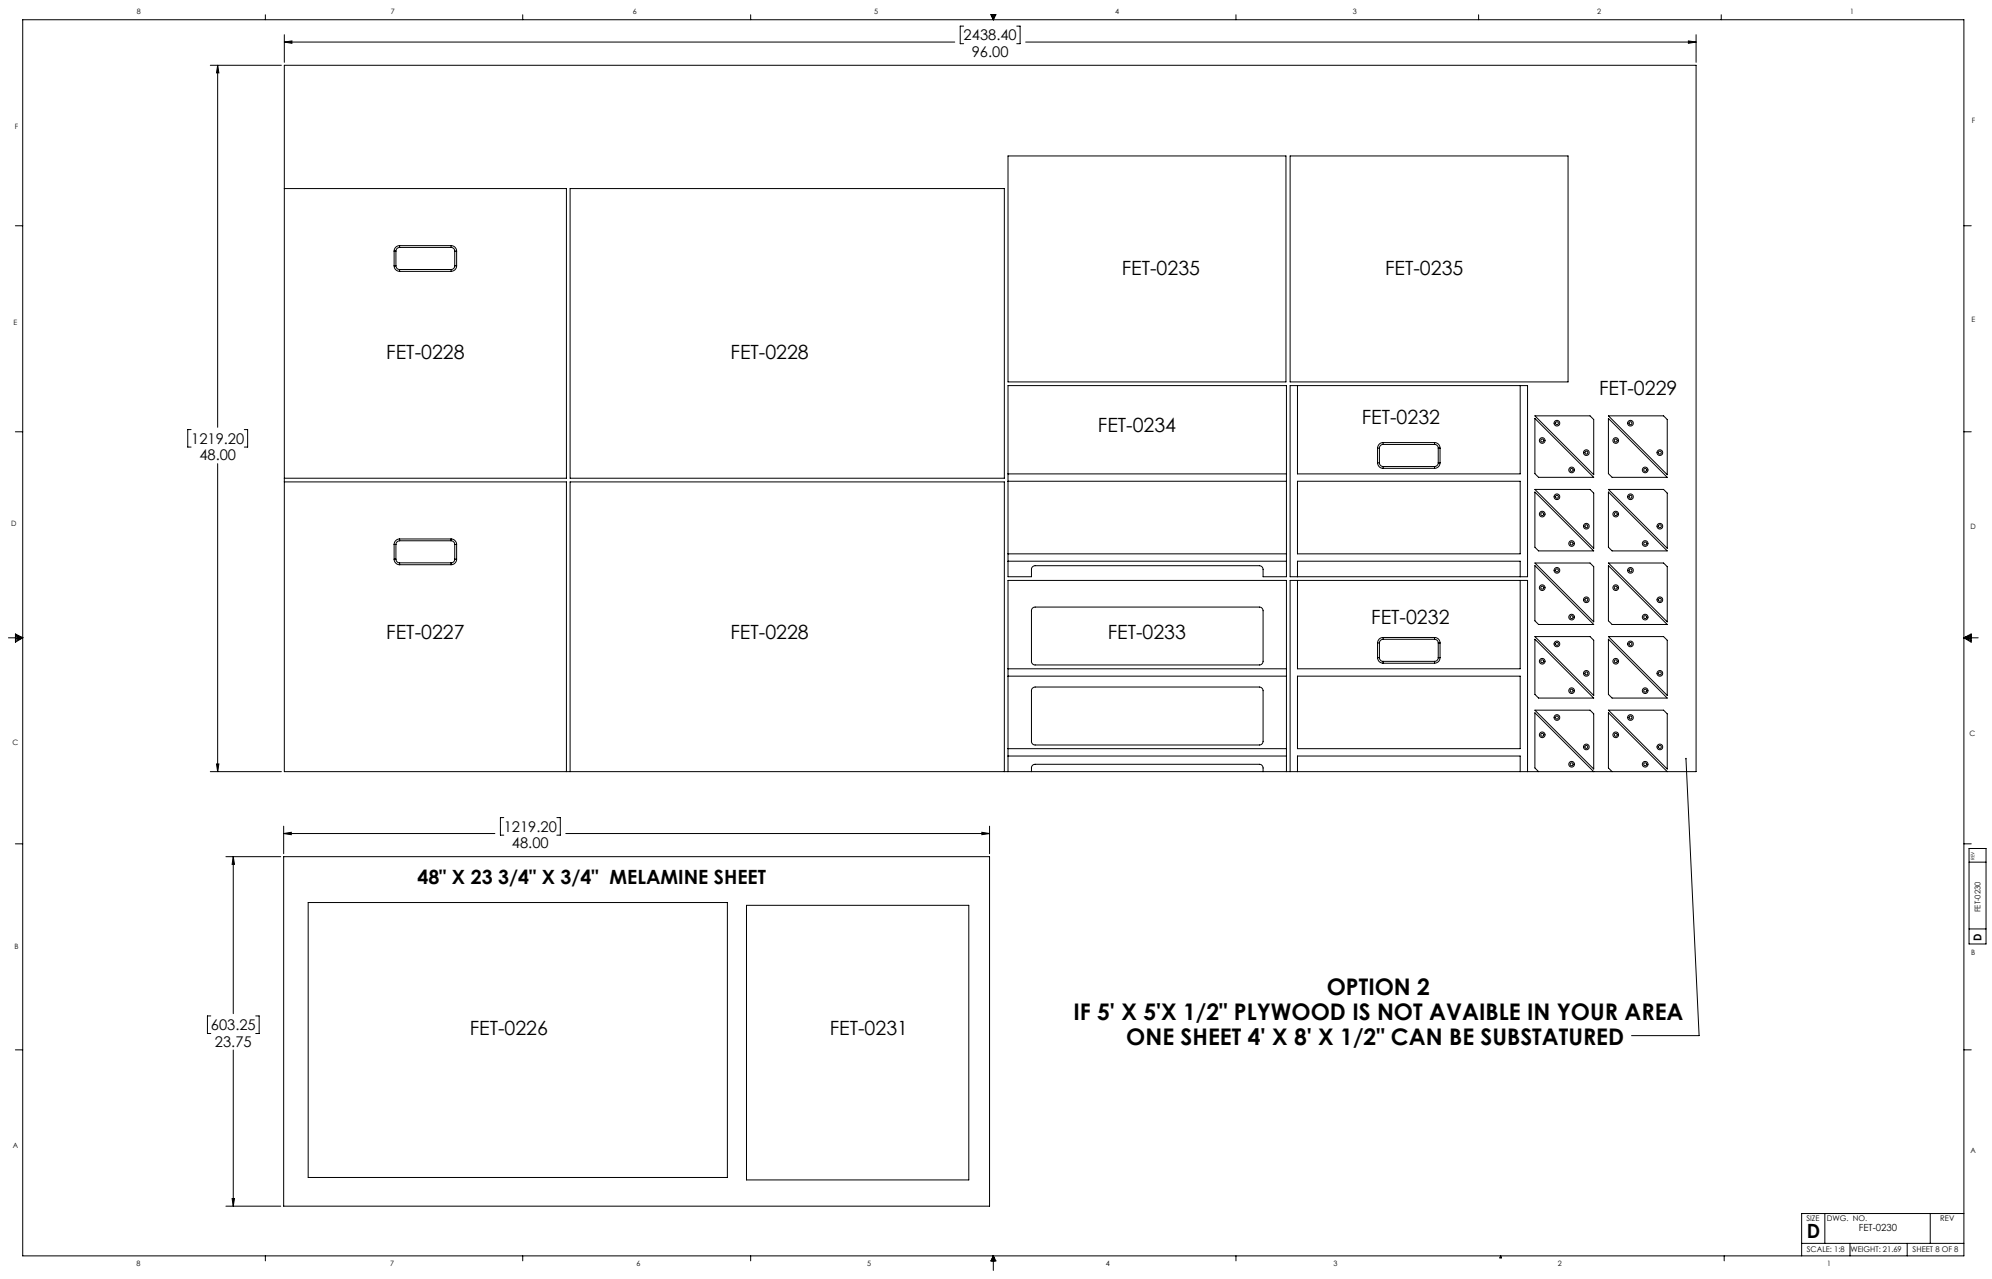
[picture p280: page 8]
OPTION 2; 48" X 23 3/4" X 3/4" MELAMINE SHEET; FREV FET-0230

IF 5' X 5'X 1/2" PLYWOOD IS NOT AVAIBLE IN YOUR AREA

ONE SHEET 4' X 8' X 1/2" CAN BE SUBSTATURED 603.25

SCALE: 1:8 WEIGHT: 21.69 SHEET 8 OF 8
