ten-point-nine/freETarget/Mechanical/Dimensioned Drawings/50m Pistol Target/FET-0201  FRAME FRONT CLAMP.PDF

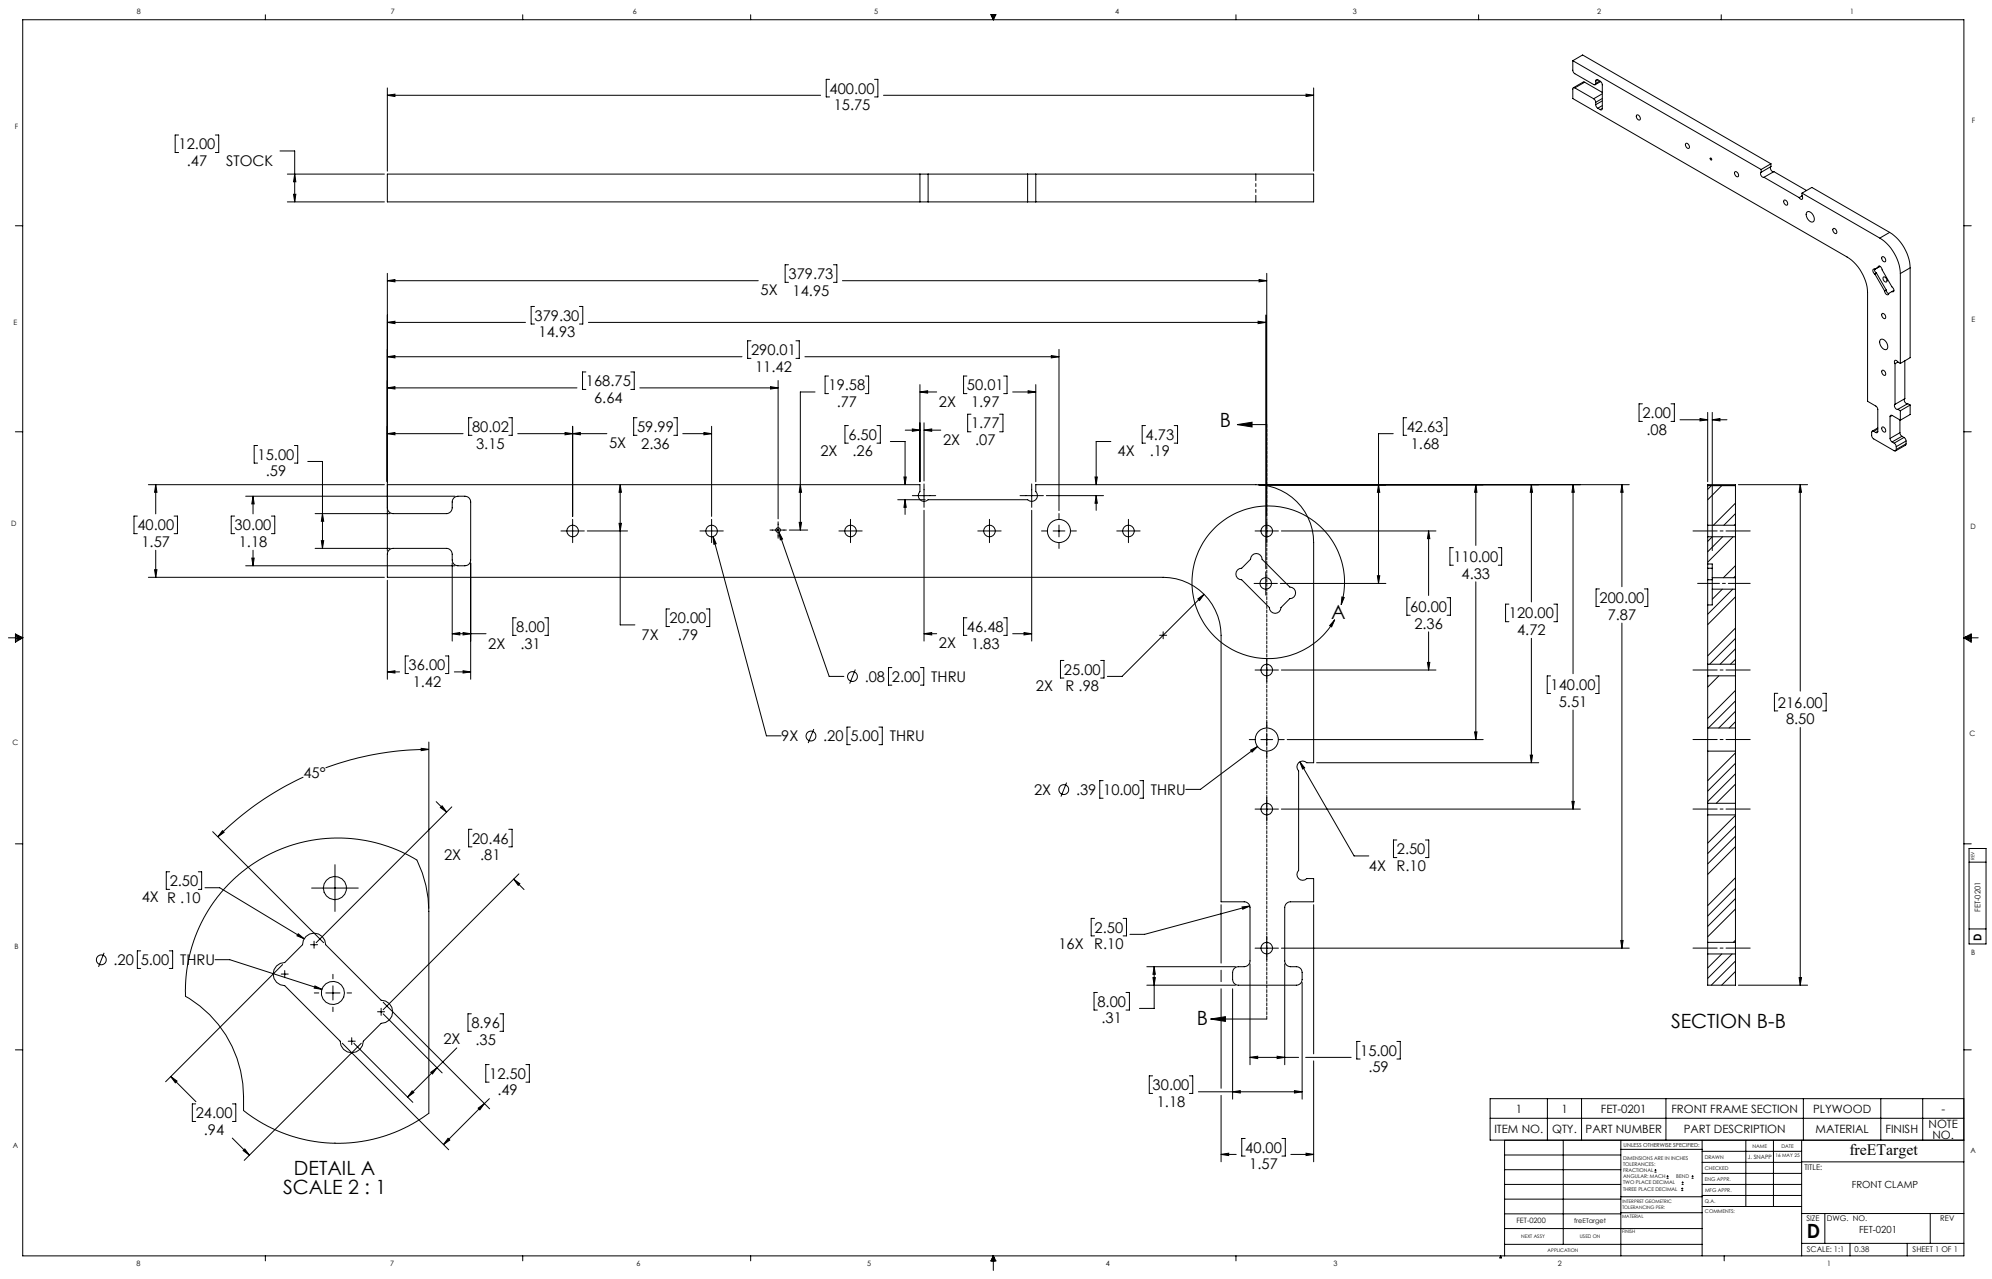
[picture p281: page 1]
.08 2.00 THRU; .20 5.00 THRU; .39 10.00 THRU; .47 STOCK; DETAIL A SCALE 2 : 1; SECTION B-B; FREV FET-0201; SHEET 1 OF 1; FRONT CLAMP; J. SNAPP 16 MAY 25; SCALE: 1:1 0.38; DWG. NO.; REV; freETarget NAME; DATE; MFG APPR.; ENG APPR.; INTERPRET GEOMETRIC TOLERANCING PER:; ANGULAR: MACH; BEND; NEXT ASSY; USED ON

1 | 1 | FET-0201 | FRONT FRAME SECTION | PLYWOOD | | -
ITEM NO. | QTY. | PART NUMBER | PART DESCRIPTION | MATERIAL | FINISH | NOTE NO.

UNLESS OTHERWISE SPECIFIED:

DIMENSIONS ARE IN INCHES
TOLERANCES:
FRACTIONAL
TWO PLACE DECIMAL
THREE PLACE DECIMAL
