ten-point-nine/freETarget/Mechanical/Dimensioned Drawings/50m Pistol Target/FET-0201 FRONT FRAME CLAMP.PDF

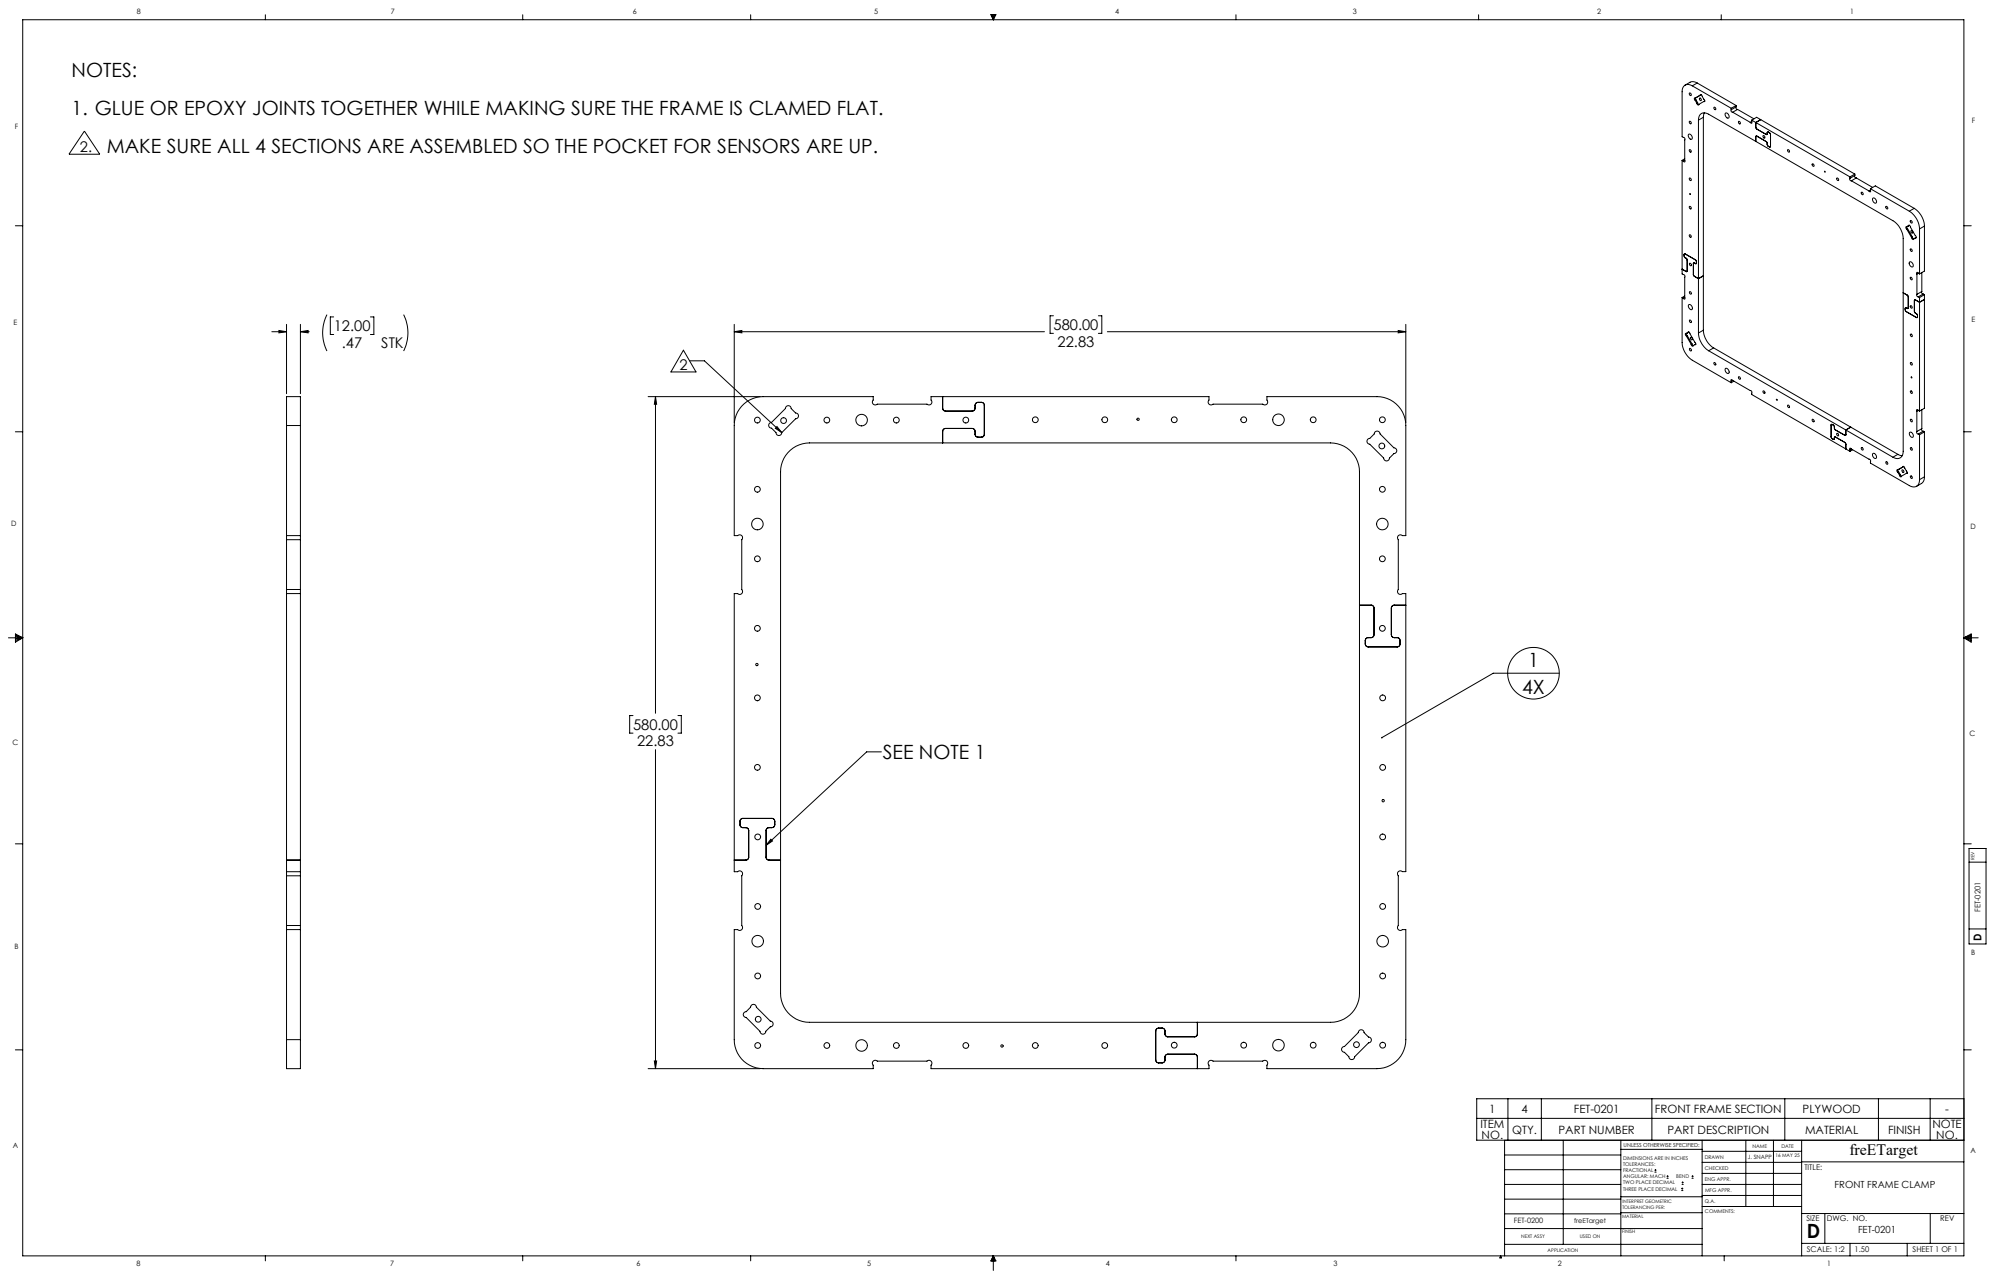
[picture p282: page 1]
SEE NOTE 1; .47 STK; FREV FET-0201; SHEET 1 OF 1; FRONT FRAME CLAMP; J. SNAPP 16 MAY 25; SCALE: 1:2 1.50; DWG. NO.; REV; freETarget NAME; DATE; MFG APPR.; ENG APPR.; INTERPRET GEOMETRIC TOLERANCING PER:; ANGULAR: MACH; BEND; NEXT ASSY; USED ON

NOTES:
1. GLUE OR EPOXY JOINTS TOGETHER WHILE MAKING SURE THE FRAME IS CLAMED FLAT.
2. MAKE SURE ALL 4 SECTIONS ARE ASSEMBLED SO THE POCKET FOR SENSORS ARE UP.

1 | 4 | FET-0201 | FRONT FRAME SECTION | PLYWOOD | | -
ITEM NO. | QTY. | PART NUMBER | PART DESCRIPTION | MATERIAL | FINISH | NOTE NO.

UNLESS OTHERWISE SPECIFIED:

DIMENSIONS ARE IN INCHES
TOLERANCES:
FRACTIONAL
TWO PLACE DECIMAL
THREE PLACE DECIMAL
