ten-point-nine/freETarget/Mechanical/Dimensioned Drawings/50m Pistol Target/FET-0202 FACE PLATE SECTION.PDF

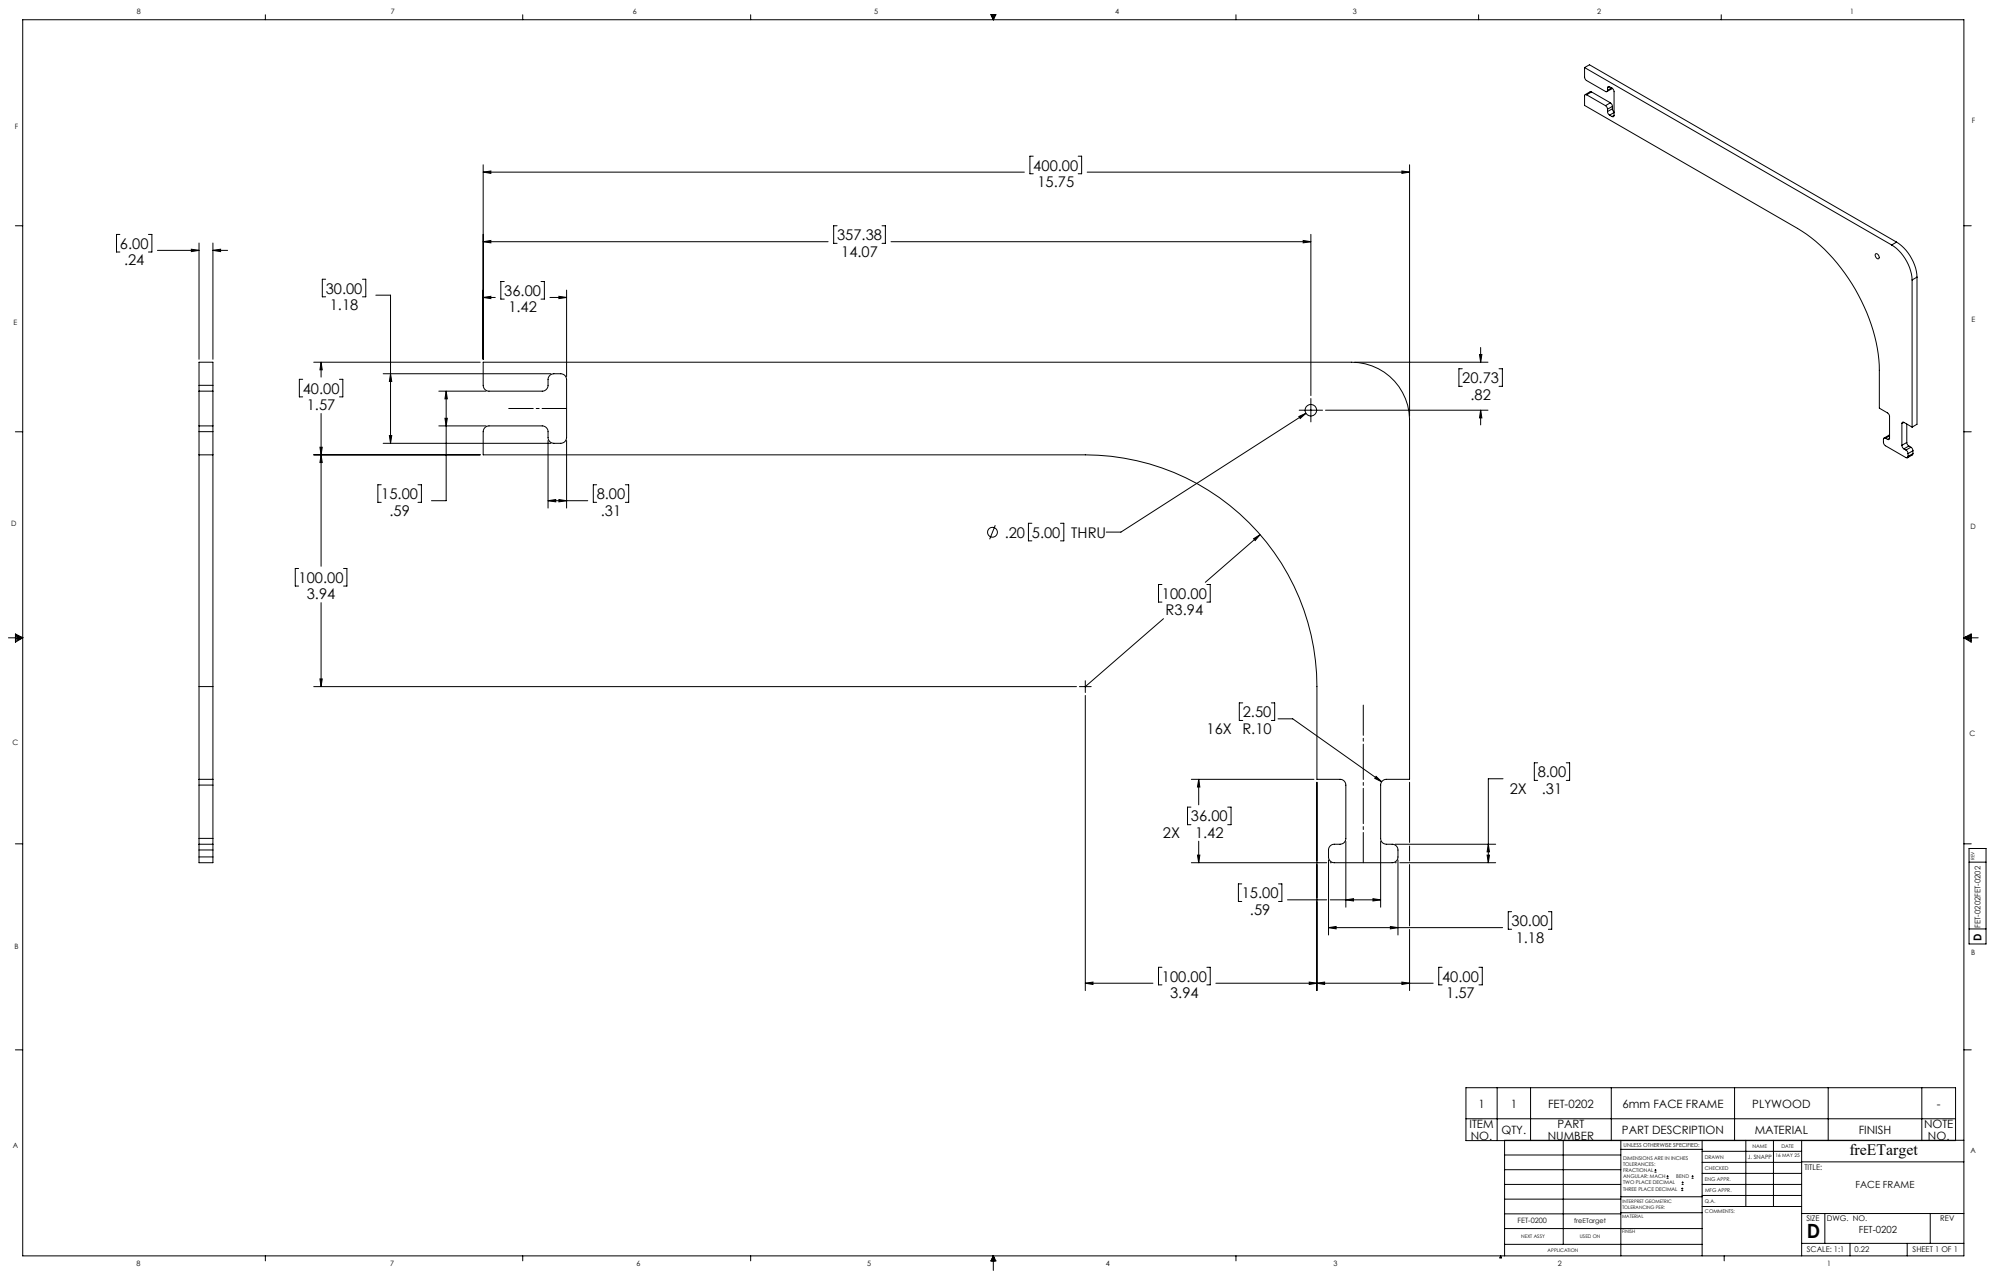
[picture p283: page 1]
.20 5.00 THRU; FREV FET-0202FET-0202; SHEET 1 OF 1; FACE FRAME; J. SNAPP 16 MAY 25; SCALE: 1:1 0.22; DWG. NO.; REV; freETarget NAME; DATE; MFG APPR.; ENG APPR.; INTERPRET GEOMETRIC TOLERANCING PER:; ANGULAR: MACH; BEND; NEXT ASSY; USED ON

1 | 1 | FET-0202 | 6mm FACE FRAME | PLYWOOD | | -
ITEM NO. | QTY. | NUMBER PART | PART DESCRIPTION | MATERIAL | FINISH | NOTE NO.

UNLESS OTHERWISE SPECIFIED:

DIMENSIONS ARE IN INCHES
TOLERANCES:
FRACTIONAL
TWO PLACE DECIMAL
THREE PLACE DECIMAL
