ten-point-nine/freETarget/Mechanical/Dimensioned Drawings/50m Pistol Target/FET-0202 FACE PLATE.PDF

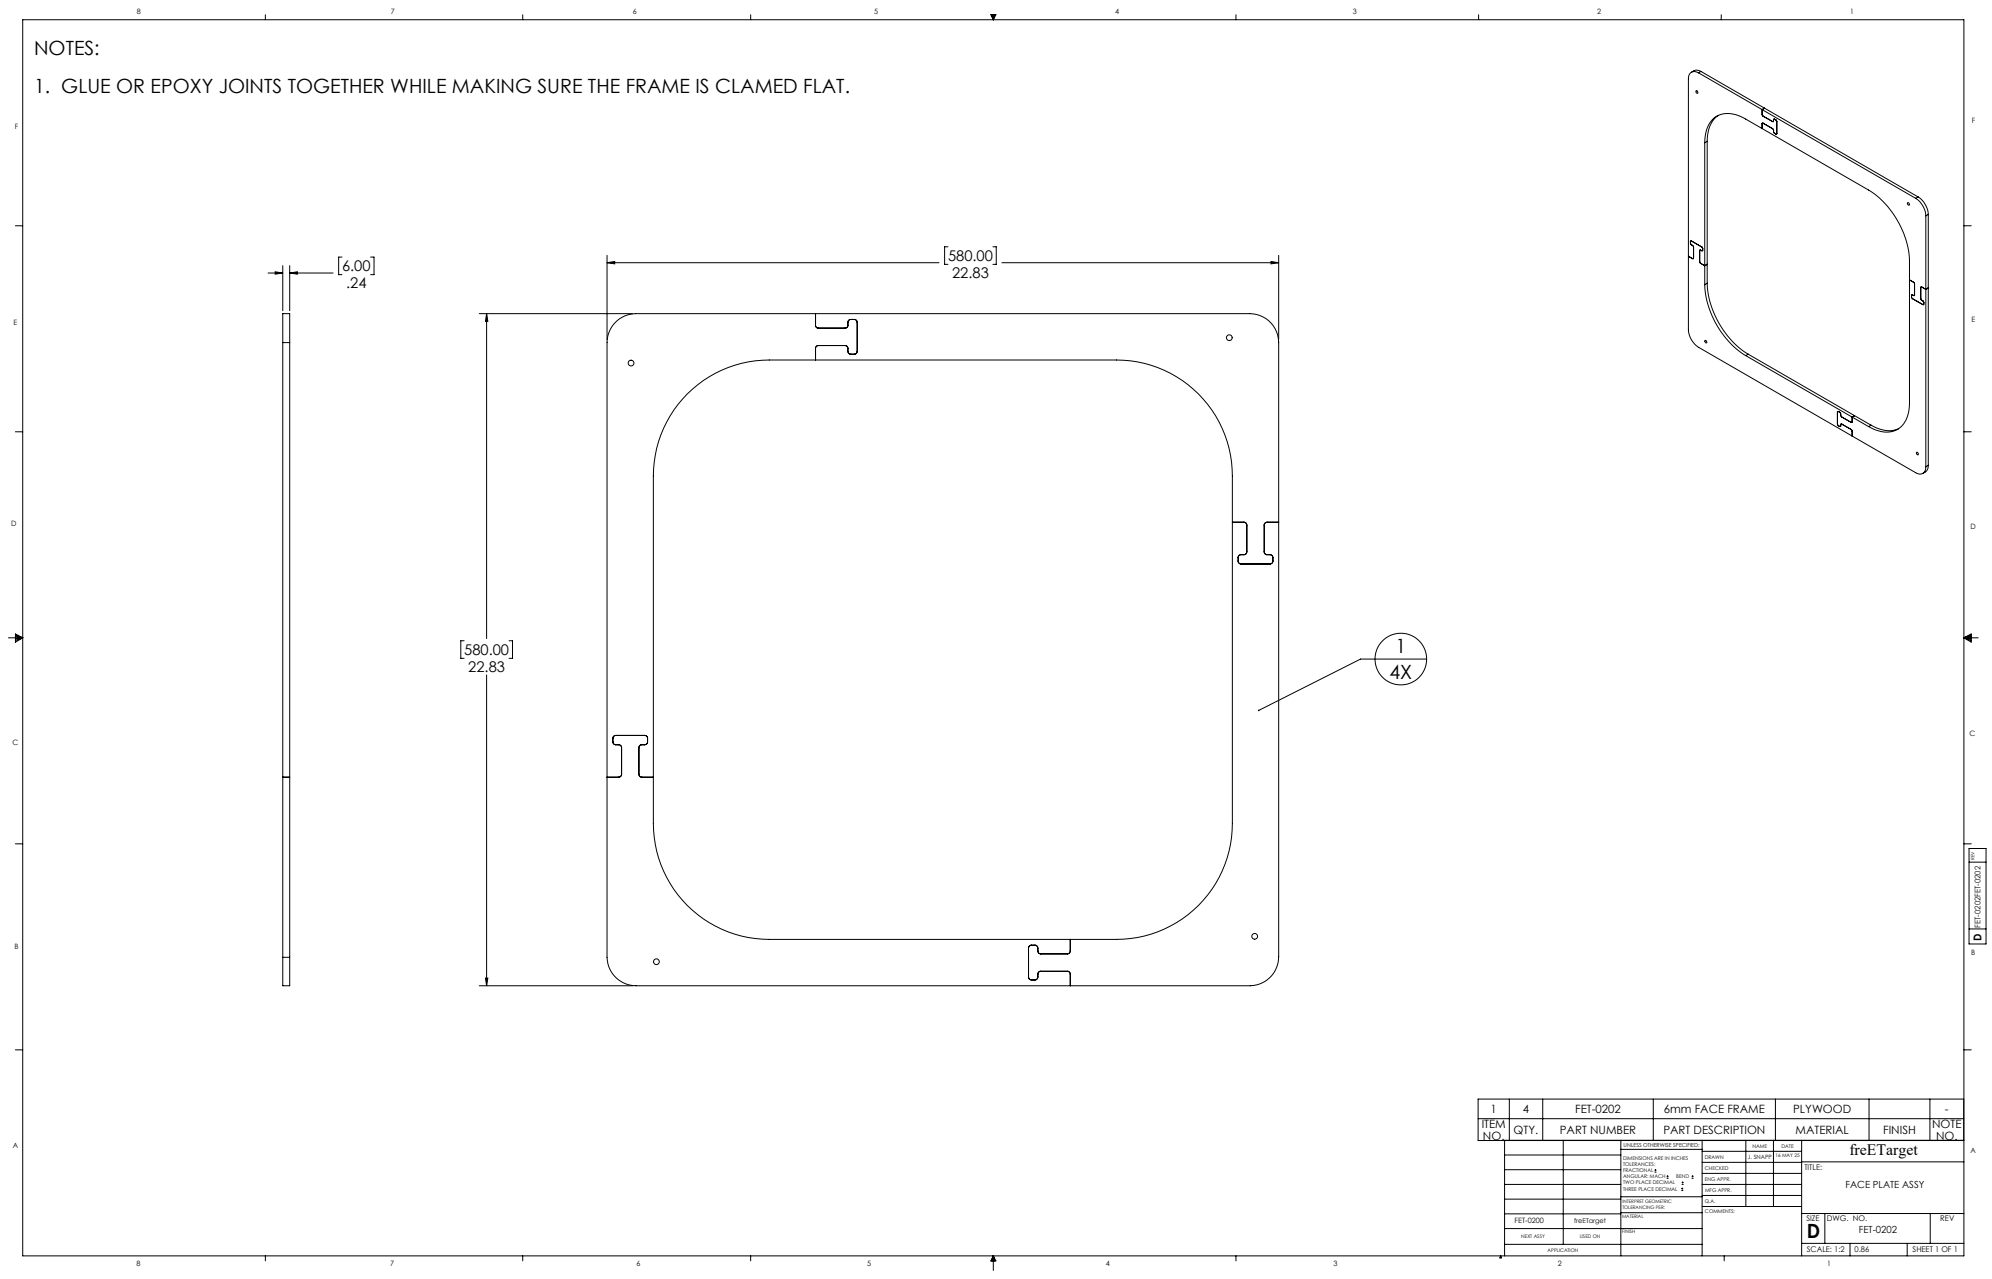
[picture p284: page 1]
FREV FET-0202FET-0202; SHEET 1 OF 1; J. SNAPP 16 MAY 25; SCALE: 1:2 0.86; DWG. NO.; REV; freETarget NAME; DATE; MFG APPR.; ENG APPR.; INTERPRET GEOMETRIC TOLERANCING PER:; ANGULAR: MACH; BEND; NEXT ASSY; USED ON

NOTES:
1. GLUE OR EPOXY JOINTS TOGETHER WHILE MAKING SURE THE FRAME IS CLAMED FLAT.

1 | 4 | FET-0202 | 6mm FACE FRAME | PLYWOOD | | -
ITEM NO. | QTY. | PART NUMBER | PART DESCRIPTION | MATERIAL | FINISH | NOTE NO.

UNLESS OTHERWISE SPECIFIED:

DIMENSIONS ARE IN INCHES
TOLERANCES:
FRACTIONAL
TWO PLACE DECIMAL
THREE PLACE DECIMAL

FACE PLATE ASSY
