ten-point-nine/freETarget/Mechanical/Dimensioned Drawings/50m Pistol Target/FET-0203 SIDE PANEL.PDF

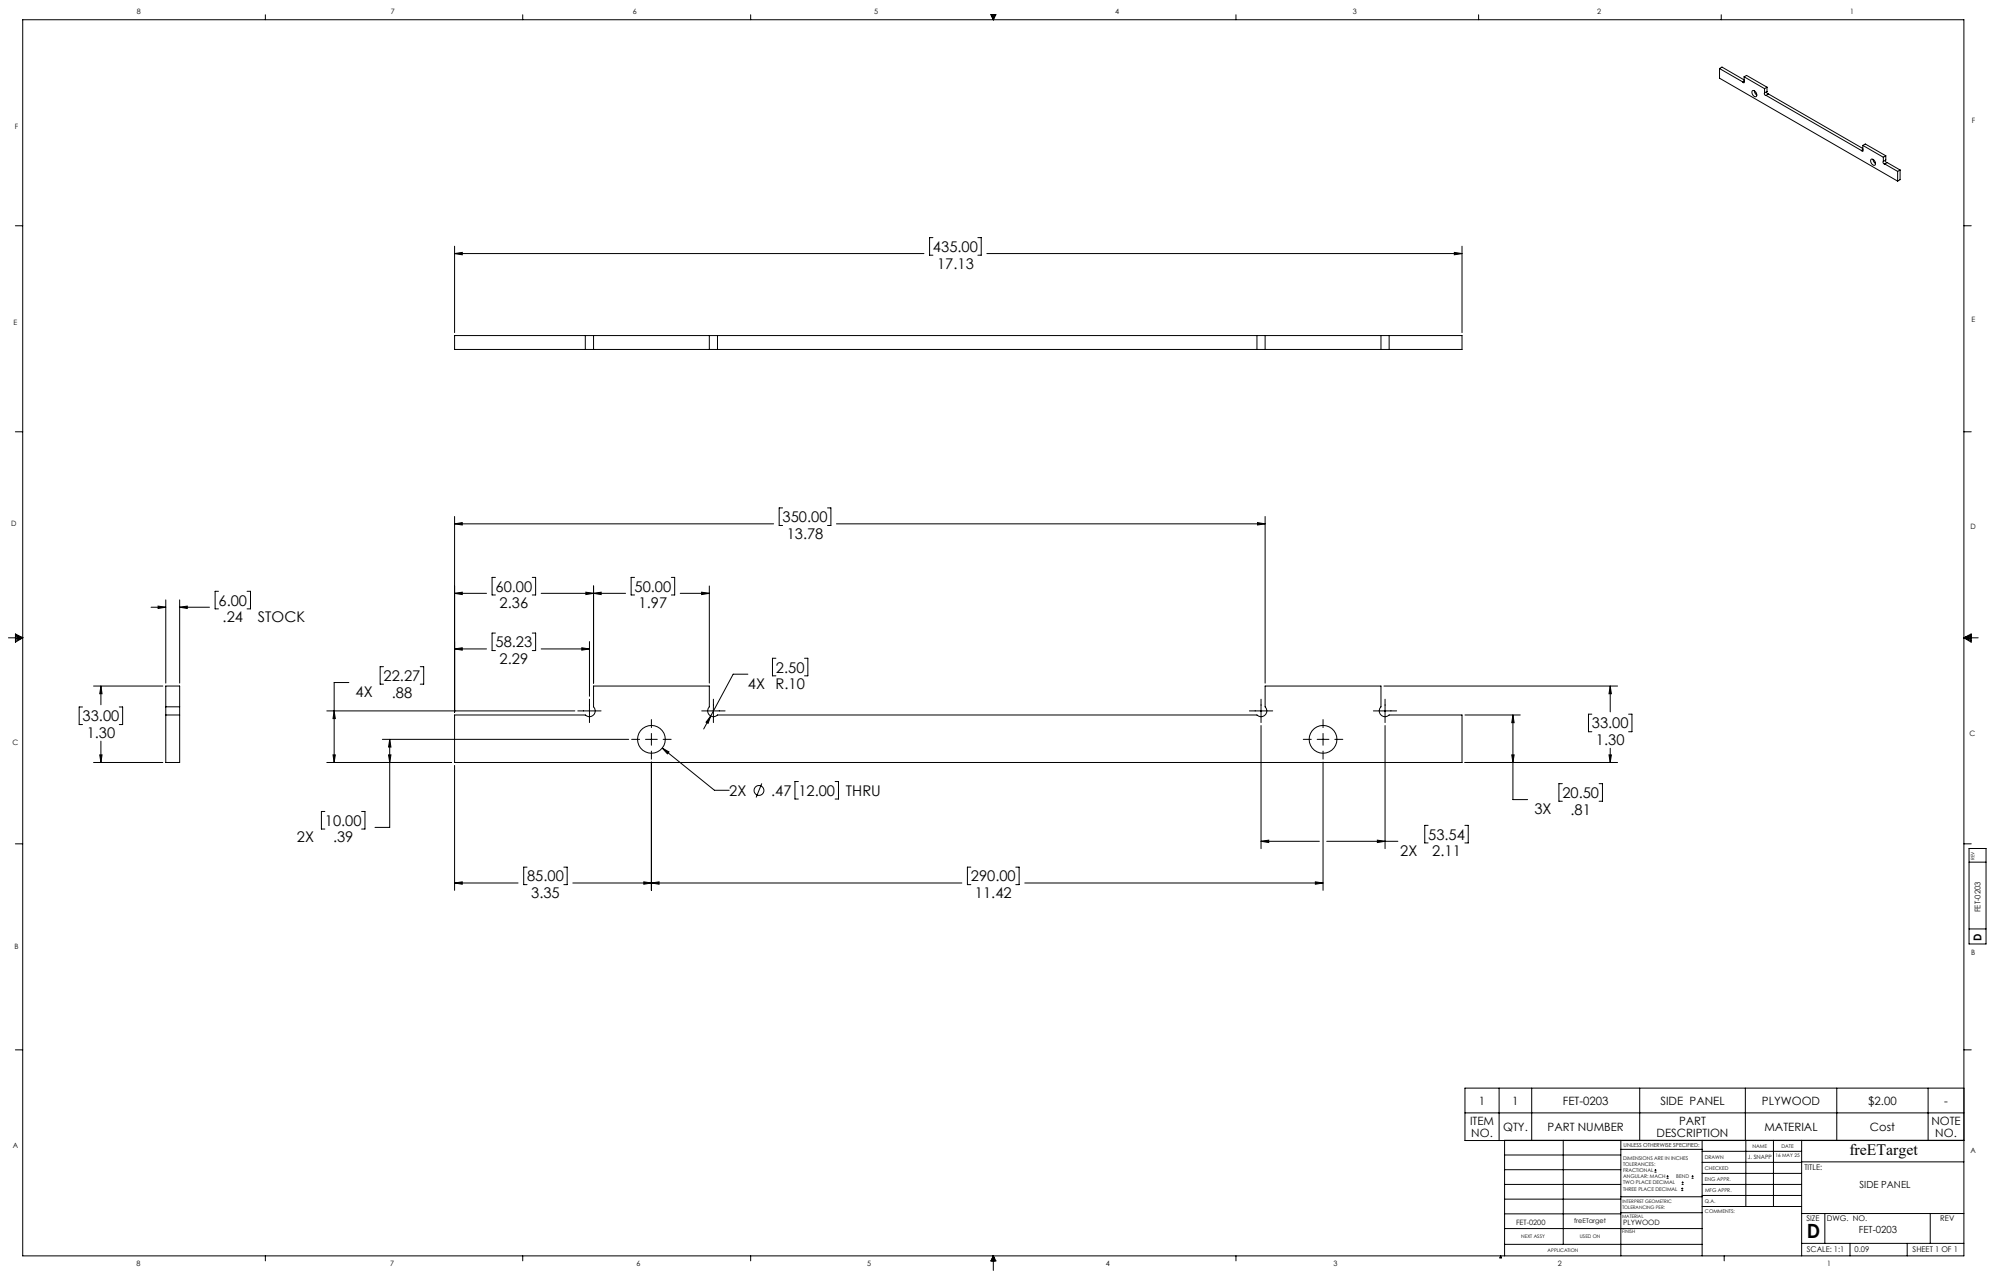
[picture p285: page 1]
.47 12.00 THRU; .24 STOCK; FREV FET-0203; SHEET 1 OF 1; SIDE PANEL; J. SNAPP 16 MAY 25; SCALE: 1:1 0.09; DWG. NO.; REV; freETarget NAME; DATE; MFG APPR.; ENG APPR.; INTERPRET GEOMETRIC TOLERANCING PER:; ANGULAR: MACH; BEND; NEXT ASSY; USED ON

1 | 1 | FET-0203 | SIDE PANEL | PLYWOOD | $2.00 | -
ITEM NO. | QTY. | PART NUMBER | DESCRIPTION PART | MATERIAL | Cost | NOTE NO.

UNLESS OTHERWISE SPECIFIED:

DIMENSIONS ARE IN INCHES
TOLERANCES:
FRACTIONAL
TWO PLACE DECIMAL
THREE PLACE DECIMAL
