ten-point-nine/freETarget/Mechanical/Dimensioned Drawings/50m Pistol Target/FET-0204 SENSOR MOUNT.PDF

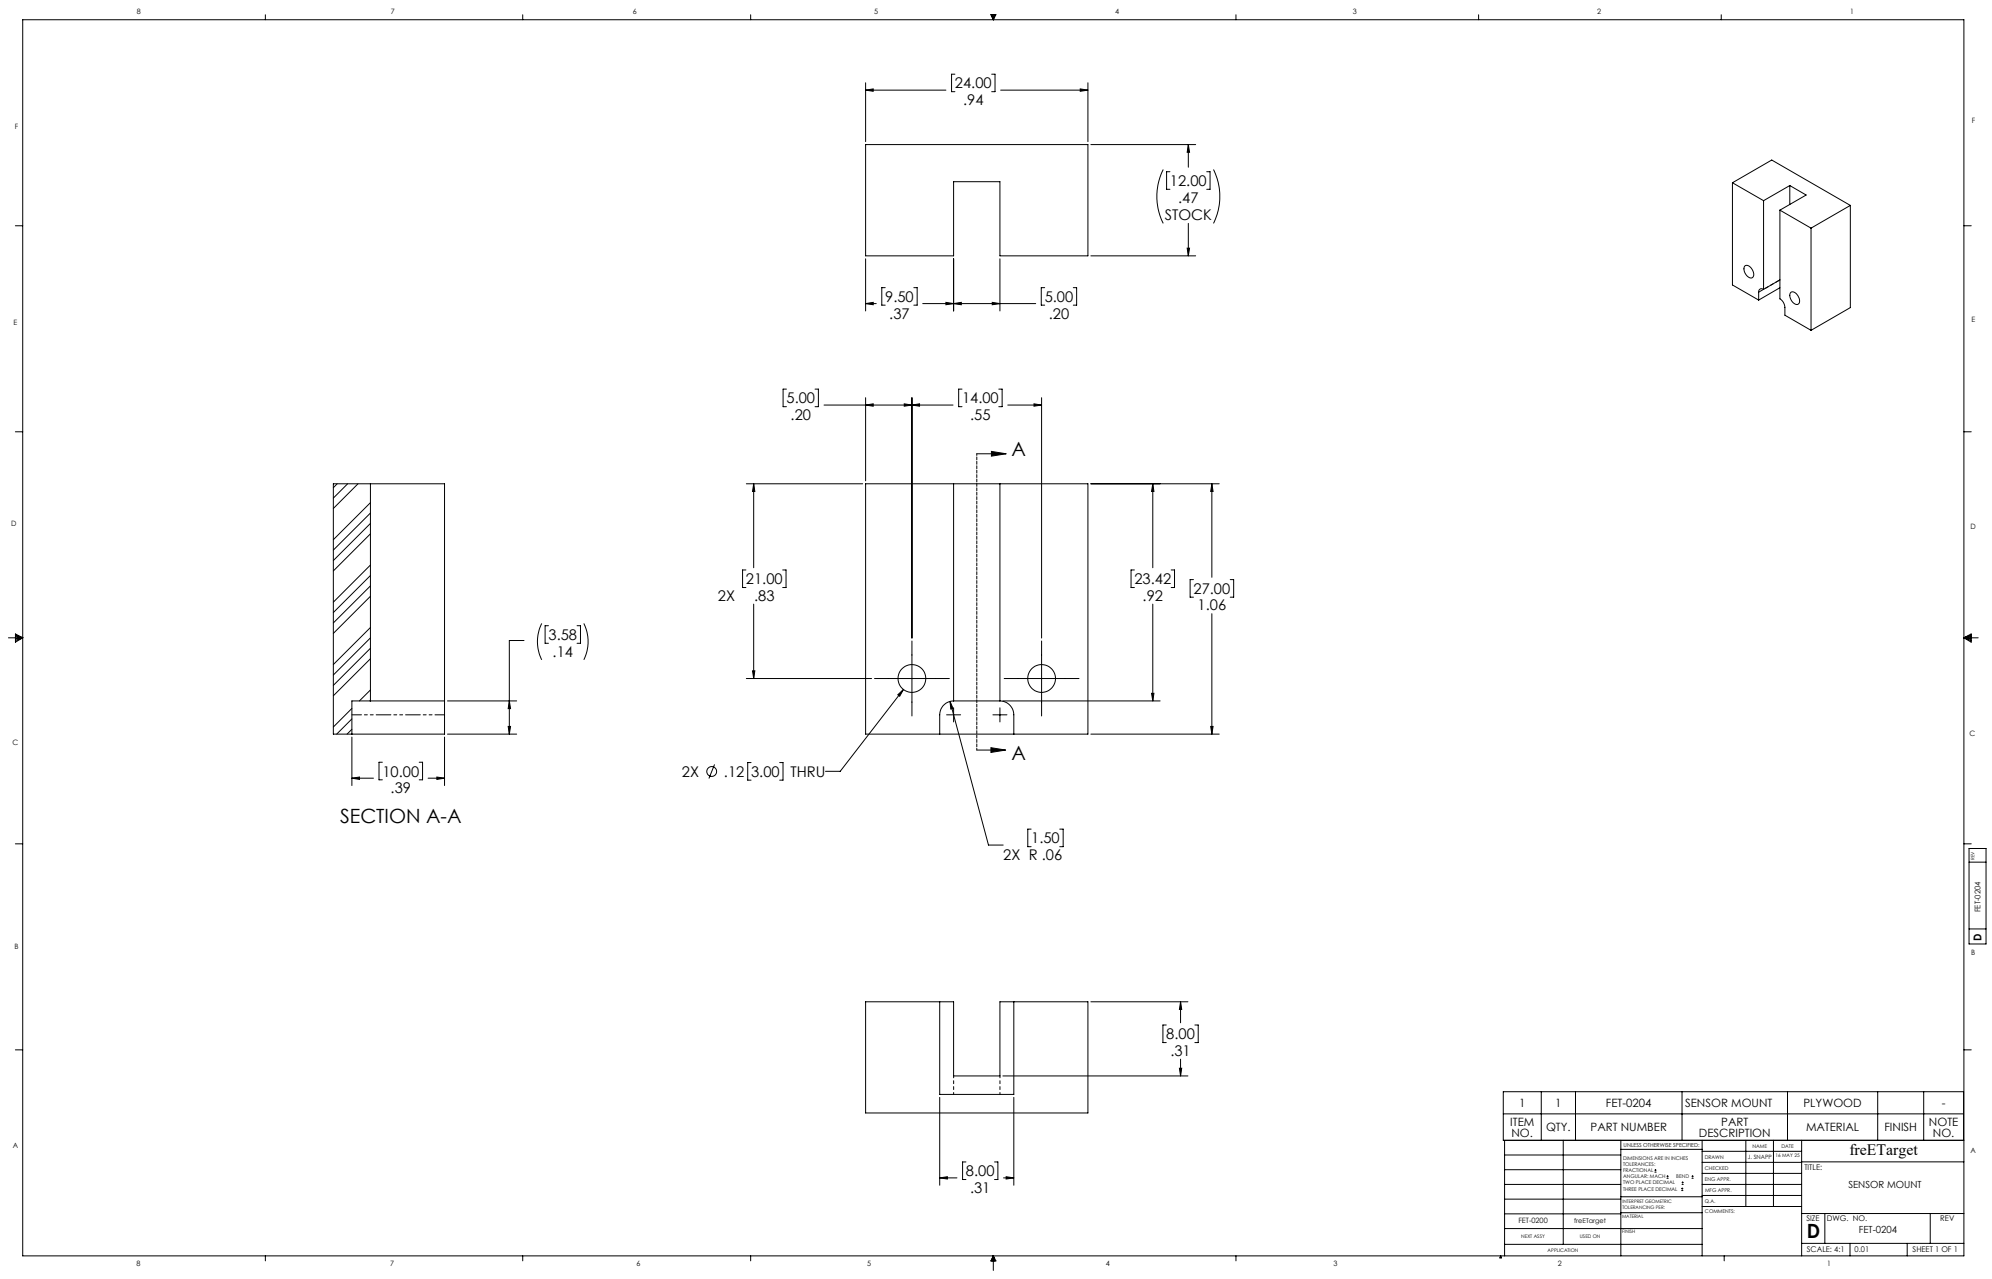
[picture p286: page 1]
.12 3.00 THRU; SECTION A-A; FREV FET-0204; SHEET 1 OF 1; SENSOR MOUNT; J. SNAPP 16 MAY 25; SCALE: 4:1 0.01; DWG. NO.; REV; freETarget NAME; DATE; MFG APPR.; ENG APPR.; INTERPRET GEOMETRIC TOLERANCING PER:; ANGULAR: MACH; BEND; NEXT ASSY; USED ON

1 | 1 | FET-0204 | SENSOR MOUNT | PLYWOOD | | -
ITEM NO. | QTY. | PART NUMBER | DESCRIPTION PART | MATERIAL | FINISH | NOTE NO.

UNLESS OTHERWISE SPECIFIED:

DIMENSIONS ARE IN INCHES
TOLERANCES:
FRACTIONAL
TWO PLACE DECIMAL
THREE PLACE DECIMAL
