ten-point-nine/freETarget/Mechanical/Dimensioned Drawings/50m Pistol Target/FET-0205 FRAME BACK CLAMP.PDF

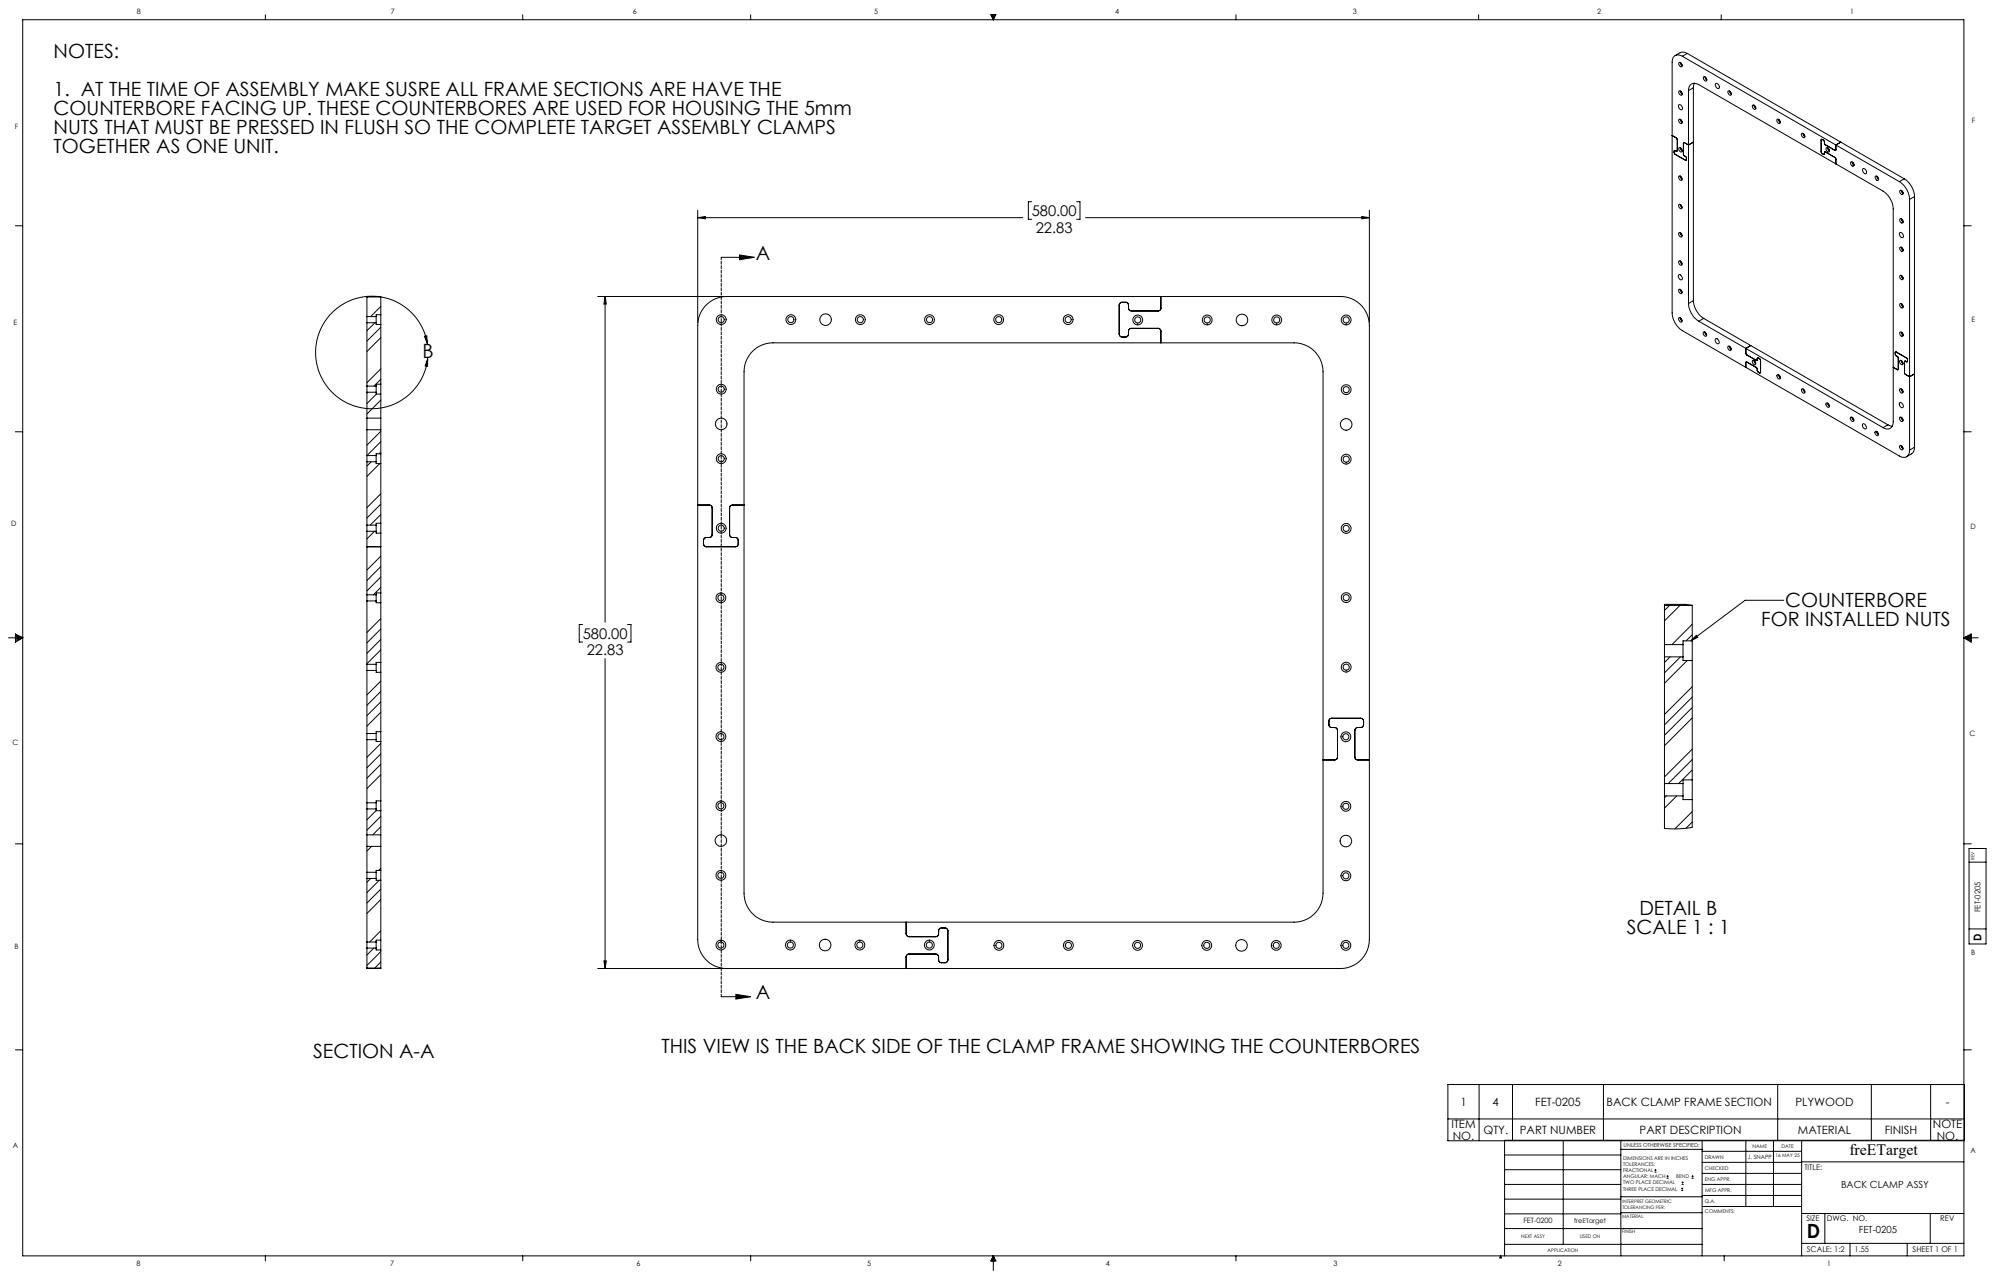
[picture p287: page 1]
SECTION A-A; DETAIL B SCALE 1 : 1; FREV FET-0205; SHEET 1 OF 1; BACK CLAMP ASSY; J. SNAPP 16 MAY 25; SCALE: 1:2 1.55; DWG. NO.; REV; freETarget NAME; DATE; MFG APPR.; ENG APPR.; INTERPRET GEOMETRIC TOLERANCING PER:; ANGULAR: MACH; BEND; NEXT ASSY; USED ON

NOTES:
1. AT THE TIME OF ASSEMBLY MAKE SUSRE ALL FRAME SECTIONS ARE HAVE THE
COUNTERBORE FACING UP. THESE COUNTERBORES ARE USED FOR HOUSING THE 5mm
NUTS THAT MUST BE PRESSED IN FLUSH SO THE COMPLETE TARGET ASSEMBLY CLAMPS
TOGETHER AS ONE UNIT.

COUNTERBORE
FOR INSTALLED NUTS

THIS VIEW IS THE BACK SIDE OF THE CLAMP FRAME SHOWING THE COUNTERBORES

1 | 4 | FET-0205 | BACK CLAMP FRAME SECTION | PLYWOOD | | -
ITEM NO. | QTY. | PART NUMBER | PART DESCRIPTION | MATERIAL | FINISH | NOTE NO.

UNLESS OTHERWISE SPECIFIED:

DIMENSIONS ARE IN INCHES
TOLERANCES:
FRACTIONAL
TWO PLACE DECIMAL
THREE PLACE DECIMAL
