ten-point-nine/freETarget/Mechanical/Dimensioned Drawings/50m Pistol Target/FET-0206 TARGET GUIDE.PDF

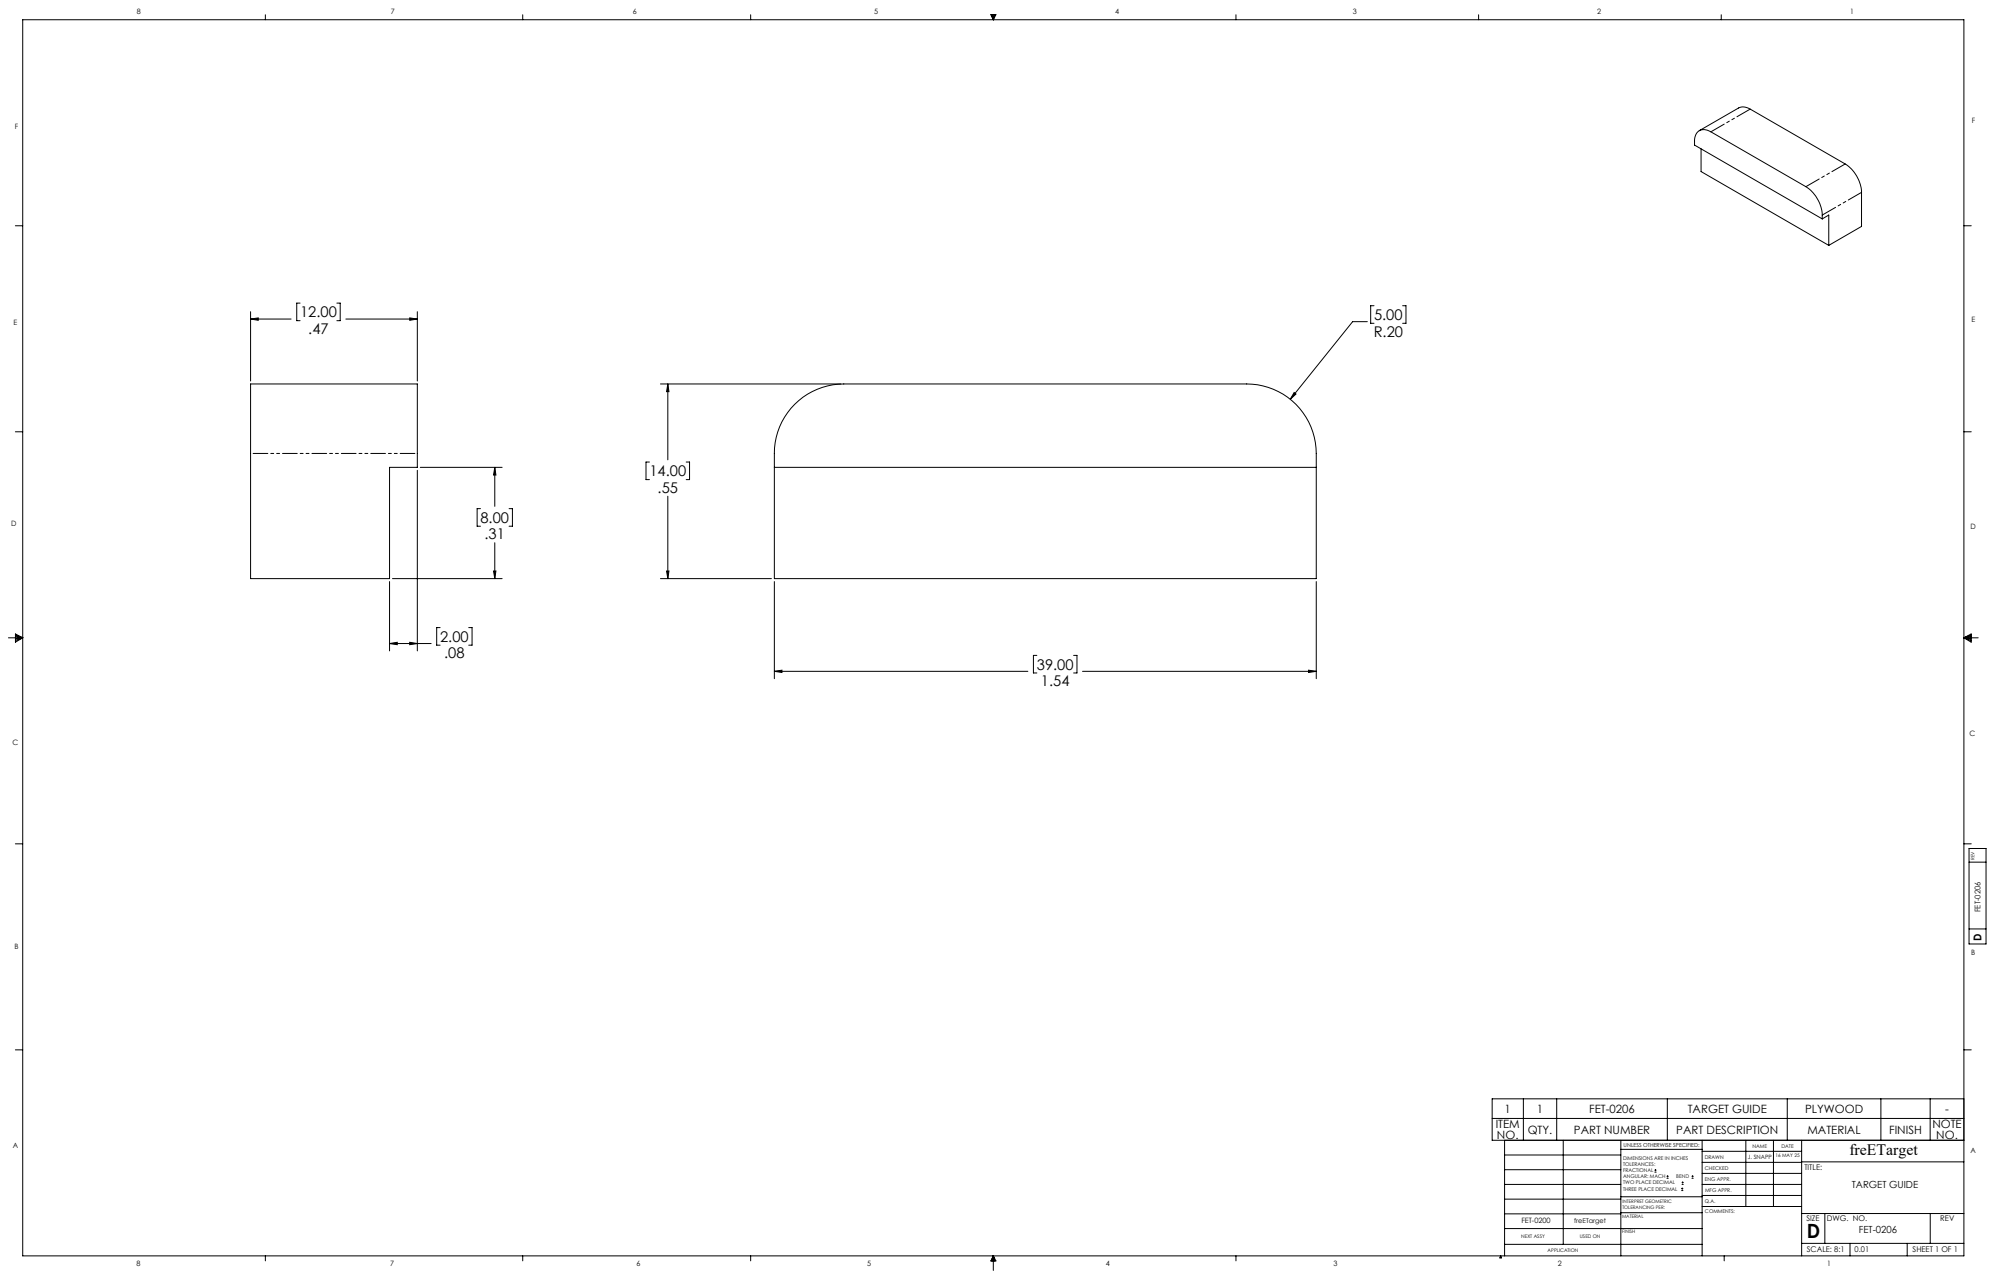
[picture p288: page 1]
FREV FET-0206; SHEET 1 OF 1; TARGET GUIDE; J. SNAPP 16 MAY 25; SCALE: 8:1 0.01; DWG. NO.; REV; freETarget NAME; DATE; MFG APPR.; ENG APPR.; INTERPRET GEOMETRIC TOLERANCING PER:; ANGULAR: MACH; BEND; NEXT ASSY; USED ON

1 | 1 | FET-0206 | TARGET GUIDE | PLYWOOD | | -
ITEM NO. | QTY. | PART NUMBER | PART DESCRIPTION | MATERIAL | FINISH | NOTE NO.

UNLESS OTHERWISE SPECIFIED:

DIMENSIONS ARE IN INCHES
TOLERANCES:
FRACTIONAL
TWO PLACE DECIMAL
THREE PLACE DECIMAL
