ten-point-nine/freETarget/Mechanical/Dimensioned Drawings/50m Pistol Target/FET-0208  STEEL GUARD.PDF

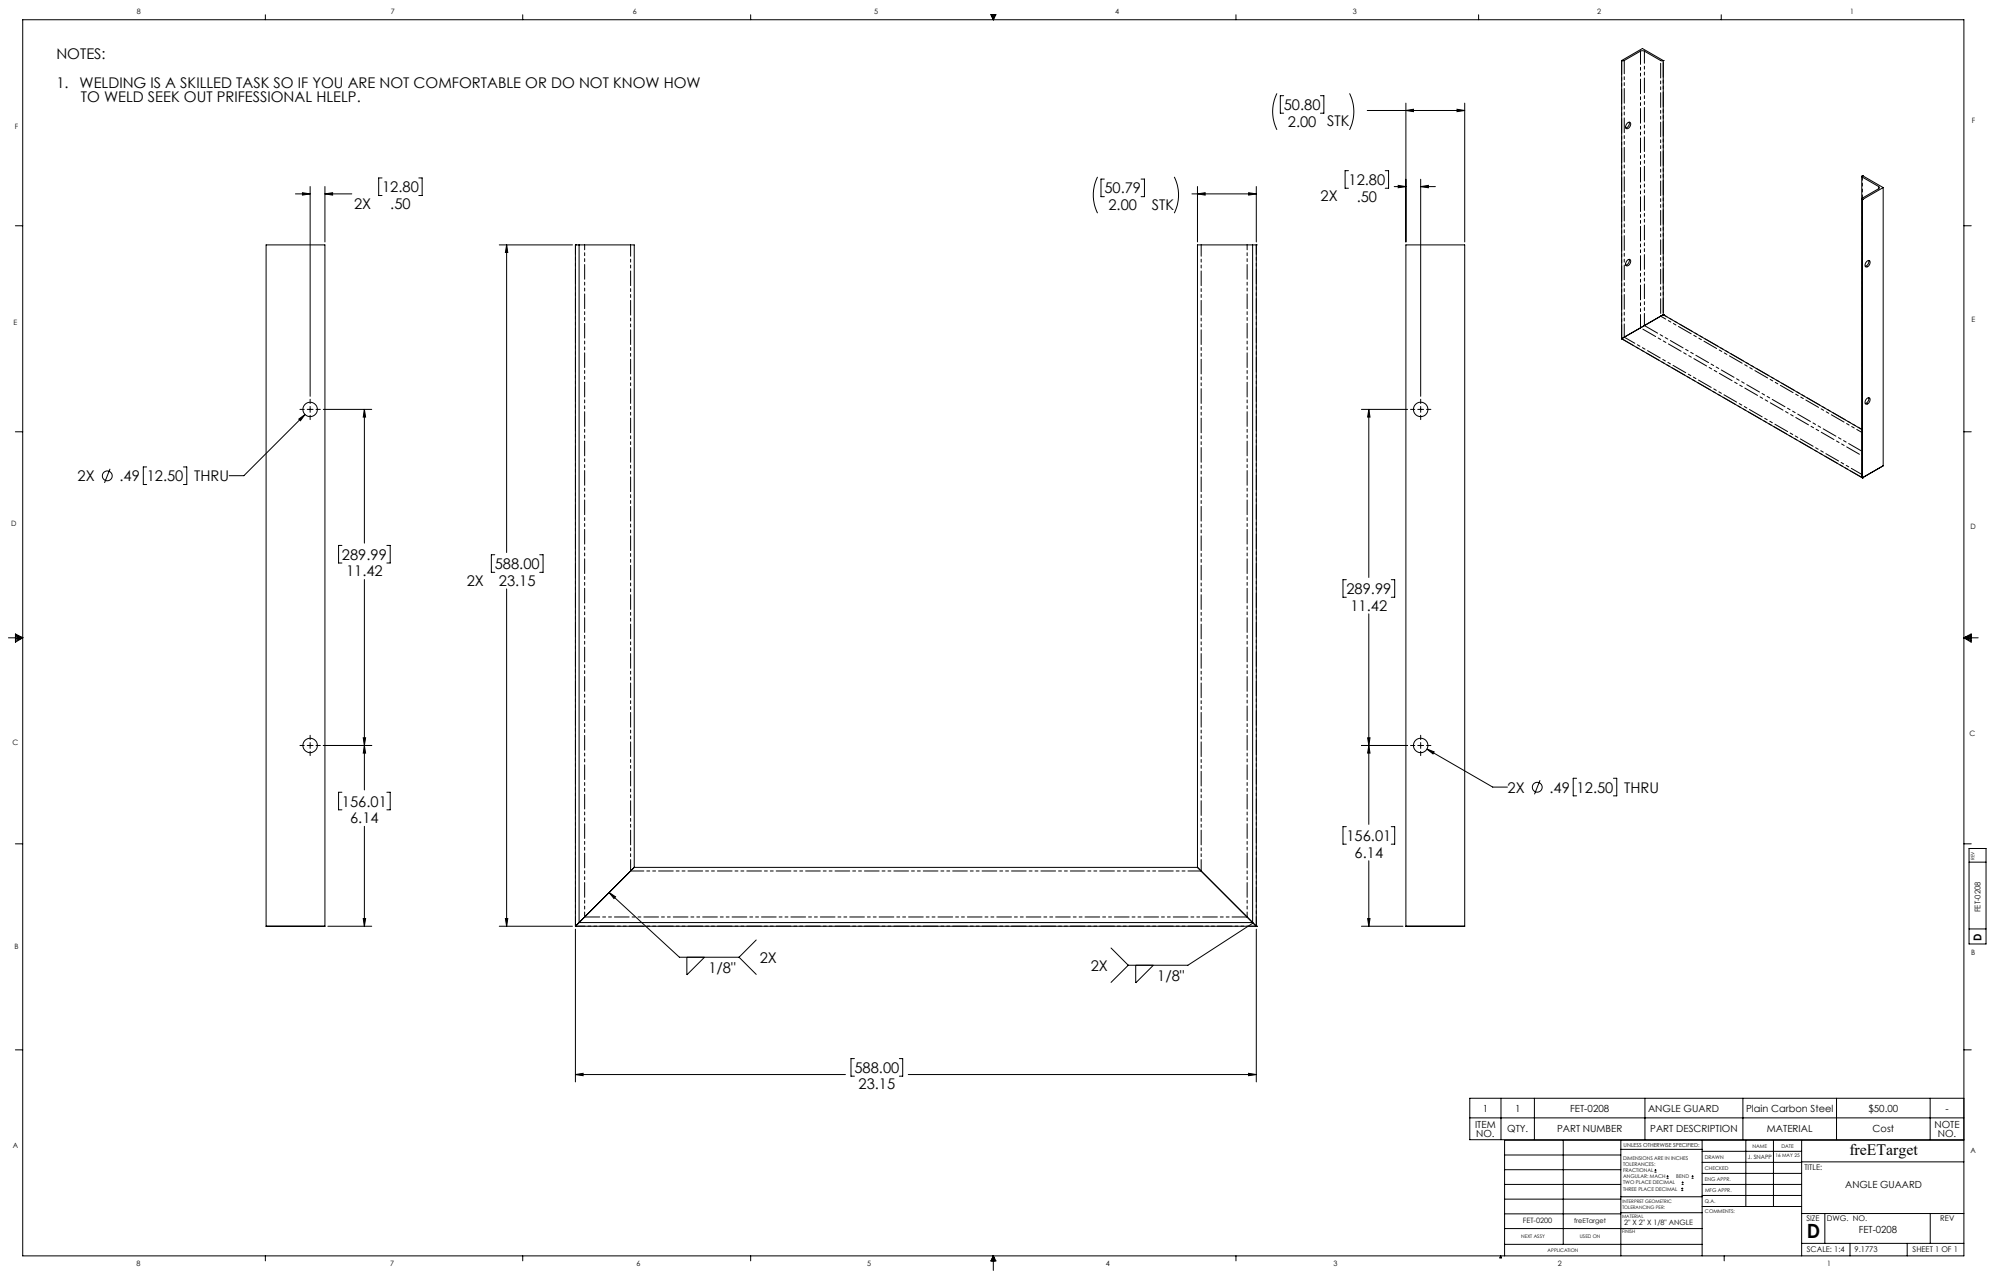
[picture p289: page 1]
2.00 STK; .49 12.50 THRU; FREV FET-0208; SHEET 1 OF 1; ANGLE GUAARD; J. SNAPP 16 MAY 25; SCALE: 1:4 9.1773; DWG. NO.; REV; freETarget NAME; DATE; MFG APPR.; ENG APPR.; 2" X 2" X 1/8" ANGLE; INTERPRET GEOMETRIC TOLERANCING PER:; ANGULAR: MACH; BEND; NEXT ASSY; USED ON

NOTES:
1. WELDING IS A SKILLED TASK SO IF YOU ARE NOT COMFORTABLE OR DO NOT KNOW HOW
TO WELD SEEK OUT PRIFESSIONAL HLELP.

1 | 1 | FET-0208 | ANGLE GUARD | Plain Carbon Steel | $50.00 | -
ITEM NO. | QTY. | PART NUMBER | PART DESCRIPTION | MATERIAL | Cost | NOTE NO.

UNLESS OTHERWISE SPECIFIED:

DIMENSIONS ARE IN INCHES
TOLERANCES:
FRACTIONAL
TWO PLACE DECIMAL
THREE PLACE DECIMAL
