ten-point-nine/freETarget/Mechanical/Dimensioned Drawings/50m Pistol Target/FET-0209 TARGET STOP PINS.PDF

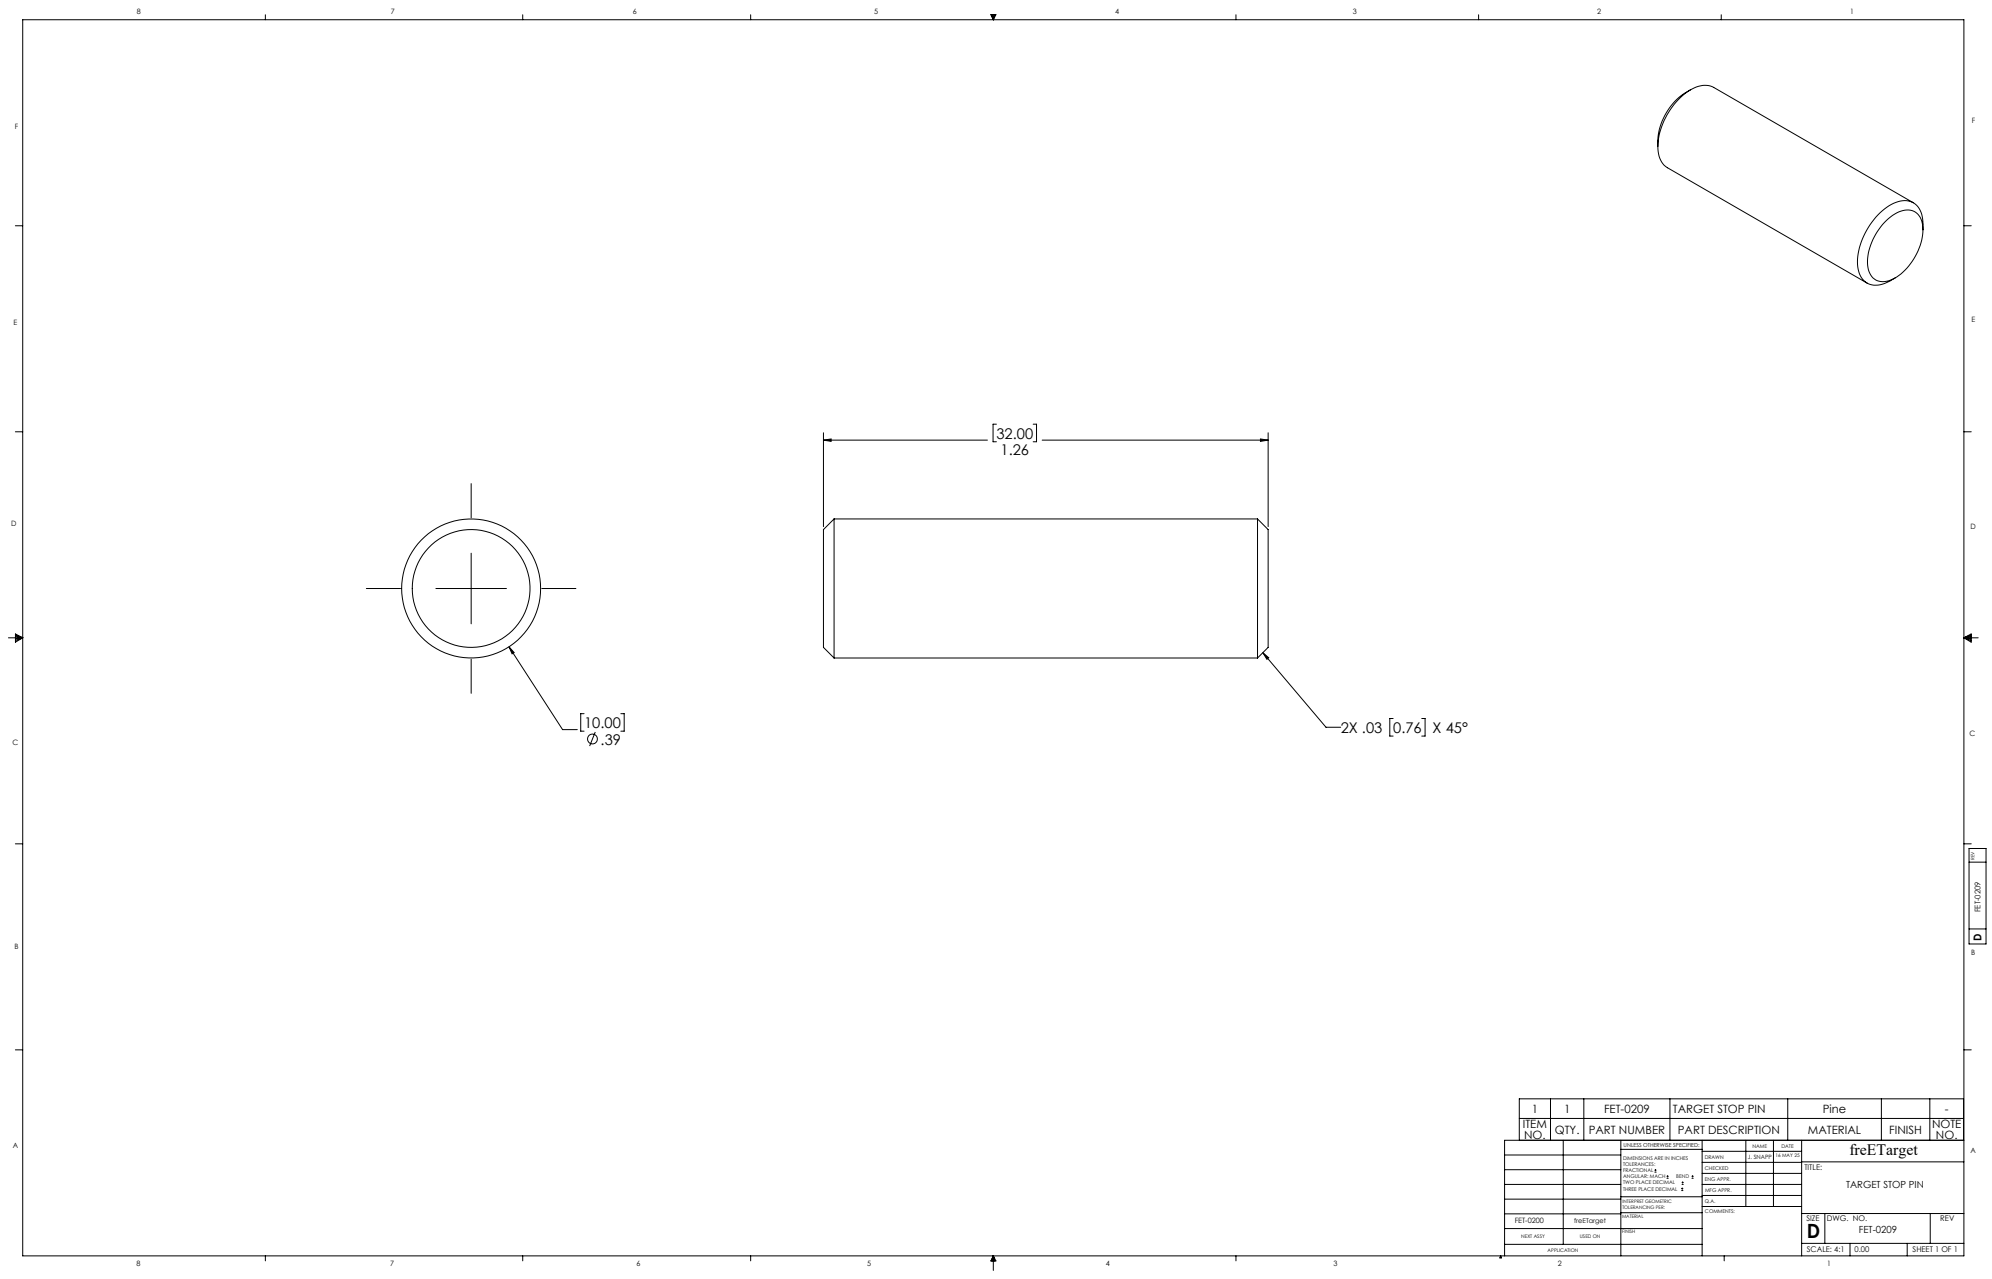
[picture p290: page 1]
FREV FET-0209; SHEET 1 OF 1; J. SNAPP 16 MAY 25; SCALE: 4:1 0.00; DWG. NO.; REV; freETarget NAME; DATE; MFG APPR.; ENG APPR.; INTERPRET GEOMETRIC TOLERANCING PER:; ANGULAR: MACH; BEND; NEXT ASSY; USED ON

1 | 1 | FET-0209 | TARGET STOP PIN | Pine | | -
ITEM NO. | QTY. | PART NUMBER | PART DESCRIPTION | MATERIAL | FINISH | NOTE NO.

UNLESS OTHERWISE SPECIFIED:

DIMENSIONS ARE IN INCHES
TOLERANCES:
FRACTIONAL
TWO PLACE DECIMAL
THREE PLACE DECIMAL

TARGET STOP PIN
