ten-point-nine/freETarget/Mechanical/Dimensioned Drawings/50m Pistol Target/FET-0210 BACKSTOP MATT.PDF

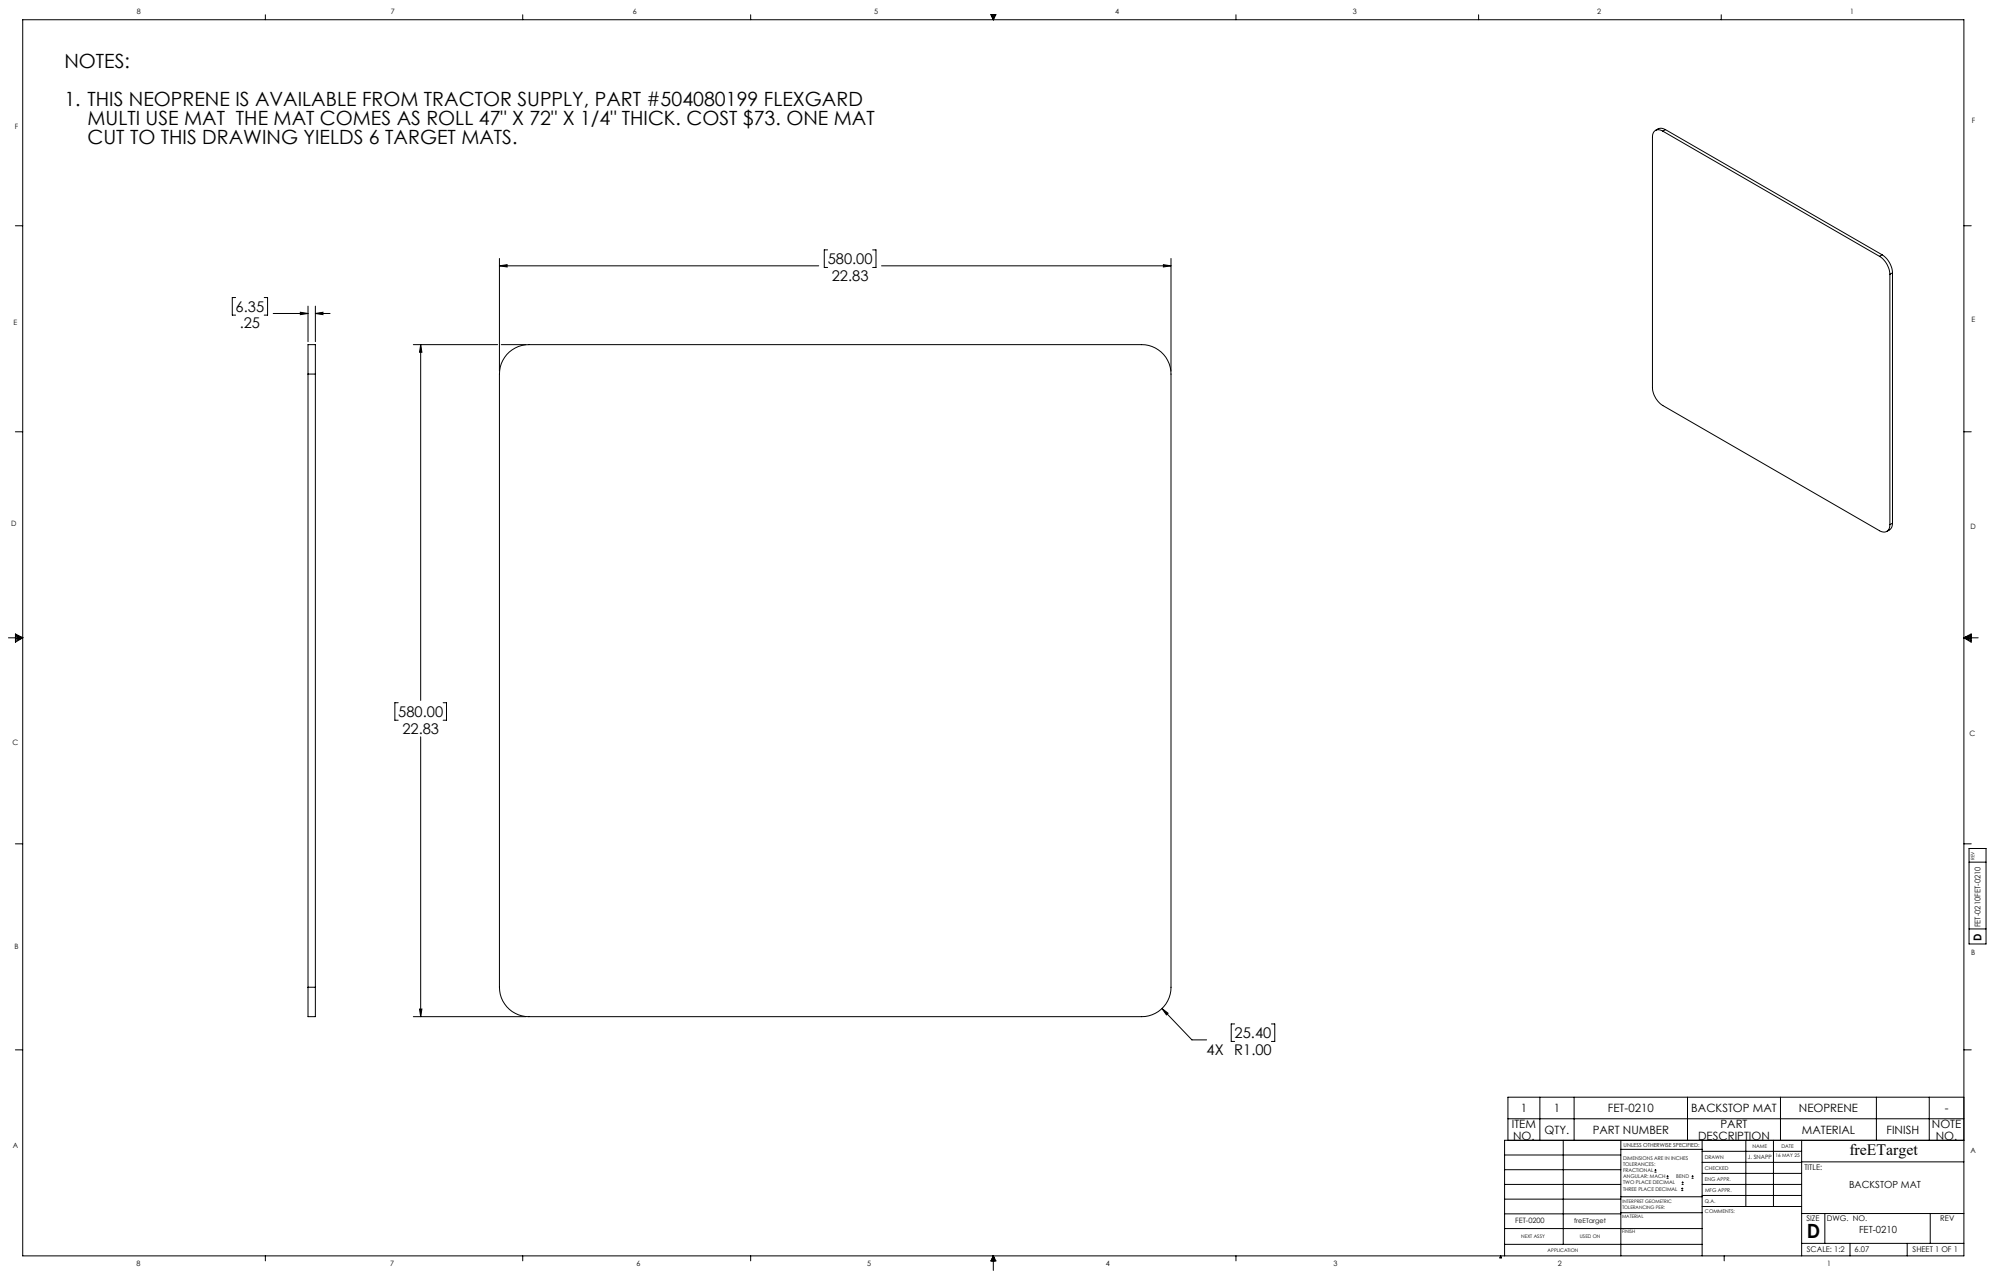
[picture p291: page 1]
FREV FET-0210FET-0210; SHEET 1 OF 1; BACKSTOP MAT; J. SNAPP 16 MAY 25; SCALE: 1:2 6.07; DWG. NO.; REV; freETarget NAME; DATE; MFG APPR.; ENG APPR.; INTERPRET GEOMETRIC TOLERANCING PER:; ANGULAR: MACH; BEND; NEXT ASSY; USED ON

NOTES:
1. THIS NEOPRENE IS AVAILABLE FROM TRACTOR SUPPLY, PART #504080199 FLEXGARD
MULTI USE MAT THE MAT COMES AS ROLL 47" X 72" X 1/4" THICK. COST $73. ONE MAT
CUT TO THIS DRAWING YIELDS 6 TARGET MATS.

1 | 1 | FET-0210 | BACKSTOP MAT | NEOPRENE | | -
ITEM NO. | QTY. | PART NUMBER | DESCRIPTION PART | MATERIAL | FINISH | NOTE NO.

UNLESS OTHERWISE SPECIFIED:

DIMENSIONS ARE IN INCHES
TOLERANCES:
FRACTIONAL
TWO PLACE DECIMAL
THREE PLACE DECIMAL
