ten-point-nine/freETarget/Mechanical/Dimensioned Drawings/50m Pistol Target/FET-0211 BASE SUPPORT FOR B17_B19.PDF

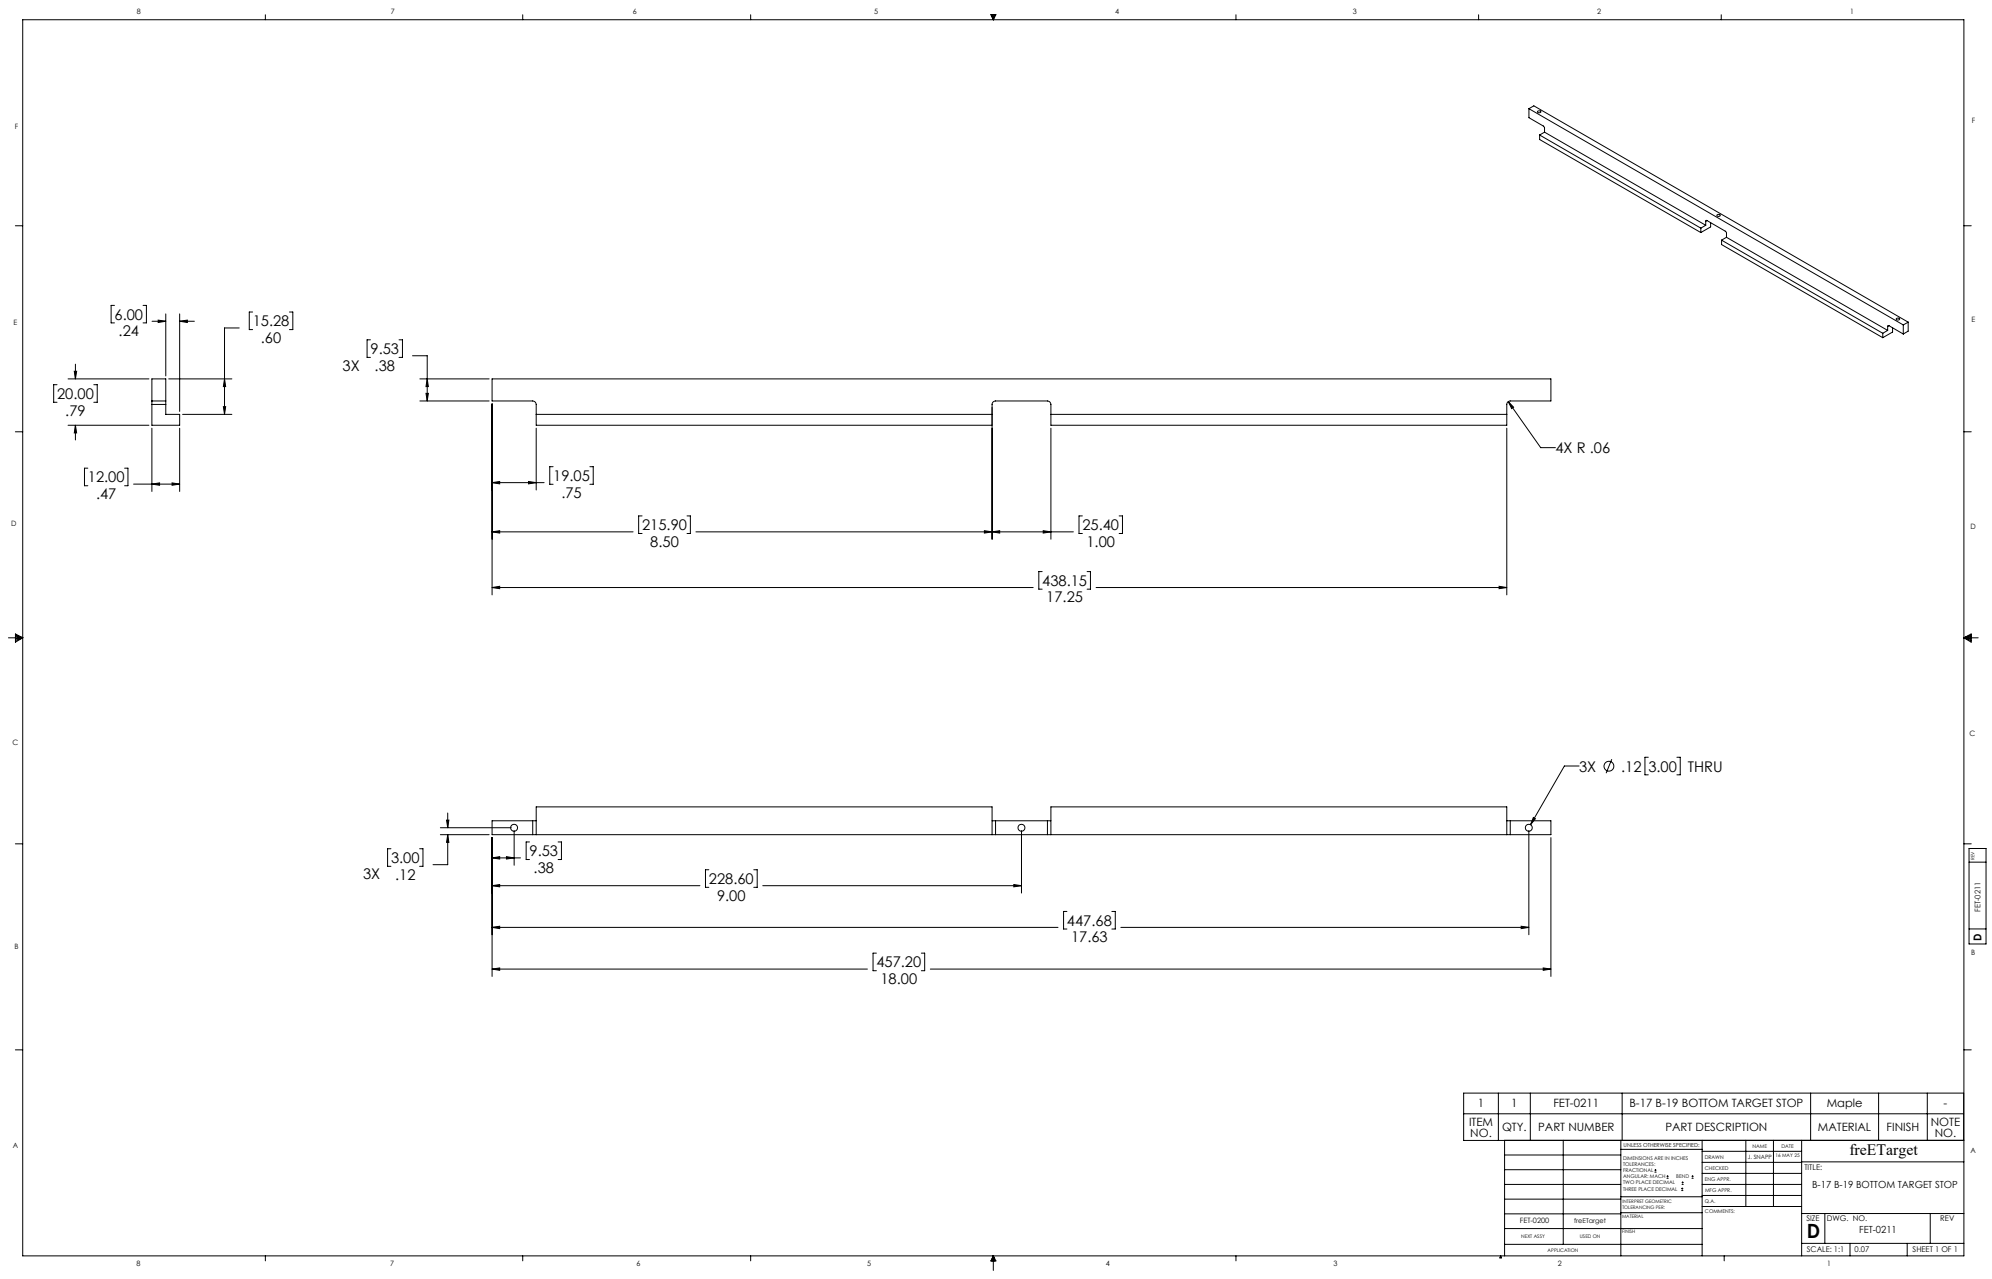
[picture p292: page 1]
.12 3.00 THRU; FREV FET-0211; SHEET 1 OF 1; B-17 B-19 BOTTOM TARGET STOP; J. SNAPP 16 MAY 25; SCALE: 1:1 0.07; DWG. NO.; REV; freETarget NAME; DATE; MFG APPR.; ENG APPR.; INTERPRET GEOMETRIC TOLERANCING PER:; ANGULAR: MACH; BEND; NEXT ASSY; USED ON

1 | 1 | FET-0211 | B-17 B-19 BOTTOM TARGET STOP | Maple | | -
ITEM NO. | QTY. | PART NUMBER | PART DESCRIPTION | MATERIAL | FINISH | NOTE NO.

UNLESS OTHERWISE SPECIFIED:

DIMENSIONS ARE IN INCHES
TOLERANCES:
FRACTIONAL
TWO PLACE DECIMAL
THREE PLACE DECIMAL
