ten-point-nine/freETarget/Mechanical/Dimensioned Drawings/50m Pistol Target/FET_200 50 METER TARGET FRAME ASSY.PDF

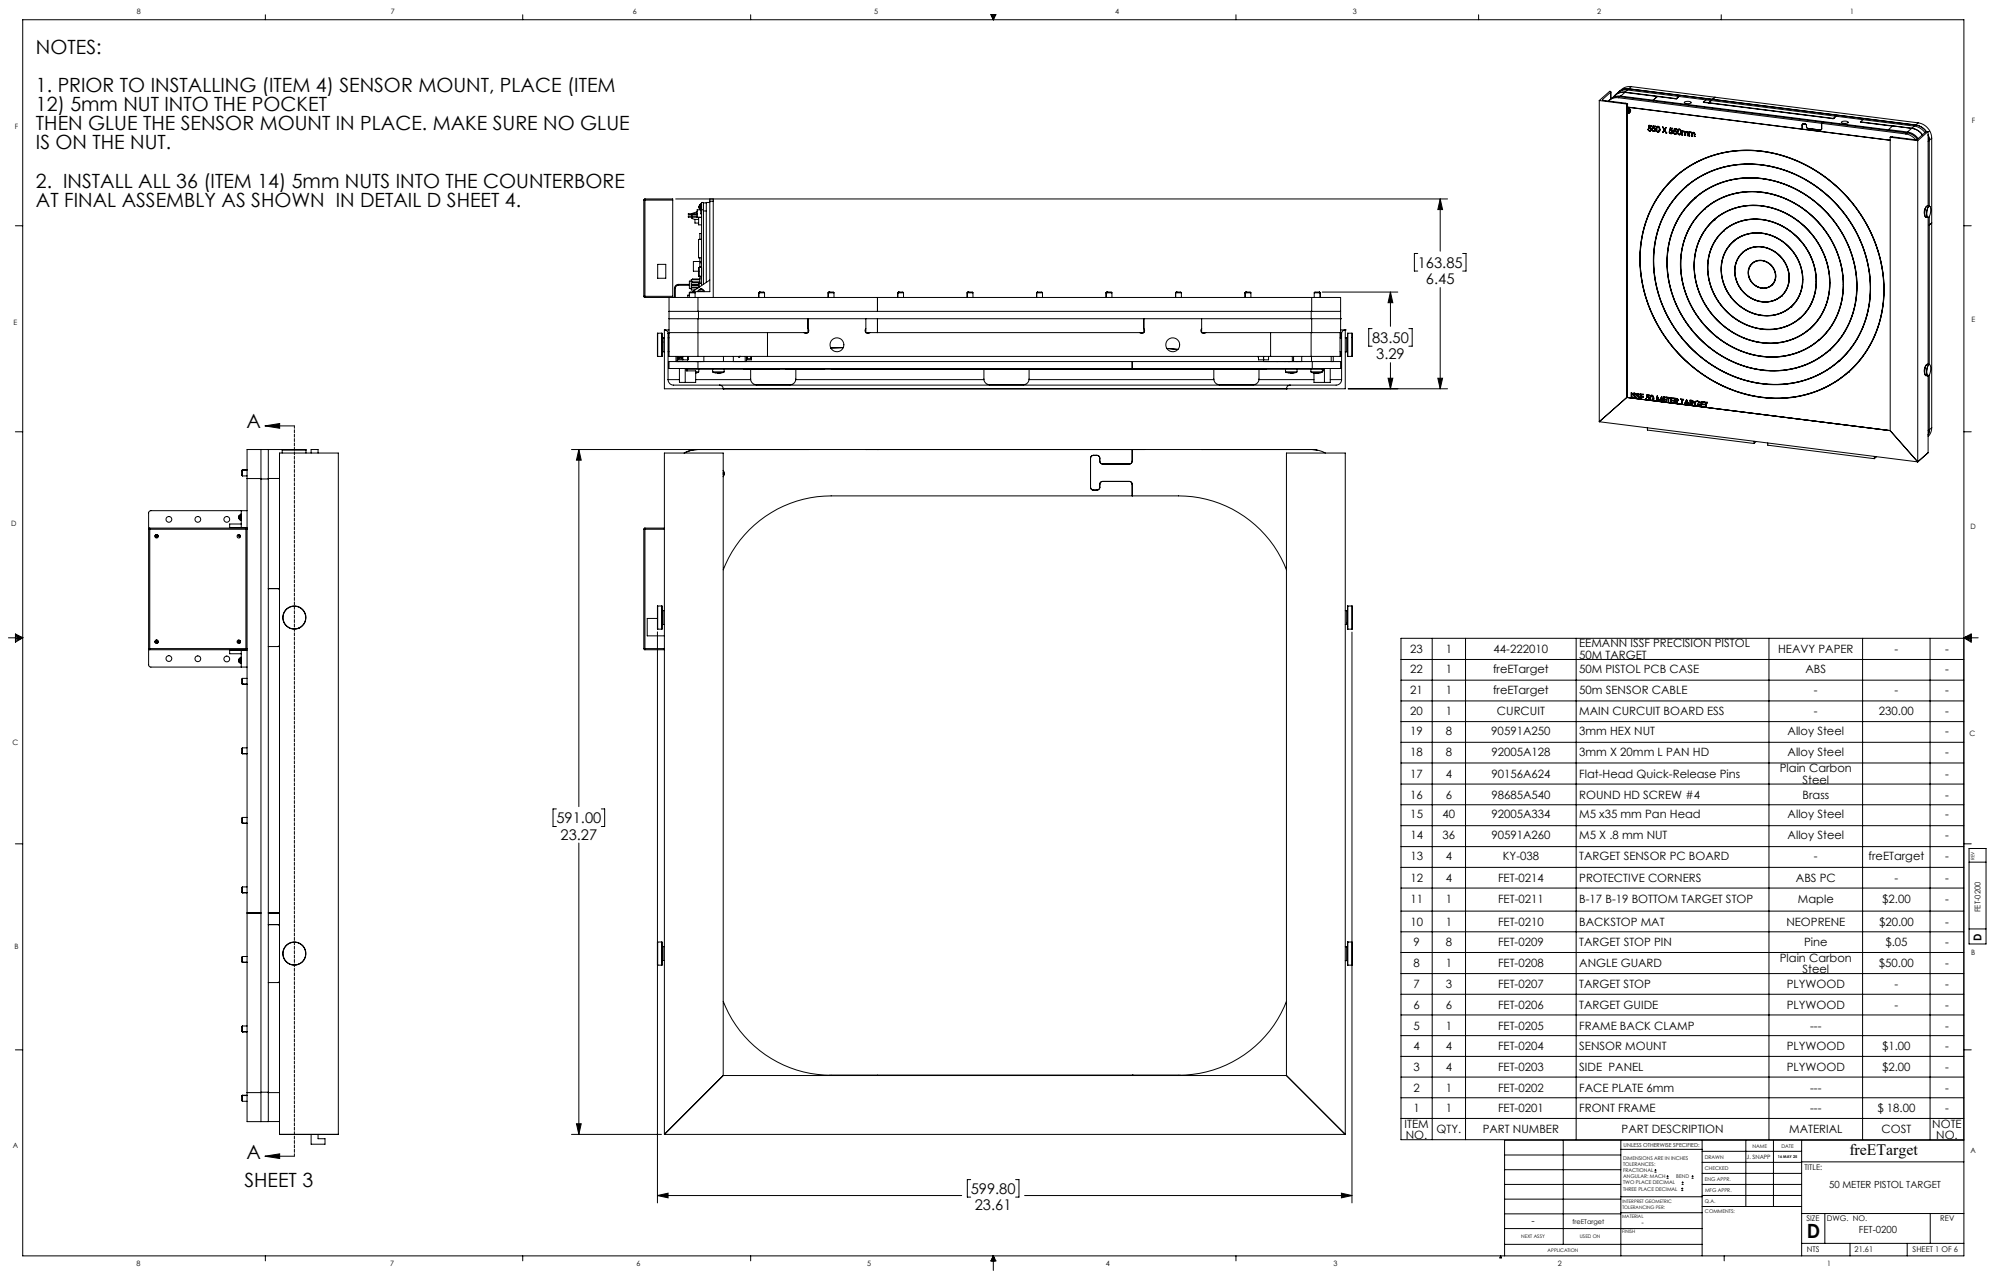
[picture p293: page 1]
SHEET 3; FREV FET-0200; SHEET 1 OF 6; 50 METER PISTOL TARGET; J. SNAPP 16 MAY 25; DWG. NO.; REV; freETarget NAME; DATE; MFG APPR.; ENG APPR.; INTERPRET GEOMETRIC TOLERANCING PER:; ANGULAR: MACH; BEND; NEXT ASSY; USED ON; - freETarget

NOTES:
1. PRIOR TO INSTALLING (ITEM 4) SENSOR MOUNT, PLACE (ITEM
12) 5mm NUT INTO THE POCKET
THEN GLUE THE SENSOR MOUNT IN PLACE. MAKE SURE NO GLUE
IS ON THE NUT.
2. INSTALL ALL 36 (ITEM 14) 5mm NUTS INTO THE COUNTERBORE
AT FINAL ASSEMBLY AS SHOWN IN DETAIL D SHEET 4.

23 | 1 | 44-222010 | EEMANN ISSF PRECISION PISTOL 50M TARGET | HEAVY PAPER | - | -
22 | 1 | freETarget | 50M PISTOL PCB CASE | ABS | | -
21 | 1 | freETarget | 50m SENSOR CABLE | - | - | -
20 | 1 | CURCUIT | MAIN CURCUIT BOARD ESS | - | 230.00 | -
19 | 8 | 90591A250 | 3mm HEX NUT | Alloy Steel | | -
18 | 8 | 92005A128 | 3mm X 20mm L PAN HD | Alloy Steel | | -
17 | 4 | 90156A624 | Flat-Head Quick-Release Pins | Plain Carbon Steel | | -
16 | 6 | 98685A540 | ROUND HD SCREW #4 | Brass | | -
15 | 40 | 92005A334 | M5 x35 mm Pan Head | Alloy Steel | | -
14 | 36 | 90591A260 | M5 X .8 mm NUT | Alloy Steel | | -
13 | 4 | KY-038 | TARGET SENSOR PC BOARD | - | freETarget | -
12 | 4 | FET-0214 | PROTECTIVE CORNERS | ABS PC | - | -
11 | 1 | FET-0211 | B-17 B-19 BOTTOM TARGET STOP | Maple | $2.00 | -
10 | 1 | FET-0210 | BACKSTOP MAT | NEOPRENE | $20.00 | -
9 | 8 | FET-0209 | TARGET STOP PIN | Pine | $.05 | -
8 | 1 | FET-0208 | ANGLE GUARD | Plain Carbon Steel | $50.00 | -
7 | 3 | FET-0207 | TARGET STOP | PLYWOOD | - | -
6 | 6 | FET-0206 | TARGET GUIDE | PLYWOOD | - | -
5 | 1 | FET-0205 | FRAME BACK CLAMP | --- | | -
4 | 4 | FET-0204 | SENSOR MOUNT | PLYWOOD | $1.00 | -
3 | 4 | FET-0203 | SIDE PANEL | PLYWOOD | $2.00 | -
2 | 1 | FET-0202 | FACE PLATE 6mm | --- | | -
1 | 1 | FET-0201 | FRONT FRAME | --- | $ 18.00 | -
ITEM NO. | QTY. | PART NUMBER | PART DESCRIPTION | MATERIAL | COST | NOTE NO.

UNLESS OTHERWISE SPECIFIED:

DIMENSIONS ARE IN INCHES
TOLERANCES:
FRACTIONAL
TWO PLACE DECIMAL
THREE PLACE DECIMAL

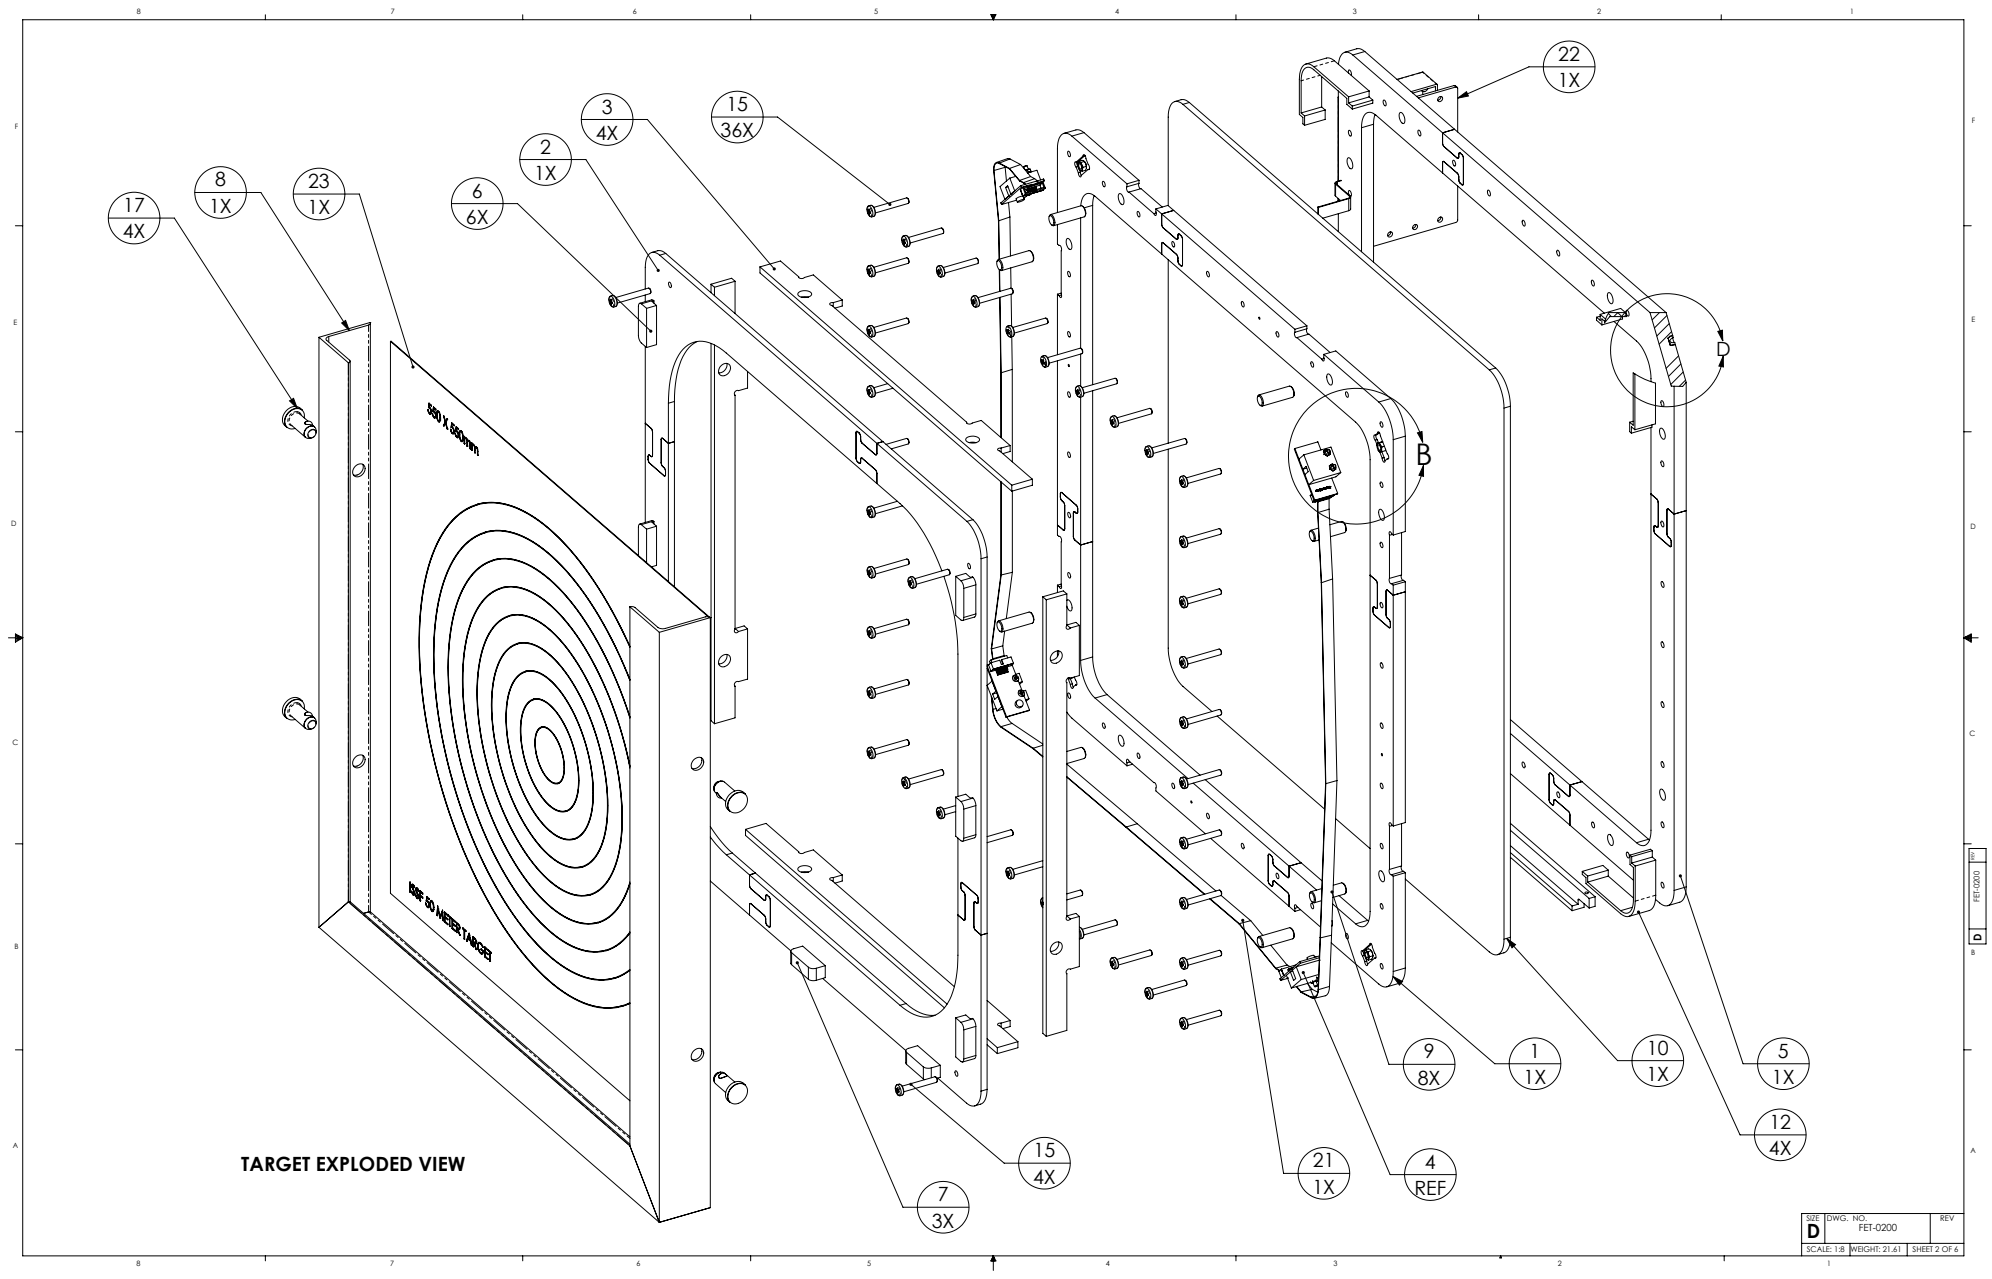
[picture p294: page 2]
FREV FET-0200

TARGET EXPLODED VIEW

SCALE: 1:8 WEIGHT: 21.61 SHEET 2 OF 6

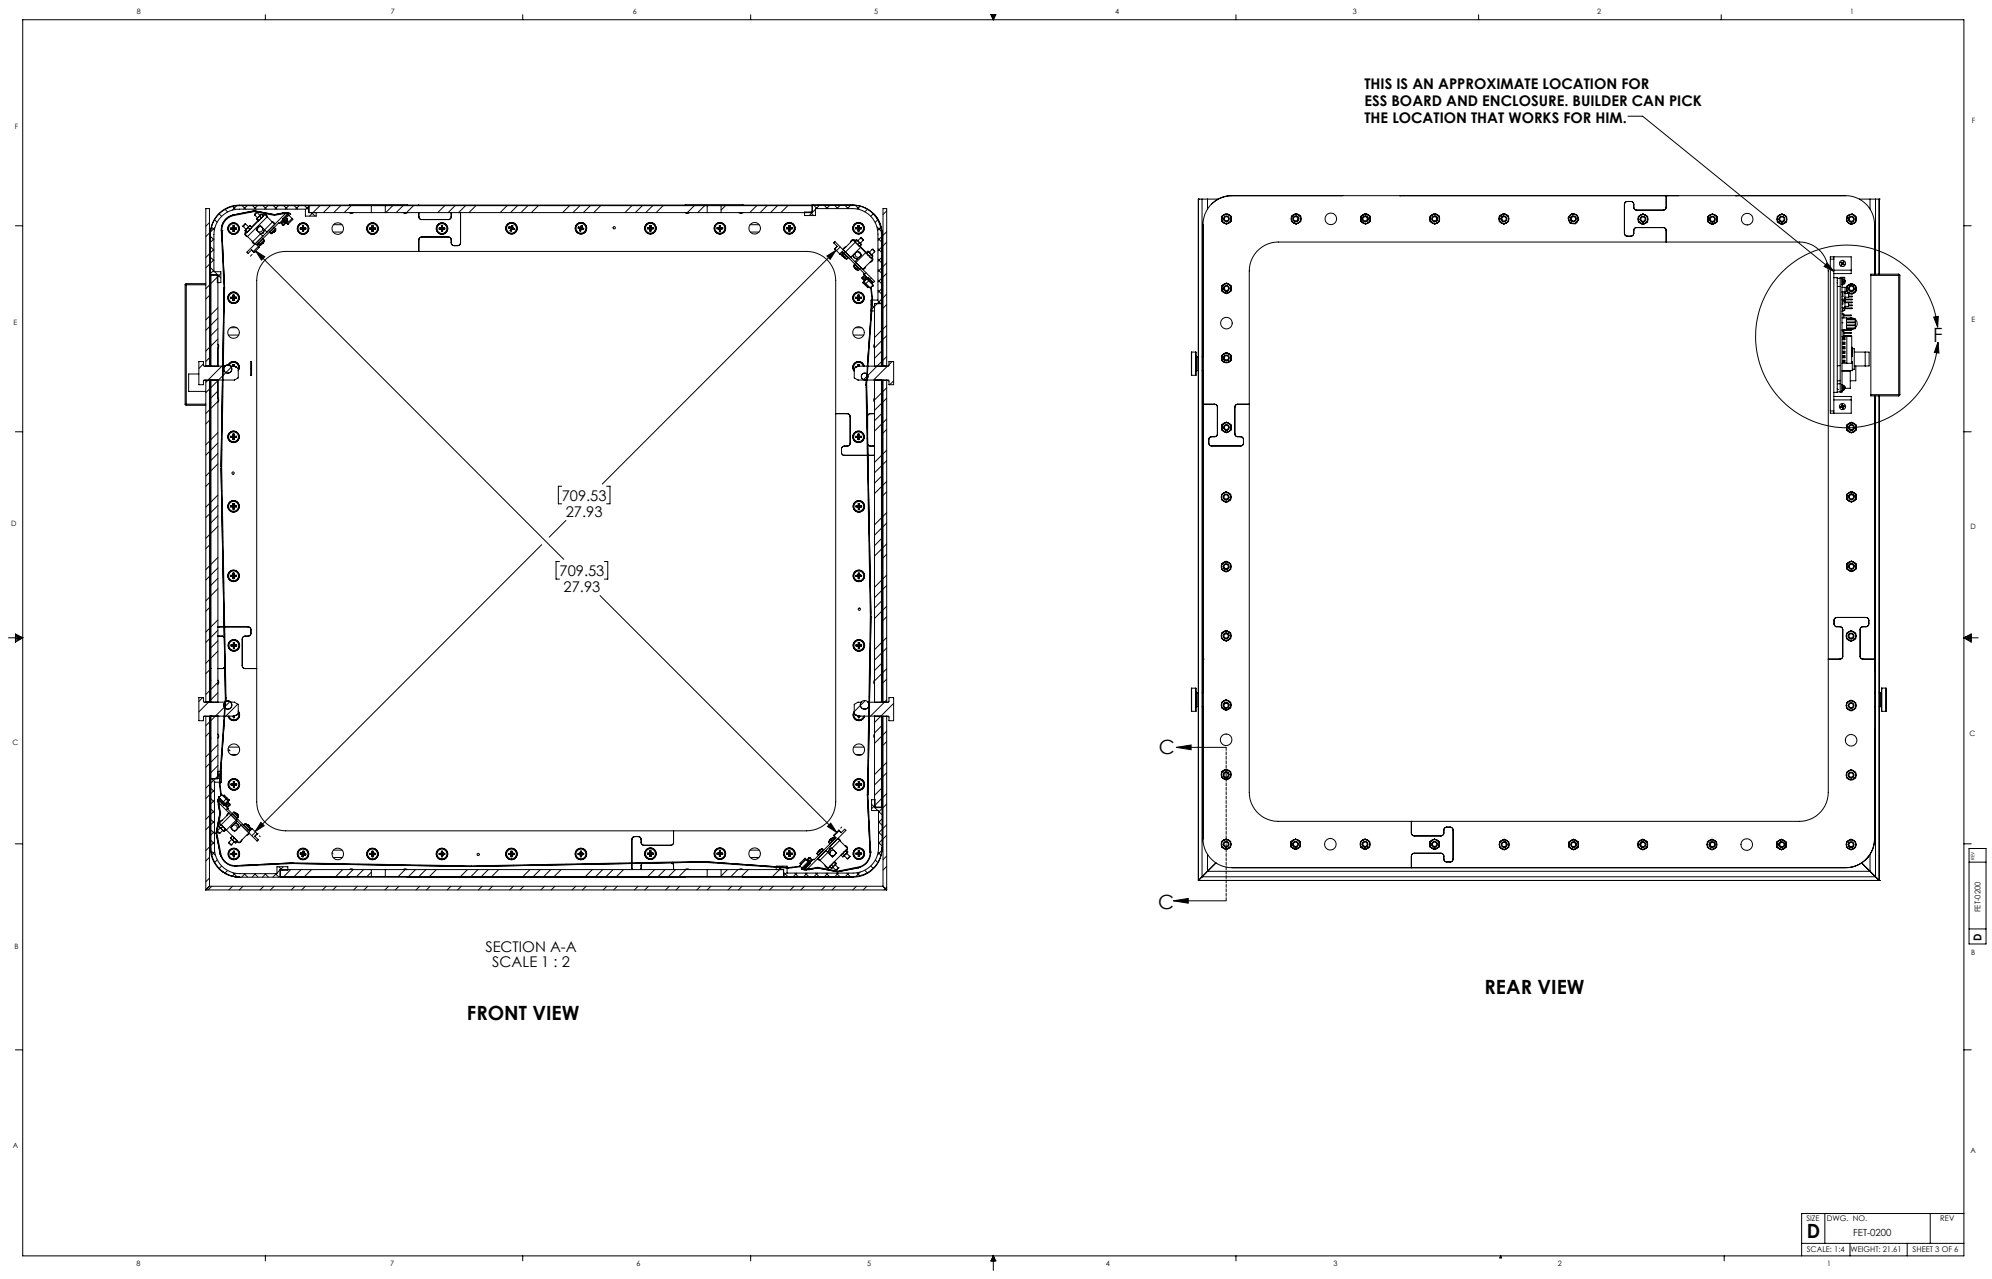
[picture p295: page 3]
SECTION A-A SCALE 1 : 2; FRONT VIEW; REAR VIEW; FREV FET-0200

THIS IS AN APPROXIMATE LOCATION FOR
ESS BOARD AND ENCLOSURE. BUILDER CAN PICK
THE LOCATION THAT WORKS FOR HIM.

SCALE: 1:4 WEIGHT: 21.61 SHEET 3 OF 6

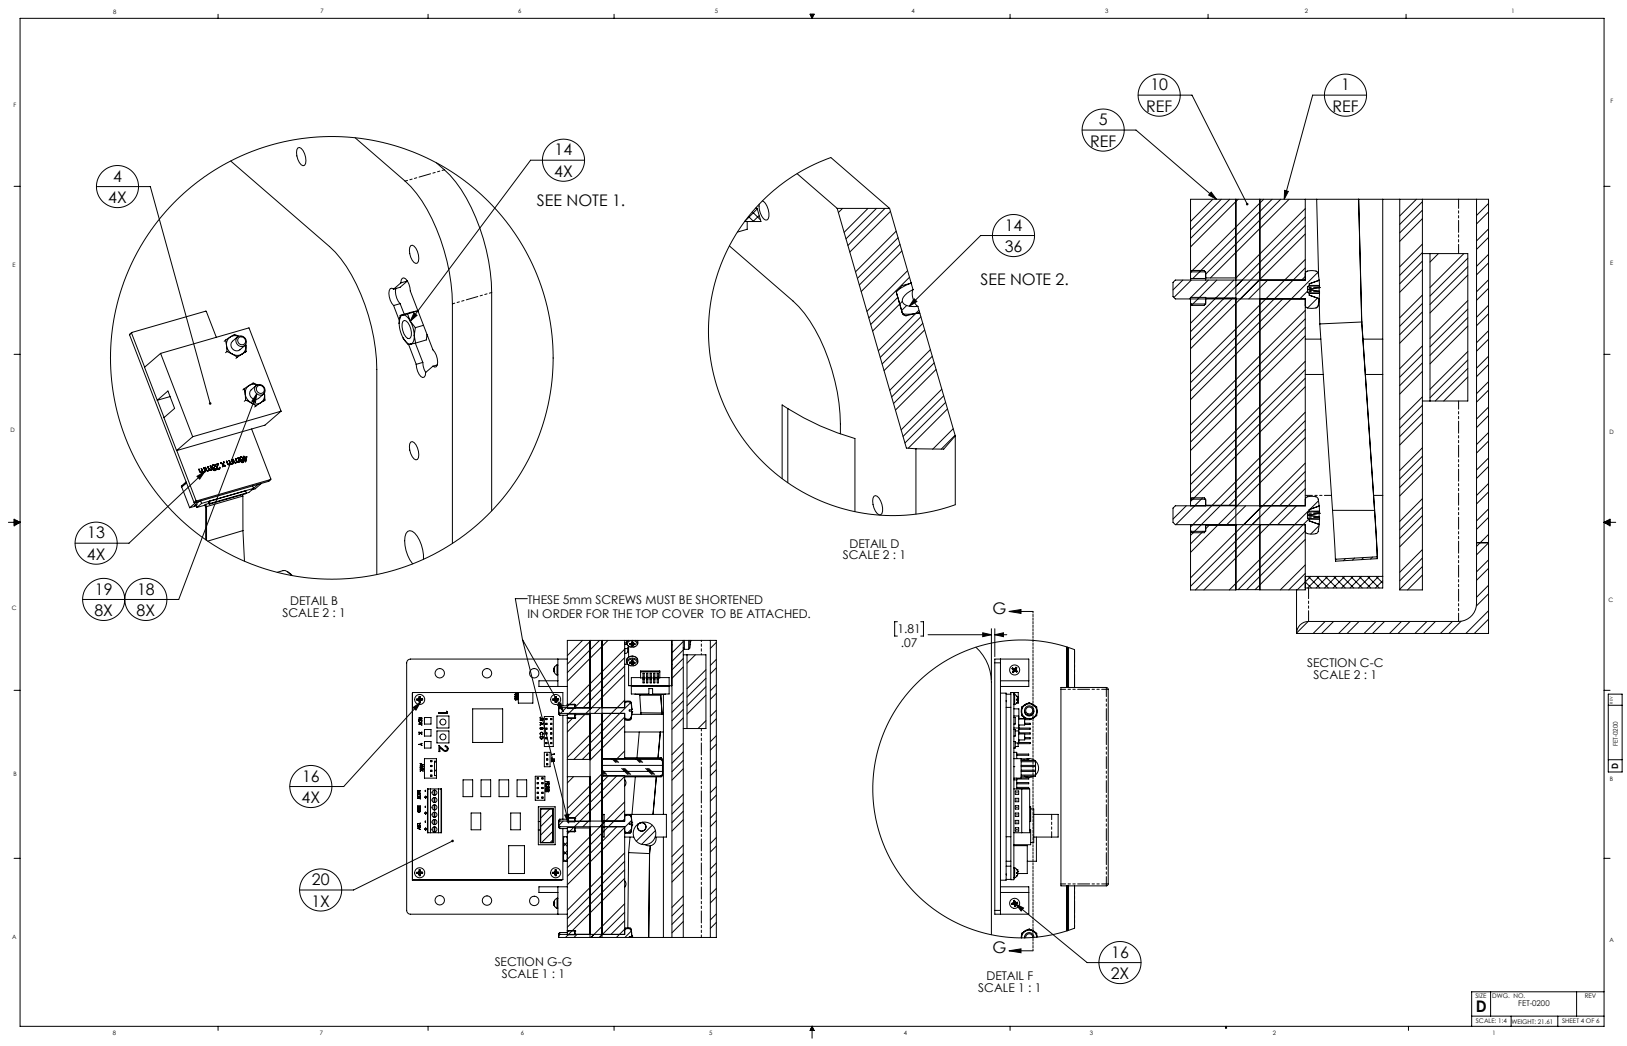
[picture p296: page 4]
DETAIL B SCALE 2 : 1; SEE NOTE 1.; SECTION C-C SCALE 2 : 1; DETAIL D SCALE 2 : 1; SEE NOTE 2.; DETAIL F SCALE 1 : 1; SECTION G-G SCALE 1 : 1; FREV FET-0200

THESE 5mm SCREWS MUST BE SHORTENED
IN ORDER FOR THE TOP COVER TO BE ATTACHED.

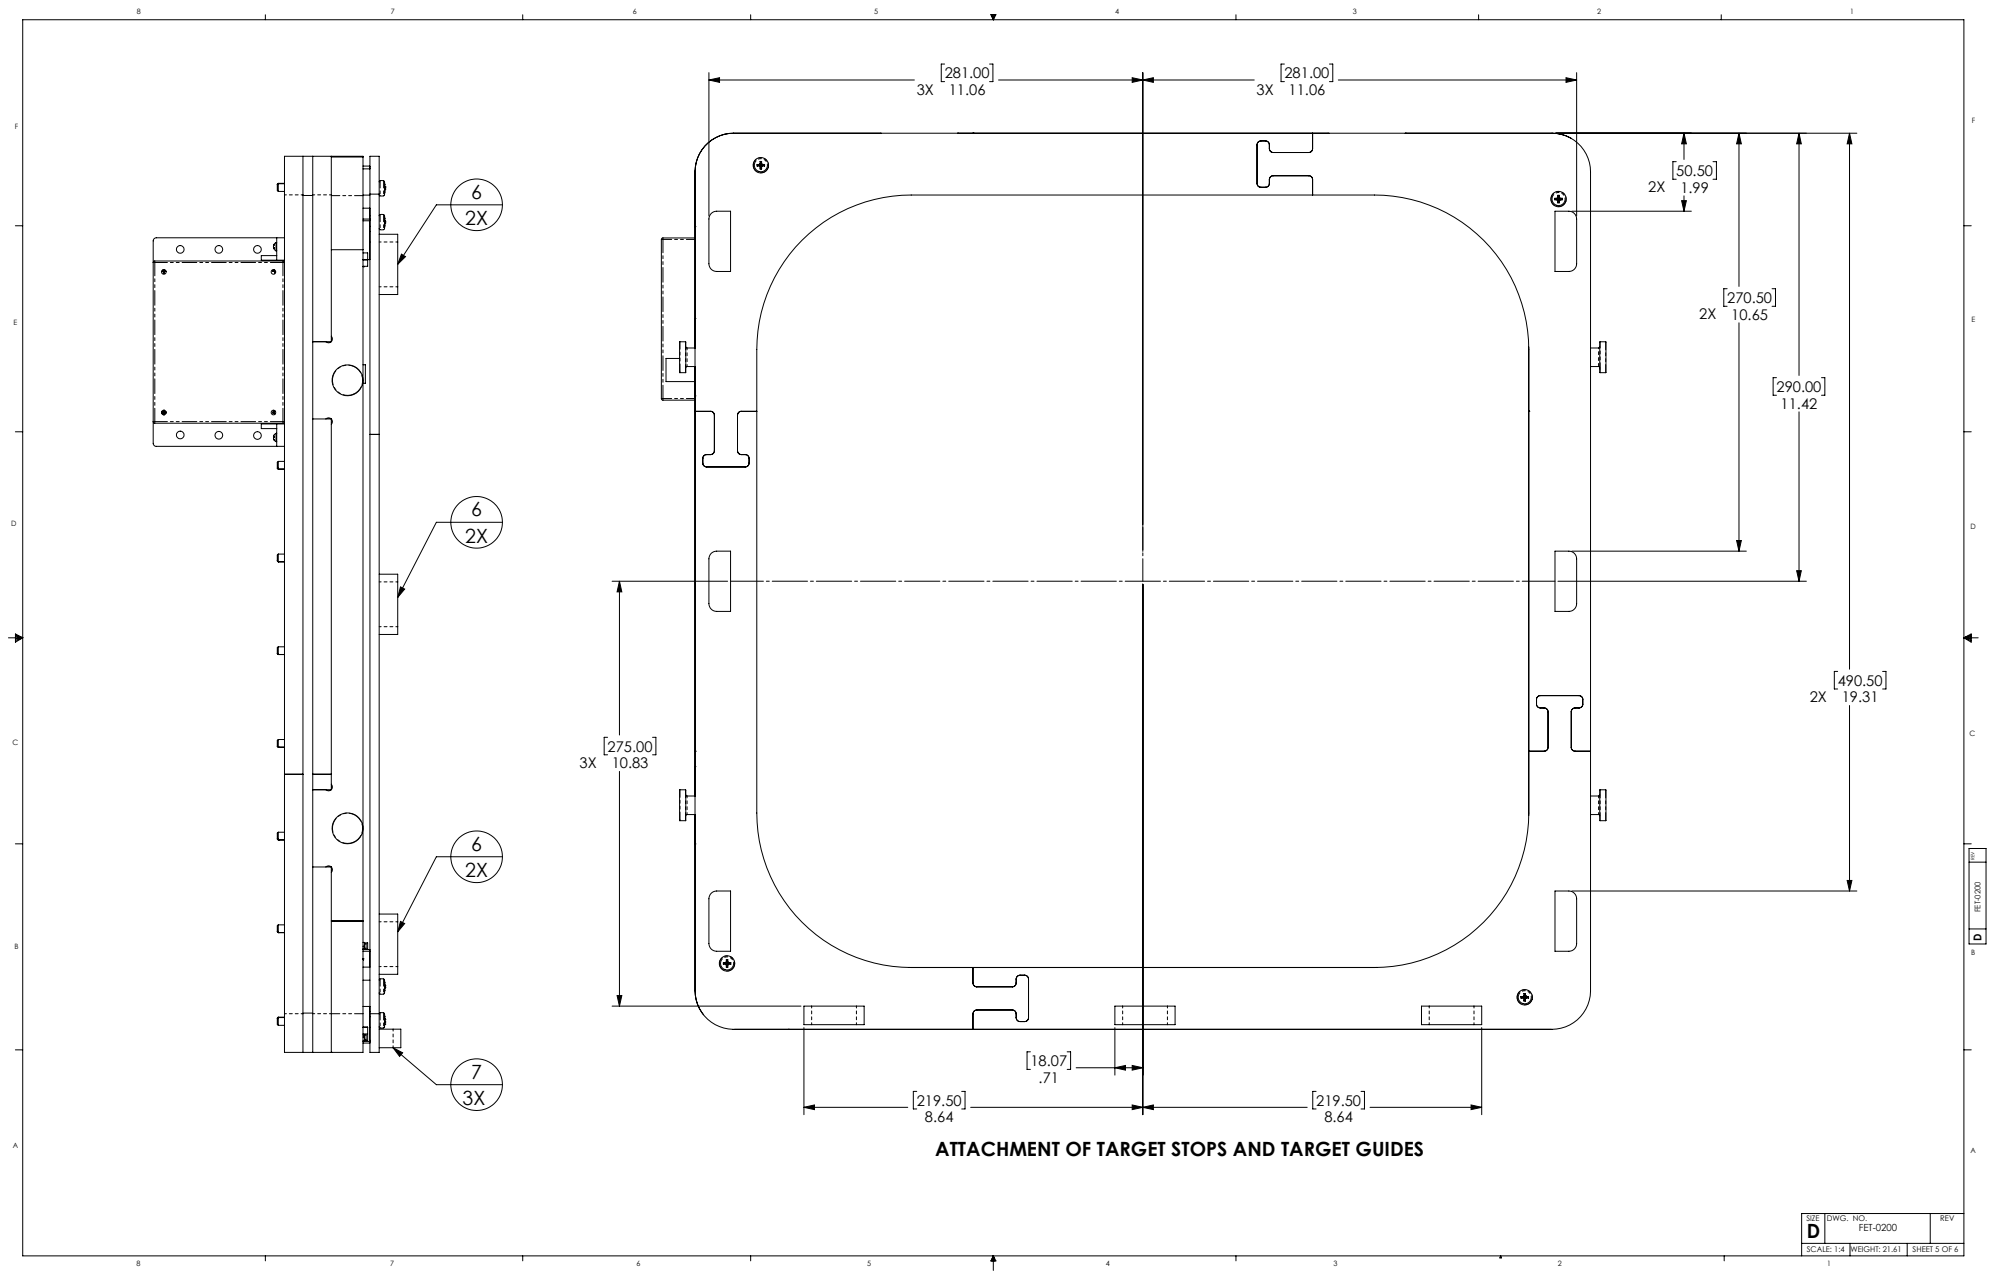
[picture p297: page 5]
FREV FET-0200

ATTACHMENT OF TARGET STOPS AND TARGET GUIDES

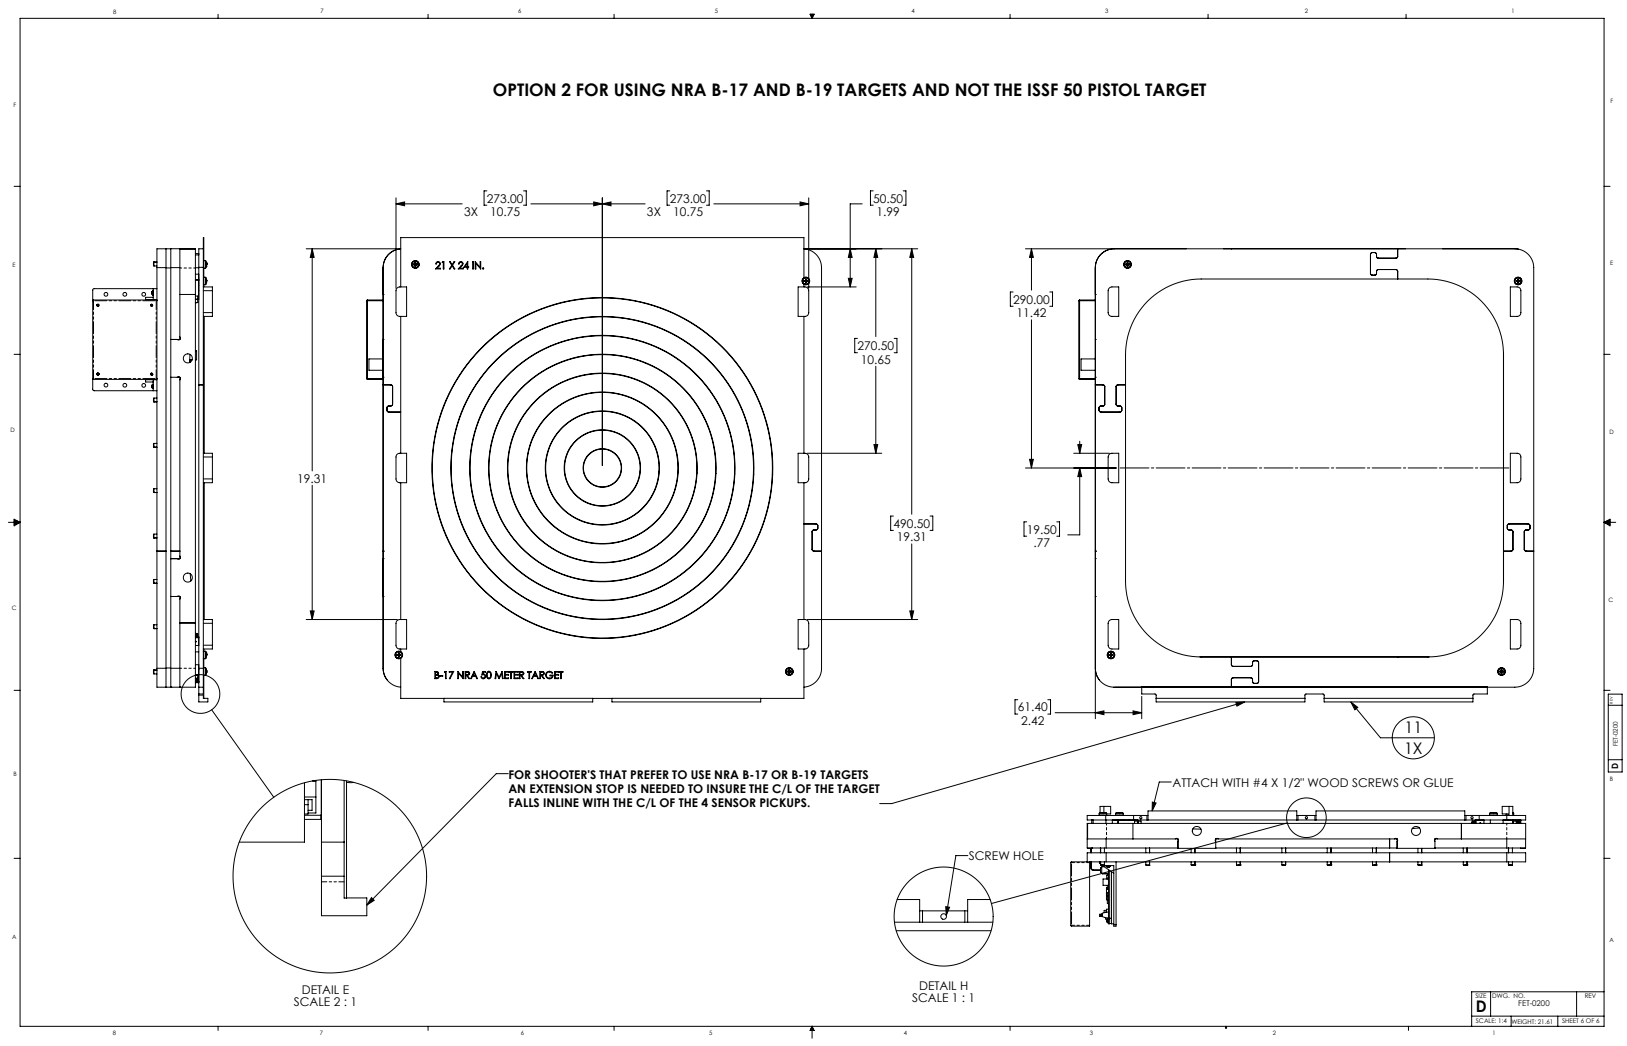
[picture p298: page 6]
DETAIL E SCALE 2 : 1; DETAIL H SCALE 1 : 1; SCREW HOLE; FREV FET-0200

OPTION 2 FOR USING NRA B-17 AND B-19 TARGETS AND NOT THE ISSF 50 PISTOL TARGET

FOR SHOOTER'S THAT PREFER TO USE NRA B-17 OR B-19 TARGETS
AN EXTENSION STOP IS NEEDED TO INSURE THE C/L OF THE TARGET
FALLS INLINE WITH THE C/L OF THE 4 SENSOR PICKUPS.

ATTACH WITH #4 X 1/2" WOOD SCREWS OR GLUE
