ten-point-nine/freETarget/Mechanical/Community Parts/Mechanical Drawings/FET-045 PAPER TRANSPORT ASSY.PDF

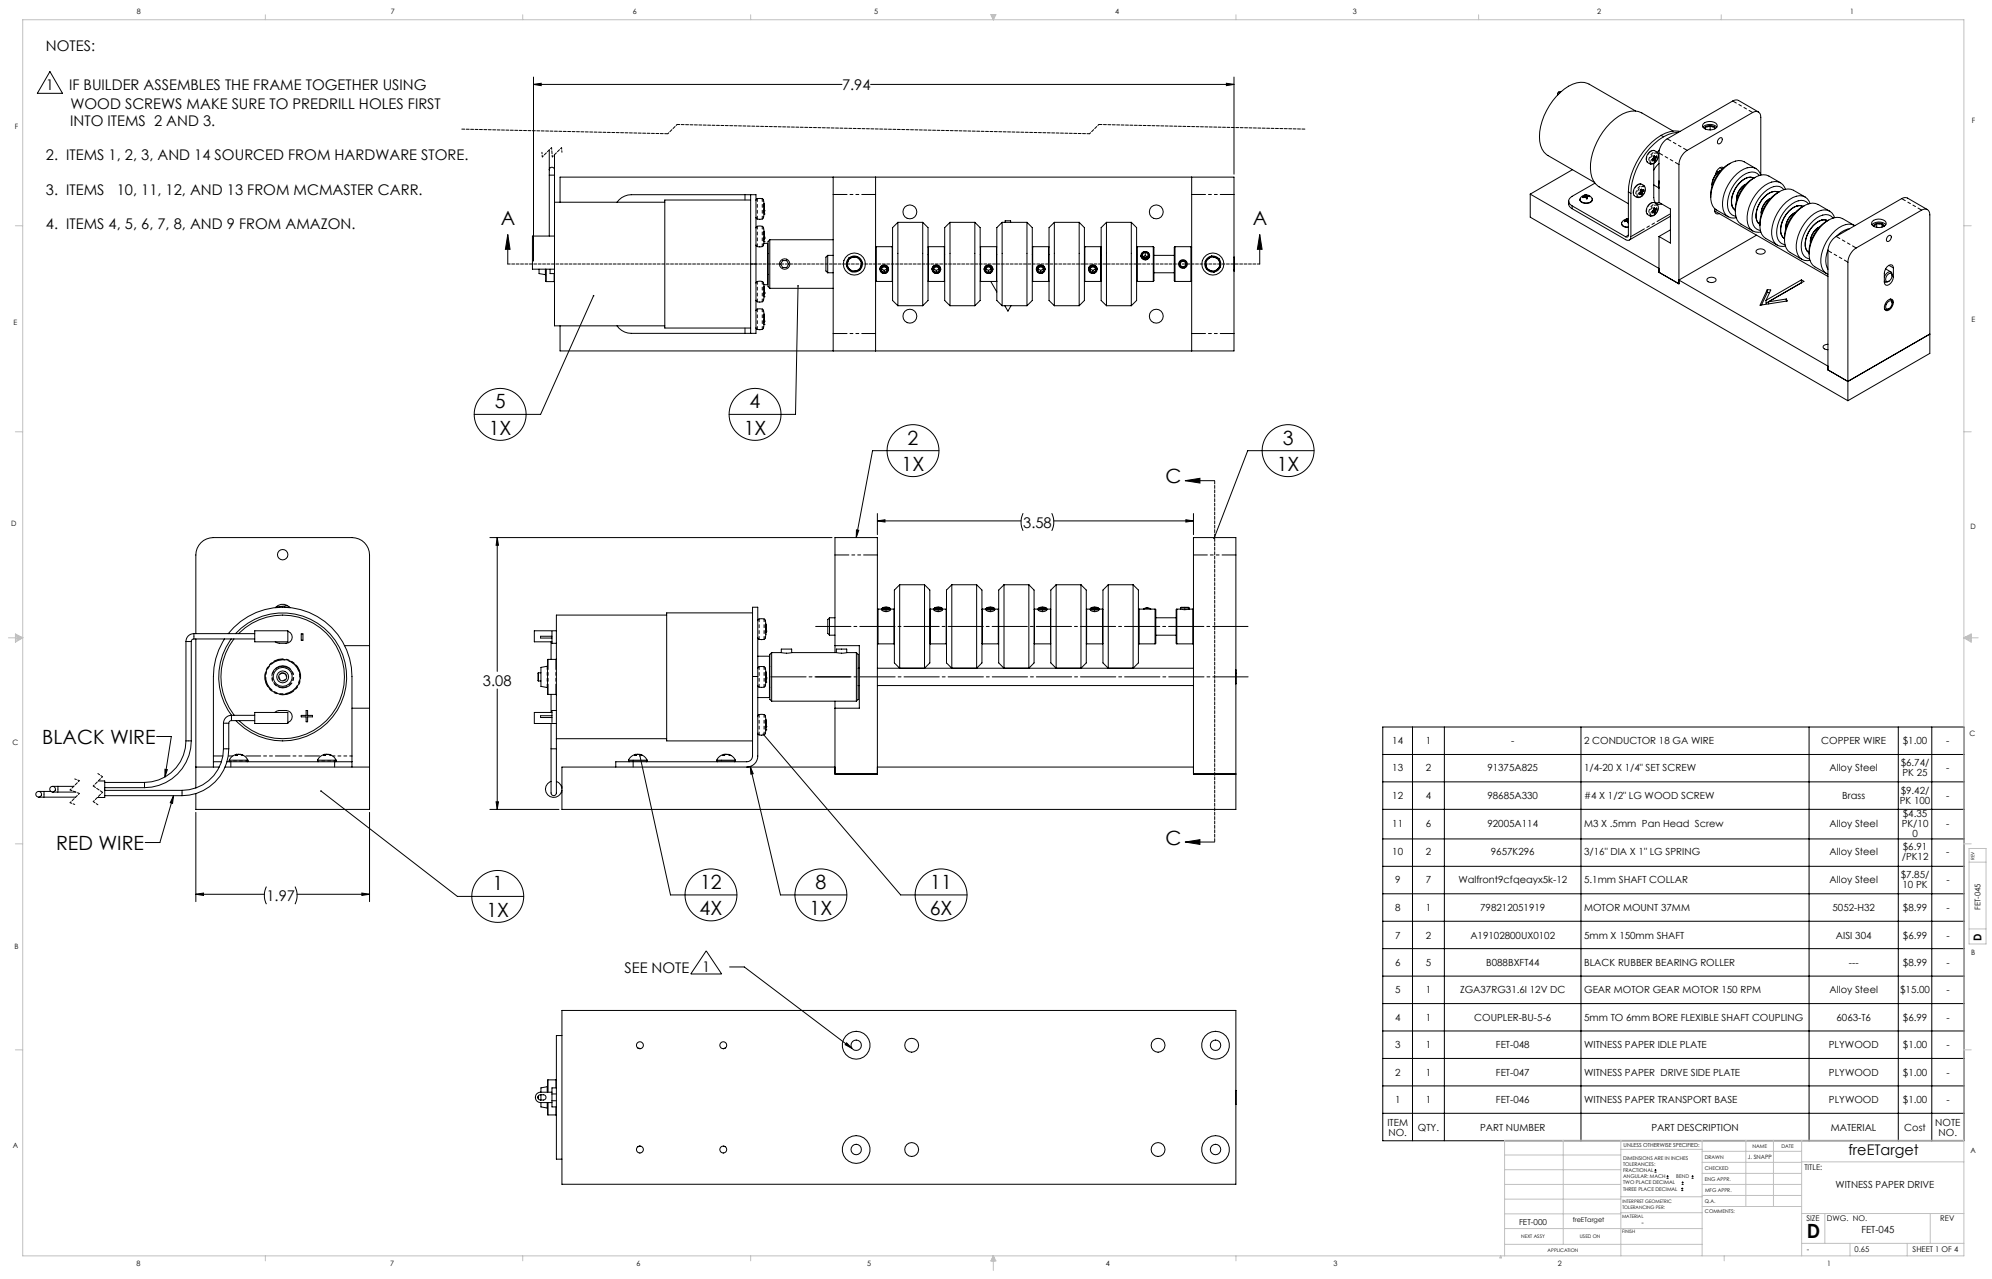
[picture p299: page 1]
RED WIRE; BLACK WIRE; SEE NOTE 1; FREV FET-045; SHEET 1 OF 4; WITNESS PAPER DRIVE; J. SNAPP; DWG. NO.; REV; freETarget NAME; DATE; MFG APPR.; ENG APPR.; INTERPRET GEOMETRIC TOLERANCING PER:; ANGULAR: MACH; BEND; NEXT ASSY; USED ON

1 IF BUILDER ASSEMBLES THE FRAME TOGETHER USING
WOOD SCREWS MAKE SURE TO PREDRILL HOLES FIRST
INTO ITEMS 2 AND 3.
2. ITEMS 1, 2, 3, AND 14 SOURCED FROM HARDWARE STORE.
3. ITEMS 10, 11, 12, AND 13 FROM MCMASTER CARR.
4. ITEMS 4, 5, 6, 7, 8, AND 9 FROM AMAZON.

14 | 1 | - | 2 CONDUCTOR 18 GA WIRE | COPPER WIRE | $1.00 | -
13 | 2 | 91375A825 | 1/4-20 X 1/4" SET SCREW | Alloy Steel | $6.74/ PK 25 | -

12 | 4 | 98685A330 | #4 X 1/2" LG WOOD SCREW | Brass | $9.42/ PK 100 | -
11 | 6 | 92005A114 | M3 X .5mm Pan Head Screw | Alloy Steel | $4.35 PK/10 0 | -

10 | 2 | 9657K296 | 3/16" DIA X 1" LG SPRING | Alloy Steel | $6.91 /PK12 | -

9 | 7 | Walfront9cfqeayx5k-12 | 5.1mm SHAFT COLLAR | Alloy Steel | $7.85/ 10 PK | -

8 | 1 | 798212051919 | MOTOR MOUNT 37MM | 5052-H32 | $8.99 | -

7 | 2 | A19102800UX0102 | 5mm X 150mm SHAFT | AISI 304 | $6.99 | -

6 | 5 | B088BXFT44 | BLACK RUBBER BEARING ROLLER | --- | $8.99 | -

5 | 1 | ZGA37RG31.6I 12V DC | GEAR MOTOR GEAR MOTOR 150 RPM | Alloy Steel | $15.00 | -

4 | 1 | COUPLER-BU-5-6 | 5mm TO 6mm BORE FLEXIBLE SHAFT COUPLING | 6063-T6 | $6.99 | -

3 | 1 | FET-048 | WITNESS PAPER IDLE PLATE | PLYWOOD | $1.00 | -

2 | 1 | FET-047 | WITNESS PAPER DRIVE SIDE PLATE | PLYWOOD | $1.00 | -

1 | 1 | FET-046 | WITNESS PAPER TRANSPORT BASE | PLYWOOD | $1.00 | -
ITEM NO. | QTY. | PART NUMBER | PART DESCRIPTION | MATERIAL | Cost | NOTE NO.

UNLESS OTHERWISE SPECIFIED:

DIMENSIONS ARE IN INCHES
TOLERANCES:
FRACTIONAL
TWO PLACE DECIMAL
THREE PLACE DECIMAL

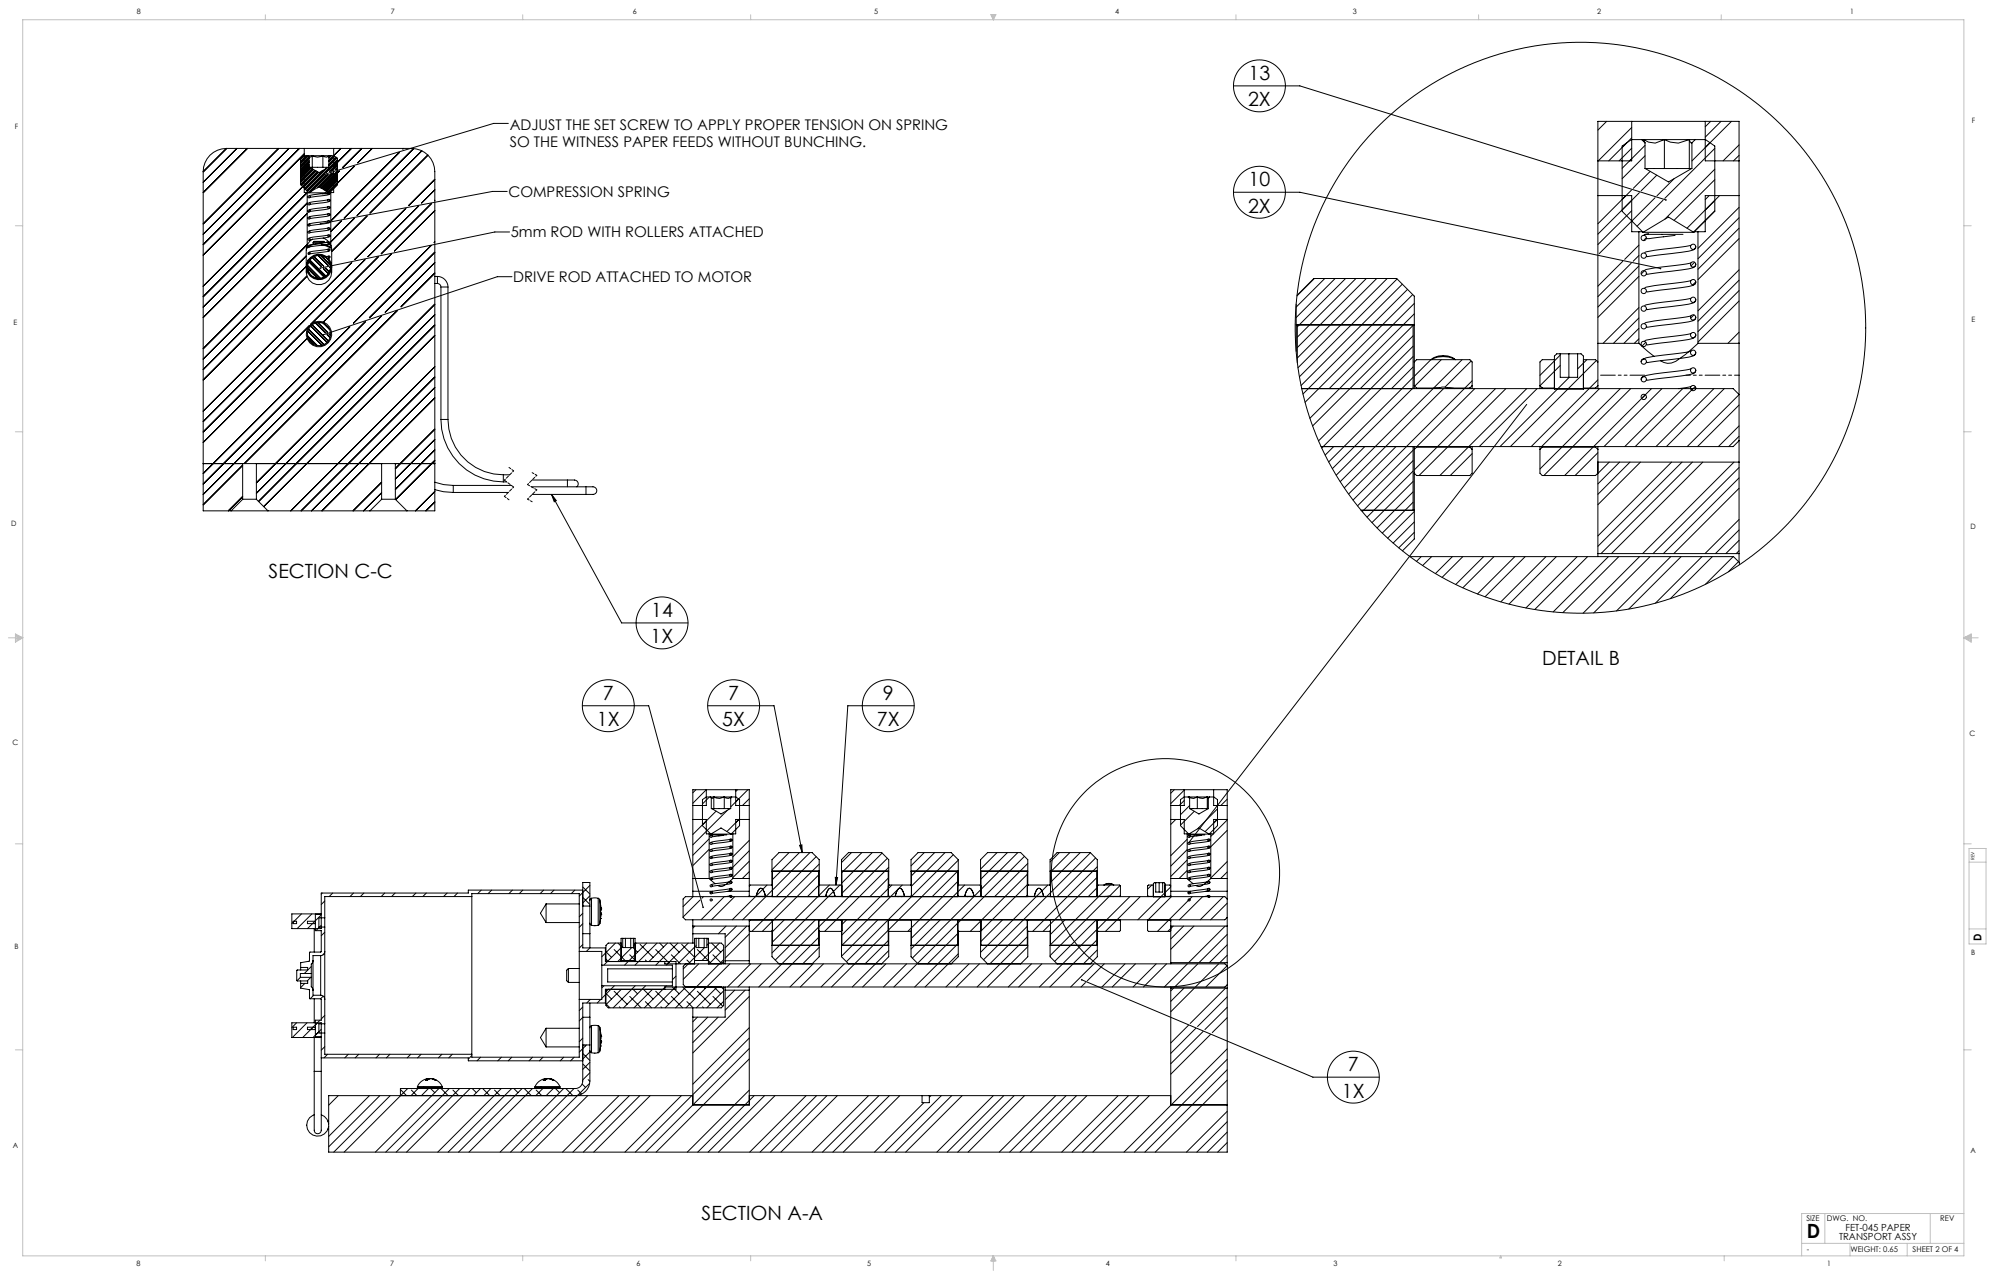
[picture p300: page 2]
SECTION A-A; DETAIL B; SECTION C-C; COMPRESSION SPRING; FET-045 PAPER TRANSPORT ASSY; WEIGHT: 0.65; SHEET 2 OF 4

ADJUST THE SET SCREW TO APPLY PROPER TENSION ON SPRING
SO THE WITNESS PAPER FEEDS WITHOUT BUNCHING.

5mm ROD WITH ROLLERS ATTACHED

DRIVE ROD ATTACHED TO MOTOR

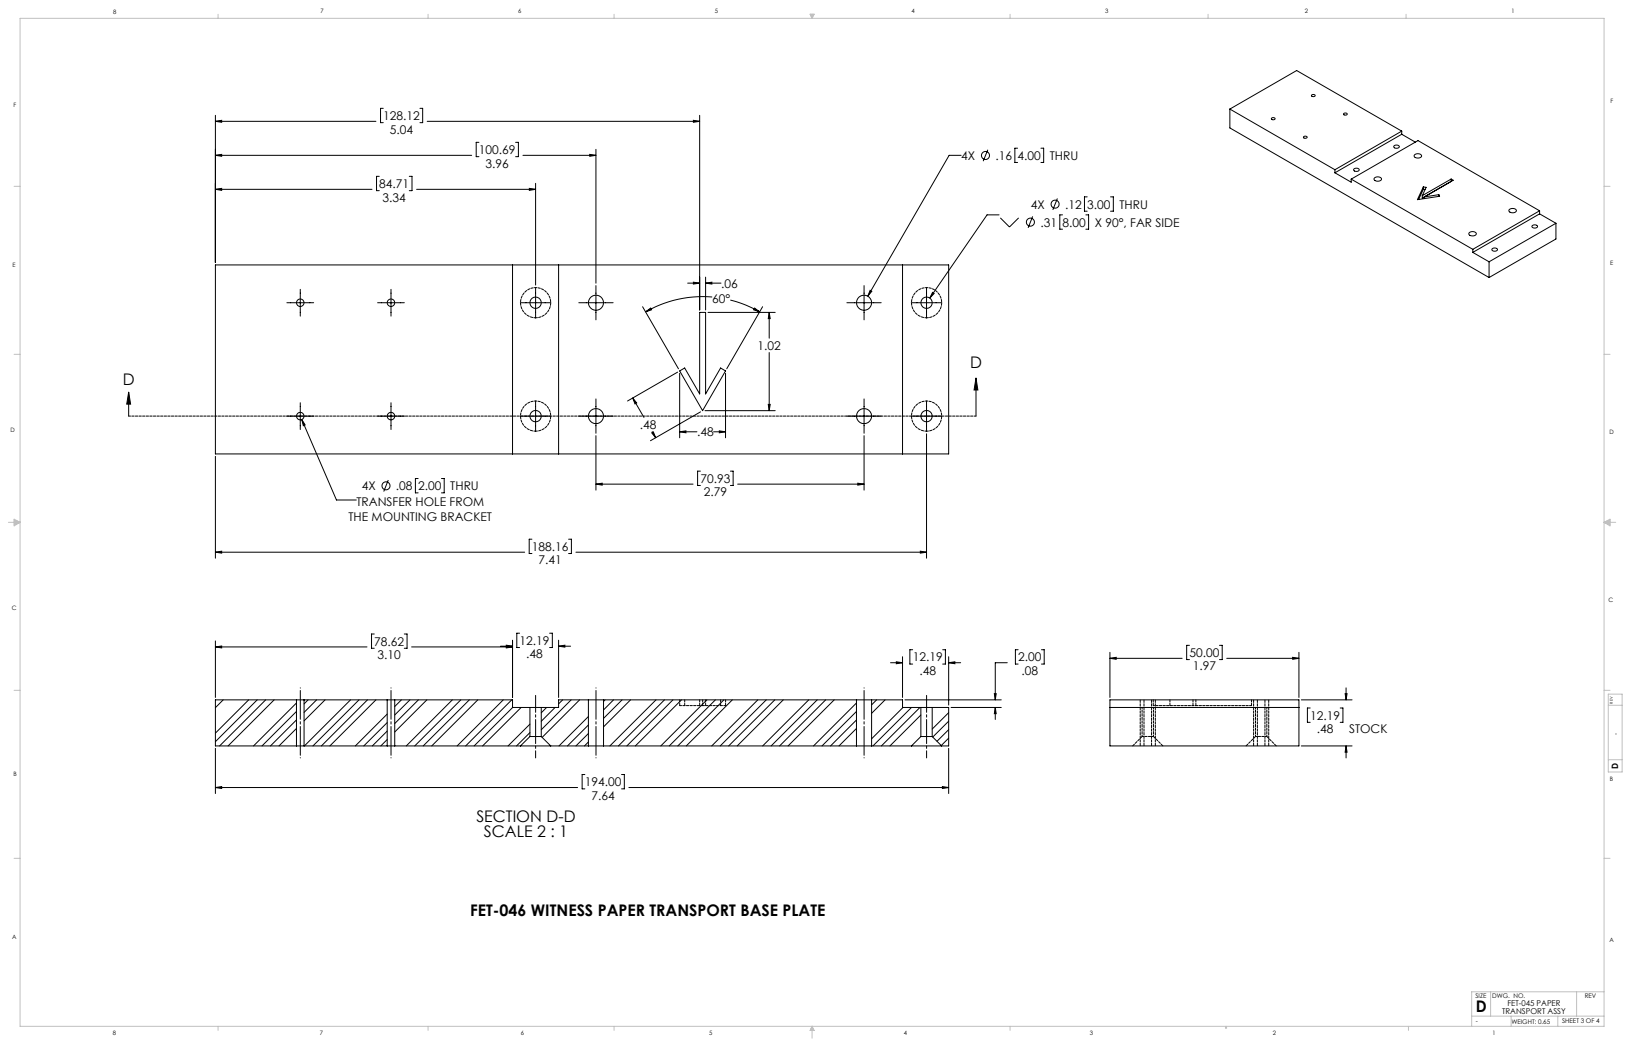
[picture p301: page 3]
.08 2.00 THRU; .16 4.00 THRU; .12 3.00 THRU; .31 8.00 X 90°, FAR SIDE; SECTION D-D SCALE 2 : 1; .48 STOCK; WEIGHT: 0.65; SHEET 3 OF 4

TRANSFER HOLE FROM
THE MOUNTING BRACKET

FET-046 WITNESS PAPER TRANSPORT BASE PLATE

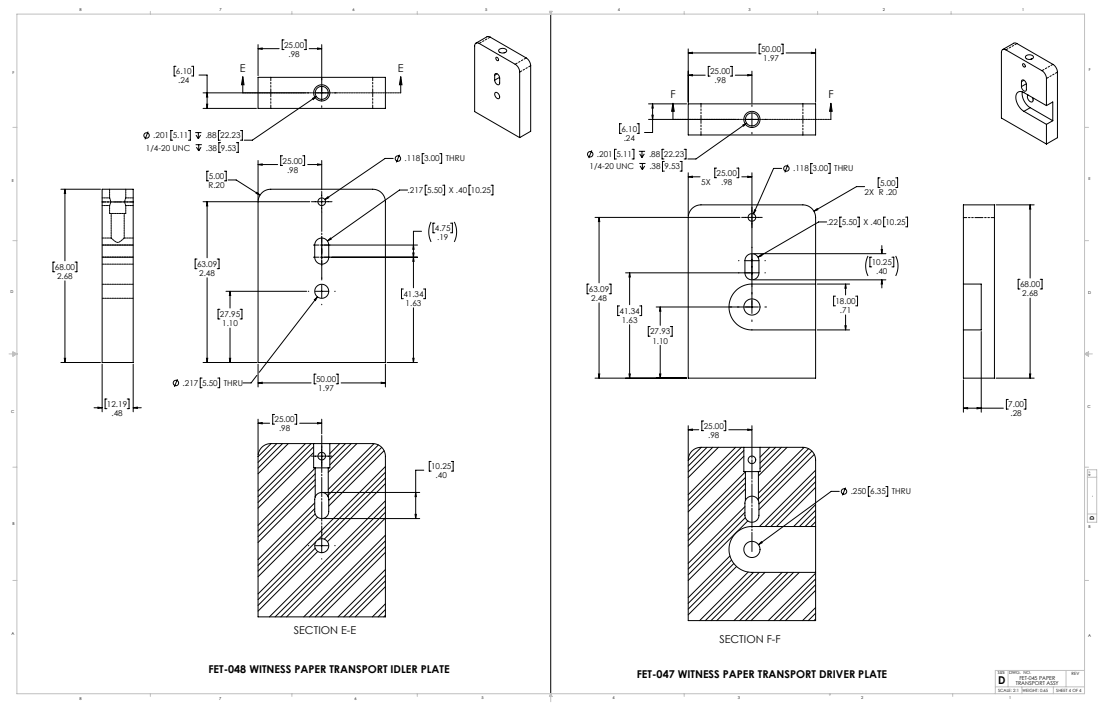
[picture p302: page 4]
.118 3.00 THRU; .217 5.50 THRU; 1/4-20 UNC; SECTION E-E; .250 6.35 THRU; SECTION F-F; FET-048 WITNESS PAPER TRANSPORT IDLER PLATE; FET-047 WITNESS PAPER TRANSPORT DRIVER PLATE; SCALE: 2:1 WEIGHT: 0.65; SHEET 4 OF 4
