ten-point-nine/freETarget/Mechanical/Dimensioned Drawings/Competition Target/FET-002 5mm FRONT DOOR PANEL.PDF

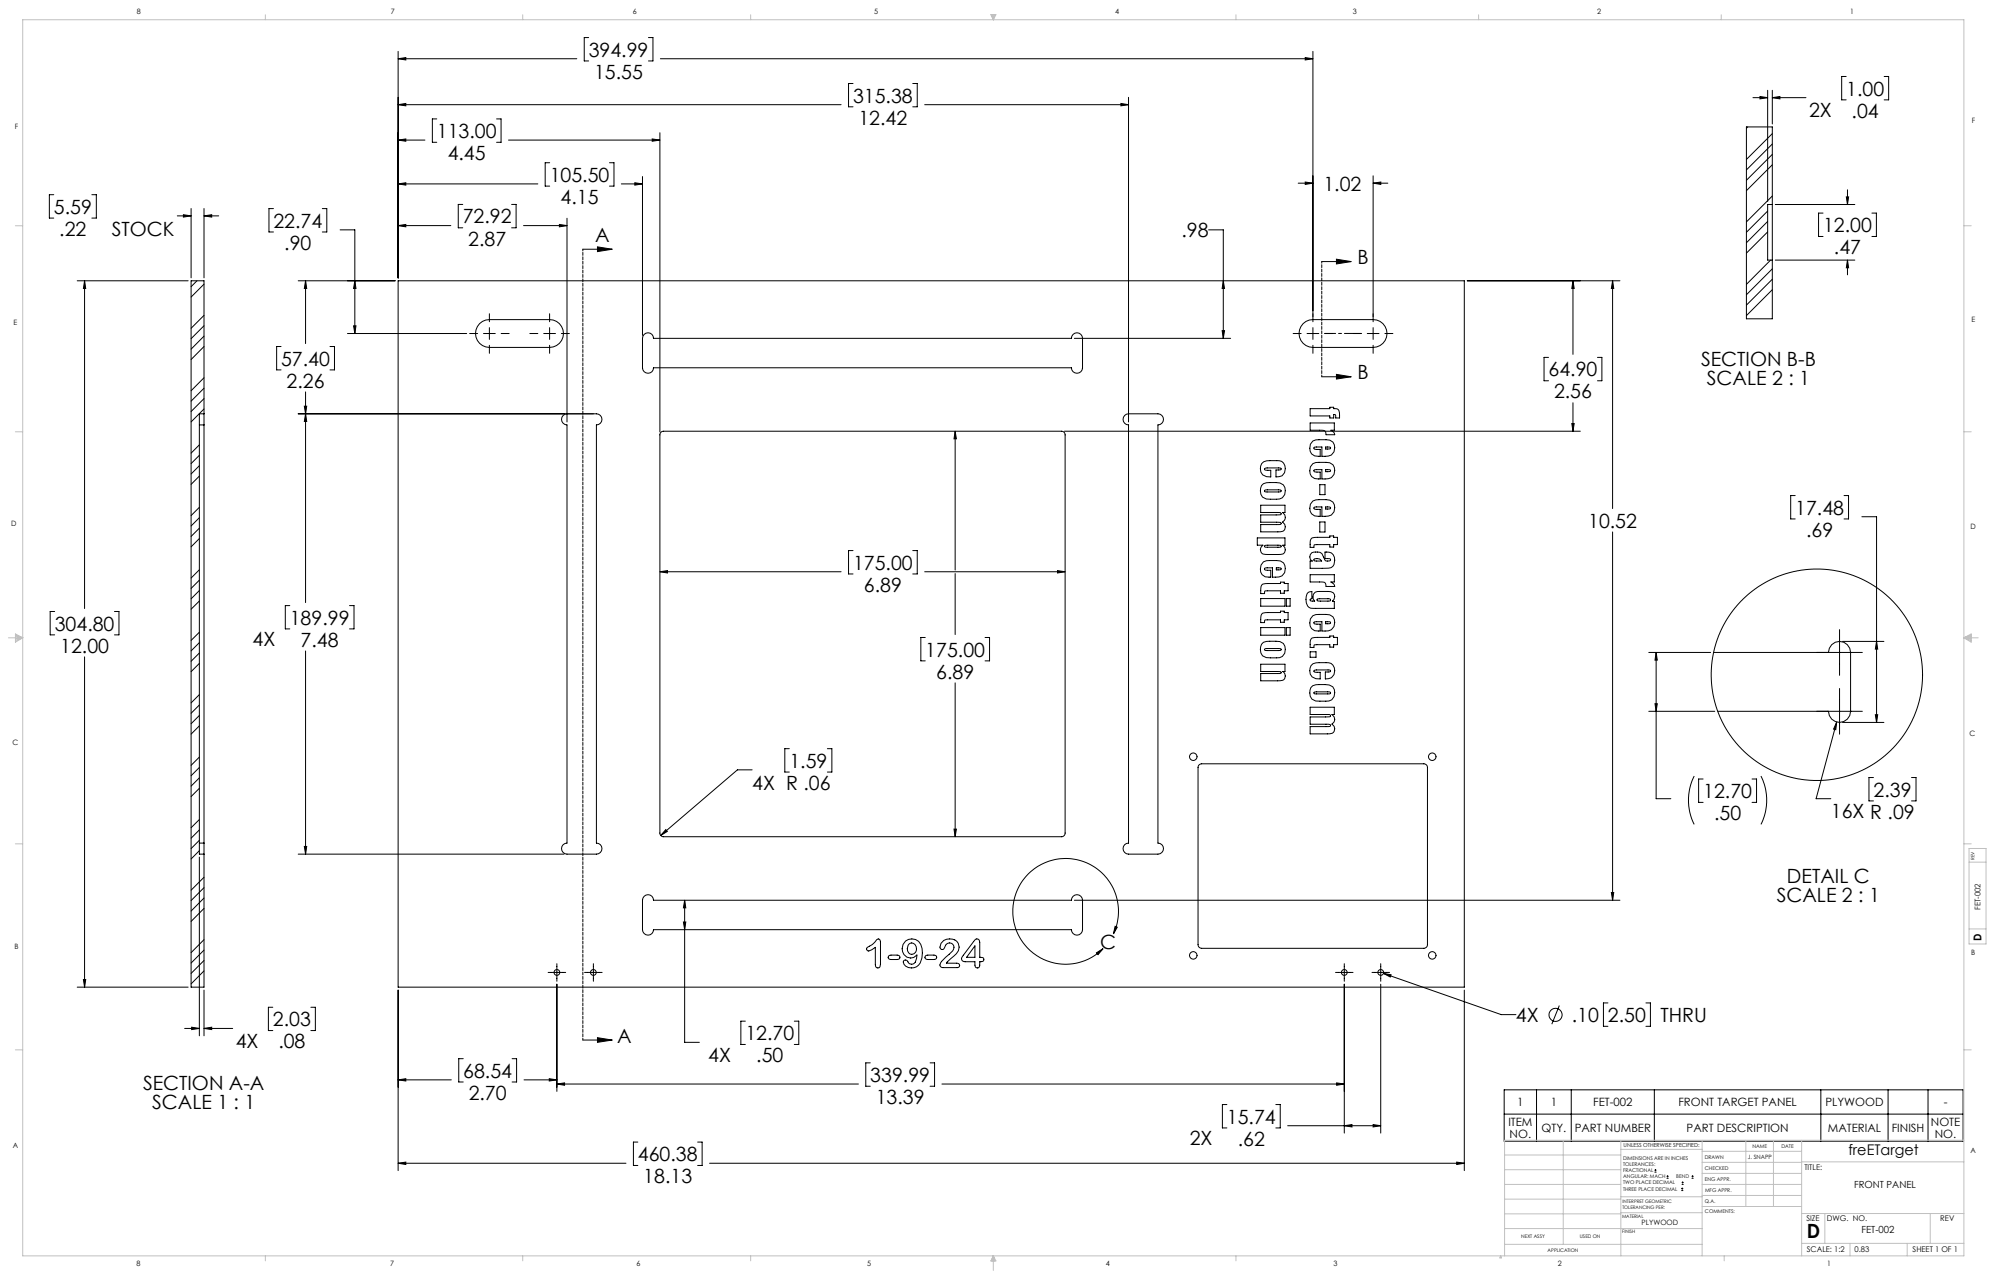
[picture p303: page 1]
.10 2.50 THRU; .22 STOCK; SECTION A-A SCALE 1 : 1; SECTION B-B SCALE 2 : 1; DETAIL C SCALE 2 : 1; FREV FET-002; SHEET 1 OF 1; FRONT PANEL; J. SNAPP; SCALE: 1:2 0.83; DWG. NO.; REV; freETarget NAME; DATE; MFG APPR.; ENG APPR.; INTERPRET GEOMETRIC TOLERANCING PER:; ANGULAR: MACH; BEND; NEXT ASSY; USED ON

1 | 1 | FET-002 | FRONT TARGET PANEL | PLYWOOD | | -
ITEM NO. | QTY. | PART NUMBER | PART DESCRIPTION | MATERIAL | FINISH | NOTE NO.

UNLESS OTHERWISE SPECIFIED:

DIMENSIONS ARE IN INCHES
TOLERANCES:
FRACTIONAL
TWO PLACE DECIMAL
THREE PLACE DECIMAL
