ten-point-nine/freETarget/Mechanical/Dimensioned Drawings/Competition Target/FET-004 5mm TARGET BACK PLATE.PDF

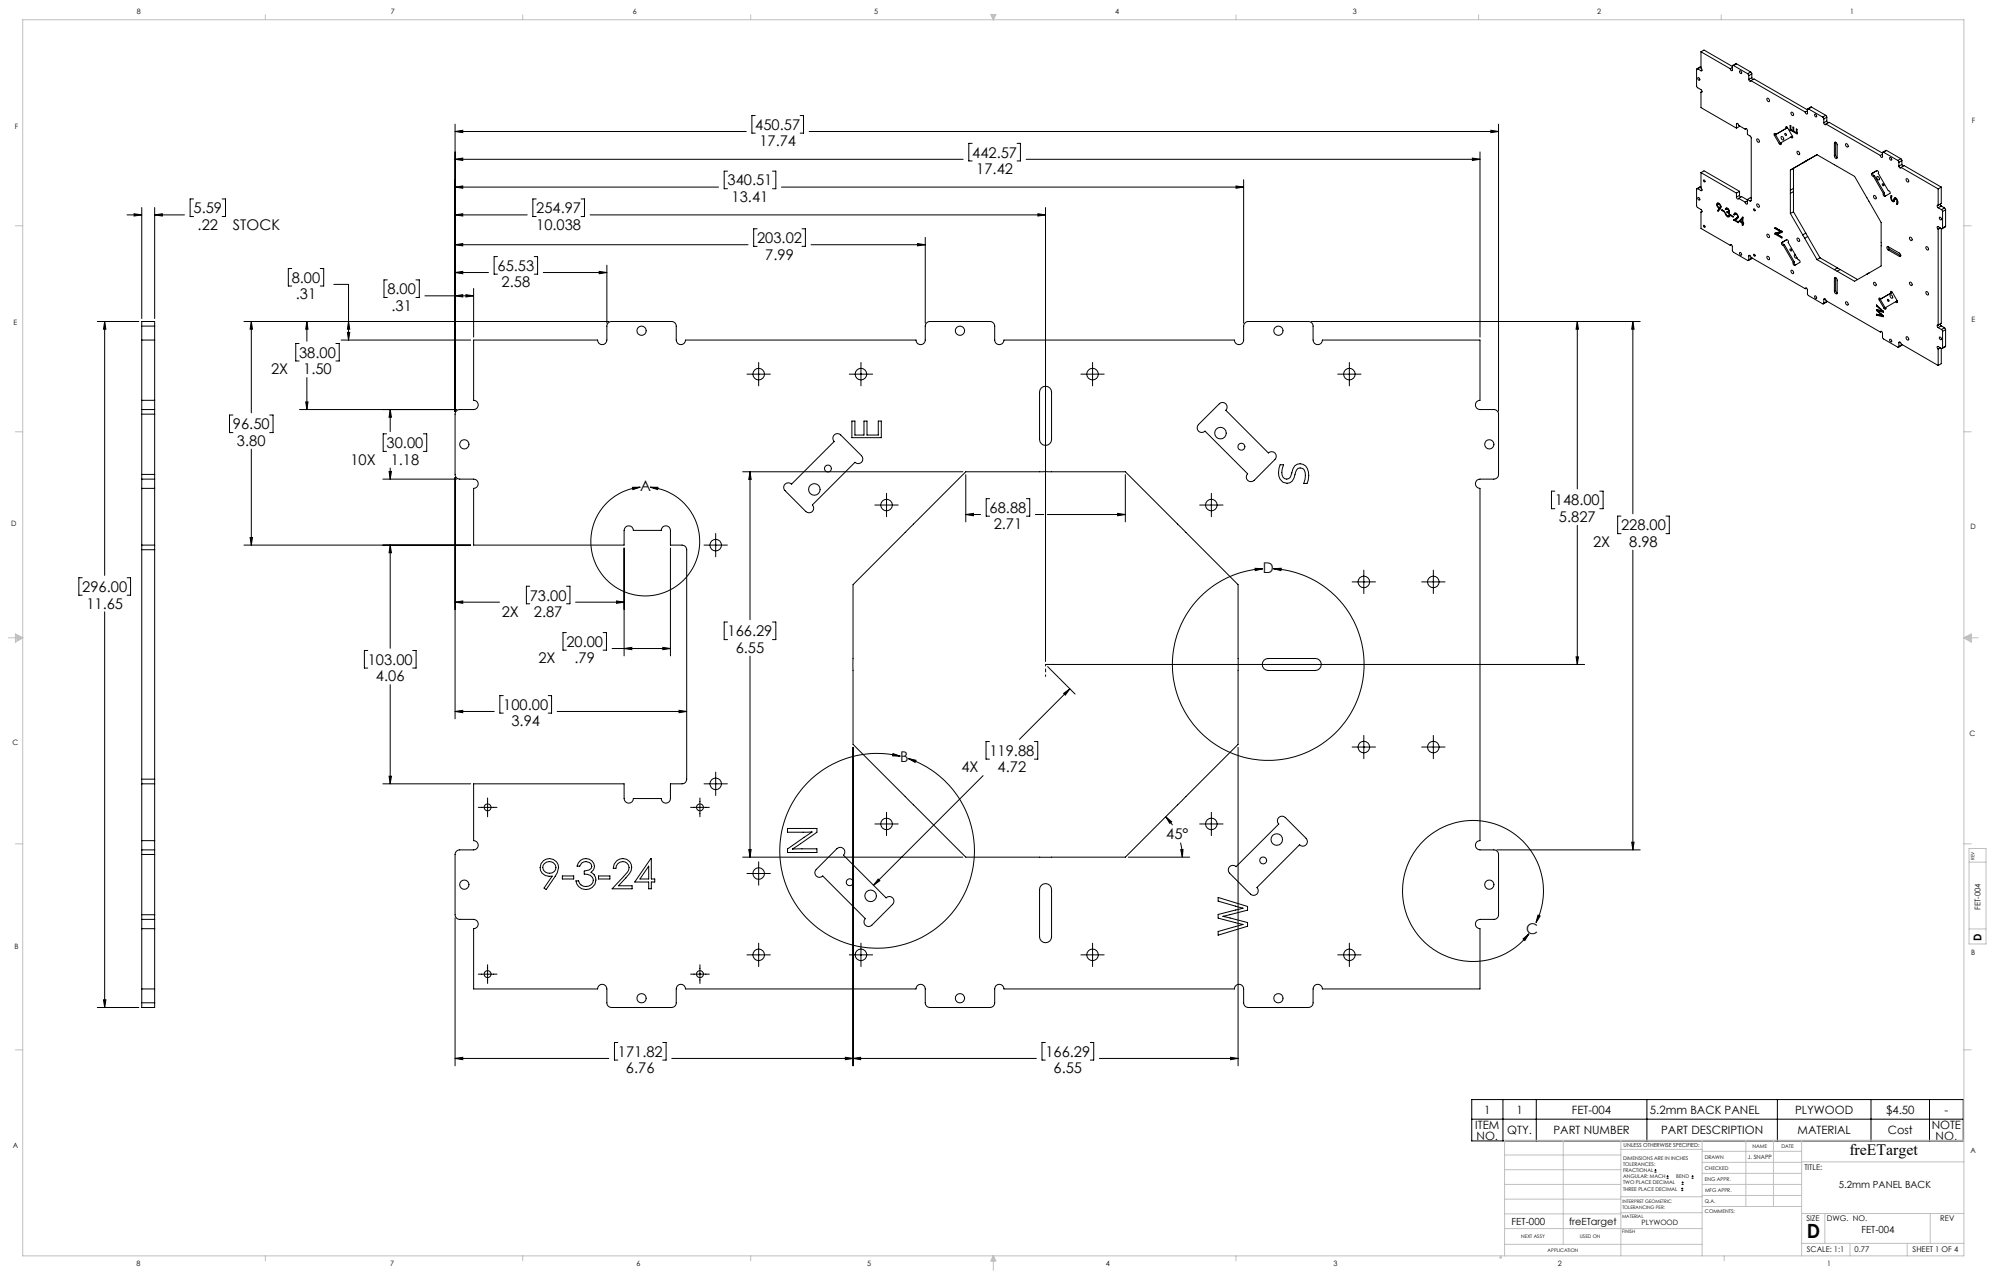
[picture p304: page 1]
.22 STOCK; FREV FET-004; SHEET 1 OF 4; 5.2mm PANEL BACK; J. SNAPP; SCALE: 1:1 0.77; DWG. NO.; REV; freETarget NAME; DATE; MFG APPR.; ENG APPR.; INTERPRET GEOMETRIC TOLERANCING PER:; ANGULAR: MACH; BEND; NEXT ASSY; USED ON

1 | 1 | FET-004 | 5.2mm BACK PANEL | PLYWOOD | $4.50 | -
ITEM NO. | QTY. | PART NUMBER | PART DESCRIPTION | MATERIAL | Cost | NOTE NO.

UNLESS OTHERWISE SPECIFIED:

DIMENSIONS ARE IN INCHES
TOLERANCES:
FRACTIONAL
TWO PLACE DECIMAL
THREE PLACE DECIMAL

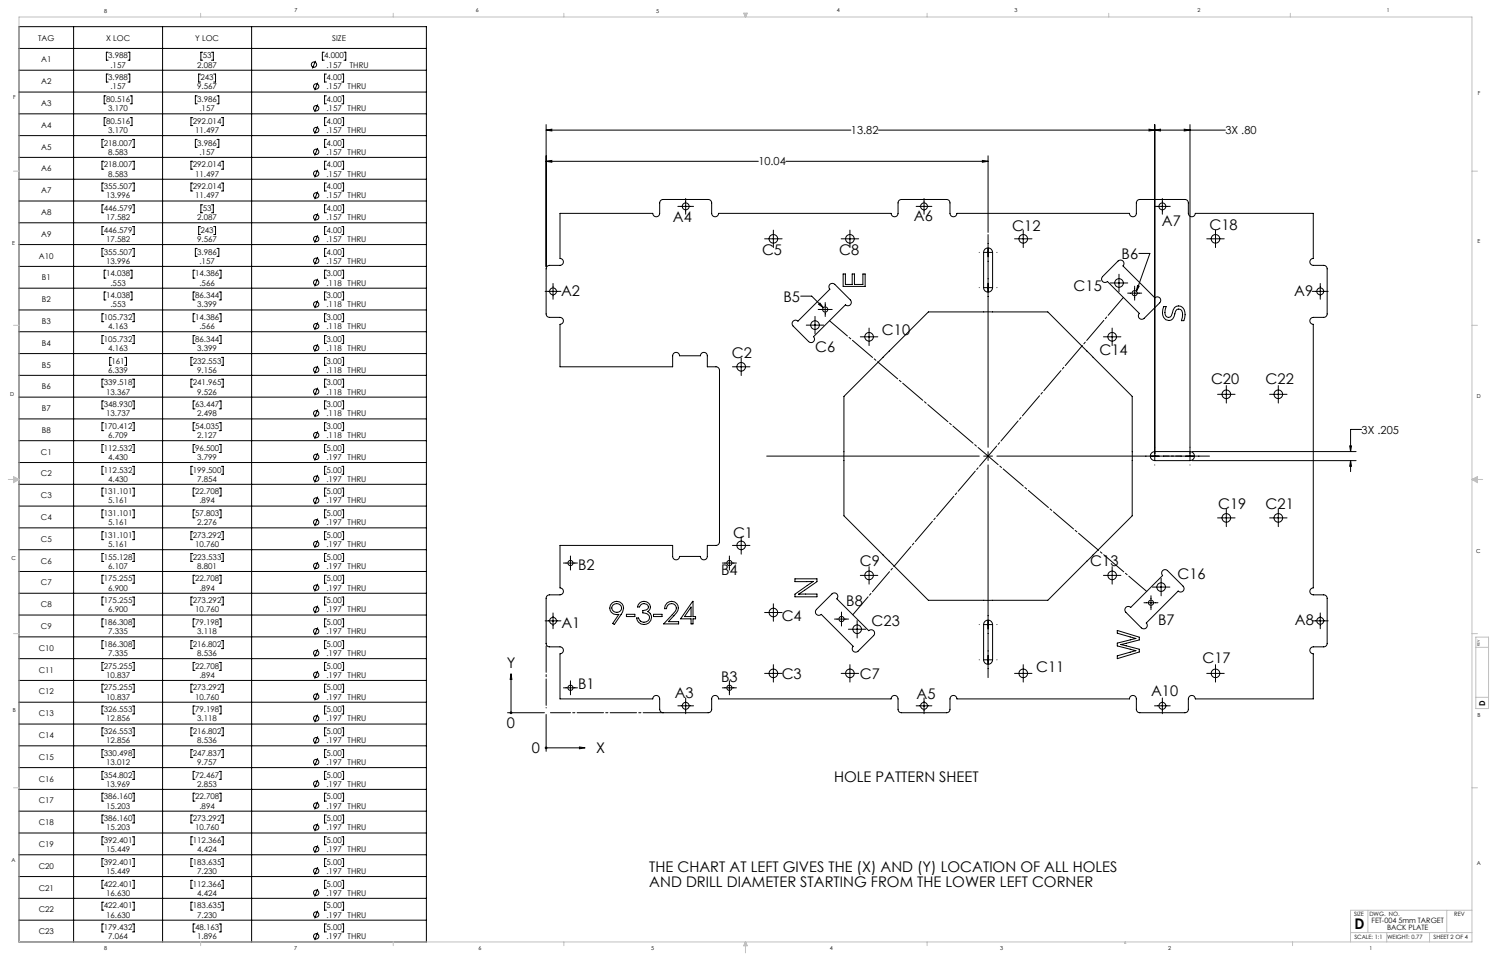
[picture p305: page 2]

TAG | X LOC | Y LOC | SIZE
A1 | 3.988 .157 | 53 2.087 | 4.000 .157 THRU

A2 | 3.988 .157 | 243 9.567 | 4.00 .157 THRU

A3 | 80.516 3.170 | 3.986 .157 | 4.00 .157 THRU

A4 | 80.516 3.170 | 292.014 11.497 | 4.00 .157 THRU

A5 | 218.007 8.583 | 3.986 .157 | 4.00 .157 THRU

A6 | 218.007 8.583 | 292.014 11.497 | 4.00 .157 THRU

A7 | 355.507 13.996 | 292.014 11.497 | 4.00 .157 THRU

A8 | 446.579 17.582 | 53 2.087 | 4.00 .157 THRU

A9 | 446.579 17.582 | 243 9.567 | 4.00 .157 THRU

A10 | 355.507 13.996 | 3.986 .157 | 4.00 .157 THRU

B1 | 14.038 .553 | 14.386 .566 | 3.00 .118 THRU

B2 | 14.038 .553 | 86.344 3.399 | 3.00 .118 THRU

B3 | 105.732 4.163 | 14.386 .566 | 3.00 .118 THRU

B4 | 105.732 4.163 | 86.344 3.399 | 3.00 .118 THRU

B5 | 161 6.339 | 232.553 9.156 | 3.00 .118 THRU

B6 | 339.518 13.367 | 241.965 9.526 | 3.00 .118 THRU

B7 | 348.930 13.737 | 63.447 2.498 | 3.00 .118 THRU

B8 | 170.412 6.709 | 54.035 2.127 | 3.00 .118 THRU

C1 | 112.532 4.430 | 96.500 3.799 | 5.00 .197 THRU

C2 | 112.532 4.430 | 199.500 7.854 | 5.00 .197 THRU

C3 | 131.101 5.161 | 22.708 .894 | 5.00 .197 THRU

C4 | 131.101 5.161 | 57.803 2.276 | 5.00 .197 THRU

C5 | 131.101 5.161 | 273.292 10.760 | 5.00 .197 THRU

C6 | 155.128 6.107 | 223.533 8.801 | 5.00 .197 THRU

C7 | 175.255 6.900 | 22.708 .894 | 5.00 .197 THRU

C8 | 175.255 6.900 | 273.292 10.760 | 5.00 .197 THRU

C9 | 186.308 7.335 | 79.198 3.118 | 5.00 .197 THRU

C10 | 186.308 7.335 | 216.802 8.536 | 5.00 .197 THRU

C11 | 275.255 10.837 | 22.708 .894 | 5.00 .197 THRU

C12 | 275.255 10.837 | 273.292 10.760 | 5.00 .197 THRU

C13 | 326.553 12.856 | 79.198 3.118 | 5.00 .197 THRU

C14 | 326.553 12.856 | 216.802 8.536 | 5.00 .197 THRU

C15 | 330.498 13.012 | 247.837 9.757 | 5.00 .197 THRU

C16 | 354.802 13.969 | 72.467 2.853 | 5.00 .197 THRU

C17 | 386.160 15.203 | 22.708 .894 | 5.00 .197 THRU

C18 | 386.160 15.203 | 273.292 10.760 | 5.00 .197 THRU

C19 | 392.401 15.449 | 112.366 4.424 | 5.00 .197 THRU

C20 | 392.401 15.449 | 183.635 7.230 | 5.00 .197 THRU

THE CHART AT LEFT GIVES THE (X) AND (Y) LOCATION OF ALL HOLES
AND DRILL DIAMETER STARTING FROM THE LOWER LEFT CORNER

C21 | 422.401 16.630 | 112.366 4.424 | 5.00 .197 THRU

C22 | 422.401 16.630 | 183.635 7.230 | 5.00 .197 THRU

C23 | 179.432 7.064 | 48.163 1.896 | 5.00 .197 THRU

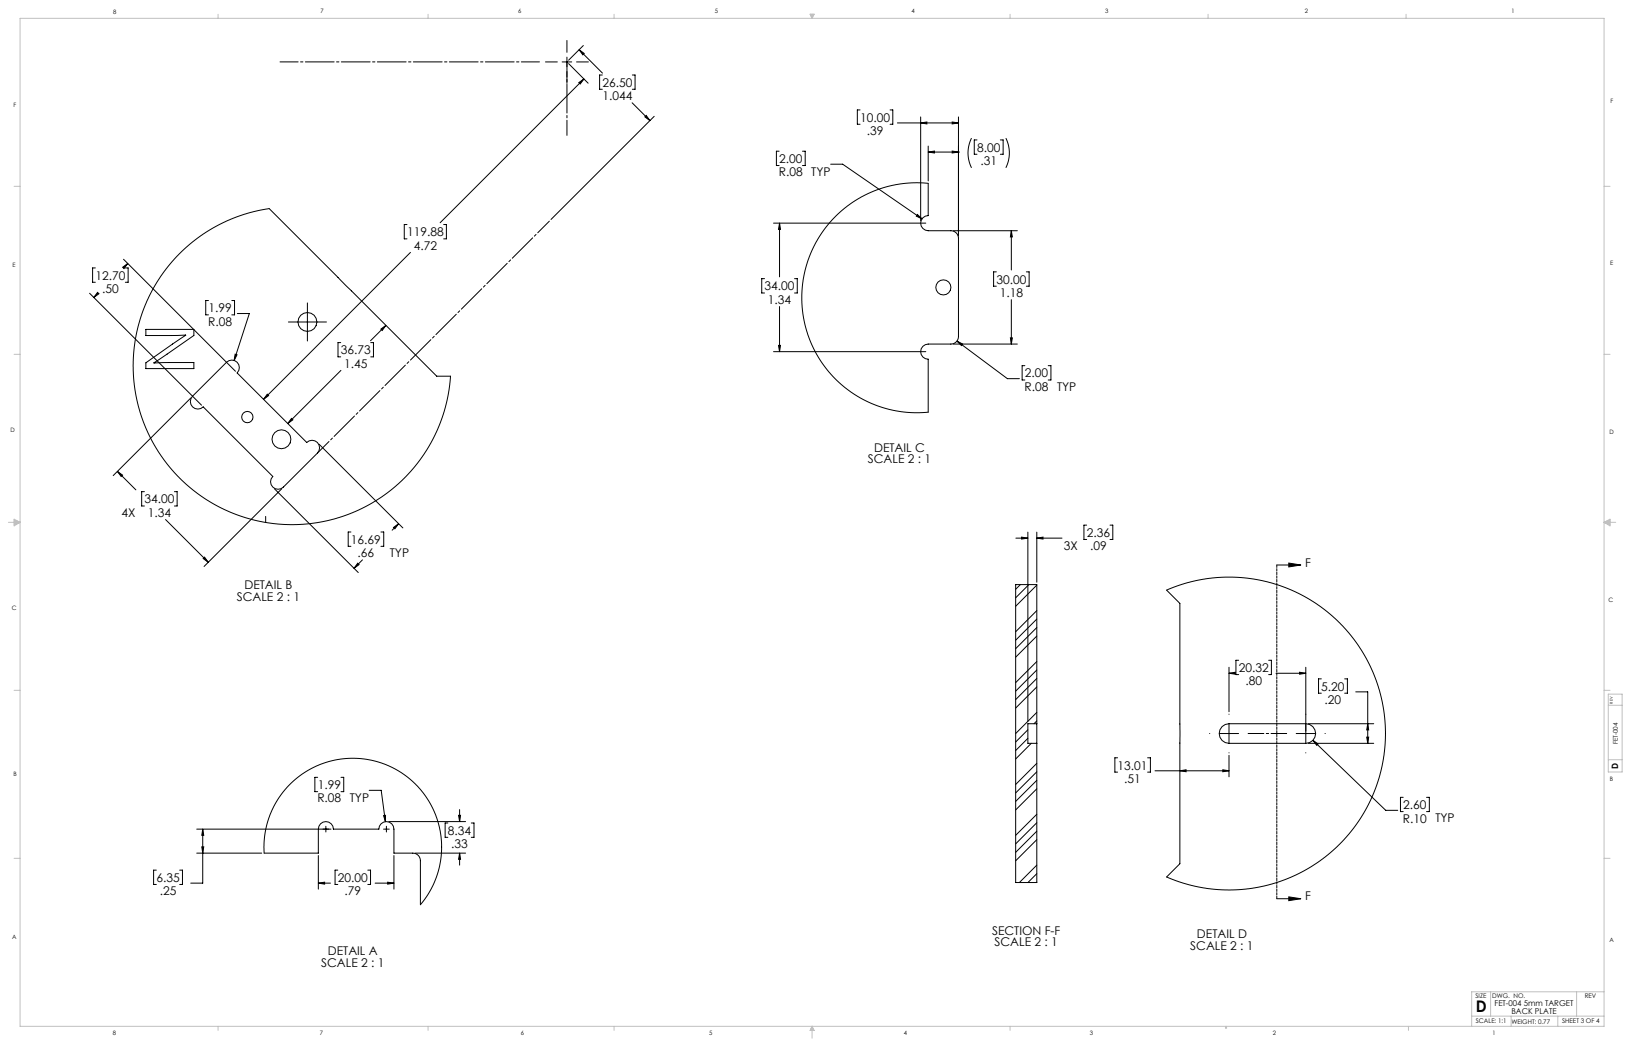
[picture p306: page 3]
R.08 TYP; DETAIL A SCALE 2 : 1; .66 TYP; DETAIL B SCALE 2 : 1; DETAIL C SCALE 2 : 1; R.10 TYP; DETAIL D SCALE 2 : 1; SECTION F-F SCALE 2 : 1; FREV FET-004

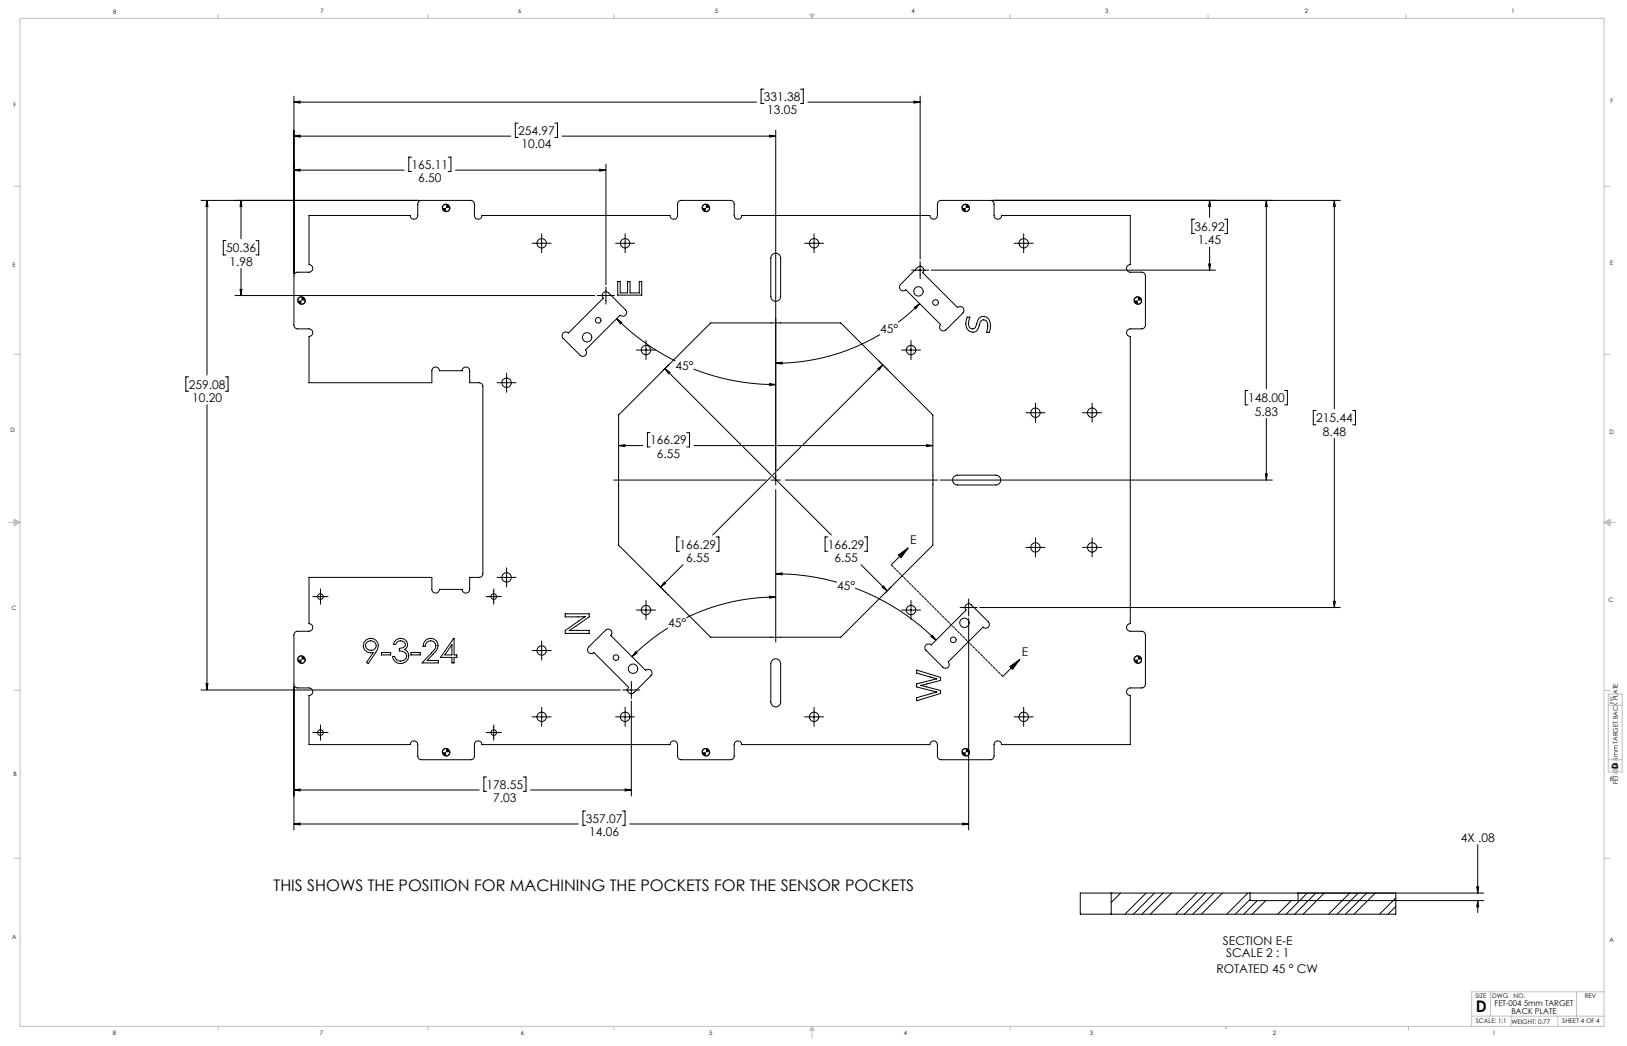
[picture p307: page 4]
SECTION E-E SCALE 2 : 1 ROTATED 45 ° CW

FREV FET-004 5mm TARGET BACK PLATE D

THIS SHOWS THE POSITION FOR MACHINING THE POCKETS FOR THE SENSOR POCKETS
