ten-point-nine/freETarget/Mechanical/Dimensioned Drawings/Competition Target/FET-005 TARGET TOP PLATE.PDF

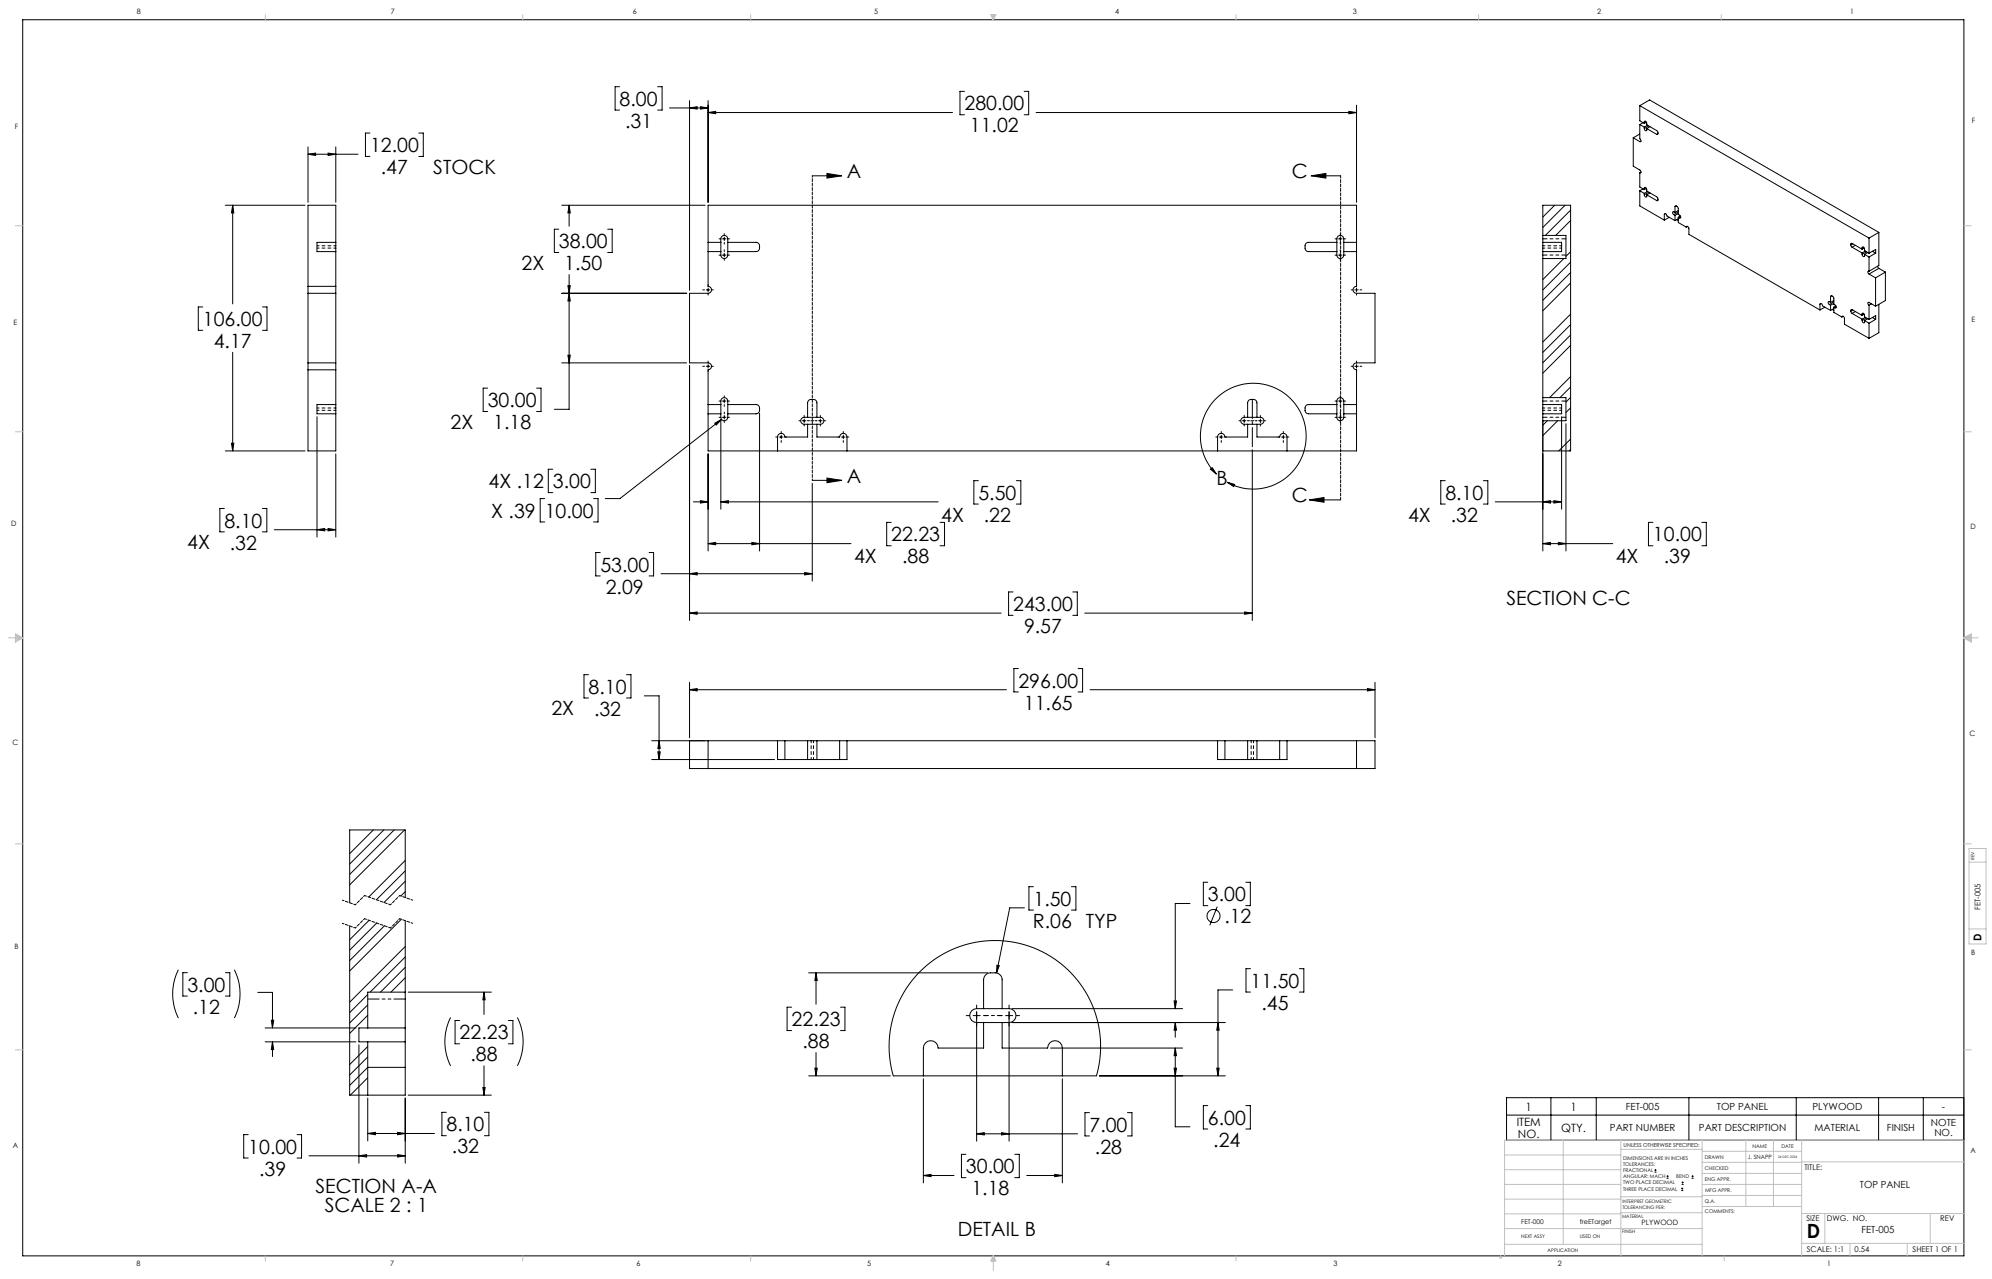
[picture p308: page 1]
.47 STOCK; SECTION A-A SCALE 2 : 1; R.06 TYP; DETAIL B; SECTION C-C; FREV FET-005; SHEET 1 OF 1; TOP PANEL; J. SNAPP 24 DEC 2024; SCALE: 1:1 0.54; DWG. NO.; REV; MFG APPR.; ENG APPR.; INTERPRET GEOMETRIC TOLERANCING PER:; ANGULAR: MACH; BEND; NEXT ASSY; USED ON

1 | 1 | FET-005 | TOP PANEL | PLYWOOD | | -
ITEM NO. | QTY. | PART NUMBER | PART DESCRIPTION | MATERIAL | FINISH | NOTE NO.

UNLESS OTHERWISE SPECIFIED:

DIMENSIONS ARE IN INCHES
TOLERANCES:
FRACTIONAL
TWO PLACE DECIMAL
THREE PLACE DECIMAL
