ten-point-nine/freETarget/Mechanical/Dimensioned Drawings/Competition Target/FET-006 BOTTOM PLATE .PDF

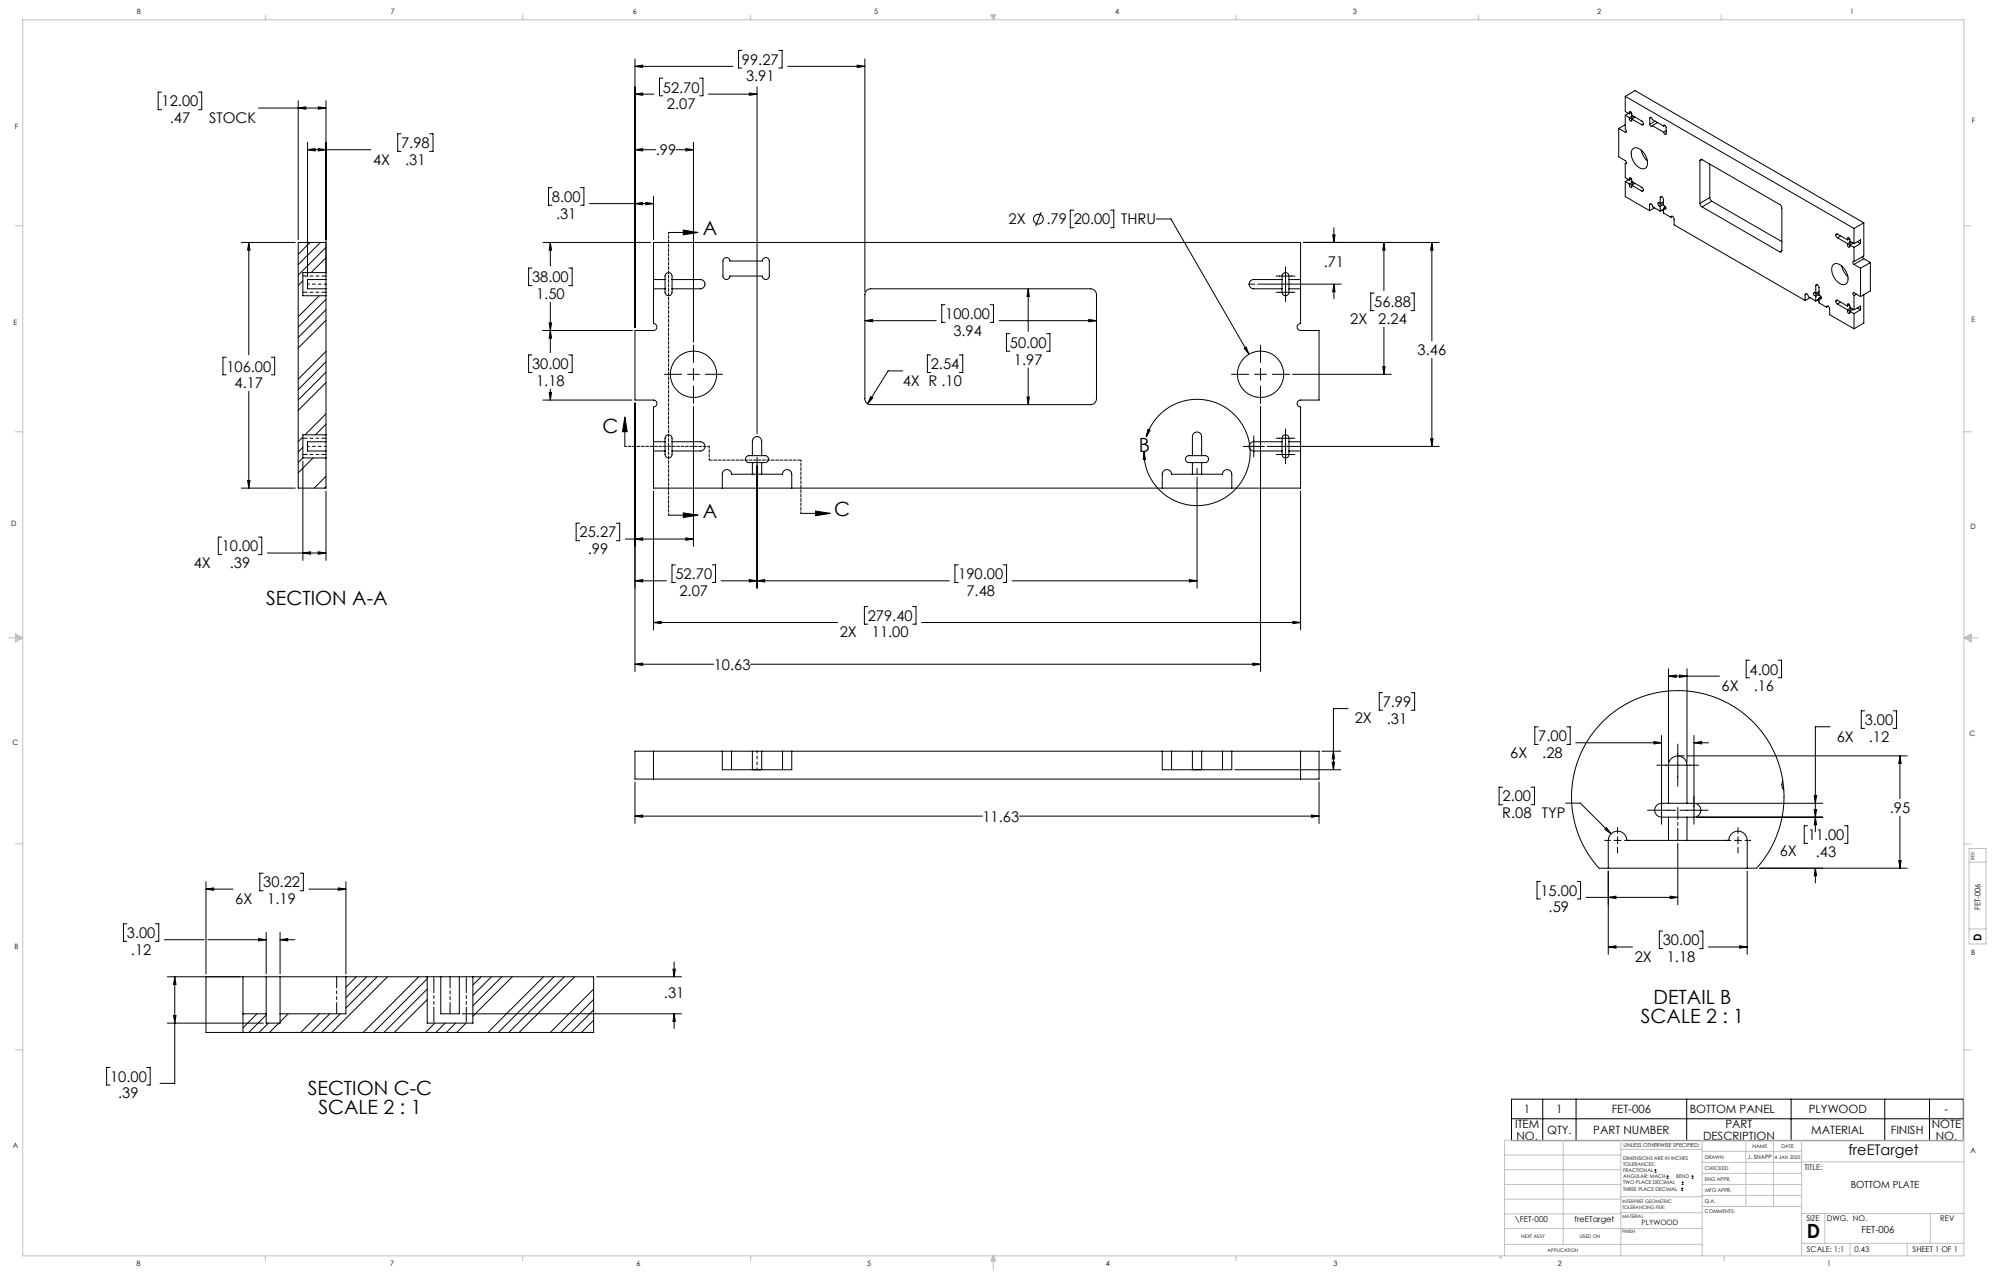
[picture p309: page 1]
2X .79 20.00 THRU; .47 STOCK; SECTION A-A; R.08 TYP; DETAIL B SCALE 2 : 1; SECTION C-C SCALE 2 : 1; FREV FET-006; SHEET 1 OF 1; BOTTOM PLATE; J. SNAPP; SCALE: 1:1 0.43; DWG. NO.; REV; freETarget NAME; DATE; MFG APPR.; ENG APPR.; INTERPRET GEOMETRIC TOLERANCING PER:; ANGULAR: MACH; BEND; NEXT ASSY; USED ON; 4 JAN 2025

1 | 1 | FET-006 | BOTTOM PANEL | PLYWOOD | | -
ITEM NO. | QTY. | PART NUMBER | DESCRIPTION PART | MATERIAL | FINISH | NOTE NO.

UNLESS OTHERWISE SPECIFIED:

DIMENSIONS ARE IN INCHES
TOLERANCES:
FRACTIONAL
TWO PLACE DECIMAL
THREE PLACE DECIMAL
