ten-point-nine/freETarget/Mechanical/Dimensioned Drawings/Competition Target/FET-009 N S E W SENSOR MOUNT.PDF

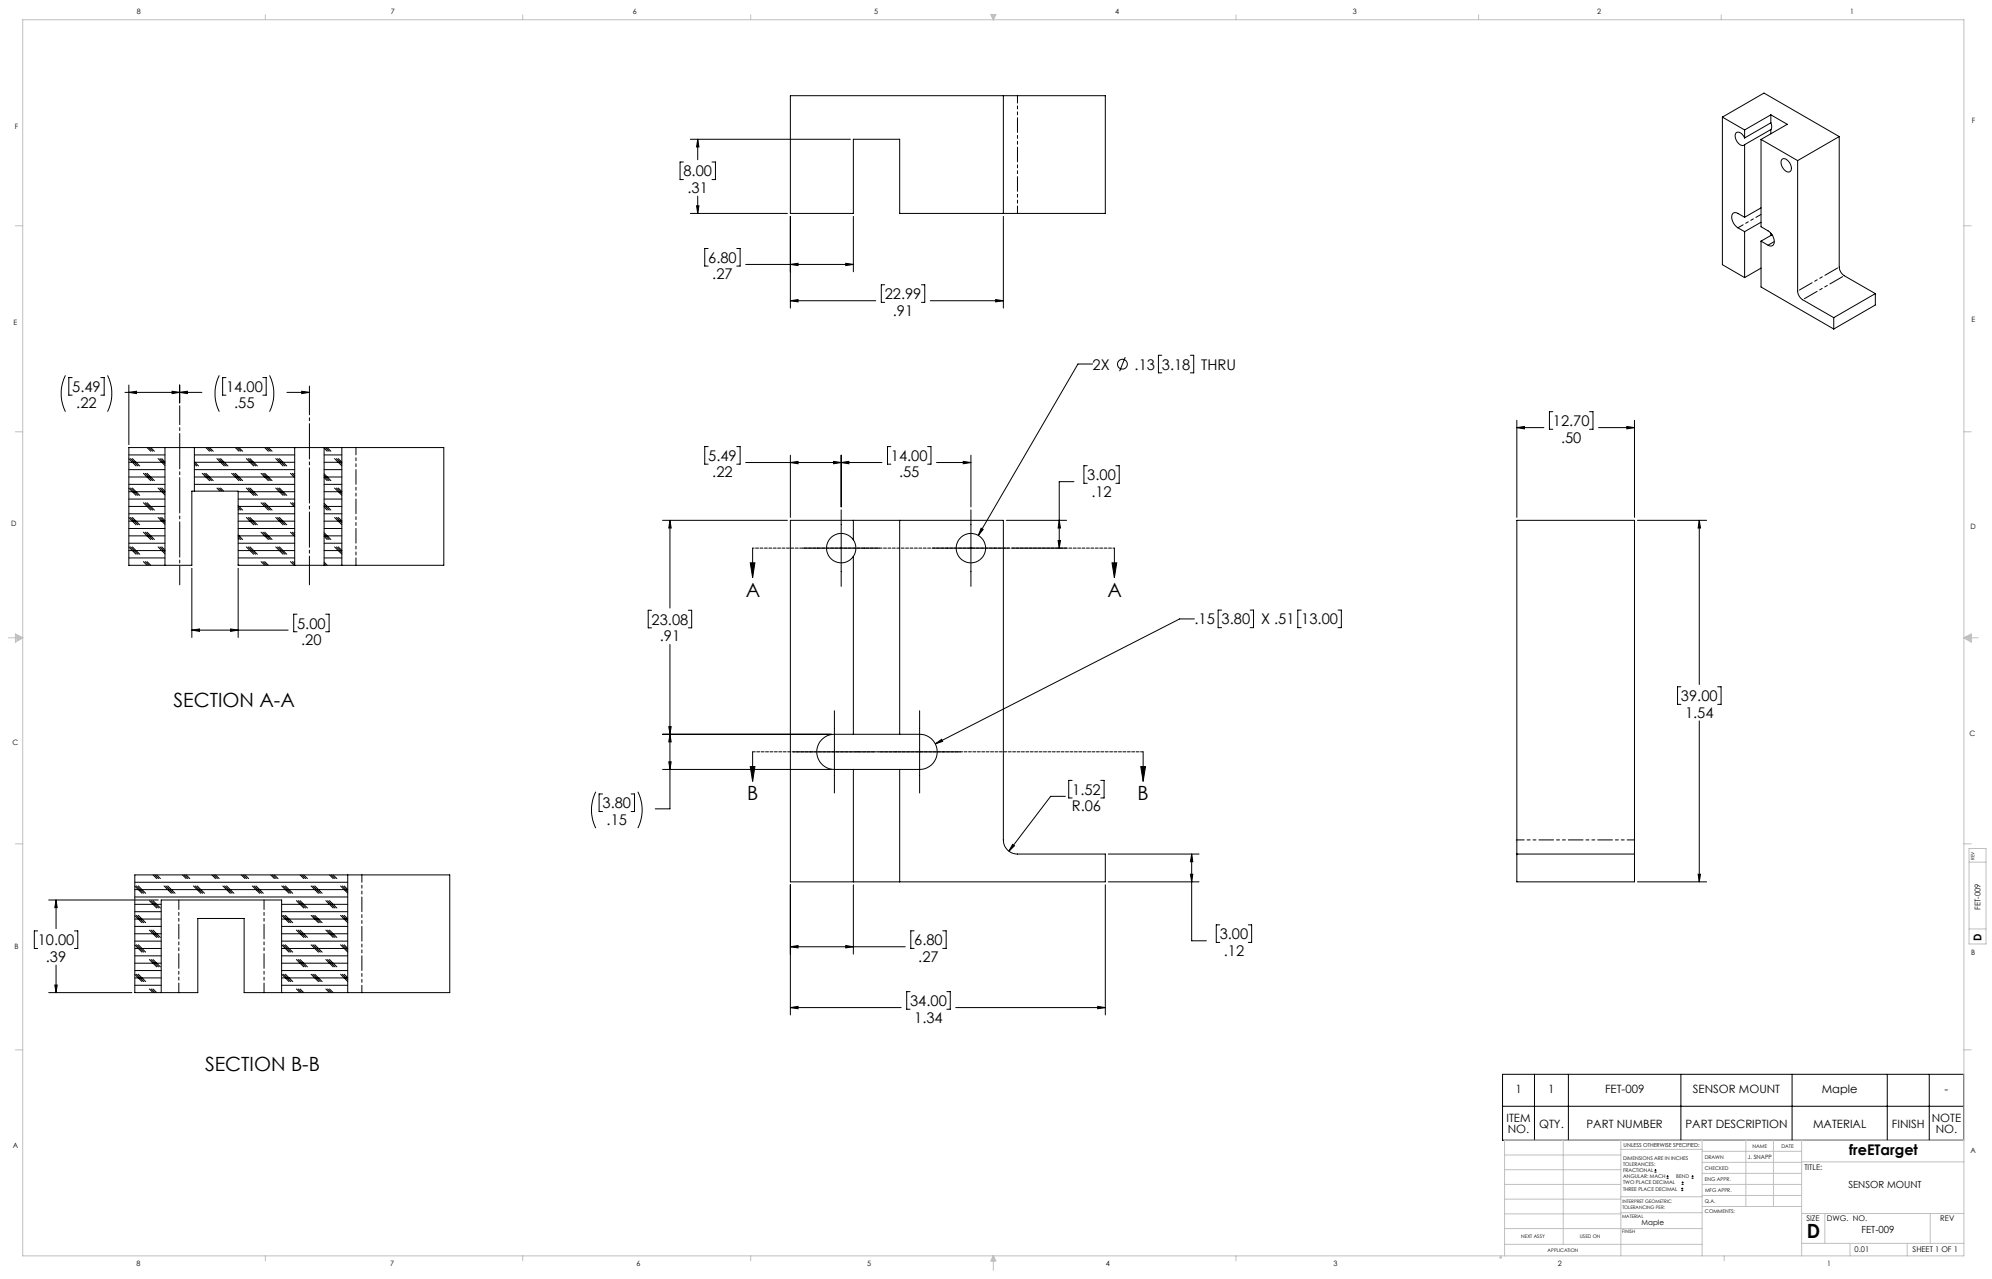
[picture p310: page 1]
.13 3.18 THRU; SECTION A-A; SECTION B-B; FREV FET-009; SHEET 1 OF 1; SENSOR MOUNT; J. SNAPP; DWG. NO.; REV; freETarget NAME; DATE; MFG APPR.; ENG APPR.; INTERPRET GEOMETRIC TOLERANCING PER:; ANGULAR: MACH; BEND; NEXT ASSY; USED ON

1 | 1 | FET-009 | SENSOR MOUNT | Maple | | -
ITEM NO. | QTY. | PART NUMBER | PART DESCRIPTION | MATERIAL | FINISH | NOTE NO.

UNLESS OTHERWISE SPECIFIED:

DIMENSIONS ARE IN INCHES
TOLERANCES:
FRACTIONAL
TWO PLACE DECIMAL
THREE PLACE DECIMAL
