ten-point-nine/freETarget/Mechanical/Dimensioned Drawings/Competition Target/FET-012 WITNESS PAPER ROLL SUPPORT.PDF

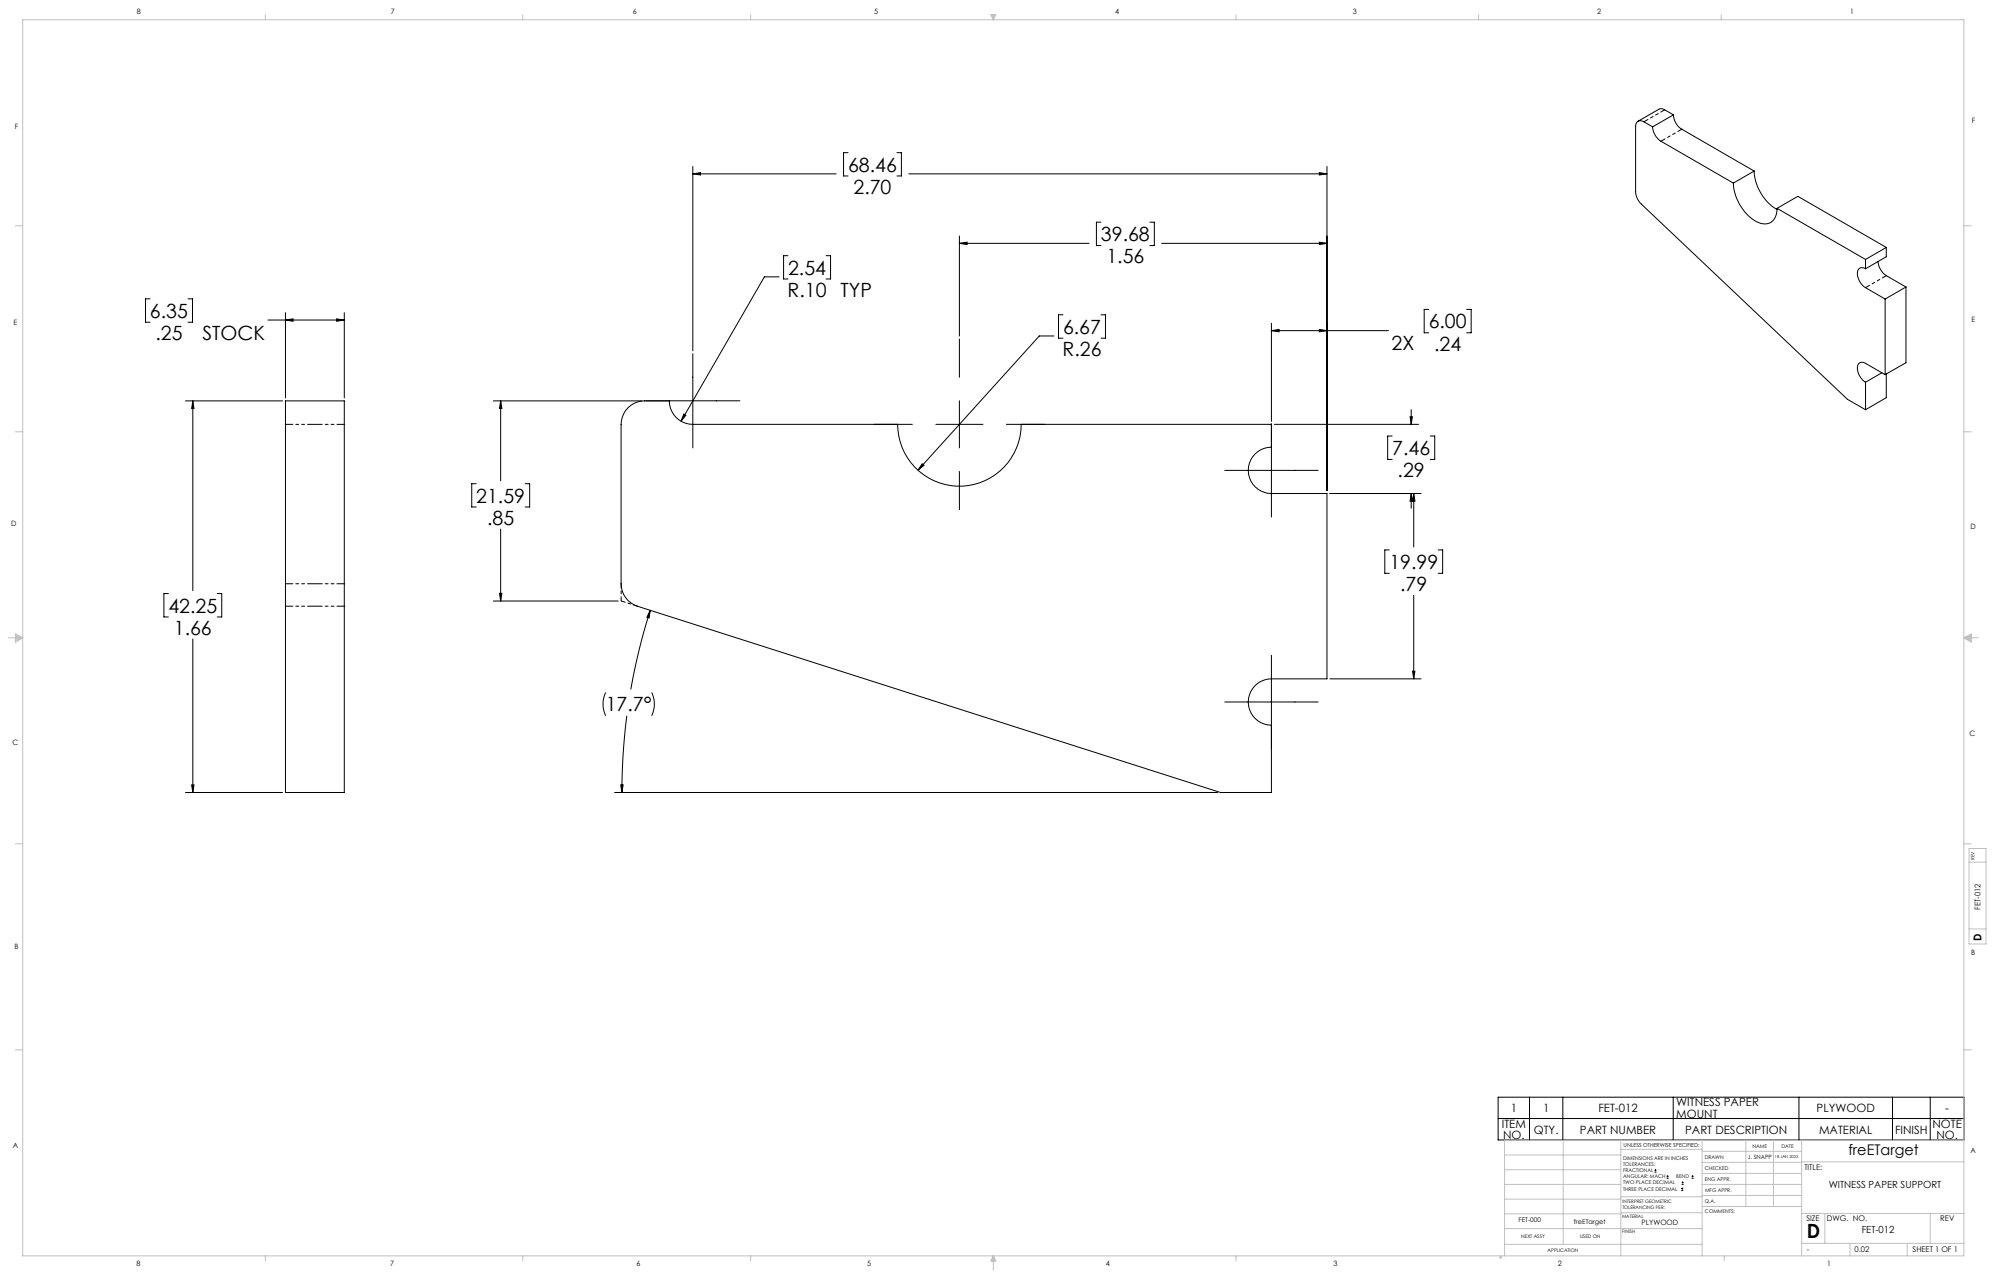
[picture p311: page 1]
R.10 TYP; .25 STOCK; FREV FET-012; SHEET 1 OF 1; WITNESS PAPER SUPPORT; J. SNAPP 18 JAN 2025; DWG. NO.; REV; freETarget NAME; DATE; MFG APPR.; ENG APPR.; INTERPRET GEOMETRIC TOLERANCING PER:; ANGULAR: MACH; BEND; NEXT ASSY; USED ON

1 | 1 | FET-012 | WITNESS PAPER MOUNT | PLYWOOD | | -
ITEM NO. | QTY. | PART NUMBER | PART DESCRIPTION | MATERIAL | FINISH NOTE | NO.

UNLESS OTHERWISE SPECIFIED:

DIMENSIONS ARE IN INCHES
TOLERANCES:
FRACTIONAL
TWO PLACE DECIMAL
THREE PLACE DECIMAL
