ten-point-nine/freETarget/Mechanical/Dimensioned Drawings/Competition Target/FET-015 LED STRIP HOLDER.PDF

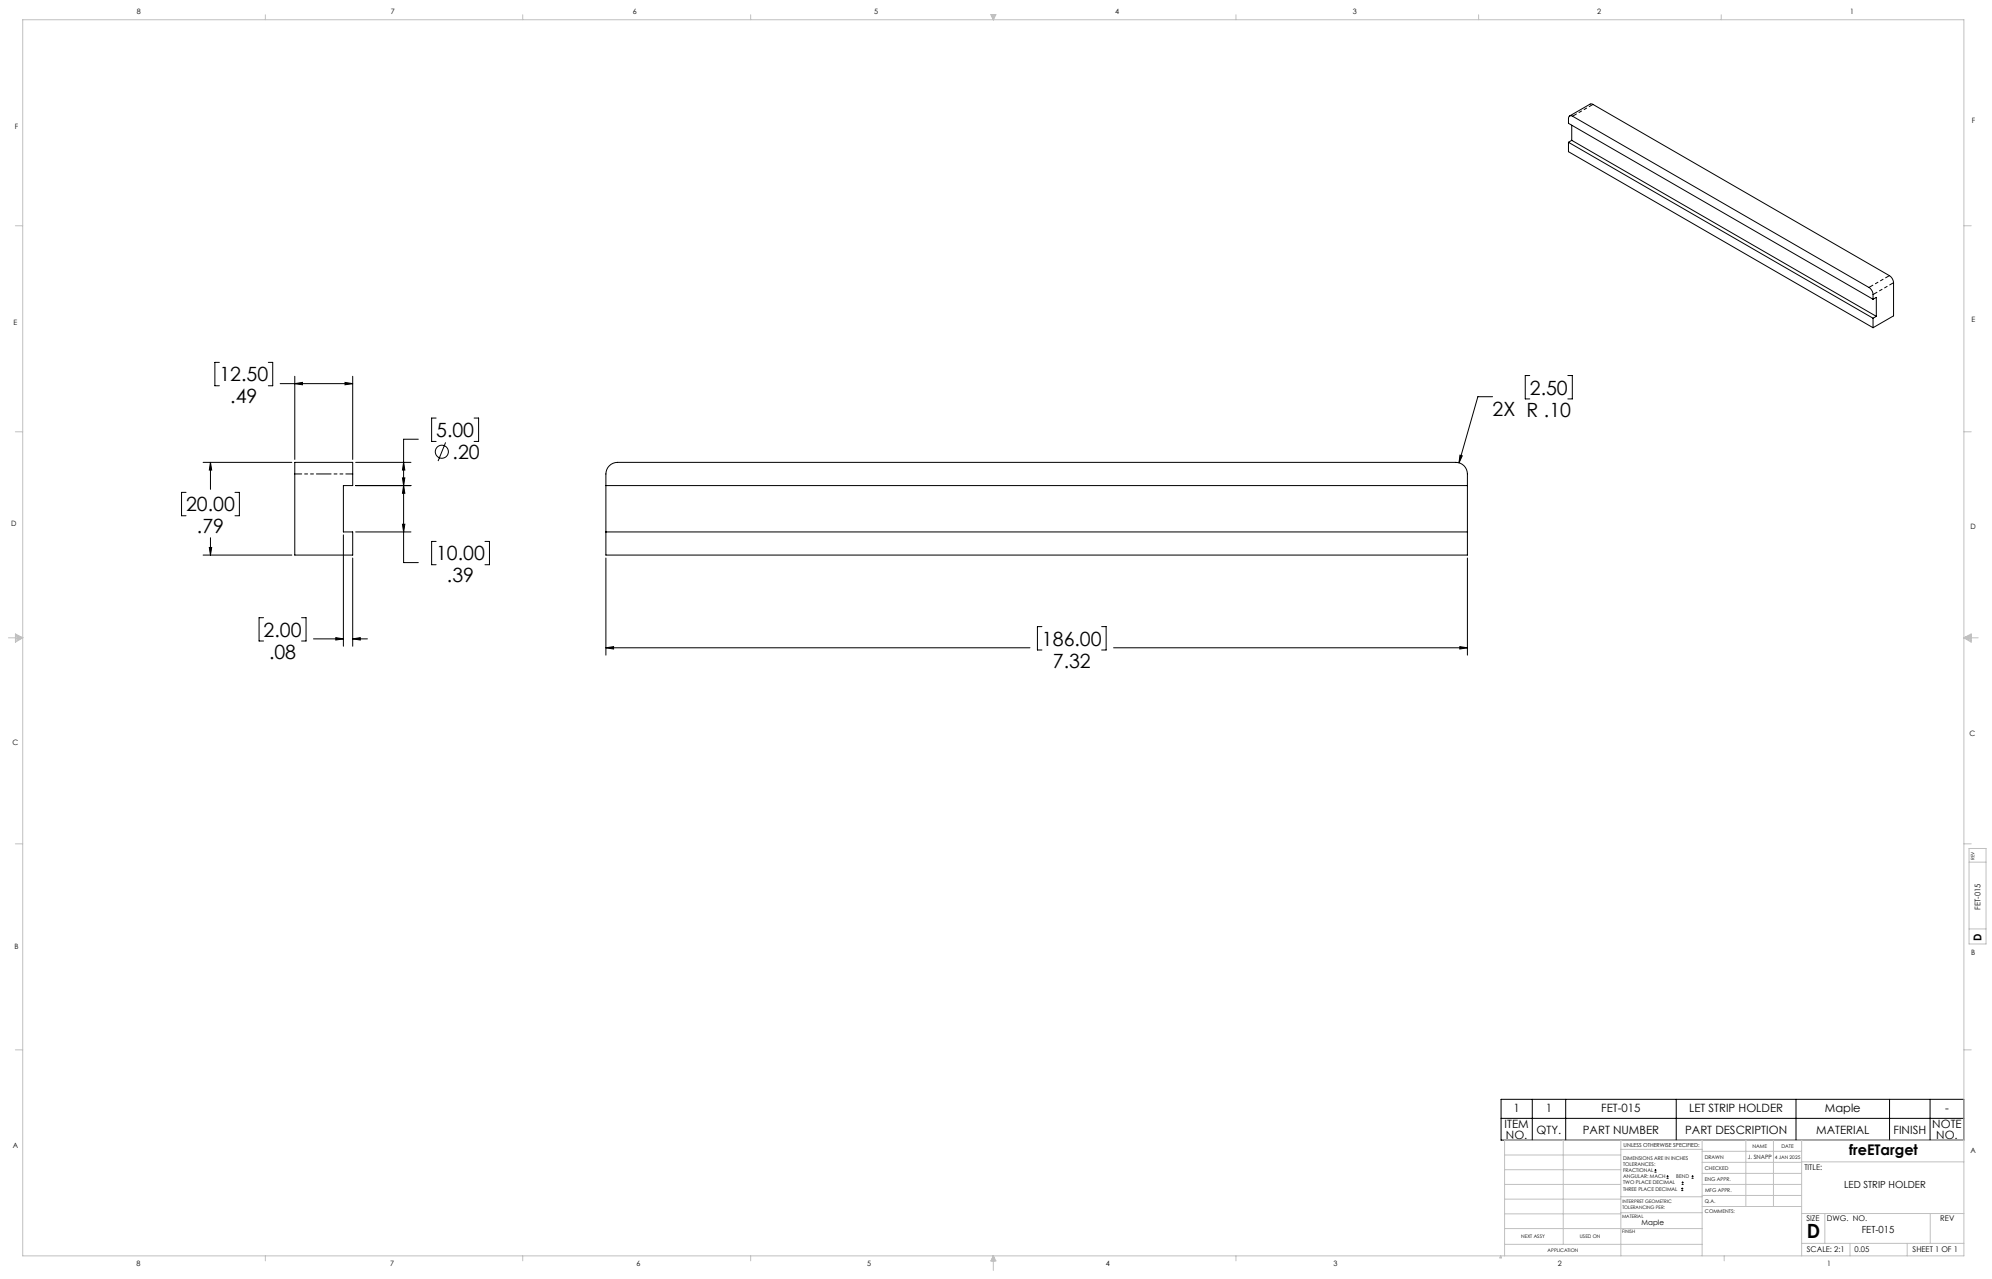
[picture p312: page 1]
FREV FET-015; SHEET 1 OF 1; LED STRIP HOLDER; J. SNAPP 4 JAN 2025; SCALE: 2:1 0.05; DWG. NO.; REV; freETarget NAME; DATE; MFG APPR.; ENG APPR.; INTERPRET GEOMETRIC TOLERANCING PER:; ANGULAR: MACH; BEND; NEXT ASSY; USED ON

1 | 1 | FET-015 | LET STRIP HOLDER | Maple | | -
ITEM NO. | QTY. | PART NUMBER | PART DESCRIPTION | MATERIAL | FINISH | NOTE NO.

UNLESS OTHERWISE SPECIFIED:

DIMENSIONS ARE IN INCHES
TOLERANCES:
FRACTIONAL
TWO PLACE DECIMAL
THREE PLACE DECIMAL
