ten-point-nine/freETarget/Mechanical/Dimensioned Drawings/Competition Target/FET-016 3mm 016 FACE PLATE.PDF

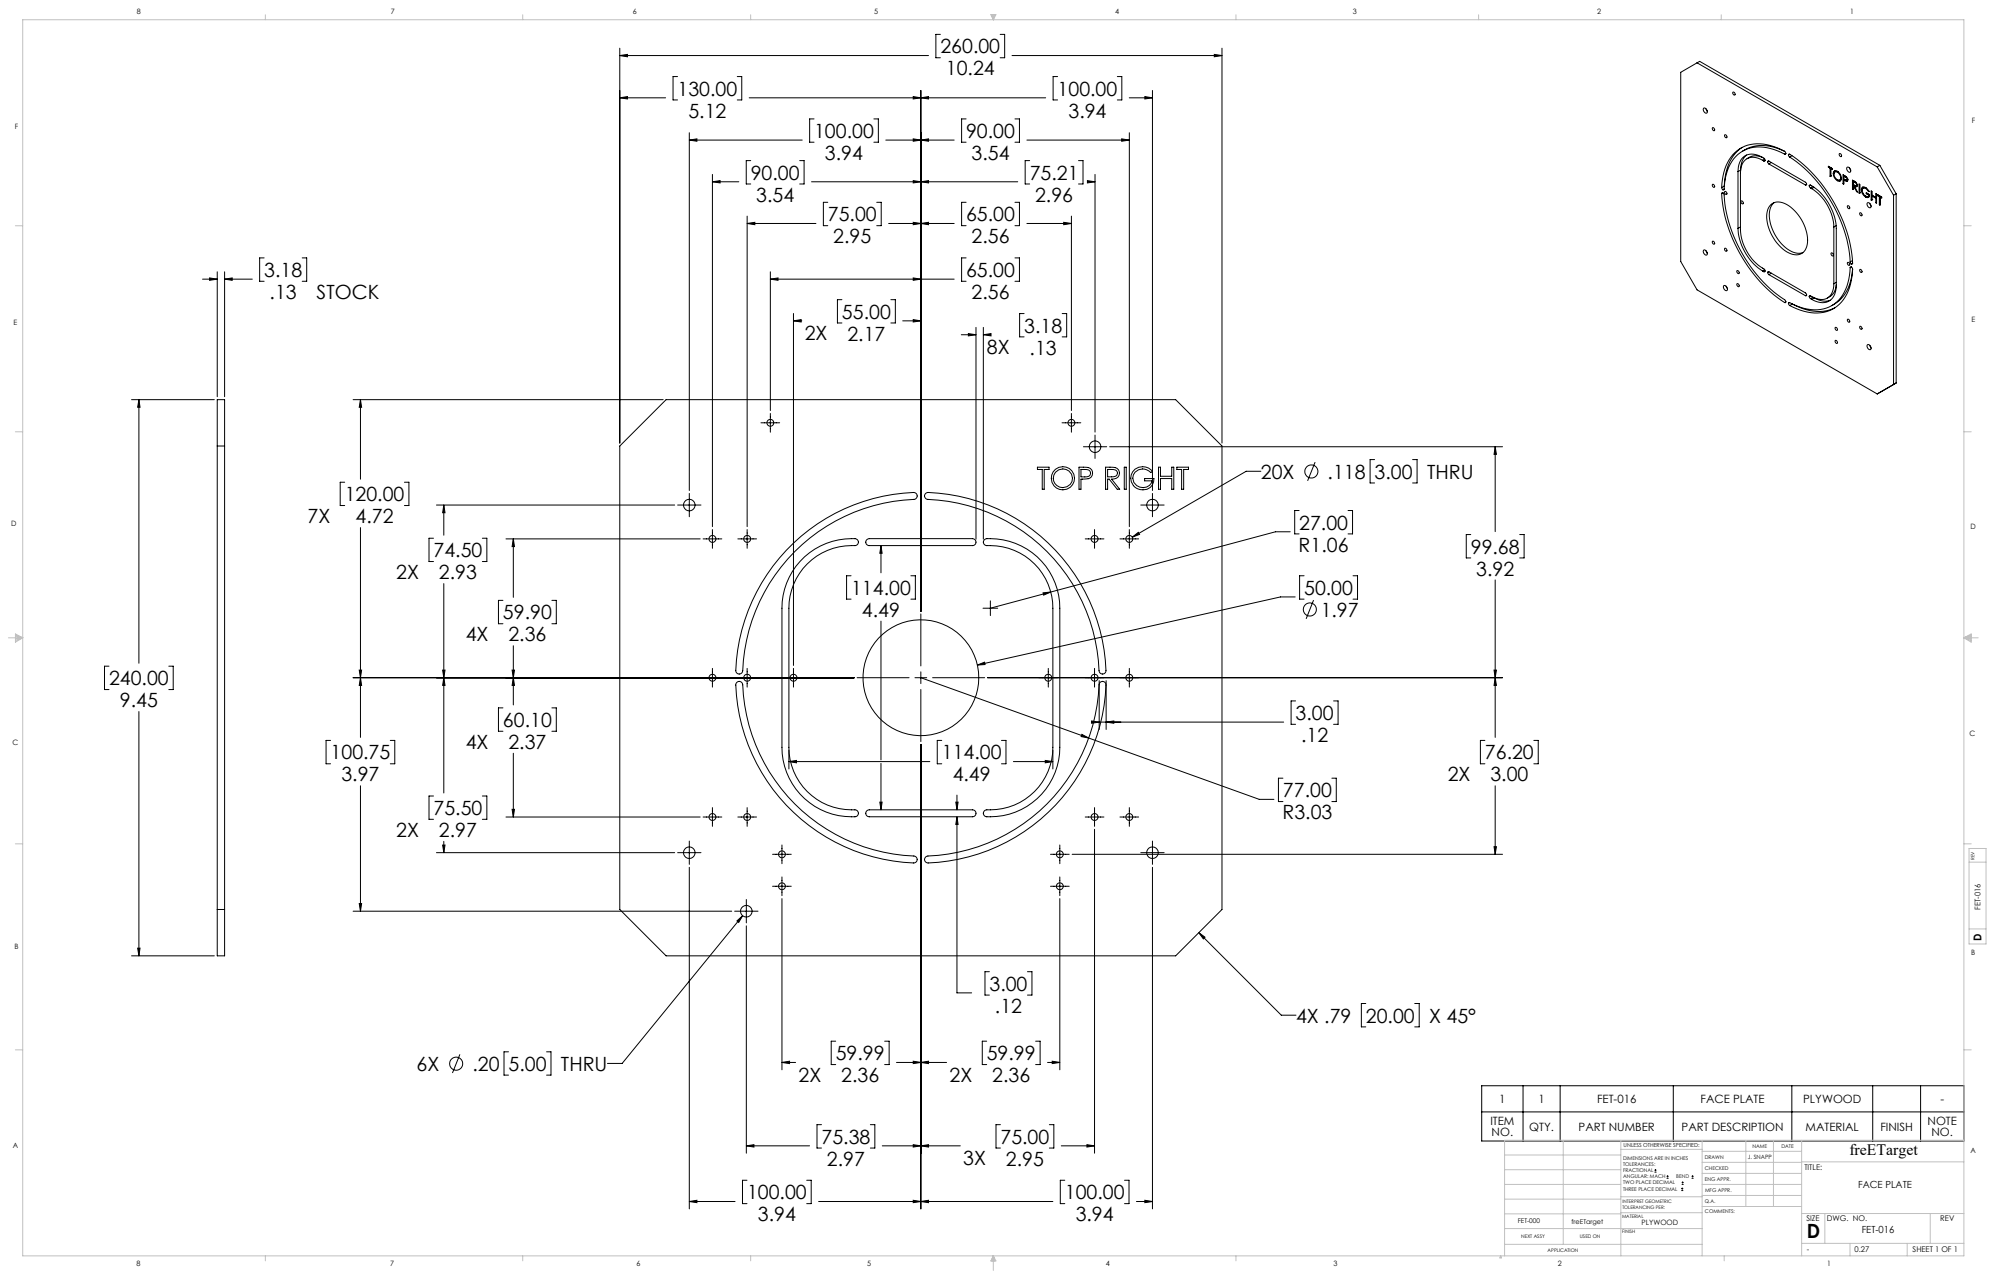
[picture p313: page 1]
.20 5.00 THRU; .118 3.00 THRU; .13 STOCK; FREV FET-016; SHEET 1 OF 1; FACE PLATE; J. SNAPP; DWG. NO.; REV; freETarget NAME; DATE; MFG APPR.; ENG APPR.; INTERPRET GEOMETRIC TOLERANCING PER:; ANGULAR: MACH; BEND; NEXT ASSY; USED ON

1 | 1 | FET-016 | FACE PLATE | PLYWOOD | | -
ITEM NO. | QTY. | PART NUMBER | PART DESCRIPTION | MATERIAL | FINISH | NOTE NO.

UNLESS OTHERWISE SPECIFIED:

DIMENSIONS ARE IN INCHES
TOLERANCES:
FRACTIONAL
TWO PLACE DECIMAL
THREE PLACE DECIMAL
