ten-point-nine/freETarget/Mechanical/Dimensioned Drawings/Competition Target/FET-017 WITNESS PAPER TOP GUIDE.PDF

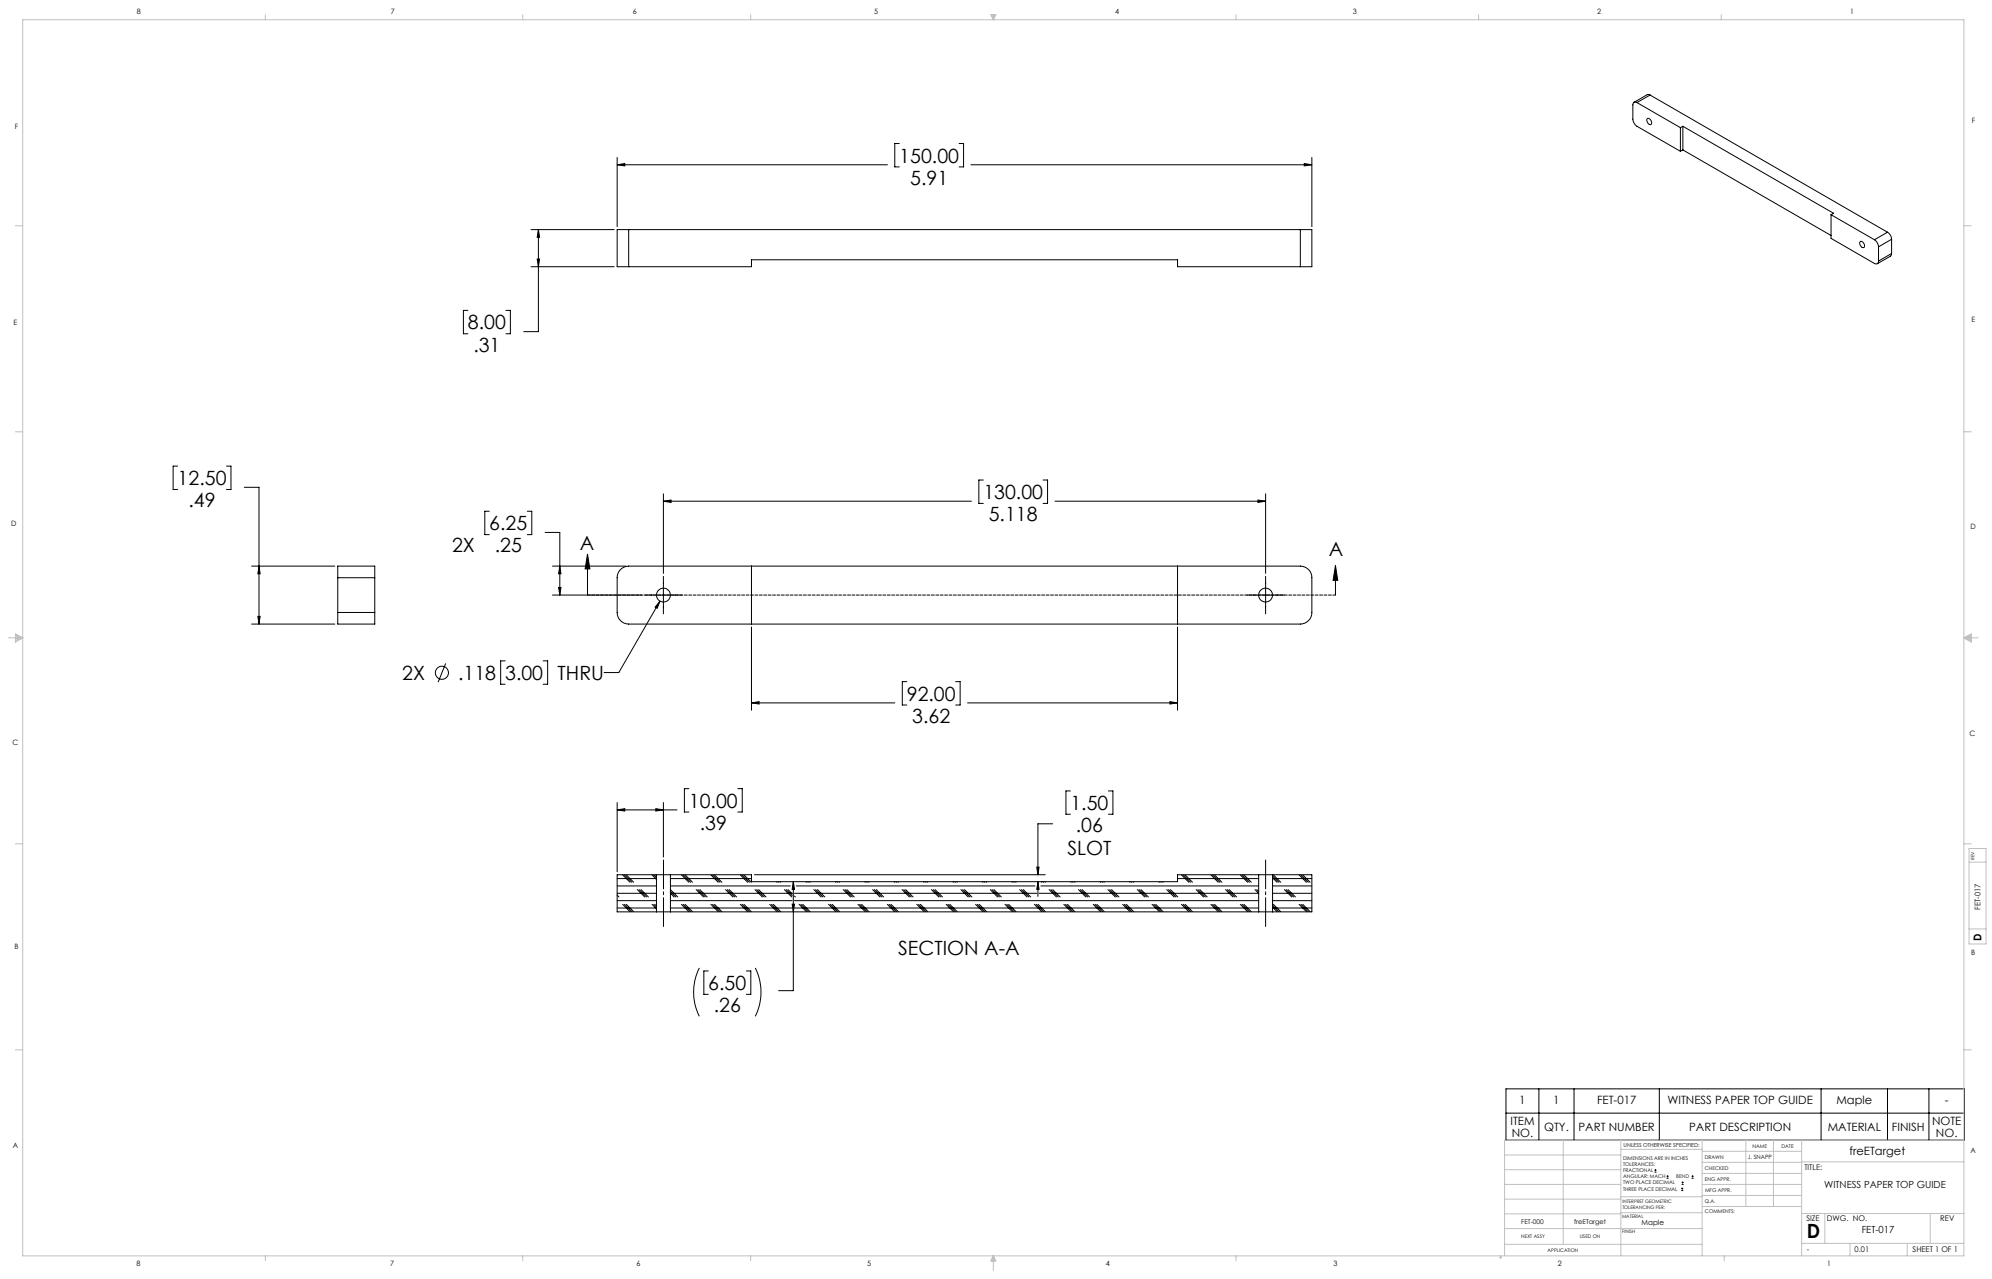
[picture p314: page 1]
.118 3.00 THRU; SECTION A-A; FREV FET-017; SHEET 1 OF 1; J. SNAPP; DWG. NO.; REV; MFG APPR.; ENG APPR.; INTERPRET GEOMETRIC TOLERANCING PER:; ANGULAR: MACH; BEND; NEXT ASSY; USED ON

1 | 1 | FET-017 | WITNESS PAPER TOP GUIDE | Maple | | -
ITEM NO. | QTY. | PART NUMBER | PART DESCRIPTION | MATERIAL | FINISH | NOTE NO.

UNLESS OTHERWISE SPECIFIED:

DIMENSIONS ARE IN INCHES
TOLERANCES:
FRACTIONAL
TWO PLACE DECIMAL
THREE PLACE DECIMAL

TITLE:
WITNESS PAPER TOP GUIDE
