ten-point-nine/freETarget/Mechanical/Dimensioned Drawings/Competition Target/FET-022 5mm FRONT DOOR ASSEMBLY.PDF

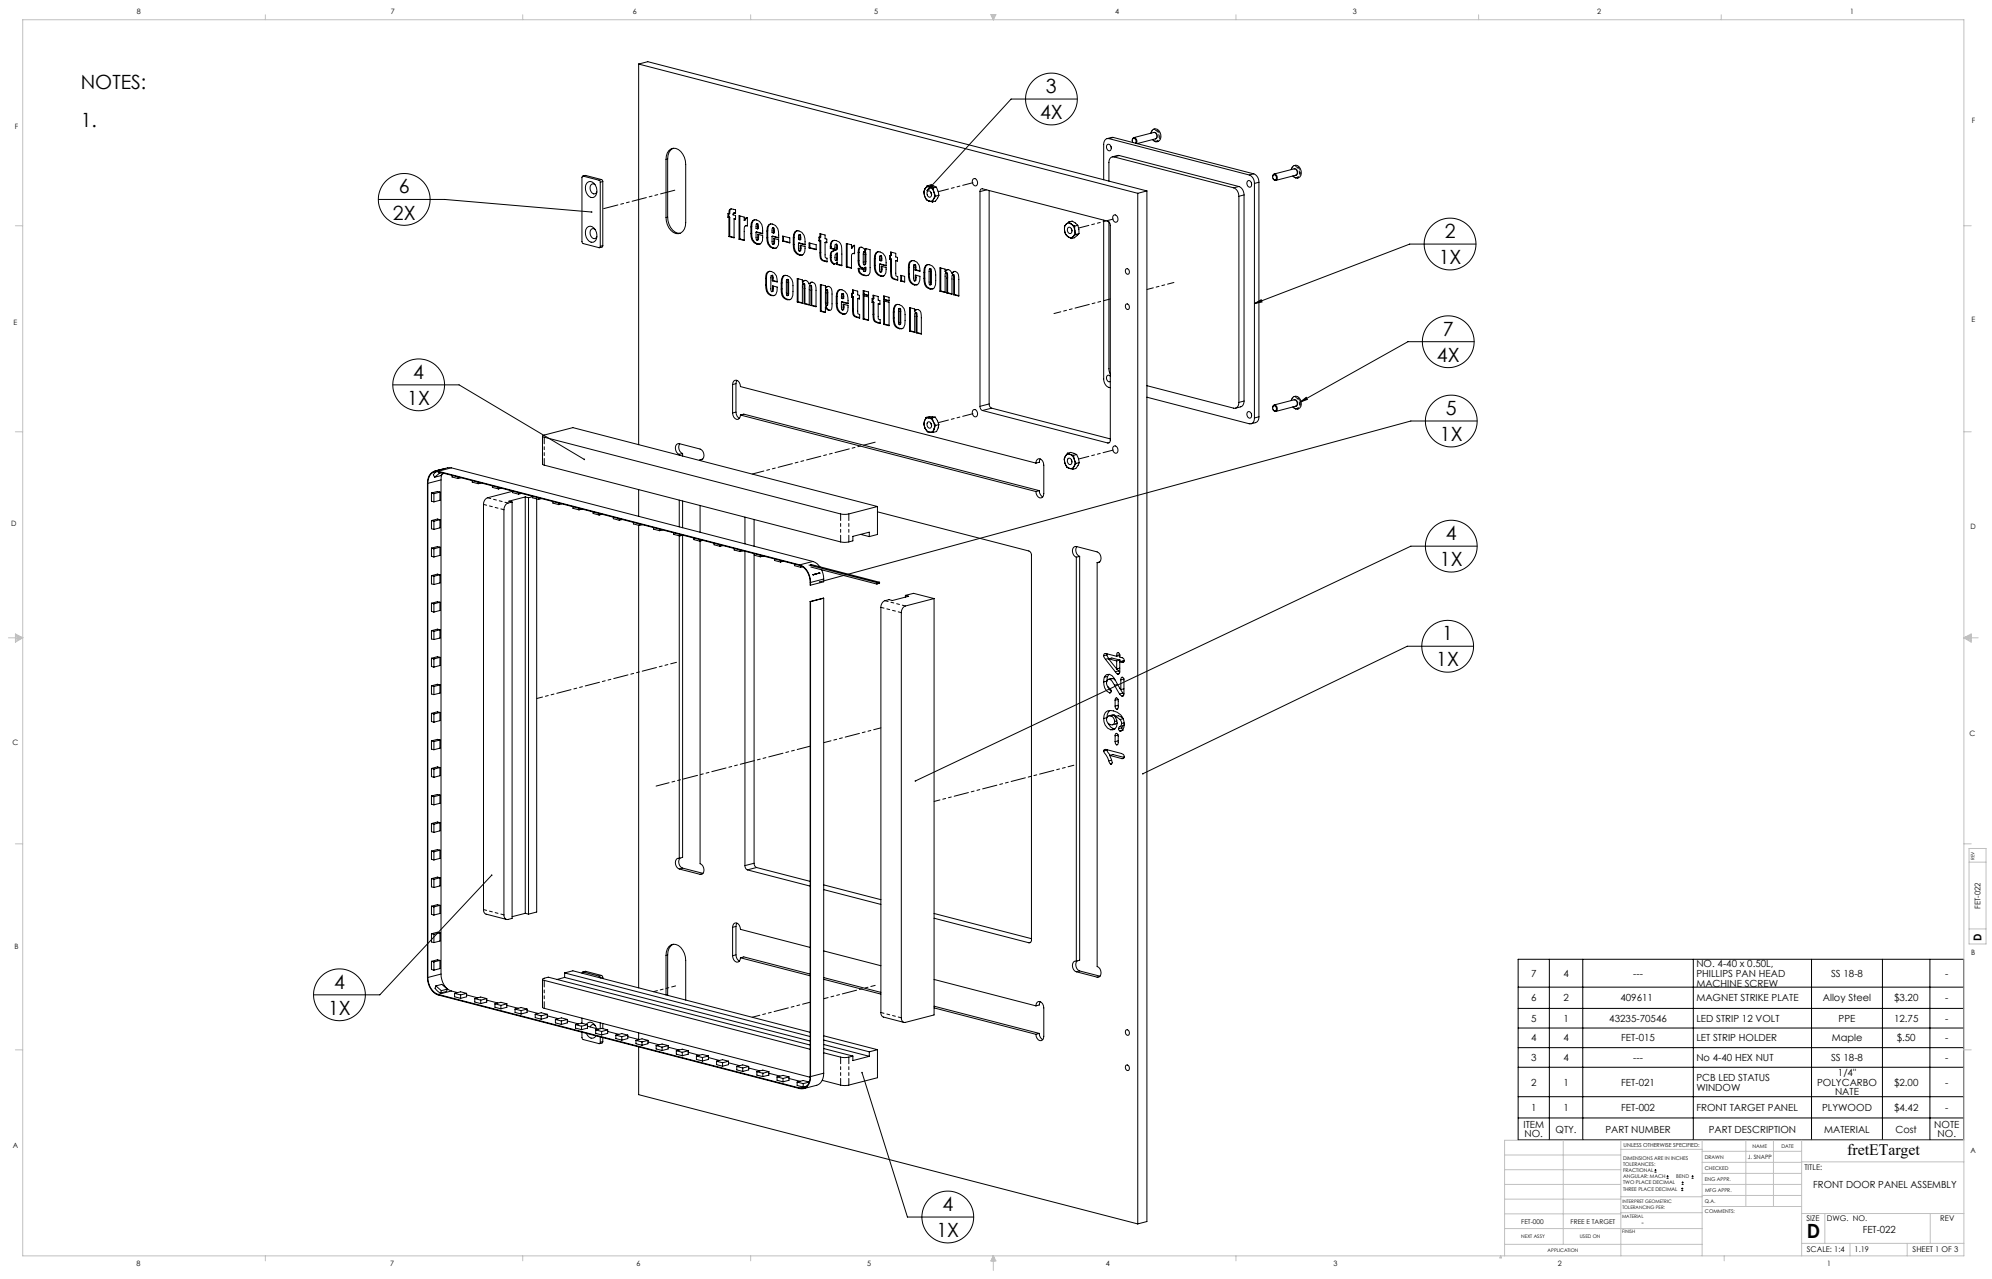
[picture p315: page 1]
EFREV FET-022 D; SHEET 1 OF 3; J. SNAPP; SCALE: 1:4 1.19; DWG. NO.; REV; fretETarget NAME; DATE; MFG APPR.; ENG APPR.; INTERPRET GEOMETRIC TOLERANCING PER:; ANGULAR: MACH; BEND; NEXT ASSY; USED ON; FET-000; FREE E TARGET

7 | 4 | --- | NO. 4-40 x 0.50L, PHILLIPS PAN HEAD MACHINE SCREW | SS 18-8 | | -

6 | 2 | 409611 | MAGNET STRIKE PLATE | Alloy Steel | $3.20 | -
5 | 1 | 43235-70546 | LED STRIP 12 VOLT | PPE | 12.75 | -
4 | 4 | FET-015 | LET STRIP HOLDER | Maple | $.50 | -
3 | 4 | --- | No 4-40 HEX NUT | SS 18-8 | | -
2 | 1 | FET-021 | PCB LED STATUS WINDOW | 1/4" POLYCARBO NATE | $2.00 | -

1 | 1 | FET-002 | FRONT TARGET PANEL | PLYWOOD | $4.42 | -
ITEM NO. | QTY. | PART NUMBER | PART DESCRIPTION | MATERIAL | Cost | NOTE NO.

UNLESS OTHERWISE SPECIFIED:

DIMENSIONS ARE IN INCHES
TOLERANCES:
FRACTIONAL
TWO PLACE DECIMAL
THREE PLACE DECIMAL

TITLE:
FRONT DOOR PANEL ASSEMBLY

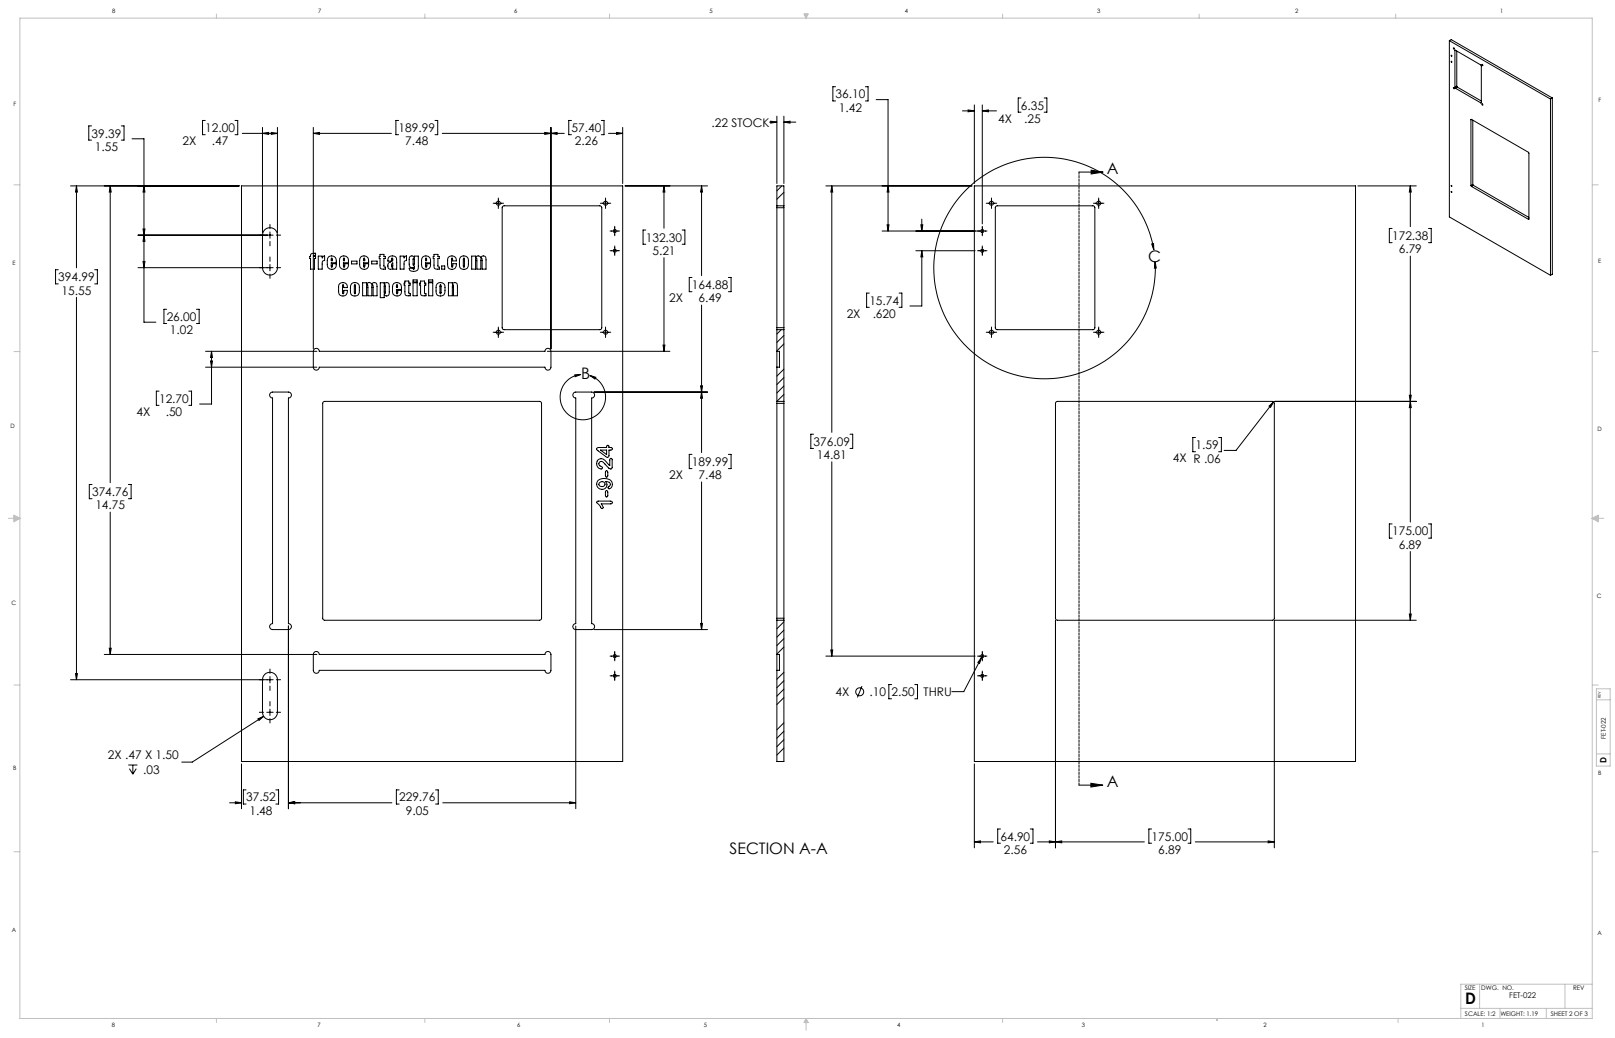
[picture p316: page 2]
.10 2.50 THRU; .22 STOCK; SECTION A-A; FREV FET-022; SCALE: 1:2 WEIGHT: 1.19; SHEET 2 OF 3

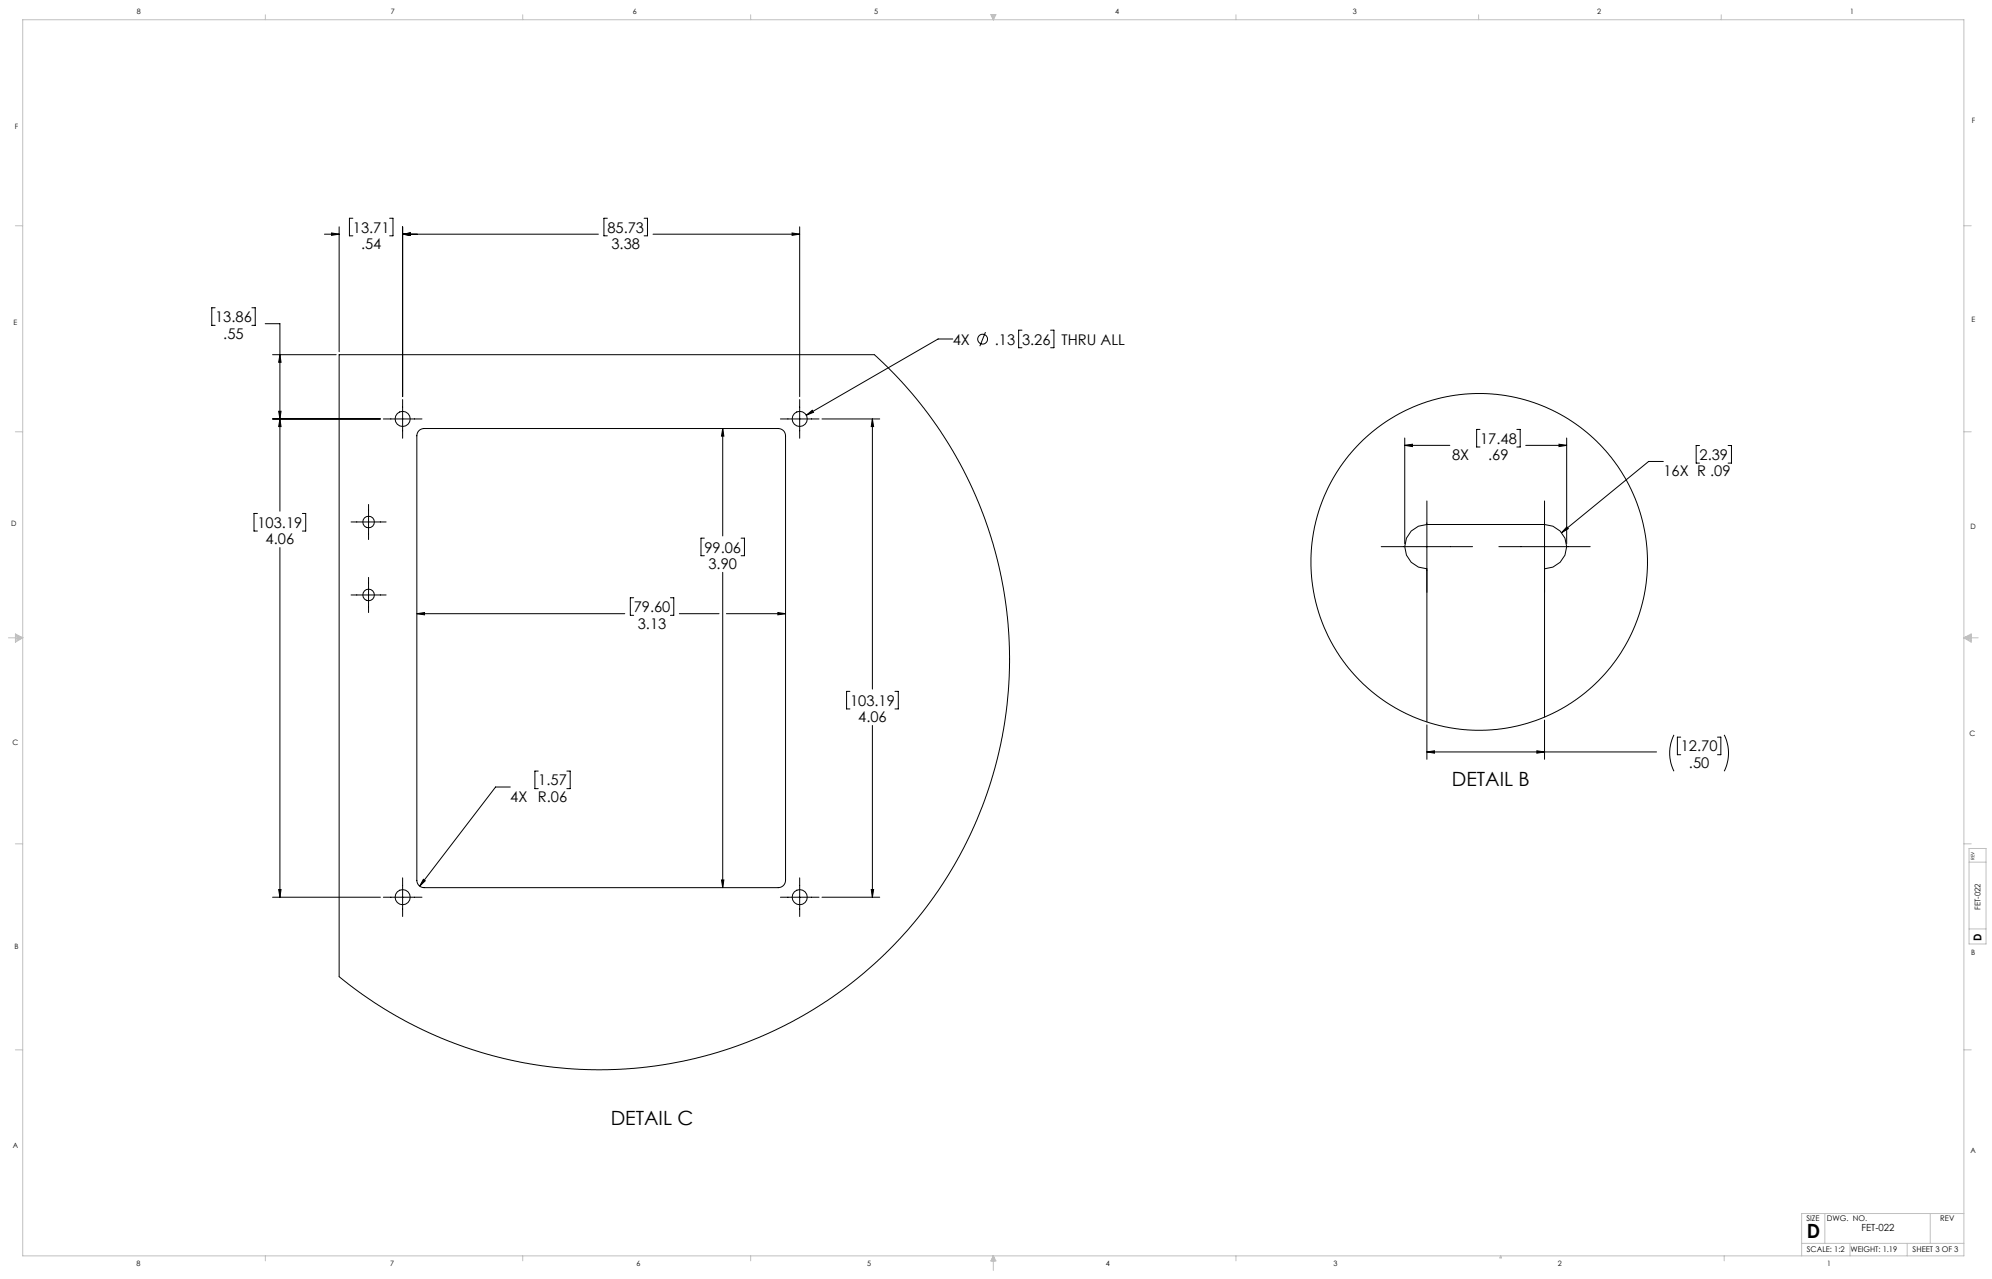
[picture p317: page 3]
.13 3.26 THRU ALL; DETAIL C; DETAIL B; FREV FET-022; SCALE: 1:2 WEIGHT: 1.19; SHEET 3 OF 3
