ten-point-nine/freETarget/Mechanical/Dimensioned Drawings/Competition Target/FRE-007 RIGHT SIDE PANEL.PDF

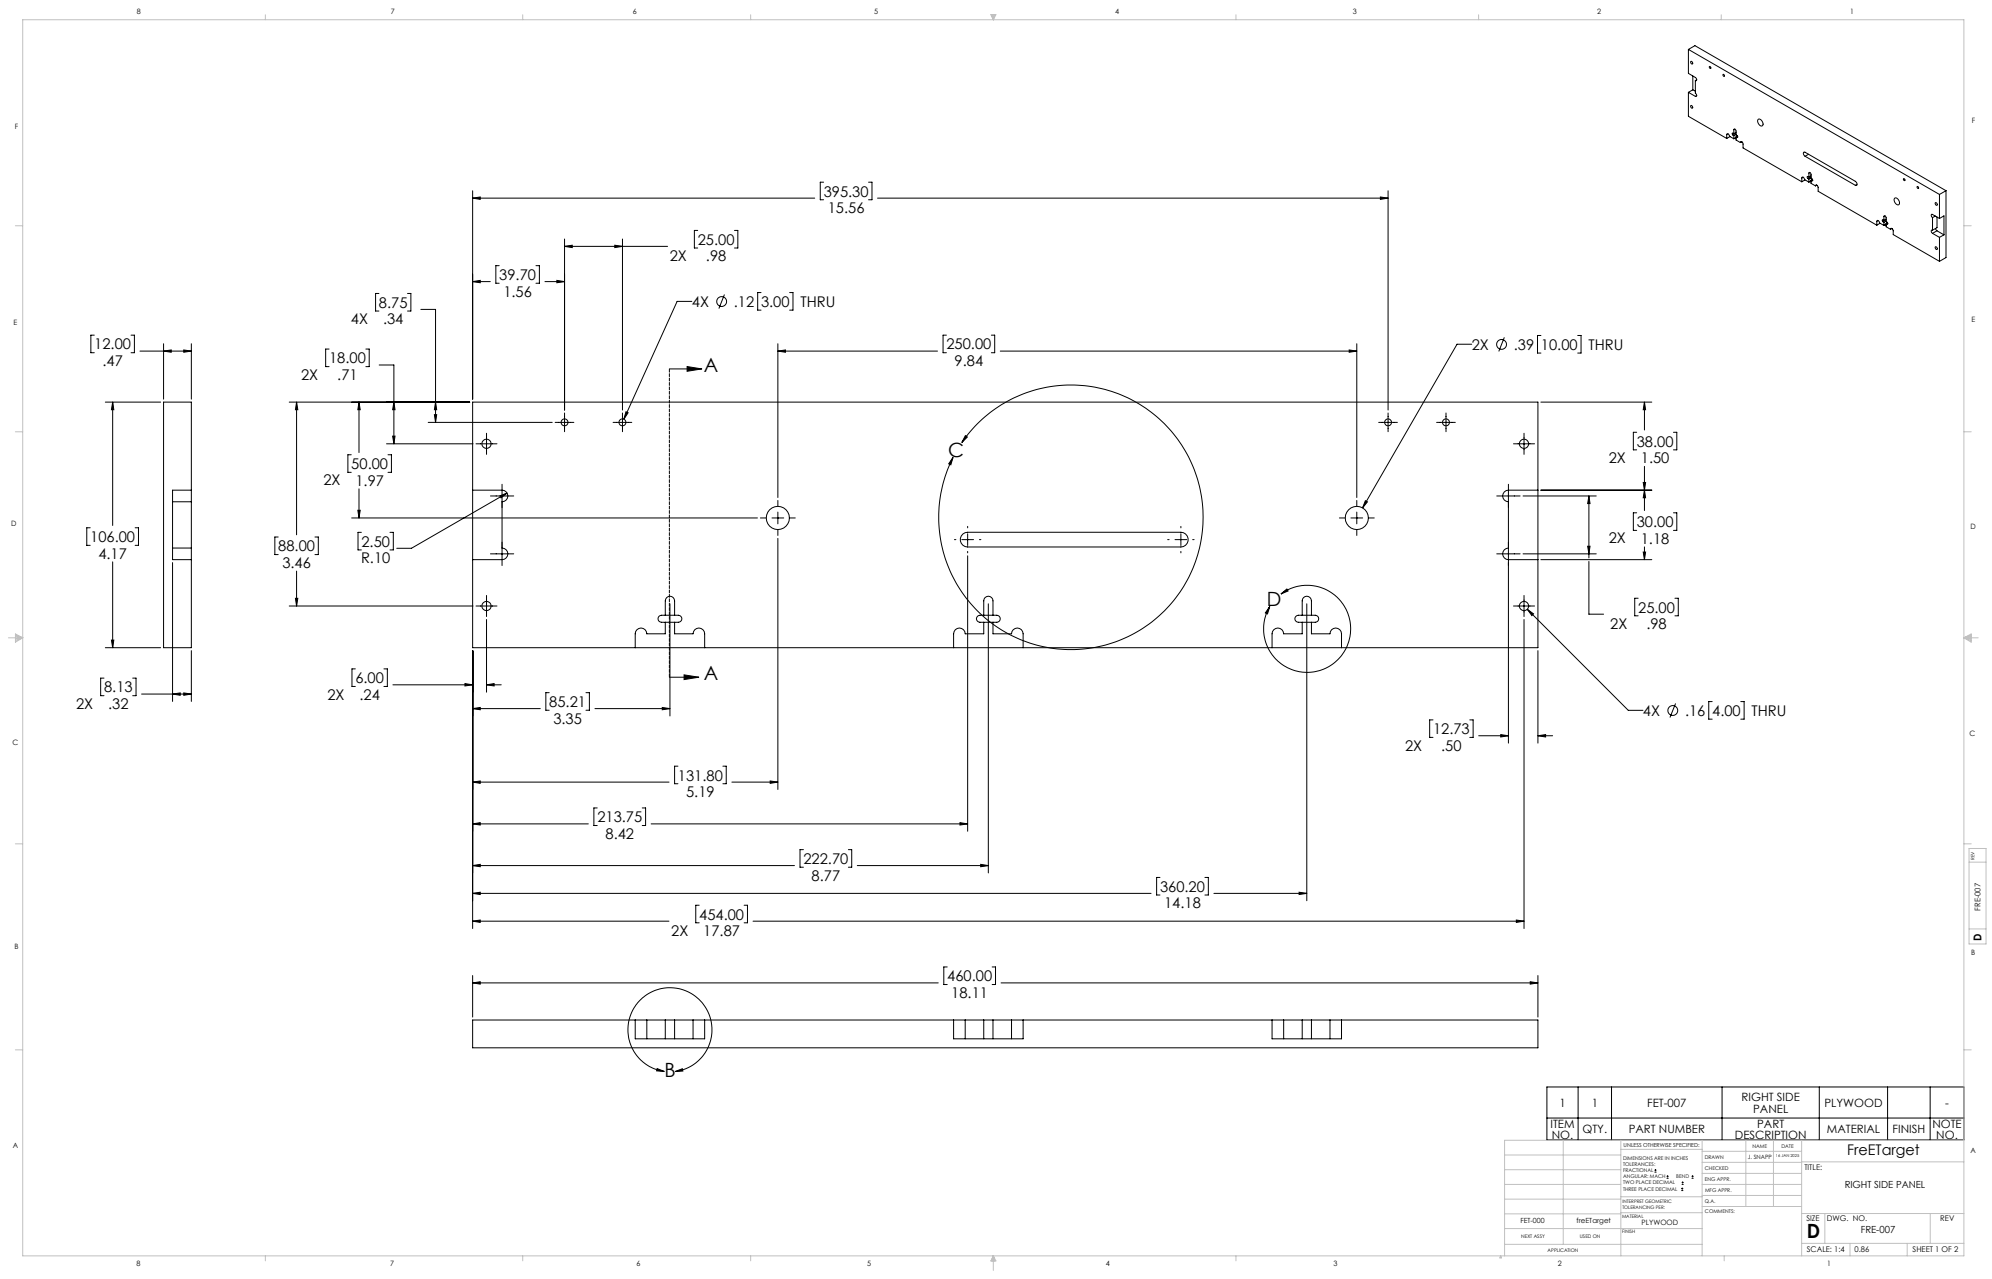
[picture p318: page 1]
.16 4.00 THRU; .12 3.00 THRU; .39 10.00 THRU; FREV FRE-007; SHEET 1 OF 2; RIGHT SIDE PANEL; 16 JAN 2025 J. SNAPP; SCALE: 1:4 0.86; DWG. NO.; REV; FreETarget NAME; DATE; MFG APPR.; ENG APPR.; INTERPRET GEOMETRIC TOLERANCING PER:; ANGULAR: MACH; BEND; NEXT ASSY; USED ON

1 | 1 | FET-007 | RIGHT SIDE PANEL | PLYWOOD | | -
ITEM NO. | QTY. | PART NUMBER | DESCRIPTION PART | MATERIAL | FINISH | NOTE NO.

UNLESS OTHERWISE SPECIFIED:

DIMENSIONS ARE IN INCHES
TOLERANCES:
FRACTIONAL
TWO PLACE DECIMAL
THREE PLACE DECIMAL

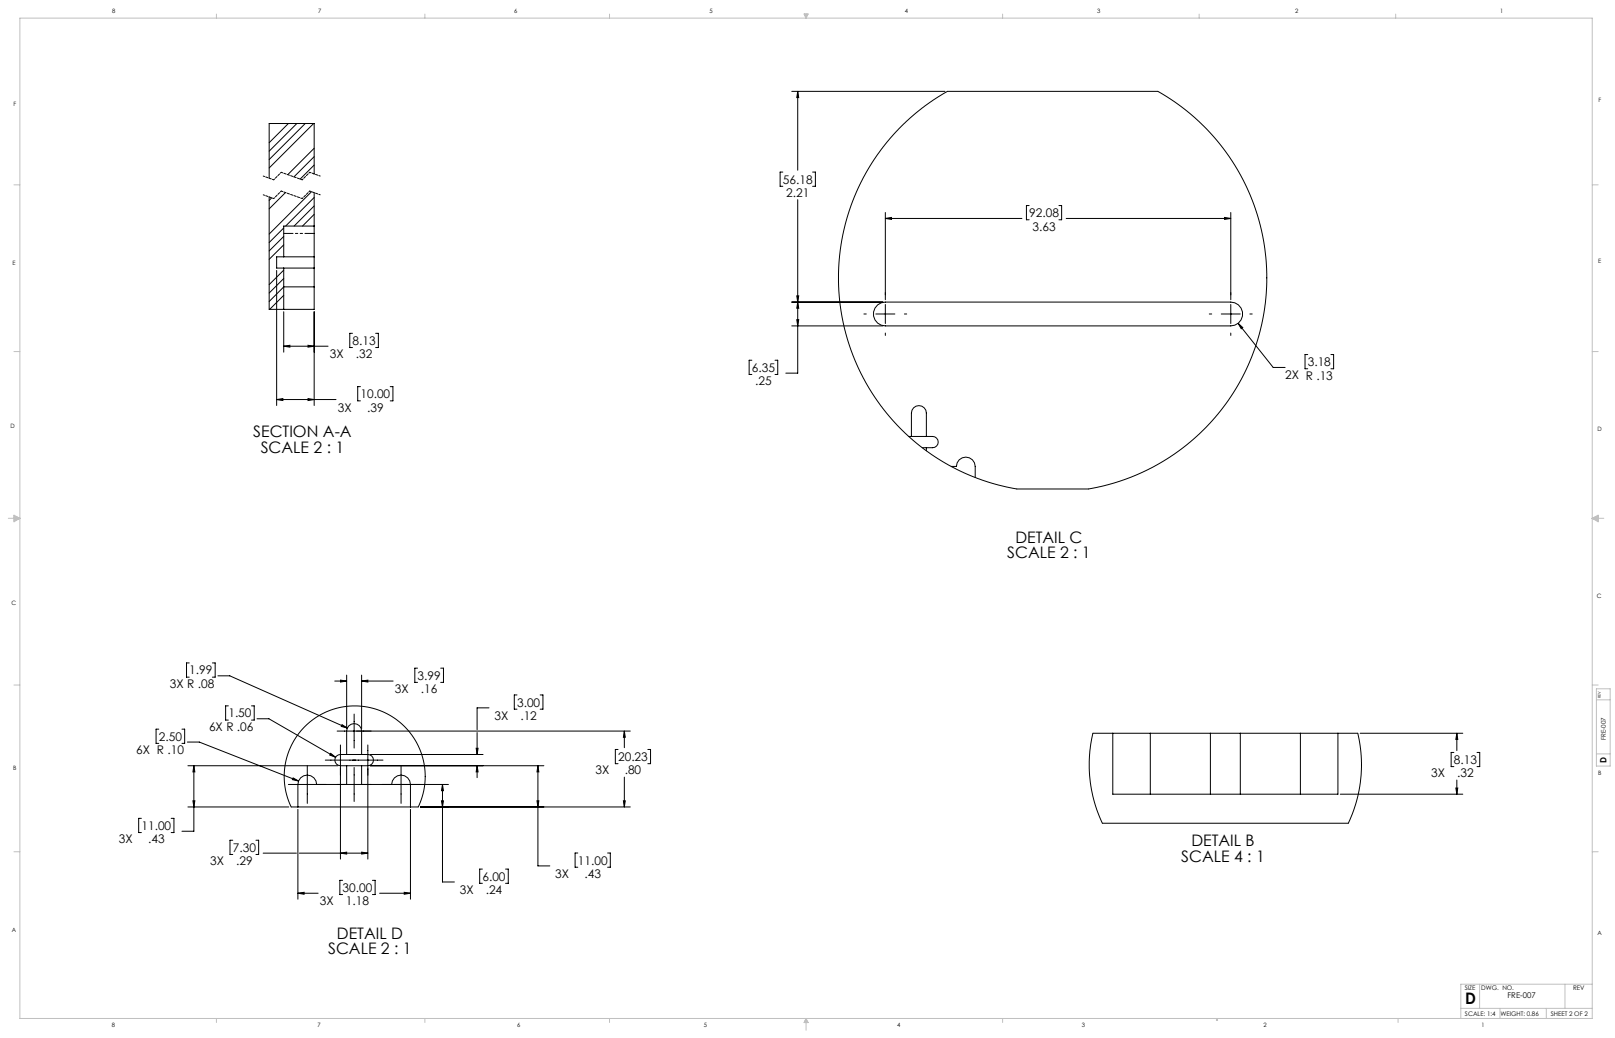
[picture p319: page 2]
DETAIL C SCALE 2 : 1; DETAIL D SCALE 2 : 1; SECTION A-A SCALE 2 : 1; DETAIL B SCALE 4 : 1; FREV FRE-007; SCALE: 1:4 WEIGHT: 0.86; SHEET 2 OF 2; DWG. NO.; REV
