ten-point-nine/freETarget/Mechanical/Dimensioned Drawings/Competition Target/FRE-008 LEFT SIDE PANEL.PDF

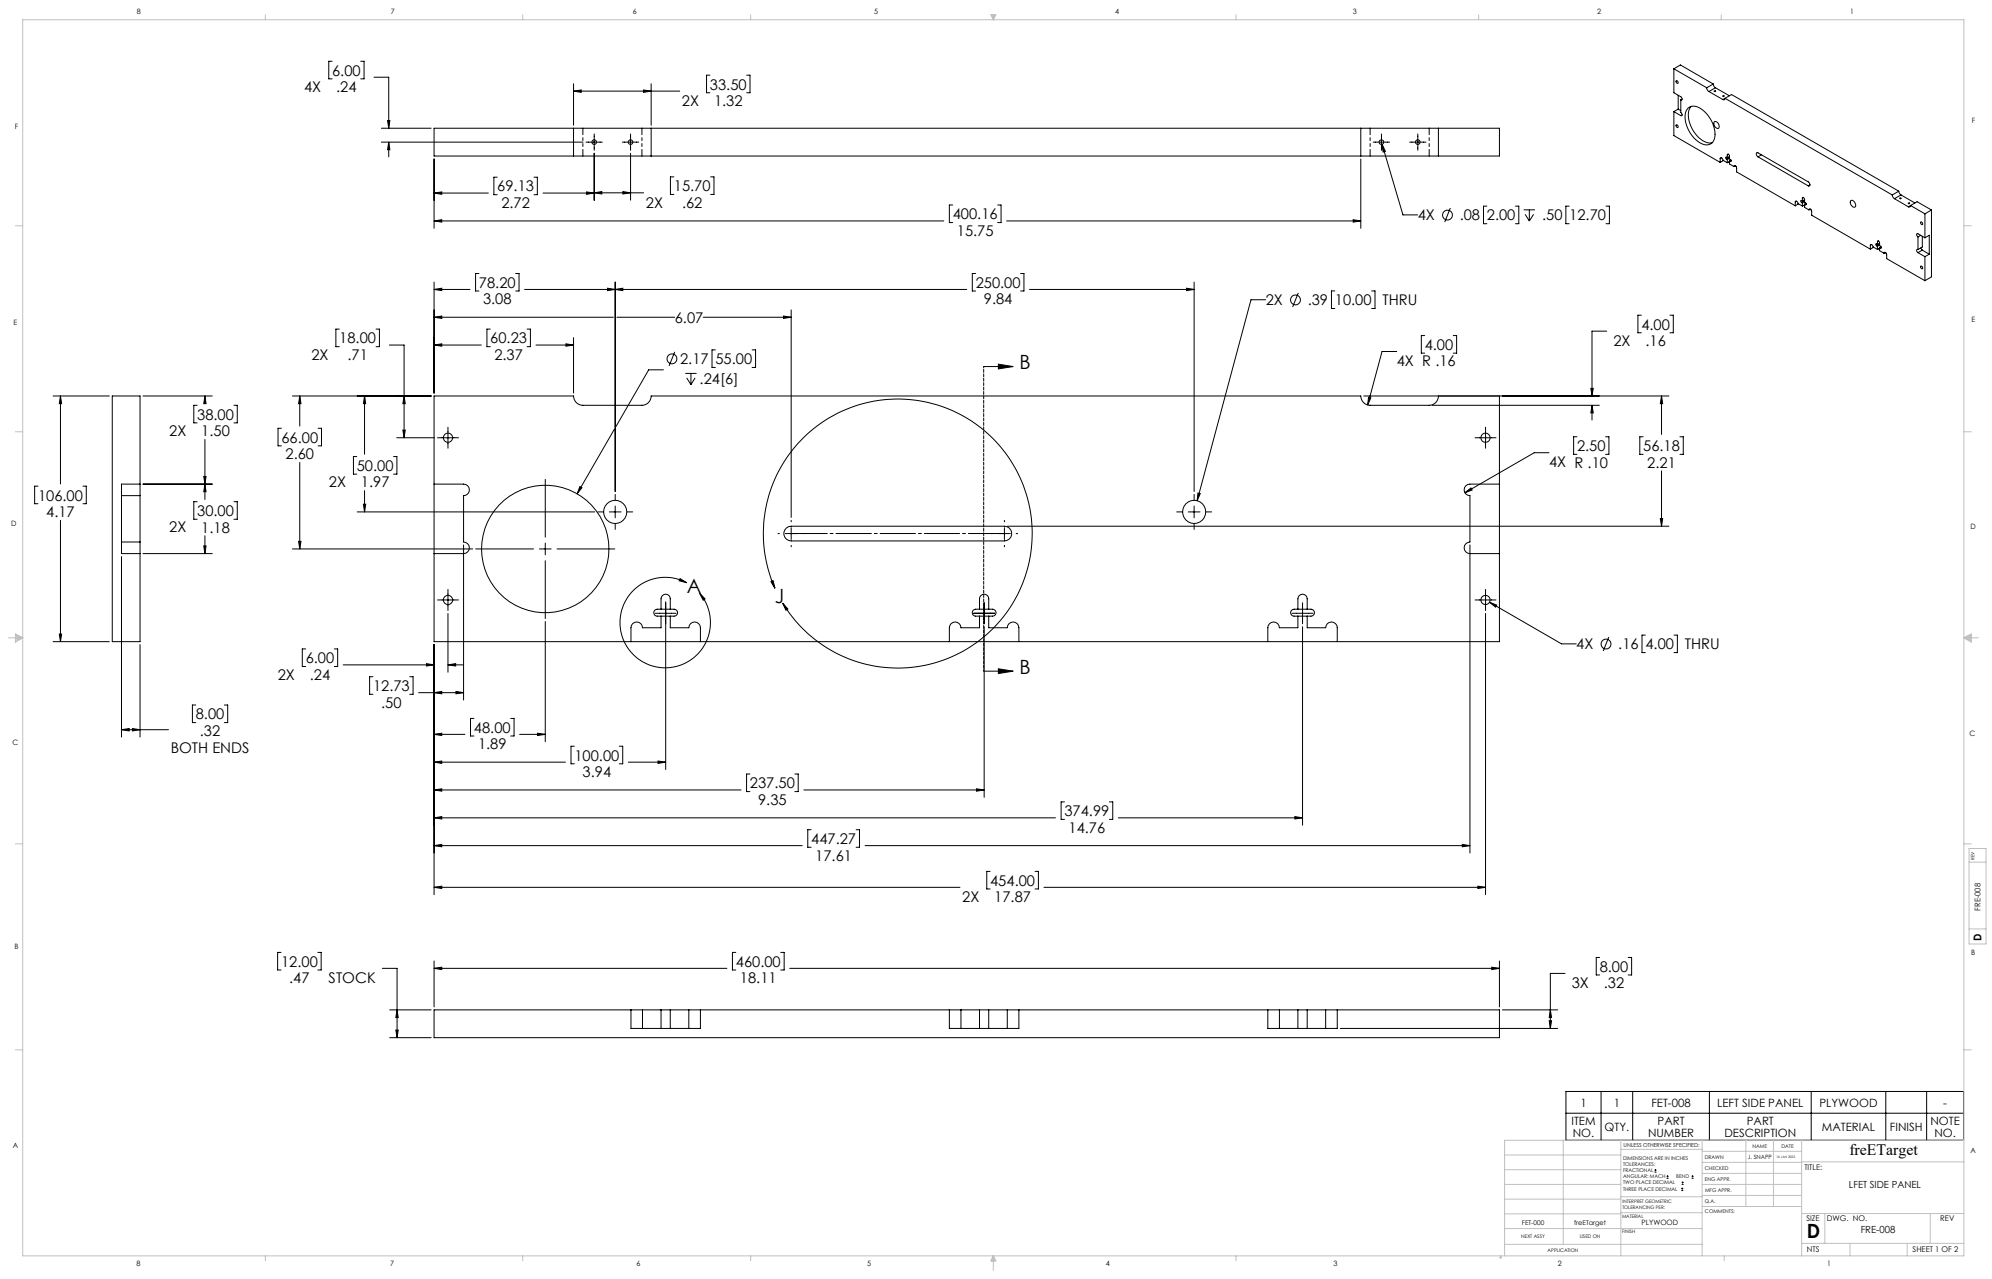
[picture p320: page 1]
.39 10.00 THRU; .16 4.00 THRU; .47 STOCK; BOTH ENDS; FREV FRE-008; SHEET 1 OF 2; J. SNAPP 16 JAN 2025; DWG. NO.; REV; freETarget NAME; DATE; MFG APPR.; ENG APPR.; INTERPRET GEOMETRIC TOLERANCING PER:; ANGULAR: MACH; BEND; NEXT ASSY; USED ON

1 | 1 | FET-008 | LEFT SIDE PANEL | PLYWOOD | | -
ITEM NO. | QTY. | PART NUMBER | DESCRIPTION PART | MATERIAL | FINISH | NOTE NO.

UNLESS OTHERWISE SPECIFIED:

DIMENSIONS ARE IN INCHES
TOLERANCES:
FRACTIONAL
TWO PLACE DECIMAL
THREE PLACE DECIMAL

LFET SIDE PANEL

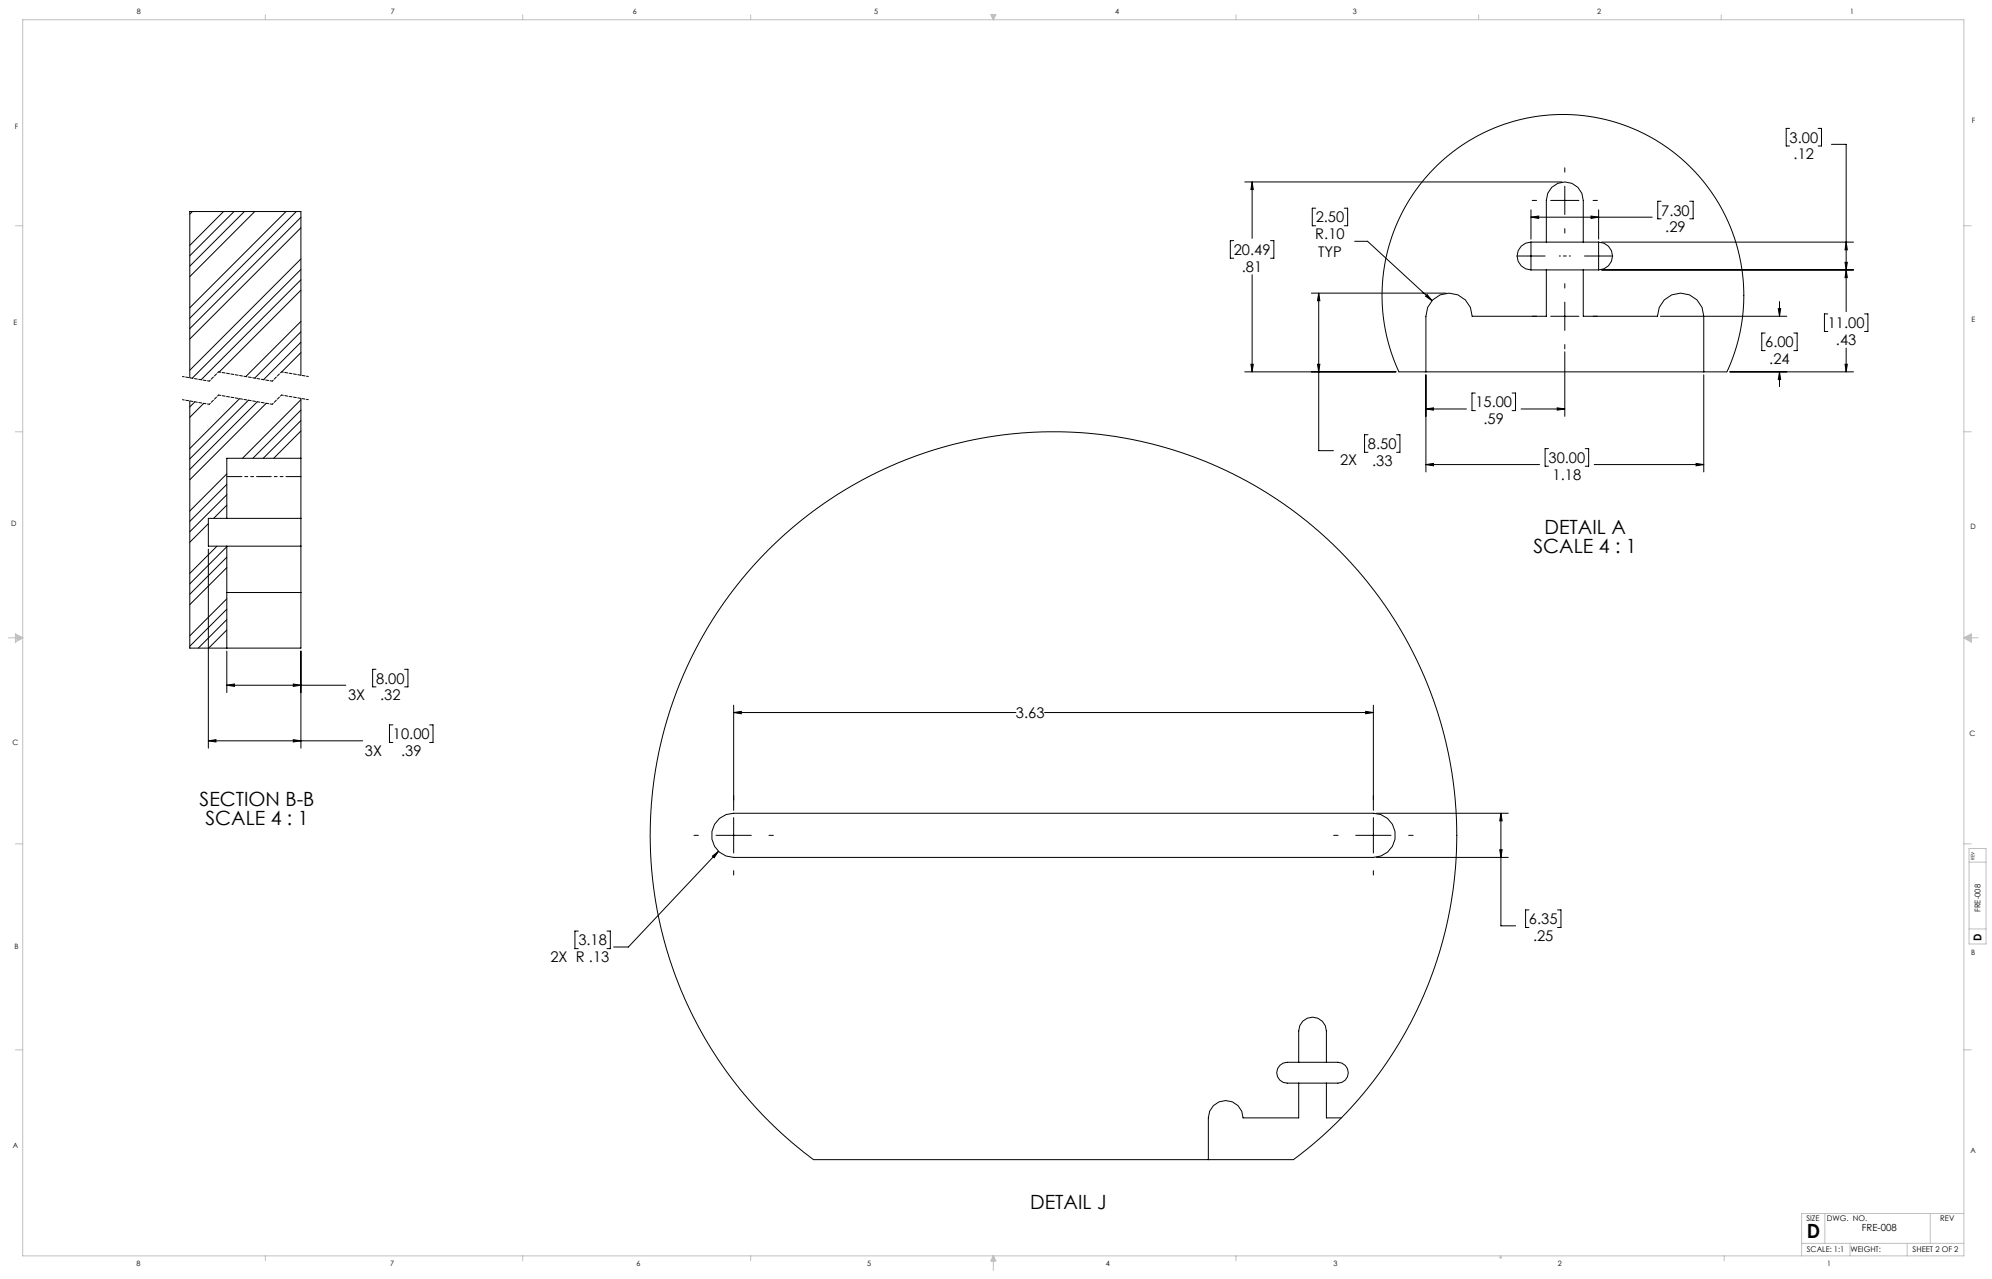
[picture p321: page 2]
SECTION B-B SCALE 4 : 1; DETAIL A SCALE 4 : 1; DETAIL J; FREV FRE-008; SCALE: 1:1 WEIGHT:; SHEET 2 OF 2; DWG. NO.; REV
