ten-point-nine/freETarget/KiCad/Filter/Filter Network.pdf

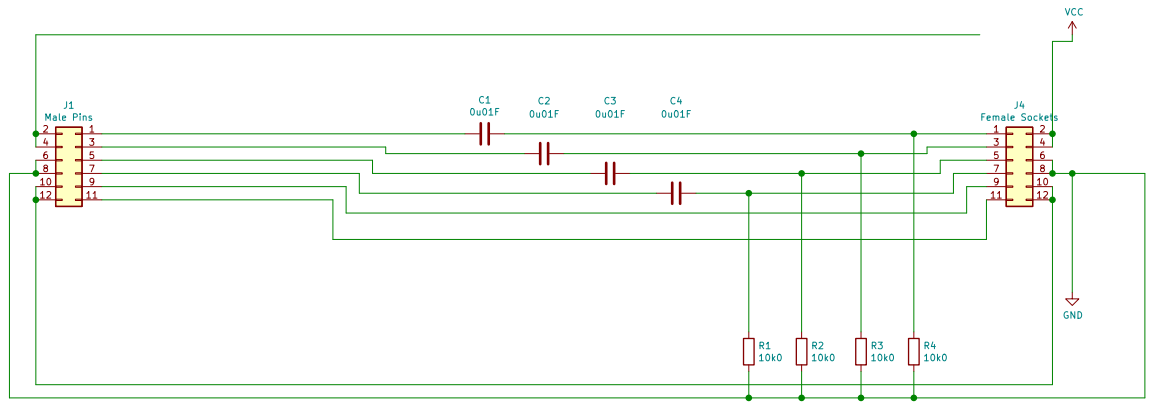
[picture p322: page 1]

Id: 1/1 Title: File: Filter Network.sch Sheet: /
