ten-point-nine/freETarget/KiCad/Sensors/Sensors.pdf

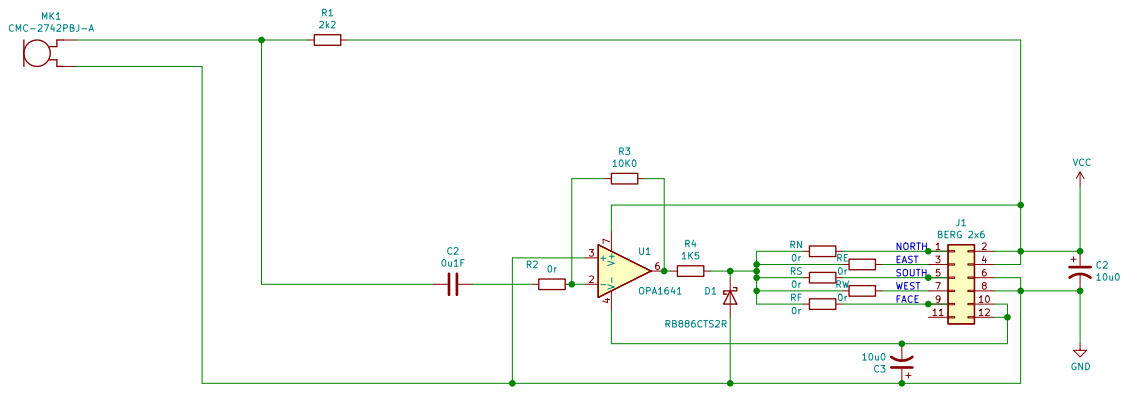
[picture p323: page 1]

File: Sensors.sch Sheet: / C2

Id: 1/1 Title: freETarget Sensor Board
