ten-point-nine/freETarget/KiCad/Version 3.1 Schematics/SCHEMATIC_HIGH_PASS Filter_3p1.pdf

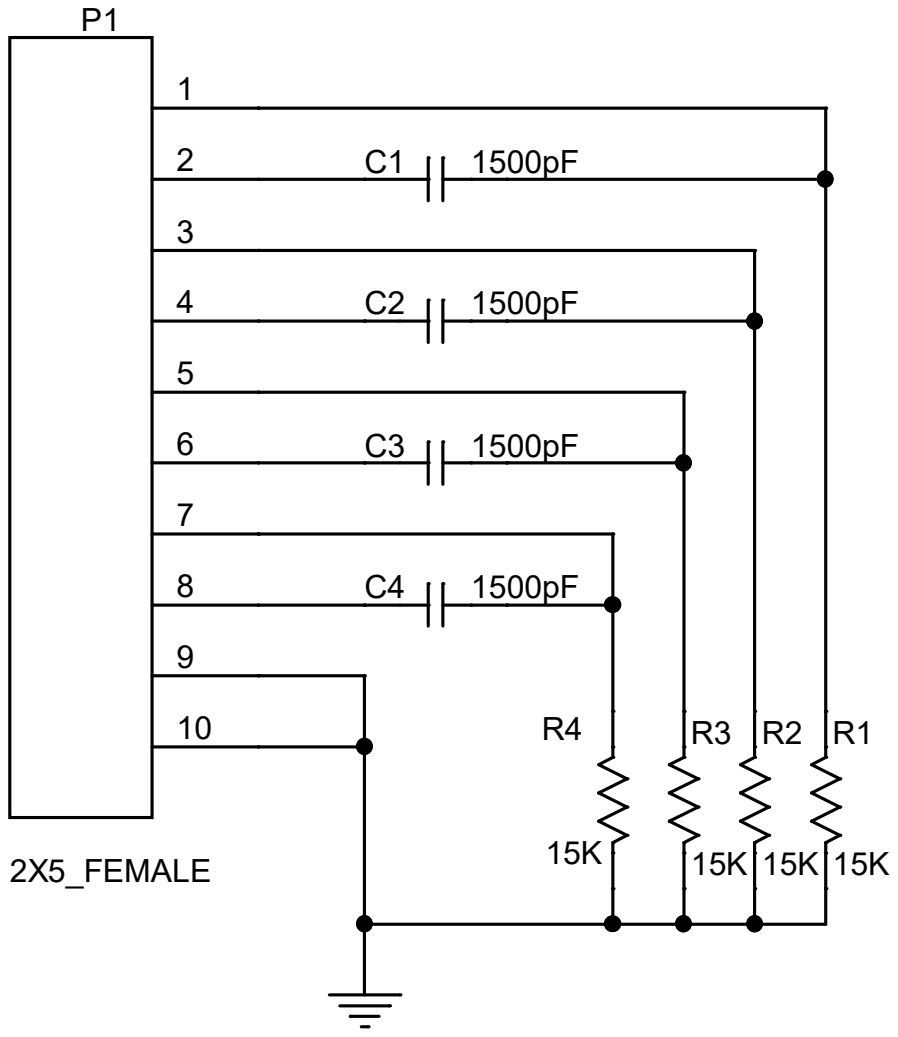
[picture p324: page 1]
