ten-point-nine/freETarget/KiCad/Version 3.1 Schematics/SCHEMATIC_SENSOR_3p1.pdf

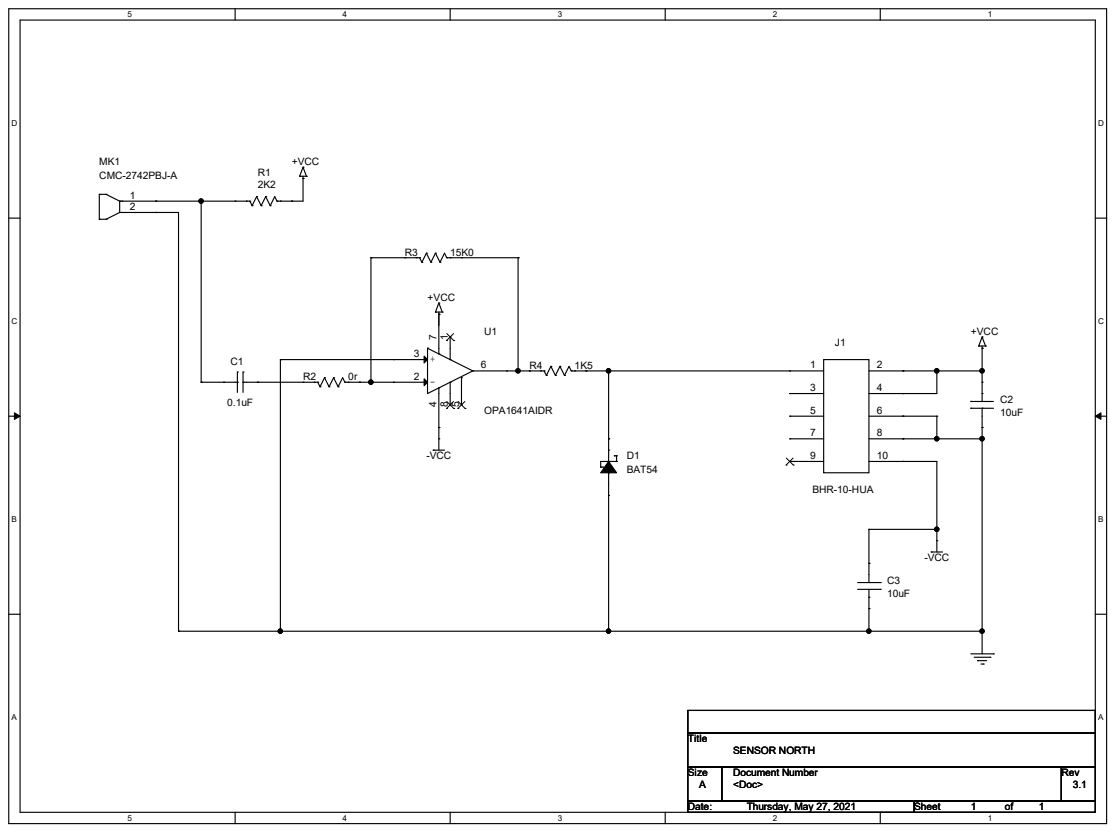
[picture p325: page 1]

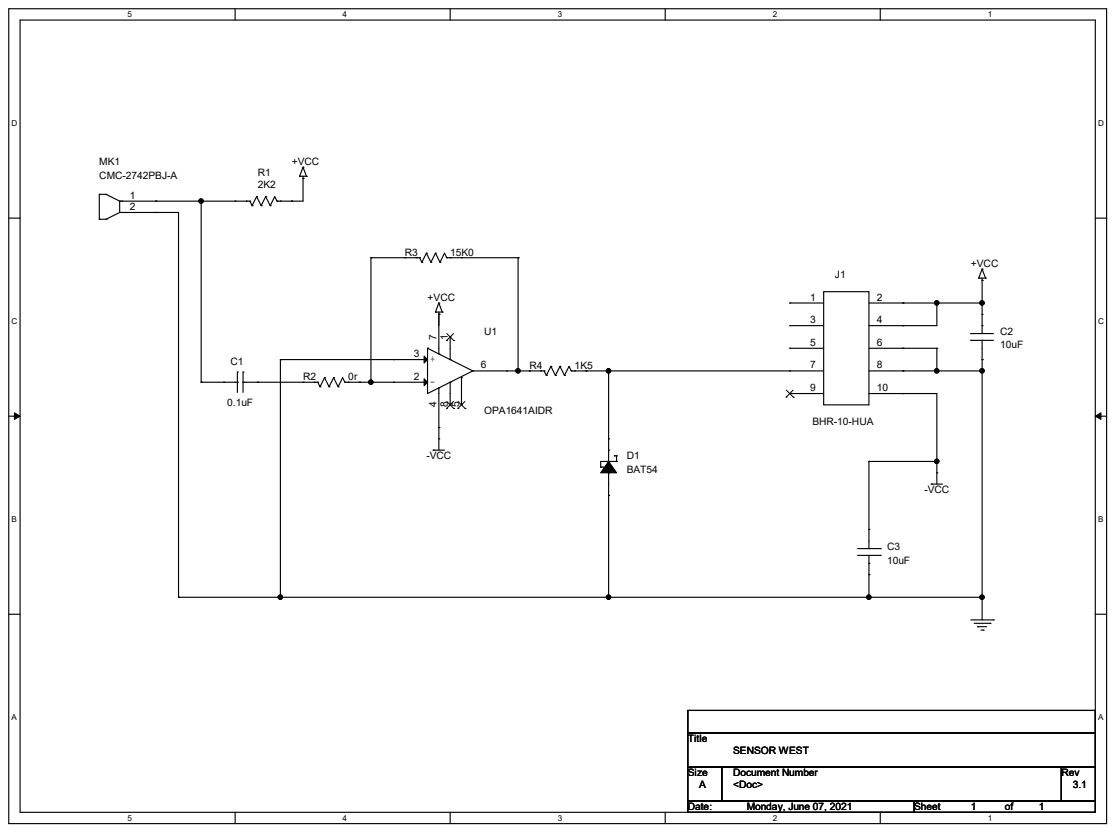
[picture p326: page 2]

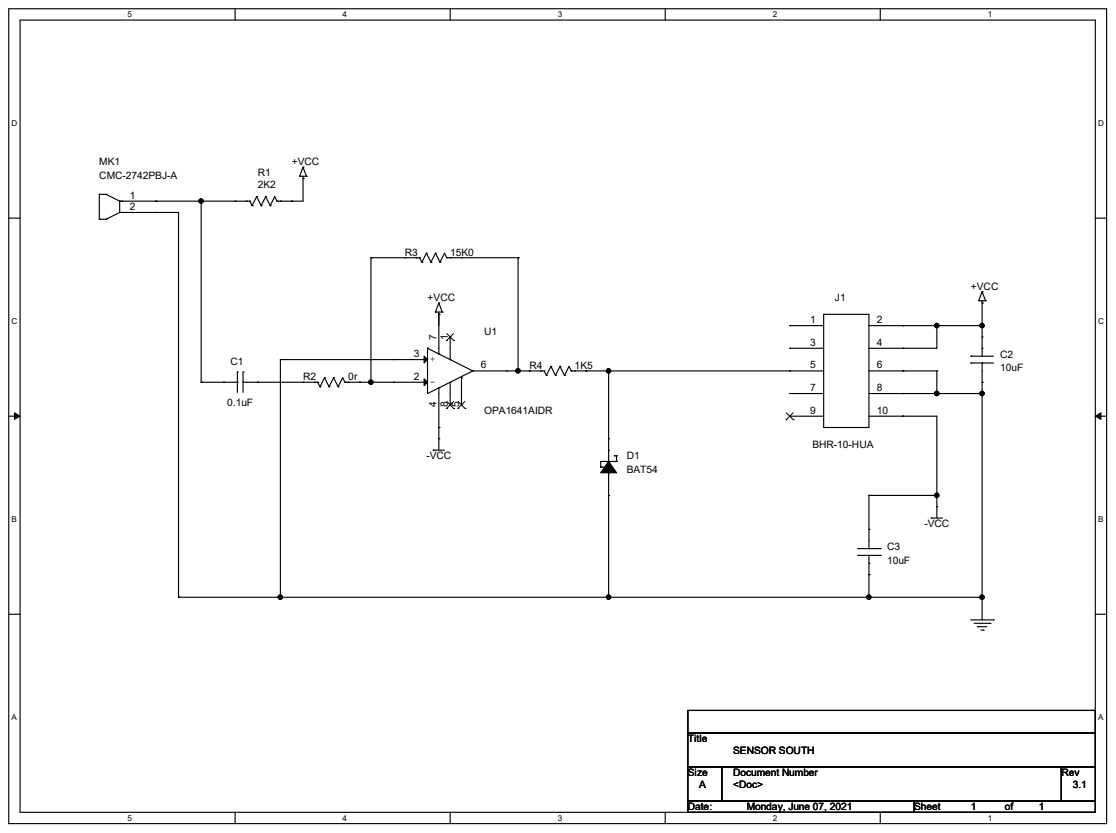
[picture p327: page 3]

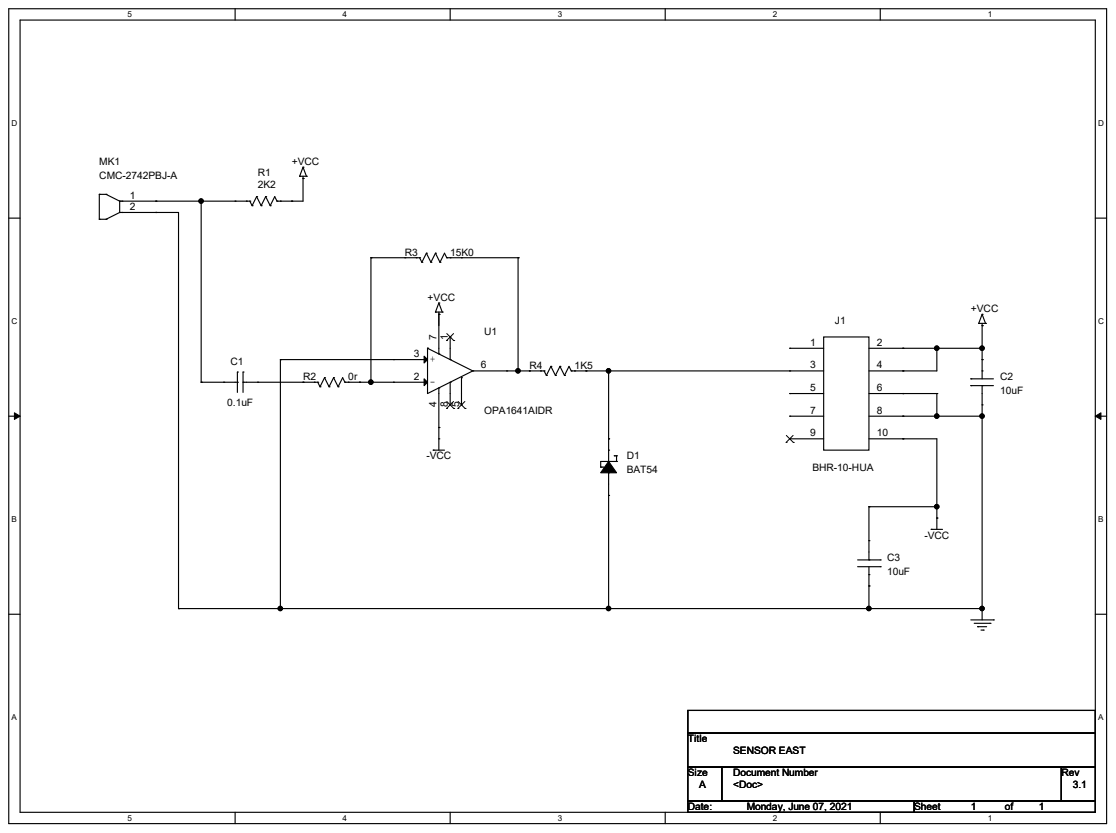
[picture p328: page 4]

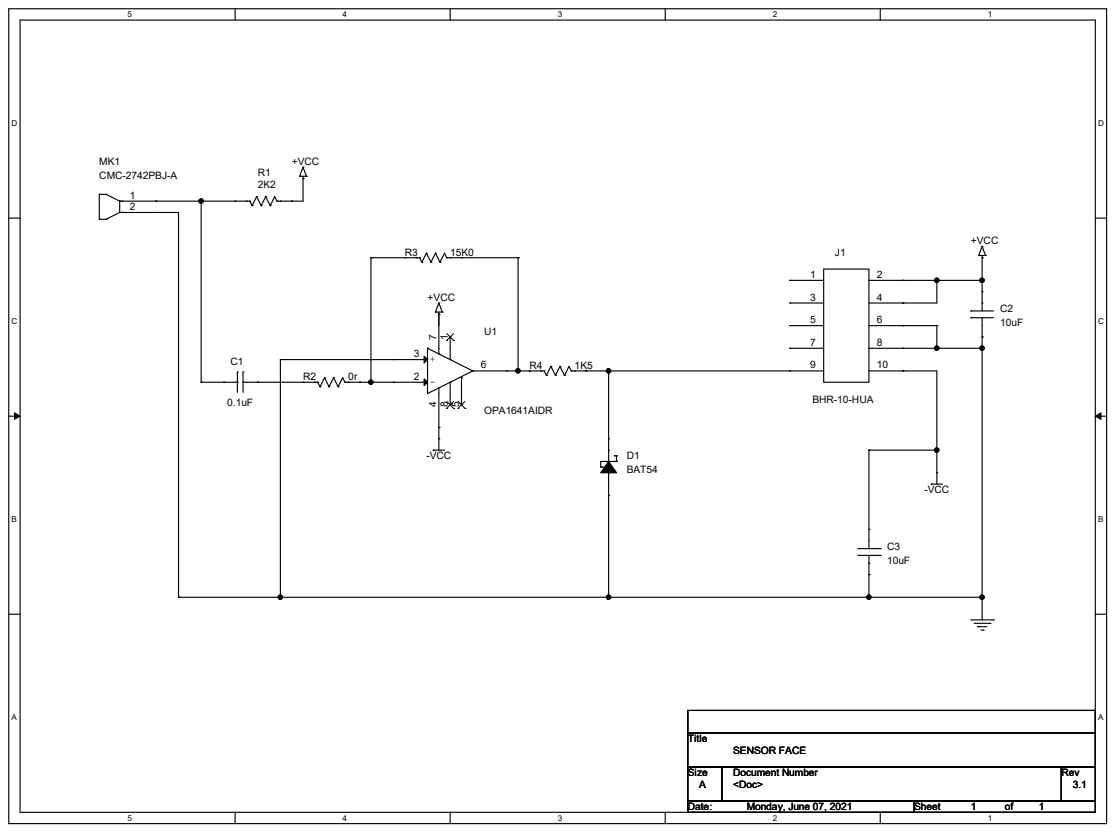
[picture p329: page 5]
