ten-point-nine/freETarget/Software/ESP32/main/compute_hit.c

/*****************************************************************************
 *
 * Compute_hit.c
 *
 * Determine the score
 *
 *****************************************************************************/
#include "math.h"
#include "stdio.h"
#include "math.h"
#include "stdbool.h"
#include "gpio_types.h"
#include "driver\gpio.h"

#include "freETarget.h"
#include "analog_io.h"
#include "helpers.h"
#include "json.h"
#include "mfs.h"
#include "diag_tools.h"
#include "token.h"
#include "timer.h"
#include "compute_hit.h"
#include "json.h"
#include "calibrate.h"

/*
 *  Definitions
 */
#define THRESHOLD (0.001)

#define R(x) (((x) + location) % 4) // Rotate the target by location points

/*
 *  Variables
 */
sensor_t s[4] = {
    // Contains variables,do not make const
    {0, {'n', "NORTH_LO", LED_NORTH_FAILED, RUN_NORTH_LO, BIT_NORTH_LO}, {'N', "NORTH_HI", LED_NORTH_FAILED, RUN_NORTH_HI, BIT_NORTH_HI}},
    {1, {'e', "EAST_LO", LED_EAST_FAILED, RUN_EAST_LO, BIT_EAST_LO},     {'E', "EAST_HI", LED_EAST_FAILED, RUN_EAST_HI, BIT_EAST_HI}    },
    {2, {'s', "SOUTH_LO", LED_SOUTH_FAILED, RUN_SOUTH_LO, BIT_SOUTH_LO}, {'S', "SOUTH_HI", LED_SOUTH_FAILED, RUN_SOUTH_HI, BIT_SOUTH_HI}},
    {3, {'w', "WEST_LO", LED_WEST_FAILED, RUN_WEST_LO, BIT_WEST_LO},     {'W', "WEST_HI", LED_WEST_FAILED, RUN_WEST_HI, BIT_WEST_HI}    }
};

unsigned int        pellet_calibre;         // Time offset to compensate for pellet diameter
static time_count_t wdt;                    // Warchdog  timer

static void remap_target(shot_record_t *s); // Map a club target if used

/*----------------------------------------------------------------
 *
 * @function: init_sensors()
 *
 * @brief: Setup the constants in the strucure
 *
 * @return: Sensor array updated with current geometry
 *
 *----------------------------------------------------------------
 *
 *                             N     (+,+)
 *
 *
 *                      W      0--R-->E
 *
 *
 *               (-,-)         S
 *
 * The layout of the sensors is shown above.  0 is the middle of
 * the target, and the sensors located at the cardinal points.
 *
 * This function takes the physical location of the sensors (mm)
 * and generates the sensor array based on time. (ex us / mm)
 *--------------------------------------------------------------*/
void init_sensors(void)
{
  DLT(DLT_APPLICATION, SEND(CONSOLE, sprintf(_xs, "init_sensors()");))

  /*
   * Determine the speed of sound and ajust
   */
  s_of_sound     = speed_of_sound(temperature_C(), humidity_RH());
  pellet_calibre = ((real_t)json_calibre_x10 / s_of_sound / 2.0d / 10.0d) * OSCILLATOR_MHZ; // Clock adjustement

  /*
   * Work out the geometry of the sensors
   */
  s[N].index = N;
  s[N].x     = json_north_x / s_of_sound * OSCILLATOR_MHZ;
  s[N].y     = (json_sensor_dia / 2.0d + json_north_y) / s_of_sound * OSCILLATOR_MHZ;
  s[N].x_mm  = json_north_x;
  s[N].y_mm  = json_sensor_dia / 2.0d + json_north_y;

  s[E].index = E;
  s[E].x     = (json_sensor_dia / 2.0d + json_east_x) / s_of_sound * OSCILLATOR_MHZ;
  s[E].y     = (0.0d + json_east_y) / s_of_sound * OSCILLATOR_MHZ;
  s[E].x_mm  = json_sensor_dia / 2.0d + json_east_x;
  s[E].y_mm  = json_east_y;

  s[S].index = S;
  s[S].x     = 0.0d + json_south_x / s_of_sound * OSCILLATOR_MHZ;
  s[S].y     = -(json_sensor_dia / 2.0d + json_south_y) / s_of_sound * OSCILLATOR_MHZ;
  s[S].x_mm  = json_south_x;
  s[S].y_mm  = -(json_sensor_dia / 2.0d + json_south_y);

  s[W].index = W;
  s[W].x     = -(json_sensor_dia / 2.0d + json_west_x) / s_of_sound * OSCILLATOR_MHZ;
  s[W].y     = json_west_y / s_of_sound * OSCILLATOR_MHZ;
  s[W].x_mm  = -(json_sensor_dia / 2.0d + json_west_x);
  s[W].y_mm  = json_west_y;

  /*
   *  All done, return
   */
  return;
}

/*----------------------------------------------------------------
 *
 * @funtion: compute_hit
 *
 * @brief: Determine the location of the hit
 *
 * @return: Sensor location used to recognize shot
 *          MISS indicates calculation failed
 *
 *----------------------------------------------------------------
 *
 * See freETarget documentaton for algorithm
 *
 *--------------------------------------------------------------*/

unsigned int compute_hit(shot_record_t *shot)      // Storing the results
{
  real_t reference;                                // Time of reference counter
  int    location;                                 // Sensor chosen for reference location
  int    i, count;
  real_t estimate;                                 // Estimated position
  real_t last_estimate, error;                     // Location error
  real_t x_avg, y_avg;                             // Running average location
  real_t z_offset_clock;                           // Time offset between paper and sensor plane

  x_avg = 0;
  y_avg = 0;

  ft_timer_new(&wdt, 20, NULL, "compute hit wdt"); // Watchdog timer

  DLT(DLT_APPLICATION, SEND(CONSOLE, sprintf(_xs, "compute_hit()");))

  /*
   *  Check for a miss, If there is a face strike, or one of the timers did not start, it's a miss
   */
  if ( (shot->face_strike != 0) || (shot->timer_count[N] == 0) || (shot->timer_count[E] == 0) || (shot->timer_count[S] == 0) ||
       (shot->timer_count[W] == 0) )
  {
    DLT(DLT_APPLICATION, SEND(CONSOLE, sprintf(_xs, "Miss detected");))
    return MISS;
  }

  /*
   *  Compute the current geometry based on the speed of sound
   */
  init_sensors();
  z_offset_clock = (real_t)json_z_offset * OSCILLATOR_MHZ / s_of_sound; // Clock adjustement for paper to sensor difference
  DLT(DLT_APPLICATION | DLT_VERBOSE, SEND(CONSOLE, sprintf(_xs, "z_offset_clock: %4.2f", z_offset_clock);))

  /*
   *  Display the timer registers if in trace mode
   */
  DLT(DLT_APPLICATION,
      for ( i = N; i <= W_HI; i++ ) SEND(CONSOLE, sprintf(_xs, "%s: %d ", find_sensor(1 << i)->long_name, shot->timer_count[i]);))

  /*
   * Determine the location of the reference counter (longest time)
   */
  reference = shot->timer_count[N];
  location  = N;
  for ( i = N; i <= W; i++ )
  {
    if ( shot->timer_count[i] > reference )
    {
      reference = shot->timer_count[i];
      location  = i;
    }
  }

  DLT(DLT_APPLICATION | DLT_VERBOSE,
      SEND(CONSOLE, sprintf(_xs, "Reference: %4.2f   location: %s", reference, find_sensor(1 << location)->long_name);))

  /*
   * Correct the time to remove the shortest distance
   */
  for ( i = N; i <= W; i++ )
  {
    s[i].count    = reference - shot->timer_count[i];
    s[i].is_valid = true;
    if ( shot->timer_count[i] == 0 )
    {
      shot->session_type = SESSION_VALID | json_session_type;
    }
  }

  DLT(DLT_APPLICATION | DLT_VERBOSE, {
    SEND(CONSOLE, sprintf(_xs, "\r\nMicroseconds ");)
    for ( i = 0; i < 8; i++ )
      SEND(CONSOLE, sprintf(_xs, "%s: %4.2f ", find_sensor(1 << i)->long_name, (real_t)s[i].count / ((real_t)OSCILLATOR_MHZ));)
  })

  /*
   * Fill up the structure with the counter geometry
   */
  for ( i = N; i <= W; i++ )
  {
    s[i].b = s[i].count;
    s[i].c = sqrt(SQ(s[(i) % 4].x - s[(i + 1) % 4].x) + SQ(s[(i) % 4].y - s[(i + 1) % 4].y));
  }

  for ( i = N; i <= W; i++ )
  {
    s[i].a = s[(i + 1) % 4].b;
  }

  /*
   *  Loop and calculate the unknown radius (estimate)
   */
  estimate = 0;
  for ( i = N; i <= W; i++ )
  {
    estimate += s[i].count;
  }
  estimate = estimate / 4.0;
  DLT(DLT_APPLICATION | DLT_VERBOSE, SEND(ALL, sprintf(_xs, "estimate: %4.2f", estimate);))

  /*
   *  Loop and calculate the unknown radius (estimate)
   */

  error = 999999; // Start with a big error
  count = 0;

  /*
   * Iterate to minimize the error
   */
  while ( error > THRESHOLD )
  {
    x_avg         = 0;         // Zero out the average values
    y_avg         = 0;
    last_estimate = estimate;

    for ( i = N; i <= W; i++ ) // Calculate X/Y for each sensor
    {
      if ( find_xy_3D(&s[i], estimate, z_offset_clock) )
      {
        x_avg += s[i].xs;      // Keep the running average
        y_avg += s[i].ys;
      }
      else                     // The calculation failed
      {
        DLT(DLT_APPLICATION, SEND(CONSOLE, sprintf(_xs, "Calculations failed");))
        return MISS;           // Abort
      }
    }

    x_avg /= 4.0d;
    y_avg /= 4.0d;

    estimate = sqrt(SQ(s[location].x - x_avg) + SQ(s[location].y - y_avg));
    error    = fabs(last_estimate - estimate);

    DLT(DLT_APPLICATION | DLT_VERBOSE,
        SEND(CONSOLE, sprintf(_xs, "x_avg: %4.2f  y_avg: %4.2f estimate: %4.2f error: %4.2f", x_avg, y_avg, estimate, error);))

    count++;
    if ( count > 20 )
    {
      break; // Exit if we can't find a solution
    }
  }

  /*
   * All done return
   */

  shot->x = x_avg;
  shot->y = y_avg;

  if ( isnan(shot->x) || isnan(shot->y) ) // If the computation failed,
  {
    DLT(DLT_APPLICATION, SEND(CONSOLE, sprintf(_xs, "Computation resulted in NaN");))
    return MISS;                          // return an error
  }

  return location;
}

/*----------------------------------------------------------------
 *
 * @function: find_xy_3D
 *
 * @brief: Calaculate where the shot seems to lie
 *
 * @return: TRUE if the shot was computed correctly
 *
 *----------------------------------------------------------------
 *
 *  Using the law of Cosines
 *
 *                    C
 *                 /     \
 *             b             a
 *          /                   \
 *     A ------------ c ----------  B
 *
 *  a^2 = b^2 + c^2 - 2(bc)cos(A)
 *
 *  Rearranging terms
 *            ( a^2 - b^2 - c^2 )
 *  A = arccos( ----------------)
 *            (      -2bc       )
 *
 *  In our system, a is the estimate for the shot location
 *                 b is the measured time + estimate of the shot location
 *                 c is the fixed distance between the sensors
 *
 * See freETarget documentaton for algorithm
 *
 * If there is a large distance between the target plane and the
 * sensor plane, then the distance between the computed position
 * and the actual postion includes a large error the further
 * the pellet hits from the centre.
 *
 * This is because the sound path from the target to the
 * sensor includes a slant distance from the paper to the sensor
 * ex.
 *
 *                                            // ()  Sensor  ---
 *                          Slant Range  ////     |           |
 *                                 ////           |      z_offset
 * ==============================@================|= -----------
 *                               | Paper Distance |
 *
 * This algorithm is the same as the regular compute_hit()
 * but corrects for the sound distance based on the z_offset
 * between the paper and sensor
 *
 * Sound Distance = sqrt(Paper Distance ^2 + z_offset ^2)
 *
 * Paper Distance = sqrt(Sound Distance ^2 - z_offset ^2)
 *
 *
 *--------------------------------------------------------------*/

bool find_xy_3D(sensor_t *s,             // Sensor to be operatated on
                real_t    estimate,      // Estimated position
                real_t    z_offset_clock // Time difference between paper and sensor plane
)
{
  real_t ae, be;                         // Locations with error added
  real_t rotation;                       // Angle shot is rotated through
  real_t x;                              // Temporary value

  /*
   * Check to see if the sensor data is correct.  If not, return an error
   */
  if ( s->is_valid == false )
  {
    DLT(DLT_APPLICATION, SEND(CONSOLE, sprintf(_xs, "Sensor: %d no data", s->index);))
    return false; // Sensor did not trigger.
  }

  /*
   * It looks like we have valid data.  Carry on
   */
  x = SQ(s->a + estimate); // - SQ(z_offset_clock);
  if ( x < 0 )
  {
    SQ(s->a + estimate);
    DLT(DLT_APPLICATION, SEND(CONSOLE, sprintf(_xs, "s->a is complex, truncting");))
  }
  ae = sqrt(x);            // Dimension with error included

  x = SQ(s->b + estimate); // - SQ(z_offset_clock);
  if ( x < 0 )
  {
    DLT(DLT_APPLICATION, SEND(CONSOLE, sprintf(_xs, "s->b is complex, truncting");))
    SQ(s->b + estimate);
  }
  be = sqrt(x);

  if ( (ae + be) < s->c ) // Check for an accumulated round off error
  {
    s->angle_A = 0;       // Yes, then force to zero.
  }
  else
  {
    s->angle_A = acos((SQ(ae) - SQ(be) - SQ(s->c)) / (-2.0d * be * s->c));
  }

  /*
   *  Compute the X,Y based on the detection sensor
   */
  rotation = 0;
  switch ( s->index )
  {
    case (N):
      rotation = PI_ON_2 - PI_ON_4 - s->angle_A;
      s->xs    = s->x + ((be)*sin(rotation));
      s->ys    = s->y - ((be)*cos(rotation));
      break;

    case (E):
      rotation = s->angle_A - PI_ON_4;
      s->xs    = s->x - ((be)*cos(rotation));
      s->ys    = s->y + ((be)*sin(rotation));
      break;

    case (S):
      rotation = s->angle_A + PI_ON_4;
      s->xs    = s->x - ((be)*cos(rotation));
      s->ys    = s->y + ((be)*sin(rotation));
      break;

    case (W):
      rotation = PI_ON_2 - PI_ON_4 - s->angle_A;
      s->xs    = s->x + ((be)*cos(rotation));
      s->ys    = s->y + ((be)*sin(rotation));
      break;

    default:
      DLT(DLT_APPLICATION, SEND(CONSOLE, sprintf(_xs, "\n\nUnknown Rotation:, %d", s->index);))
      break;
  }

  /*
   * Debugging
   */
  DLT(DLT_APPLICATION | DLT_VERBOSE, {
    SEND(CONSOLE, sprintf(_xs, "index: %d  a:%4.2f b: %4.2f ae: %4.2f  be: %4.2f c: %4.2f", s->index, s->a, s->b, ae, be, s->c);)
    SEND(CONSOLE,
         sprintf(_xs, " cos: %4.2f  sin: %4.2f  angle_A: %4.2f  x: %4.2f y: %4.2f", cos(rotation), sin(rotation), s->angle_A, s->x, s->y);)
    SEND(CONSOLE, sprintf(_xs, " rotation: %4.2f  xs: %4.2f  ys: %4.2f", rotation, s->xs, s->ys);)
  })

  /*
   *  All done, return.  The location is in the structure s->x and s->y
   */
  if ( isnan(s->x) || isnan(s->y) ) // If the computation failed,
  {
    return false;                   // return an error
  }

  return true;
}

/*----------------------------------------------------------------
 *
 * @function: prepare_score
 *
 * @brief: Send the score out over the serial port
 *
 * @return: None
 *
 *----------------------------------------------------------------
 *
 * The score is sent as:
 *
 * {"shot":n, "x":x, "y":y, "r(adius)":r, "a(ngle)": a, debugging info ..... }
 *
 * It is up to the PC program to convert x & y or radius and angle
 * into a meaningful score relative to the target.
 *
 *--------------------------------------------------------------*/
void prepare_score(shot_record_t *shot,        //  record
                   unsigned int   shot_number, // What shot are we
                   bool           miss         // TRUE if the shot was a miss
)
{
  real_t x_mm, y_mm;                           // Shot location in mm X, Y before rotation
  real_t rho_radians;                          // Angle to shot location

  DLT(DLT_APPLICATION, SEND(CONSOLE, sprintf(_xs, "prepare_score(%d)", shot_number);))

  /*
   * Grab the token ring if needed
   */
  if ( json_token != TOKEN_NONE )
  {
    while ( my_ring != whos_ring )
    {
      token_take();                                                // Grab the token ring
      ft_timer_new(&wdt, 2 * ONE_SECOND, NULL, "Watch Dog Timer"); // 2 second watchdog
      while ( (wdt != 0)                                           // Wait up to 2 seconds
              && (whos_ring != my_ring) )                          // Or we own the ring
      {
        token_poll();
      }
    }
  }

  shot->shot = shot_number;

  /*
   *  Work out the hole in perfect coordinates
   */
  x_mm = shot->x * s_of_sound * CLOCK_PERIOD;                       // Distance in mm
  y_mm = shot->y * s_of_sound * CLOCK_PERIOD;                       // Distance in mm

  rho_radians = atan2_2PI(y_mm, x_mm);                              // Angle to shot
  rho_radians += degrees_to_radians(json_sensor_angle);             // North is at the top Add in the rotation to the physical location
  shot->angle  = rho_radians + solve_spline_for_angle(rho_radians); // Correct for the spline interplation;
  shot->radius = sqrt(SQ(x_mm) + SQ(y_mm)) * solve_spline_for_scale(shot->angle); // radius in mm

  /*
   * Rotate the result based on the construction, and recompute the hit
   */
  shot->x_mm = shot->radius * cos(shot->angle) + json_x_offset; // Rotate onto the target face
  shot->y_mm = shot->radius * sin(shot->angle) + json_y_offset; // and add in sensor correction
  remap_target(shot);                                           // Change the target if needed
  shot->session_type = SESSION_VALID | json_session_type;

  DLT(DLT_CALIBRATION | DLT_VERBOSE, SEND(CONSOLE, sprintf(_xs, "x_mm: %4.2f  y_mm: %4.2f  radius: %4.2f  rho_radians: %4.2f", shot->x_mm,
                                                       shot->y_mm, shot->radius, shot->angle);))
  /*
   * All done, return
   */
  if ( json_token != TOKEN_NONE )
  {
    token_give(); // Give up the token ring
  }
  set_status_LED(LED_READY);

  return;
}

/*----------------------------------------------------------------
 *
 * @function: send_replay
 *
 * @brief: Replay the scores
 *
 * @return: None
 *
 *----------------------------------------------------------------
 *
 * The score is sent as:
 *
 * {"shot":n, "time": time,  "x":x, "y":y,}
 *
 * Shots are stored in memory as they occur.  When a new TCPIP
 * connection is made, all of the accumulated scores are sent out
 * to update the new PC client
 *
 *--------------------------------------------------------------*/

void send_replay(shot_record_t *shot,                                                       //  record
                 unsigned int   shot_number)
{

  if ( (shot->session_type & SESSION_VALID) != 0 )                                          // Do we have a shot record?
  {
    if ( (json_session_type == SESSION_EMPTY)                                               // Any shot will do
         || ((json_session_type & SESSION_SIGHT) && (shot->session_type & SESSION_SIGHT))   // Only sighters
         || ((json_session_type & SESSION_MATCH) && (shot->session_type & SESSION_MATCH)) ) // Only match
    {
      build_json_score(shot, SCORE_TCPIP);
    }
    else                                                                                    // No shot record
    {
      _xs[0] = 0;
    }
  }
  else                                                                                      // No shot record
  {
    _xs[0] = 0;
  }

  /*
   * All done, return
   */
  return;
}

/*----------------------------------------------------------------
 *
 * @function: remap_target
 *
 * @brief: Remaps shot into a different target
 *
 * @return: Pellet location remapped to centre bull
 *
 *----------------------------------------------------------------
 *
 *  For example a five bull target looks like
 *
 *     **        **
 *     **        **
 *          **
 *          **
 *     **        **
 *     **        **
 *
 * The function prepare_score locates the pellet onto the paper
 * This function finds the closest bull and then maps the pellet
 * onto the centre one.t->shot_time
 *--------------------------------------------------------------*/
typedef struct
{
  real_t x;                 // X location of Bull
  real_t y;                 // Y location of Bull
} new_target_t;

#define LAST_BULL (-1000.0)
#define D5_74     (74 / 2)  // Five bull air rifle is 74mm centre-centre
const new_target_t five_bull_air_rifle_74mm[] = {
    {-D5_74,    D5_74    },
    {D5_74,     D5_74    },
    {0,         0        },
    {-D5_74,    -D5_74   },
    {D5_74,     -D5_74   },
    {LAST_BULL, LAST_BULL}
};

#define D5_79 (79 / 2)      // Five bull air rifle is 79mm centre-centre
const new_target_t five_bull_air_rifle_79mm[] = {
    {-D5_79,    D5_79    },
    {D5_79,     D5_79    },
    {0,         0        },
    {-D5_79,    -D5_79   },
    {D5_79,     -D5_79   },
    {LAST_BULL, LAST_BULL}
};

#define D12_H (191.0 / 2.0) // Twelve bull air rifle 95mm Horizontal
#define D12_V (195.0 / 3.0) // Twelve bull air rifle 84mm Vertical
const new_target_t twelve_bull_air_rifle[] = {
    {-D12_H,    D12_V + D12_V / 2   },
    {0,         D12_V + D12_V / 2   },
    {D12_H,     D12_V + D12_V / 2   },
    {-D12_H,    D12_V / 2           },
    {0,         D12_V / 2           },
    {D12_H,     D12_V / 2           },
    {-D12_H,    -D12_V / 2          },
    {0,         -D12_V / 2          },
    {D12_H,     -D12_V / 2          },
    {-D12_H,    -(D12_V + D12_V / 2)},
    {0,         -(D12_V + D12_V / 2)},
    {D12_H,     -(D12_V + D12_V / 2)},
    {LAST_BULL, LAST_BULL           }
};

#define O12_H (144.0 / 2.0) // Twelve bull air rifle Orion
#define O12_V (190.0 / 3.0) // Twelve bull air rifle Orion
const new_target_t orion_bull_air_rifle[] = {
    {-O12_H,    O12_V + O12_V / 2   },
    {0,         O12_V + O12_V / 2   },
    {O12_H,     O12_V + O12_V / 2   },
    {-O12_H,    O12_V / 2           },
    {0,         O12_V / 2           },
    {O12_H,     O12_V / 2           },
    {-O12_H,    -O12_V / 2          },
    {0,         -O12_V / 2          },
    {O12_H,     -O12_V / 2          },
    {-O12_H,    -(O12_V + O12_V / 2)},
    {0,         -(O12_V + O12_V / 2)},
    {O12_H,     -(O12_V + O12_V / 2)},
    {LAST_BULL, LAST_BULL           }
};

//                                0  1  2  3              4                        5              6  7  8  9  10           11 12
const new_target_t *ptr_list[] = {0, 0, 0, 0, five_bull_air_rifle_74mm, five_bull_air_rifle_79mm, 0,
                                  0, 0, 0, 0, orion_bull_air_rifle,     twelve_bull_air_rifle};

static void remap_target(shot_record_t *shot)
{
  real_t distance, closest; // Distance to bull in clock ticks
  real_t dx, dy;            // Best fitting bullseye
  int    i;
  dx = 0.0;
  dy = 0.0;

  new_target_t *ptr;        // Bull pointer

  if ( (json_target_type <= 1) || (json_target_type > sizeof(ptr_list) / sizeof(new_target_t *)) )
  {
    return;                 // Check for limits
  }

  /*
   * Find the closest bull
   */
  DLT(DLT_APPLICATION, SEND(CONSOLE, sprintf(_xs, "remap_target x: %4.2fmm  y: %4.2fmm", shot->x_mm, shot->y_mm);))

  ptr = ptr_list[json_target_type];
  if ( ptr == 0 )     // Check for unassigned targets
  {
    return;
  }
  closest = 100000.0; // Distance to closest bull

  /*
   * Loop and find the closest target
   */
  i = 0;
  while ( ptr->x != LAST_BULL )
  {
    distance = sqrt(SQ(ptr->x - shot->x_mm) + SQ(ptr->y - shot->y_mm));
    DLT(DLT_APPLICATION, SEND(CONSOLE, sprintf(_xs, " distance: %4.2f", distance);))
    if ( distance < closest ) // Found a closer one?
    {
      closest = distance;     // Remember it
      dx      = ptr->x;
      dy      = ptr->y;       // Remember the closest bull
      DLT(DLT_APPLICATION, SEND(CONSOLE, sprintf(_xs, "Target: %d   dx: %4.2f   dy: %4.2f", i, dx, dy);))
    }
    ptr++;
    i++;
  }

  /*
   * Remap the pellet to the centre one
   */
  shot->x_mm -= dx;
  shot->y_mm -= dy;
  DLT(DLT_APPLICATION, SEND(CONSOLE, sprintf(_xs, "x: %4.2f , y: %4.2f ", shot->x_mm, shot->y_mm);))

  /*
   *  All done, return
   */
  return;
}
