ten-point-nine/freETarget/Software/ESP32/main/json.c

/*-------------------------------------------------------
 *
 * JSON.c
 *
 * JSON driver
 *
 * ----------------------------------------------------*/
#include "esp_timer.h"
#include "nvs.h"
#include "nvs_flash.h"
#include "string.h"
// #include <sys/param.h>
#include "esp_ota_ops.h"

#define JSON_C // This is the JSON file
#include "freETarget.h"
#include "board_assembly.h"
#include "helpers.h"
#include "analog_io.h"
#include "ctype.h"
#include "diag_tools.h"
#include "json.h"
#include "mechanical.h"
#include "mfs.h"
#include "nonvol.h"
#include "serial_io.h"
#include "stdio.h"
#include "token.h"
#include "serial_io.h"
#include "wifi.h"
#include "bluetooth.h"
#include "timer.h"
#include "ota.h"
#include "calibrate.h"

/*
 *  Function Prototypes
 */
static void handle_json(void);                                                 // Breakdown the JSON and execute it
void        show_echo(void);                                                   // Display the current settings
static void show_names(int v);
static void set_trace(int v);                                                  // Set the trace on and off
static void unlock_target(unsigned int password);                              // Unlock the target
static void lock_target(unsigned int password);                                // Lock the target
static bool good_input(unsigned int conversion, char next, unsigned int show); // Determine if the input is valid

/*
 *  Variables
 */
char input_JSON[EXTRA_LARGE_STRING]; // JSON input buffer

void        show_echo(void);         // Display the current settings
static void show_names(int v);
static void set_trace(int v);        // Set the trace on and off
static void set_50m(int x);          // Configure for 50m pistol

const json_message_t JSON[] = {
    //  show     token        value stored in RAM             convert                 service fcn()     NONVOL location      Initial Value
    //  PS Value
    {HIDE,        "\"50M\"",             0,                           IS_VOID,                &set_50m,           0,                          0,          0 },
    {HIDE + LOCK, "\"ANGLE\":",          &json_sensor_angle,          IS_INT32,               0,                  NONVOL_SENSOR_ANGLE,        45,         0 },
    {HIDE + LOCK, "\"ANGLE_OFFSET\":",   &json_sensor_angle_offset,   IS_FLOAT,               0,                  NONVOL_SENSOR_ANGLE_OFFSET, 0,          15},
    {SHOW + LOCK, "\"AUX_MODE\":",       &json_aux_mode,              IS_INT32,               0,                  NONVOL_AUX_PORT_ENABLE,     RS485,      6 },
    {HIDE,        "\"BYE\"",             0,                           IS_INT32,               &bye,               0,                          0,          0 },
    {HIDE,        "\"CAL\":",            0,                           IS_INT32,               &calibrate,         0,                          0,          0 },
    {HIDE,        "\"DOWNLOAD\"",        &json_OTA_download_size,     IS_INT32,               &OTA_serial,        0,                          0,          0 },
    {HIDE,        "\"ECHO\"",            0,                           IS_VOID,                &show_echo,         0,                          0,          0 },
    {HIDE + LOCK, "\"FACE_STRIKE\":",    &json_face_strike,           IS_INT32,               0,                  NONVOL_FACE_STRIKE,         0,          0 },
    {HIDE,        "\"FLASH\"",           0,                           IS_INT32,               &OTA_serial,        0,                          0,          0 },
    {SHOW + LOCK, "\"FOLLOW_THROUGH\":", &json_follow_through,        IS_INT32,               0,                  NONVOL_FOLLOW_THROUGH,      0,          0 },
    {HIDE + LOCK, "\"INIT\"",            0,                           IS_VOID,                &init_nonvol,       0,                          0,          0 },
    {SHOW + LOCK, "\"KEEP_ALIVE\":",     &json_keep_alive,            IS_INT32,               0,                  NONVOL_KEEP_ALIVE,          120,        0 },
    {SHOW + LOCK, "\"LED_BRIGHT\":",     &json_LED_PWM,               IS_INT32,               &set_LED_PWM_now,   NONVOL_LED_PWM,             50,         0 },
    {HIDE,        "\"MFS?\"",            0,                           IS_VOID,                &mfs_show,          0,                          0,          0 },
    {SHOW + LOCK, "\"MFS_TAP_1\":",      &json_mfs_tap_1,             IS_MFS,                 0,                  NONVOL_MFS_TAP_A,           PAPER_SHOT, 2 },
    {SHOW + LOCK, "\"MFS_TAP_2\":",      &json_mfs_tap_2,             IS_MFS,                 0,                  NONVOL_MFS_TAP_B,           TARGET_ON,  2 },
    {SHOW + LOCK, "\"MFS_HOLD_1\":",     &json_mfs_hold_1,            IS_MFS,                 0,                  NONVOL_MFS_HOLD_A,          PAPER_FEED, 2 },
    {SHOW + LOCK, "\"MFS_HOLD_2\":",     &json_mfs_hold_2,            IS_MFS,                 0,                  NONVOL_MFS_HOLD_B,          TARGET_OFF, 2 },
    {SHOW + LOCK, "\"MFS_HOLD_12\":",    &json_mfs_hold_12,           IS_MFS,                 0,                  NONVOL_MFS_HOLD_AB,         LED_ADJUST, 2 },
    {SHOW + LOCK, "\"MFS_HOLD_C\":",     &json_mfs_hold_c,            IS_MFS,                 0,                  NONVOL_MFS_HOLD_C,          MFS_C_LED,  2 },
    {SHOW + LOCK, "\"MFS_HOLD_D\":",     &json_mfs_hold_d,            IS_MFS,                 0,                  NONVOL_MFS_HOLD_D,          MFS_D_LED,  2 },
    {SHOW + LOCK, "\"MFS_SELECT_CD\":",  &json_mfs_select_cd,         IS_MFS,                 0,                  NONVOL_MFS_SELECT_CD,       RAPID_HIGH, 2 },
    {SHOW + LOCK, "\"MIN_RING_TIME\":",  &json_min_ring_time,         IS_INT32,               0,                  NONVOL_MIN_RING_TIME,       500,        0 },
    {SHOW + LOCK, "\"NAME_ID\":",        &json_name_id,               IS_INT32,               &show_names,        NONVOL_NAME_ID,             0,          0 },
    {SHOW + LOCK, "\"NAME_TEXT\":",      (int *)&json_name_text,      IS_TEXT + SSID_SIZE,    &show_names,        NONVOL_NAME_TEXT,           0,          8 },
    {HIDE + LOCK, "\"OTA\"",             0,                           0,                      &OTA_load_json,     0,                          0,          0 },
    {SHOW + LOCK, "\"OTA_URL\":",        (int *)&json_ota_url,        IS_TEXT + URL_SIZE,     0,                  NONVOL_OTA_URL,             0,          11},
    {HIDE,        "\"P\"",               0,                           IS_VOID,                &paper_start,       0,                          0,          0 },
    {SHOW + LOCK, "\"PAPER_ECO\":",      &json_paper_eco,             IS_INT32,               0,                  NONVOL_PAPER_ECO,           0,          0 },
    {SHOW + LOCK, "\"PAPER_SHOT\":",     &json_paper_shot,            IS_INT32,               0,                  NONVOL_PAPER_SHOT,          0,          5 },
    {SHOW + LOCK, "\"PAPER_TIME\":",     &json_paper_time,            IS_INT32,               0,                  NONVOL_PAPER_TIME,          500,        0 },
    {SHOW + LOCK, "\"PCNT_LATENCY\":",   &json_pcnt_latency,          IS_INT32,               0,                  NONVOL_PCNT_LATENCY,        0,          1 },
    {SHOW + LOCK, "\"POWER_SAVE\":",     &json_power_save,            IS_INT32,               0,                  NONVOL_POWER_SAVE,          0,          0 },
    {SHOW,        "\"RAPID_COUNT\":",    &json_rapid_count,           IS_INT32,               0,                  0,                          0,          0 },
    {SHOW,        "\"RAPID_ENABLE\":",   &json_rapid_enable,          IS_INT32,               0,                  0,                          0,          0 },
    {SHOW,        "\"RAPID_TIME\":",     &json_rapid_time,            IS_FLOAT,               0,                  0,                          0,          0 },
    {SHOW,        "\"RAPID_WAIT\":",     &json_rapid_wait,            IS_FLOAT,               0,                  0,                          0,          0 },
    {SHOW + LOCK, "\"REMOTE_ACTIVE\":",  &json_remote_active,         IS_INT32,               0,                  NONVOL_REMOTE_ACTIVE,       0,          8 },
    {SHOW + LOCK, "\"REMOTE_KEY\":",     &json_remote_key,            IS_TEXT + KEY_SIZE,     0,                  NONVOL_REMOTE_KEY,          0,          8 },
    {SHOW + LOCK, "\"REMOTE_URL\":",     (int *)&json_remote_url,     IS_TEXT + URL_SIZE,     0,                  NONVOL_REMOTE_URL,          0,          8 },
    {HIDE,        "\"RESET\"",           0,                           IS_VOID,                &esp_restart,       0,                          0,          0 },
    {SHOW + LOCK, "\"SEND_MISS\":",      &json_send_miss,             IS_INT32,               0,                  NONVOL_SEND_MISS,           0,          0 },
    {SHOW + LOCK, "\"SENSOR\":",         (int *)&json_sensor_dia,     IS_FLOAT,               0,                  NONVOL_SENSOR_DIA,          232000,     0 },
    {SHOW,        "\"SN\":",             &json_serial_number,         IS_FIXED,               0,                  NONVOL_SERIAL_NO,           0xffff,     0 },
    {SHOW,        "\"SESSION\":",        &json_session_type,          IS_INT32,               &start_new_session, 0,                          0,          0 },
    {SHOW + LOCK, "\"STEP_COUNT\":",     &json_step_count,            IS_INT32,               0,                  NONVOL_STEP_COUNT,          0,          0 },
    {SHOW + LOCK, "\"STEP_RAMP\":",      &json_step_ramp,             IS_INT32,               0,                  NONVOL_STEP_RAMP,           0,          4 },
    {SHOW,        "\"STEP_START\":",     &json_step_start,            IS_INT32,               0,                  NONVOL_STEP_START,          0,          4 },
    {SHOW + LOCK, "\"STEP_TIME\":",      &json_step_time,             IS_INT32,               0,                  NONVOL_STEP_TIME,           0,          0 },
    {HIDE,        "\"TARGET_TYPE\":",    &json_target_type,           IS_INT32,               0,                  NONVOL_TARGET_TYPE,         0,          0 },
    {HIDE + LOCK, "\"TEST\":",           0,                           IS_INT32,               &self_test,         0,                          0,          0 },
    {SHOW + LOCK, "\"TOKEN\":",          &json_token,                 IS_INT32,               0,                  NONVOL_TOKEN,               0,          0 },
    {SHOW,        "\"TRACE\":",          0,                           IS_INT32,               &set_trace,         0,                          0,          0 },
    {SHOW,        "\"VERSION\"",         0,                           IS_INT32,               &POST_version,      0,                          0,          0 },
    {SHOW + LOCK, "\"VREF_LO\":",        (int *)&json_vref_lo,        IS_FLOAT,               &set_VREF,          NONVOL_VREF_LO,             1250,       0 },
    {SHOW + LOCK, "\"VREF_HI\":",        (int *)&json_vref_hi,        IS_FLOAT,               &set_VREF,          NONVOL_VREF_HI,             2000,       0 },
    {SHOW + LOCK, "\"WIFI_CHANNEL\":",   &json_wifi_channel,          IS_INT32,               0,                  NONVOL_WIFI_CHANNEL,        6,          0 },
    {SHOW + LOCK, "\"WIFI_GATEWAY\":",   (int *)&json_wifi_gateway,   IS_TEXT + IP_SIZE,      0,                  NONVOL_WIFI_GATEWAY,        0,          9 },
    {SHOW + LOCK, "\"WIFI_HIDDEN\":",    &json_wifi_hidden,           IS_INT32,               0,                  NONVOL_WIFI_HIDDEN,         0,          1 },
    {SHOW + LOCK, "\"WIFI_IP\":",        (int *)&json_wifi_static_ip, IS_TEXT + IP_SIZE,      0,                  NONVOL_WIFI_IP,             0,          9 },
    {SHOW + LOCK, "\"WIFI_PWD\":",       (int *)&json_wifi_pwd,       IS_SECRET + PWD_SIZE,   0,                  NONVOL_WIFI_PWD,            0,          0 },
    {SHOW + LOCK, "\"WIFI_RESET\":",     &json_wifi_reset_first,      IS_INT32,               0,                  NONVOL_WIFI_RESET_FIRST,    1,          3 },
    {SHOW + LOCK, "\"WIFI_SSID\":",      (int *)&json_wifi_ssid,      IS_TEXT + SSID_SIZE,    0,                  NONVOL_WIFI_SSID,           0,          0 },
    {SHOW + LOCK, "\"X_OFFSET\":",       (int *)&json_x_offset,       IS_FLOAT,               0,                  NONVOL_X_OFFSET,            0,          7 },
    {SHOW + LOCK, "\"Y_OFFSET\":",       (int *)&json_y_offset,       IS_FLOAT,               0,                  NONVOL_Y_OFFSET,            0,          7 },
    {SHOW + LOCK, "\"Z_OFFSET\":",       &json_z_offset,              IS_INT32,               0,                  NONVOL_Z_OFFSET,            13,         0 },
    {HIDE + LOCK, "\"NORTH_X\":",        &json_north_x,               IS_INT32,               0,                  NONVOL_NORTH_X,             0,          0 },
    {HIDE + LOCK, "\"NORTH_Y\":",        &json_north_y,               IS_INT32,               0,                  NONVOL_NORTH_Y,             0,          0 },
    {HIDE + LOCK, "\"EAST_X\":",         &json_east_x,                IS_INT32,               0,                  NONVOL_EAST_X,              0,          0 },
    {HIDE + LOCK, "\"EAST_Y\":",         &json_east_y,                IS_INT32,               0,                  NONVOL_EAST_Y,              0,          0 },
    {HIDE + LOCK, "\"SOUTH_X\":",        &json_south_x,               IS_INT32,               0,                  NONVOL_SOUTH_X,             0,          0 },
    {HIDE + LOCK, "\"SOUTH_Y\":",        &json_south_y,               IS_INT32,               0,                  NONVOL_SOUTH_Y,             0,          0 },
    {HIDE + LOCK, "\"WEST_X\":",         &json_west_x,                IS_INT32,               0,                  NONVOL_WEST_X,              0,          0 },
    {HIDE + LOCK, "\"WEST_Y\":",         &json_west_y,                IS_INT32,               0,                  NONVOL_WEST_Y,              0,          0 },
    {SHOW,        "\"ATHLETE\":",        (int *)&json_athlete,        IS_TEXT + LARGE_STRING, 0,                  NONVOL_ATHELETE,            0,          10},
    {SHOW,        "\"EVENT\":",          (int *)&json_event,          IS_TEXT + LARGE_STRING, 0,                  NONVOL_EVENT,               0,          10},
    {SHOW,        "\"TARGET_NAME\":",    (int *)json_target_name,     IS_TEXT + LARGE_STRING, 0,                  NONVOL_TARGET_NAME,         0,          10},
    {HIDE,        "\"LOCK\":",           0,                           IS_INT32,               &lock_target,       0,                          0,          12},
    {HIDE,        "\"UNLOCK\":",         0,                           IS_INT32,               &unlock_target,     0,                          0,          12},
    {0,           0,                     0,                           0,                      0,                  0,                          0,          0 }
};

/*-----------------------------------------------------
 *
 * @function: freeETarget_json
 *
 * @brief: Accumulate input from the serial port
 *
 * @return: None
 *
 *-----------------------------------------------------
 *
 * The format of the JSON stings used here is
 *
 * {"LABLE":value }
 *
 * {"ECHO":0"}
 * {"ECHO":0, "DIP":8}
 * {"DIP":9, "SENSOR":230.0, "ECHO":0}
 * {"TEST":7, "ECHO":0}
 * {"PAPER":1, "DELAY":5, "PAPER":0, "TEST":16}
 *
 * Find the lable, ex "DIP": and save in the
 * corresponding memory location
 *
 *-----------------------------------------------------*/
static unsigned int in_JSON           = 0;
static unsigned int got_right_bracket = 0;
static bool         not_found;
static bool         keep_space;         // Set to 1 if keeping spaces
static bool         got_left_bracket;   // Set to 1 if we have a bracket
unsigned int        from_BlueTooth = 0; // Count of characters from the BlueTooth port

void freeETarget_json(void *pvParameters)
{
  char ch;

  DLT(DLT_INFO, SEND(CONSOLE, sprintf(_xs, "freeETarget_json()");))

  while ( 1 )
  {
    IF_NOT(IN_OPERATION)
    {
      vTaskDelay(ONE_SECOND);
      continue;
    }

    IF_IN(IN_RAPID) // Ignore anything coming in while in rapid mode
    {
      if ( serial_available(ALL) != 0 )
      {
        DLT(DLT_INFO, SEND(CONSOLE, sprintf(_xs, "Input ignored during rapid fire");))
        while ( serial_available(ALL) != 0 )
        {
          ch = serial_getch(ALL);
        }
      }
      vTaskDelay(TICK_10ms);
      continue;
    }

    /*
     * See if anything is waiting and if so, add it in
     */
    while ( (serial_available(ALL) != 0) )         // Something waiting for us?
    {
      from_BlueTooth = serial_available(AUX_PORT); // How much from the BlueTooth port?
      ch             = serial_getch(ALL);

      if ( json_aux_mode != RS485 )                // Not RS485 mode
      {
        serial_putch(ch, ALL);                     // Echo back to all ports
      }
      else                                         // If in RS485 mode, do not echo back to AUX
      {
        serial_putch(ch, SOME);                    // because RS485 diesables receive during transmit
      }

                                                   /*
                                                    * Parse the stream
                                                    */

      if ( ch == '\n' ) // New Line
      {
        ch = ',';       // Convert to a comma
      }

      if ( ch == '\r' ) // Carriage Return, ignore it
      {
        continue;
      }

      switch ( ch )
      {
        case '{':
          in_JSON           = 0;
          input_JSON[0]     = 0;
          got_right_bracket = 0;
          got_left_bracket  = true;
          keep_space        = 0;
          break;

        case '}':
          if ( in_JSON != 0 )
          {
            got_left_bracket  = false;
            got_right_bracket = in_JSON;
            handle_json();         // Fall through to manage the JSON message
            vTaskDelay(TICK_10ms);
            serial_flush(ALL);
          }
          break;

        case 0x08:                 // Backspace
          if ( in_JSON != 0 )
          {
            in_JSON--;
          }
          input_JSON[in_JSON] = 0; // Null terminate
          break;

        case '*':                  // Connected to PC over BT or Wifi
          POST_version();
          if ( from_BlueTooth != 0 )
          {
            Bluetooth_start_new_connection();
          }

        case '^':                     // Special case for European keyboards which have a different "*" key
          ch = '"';                   // Convert and fall through

        case '"':                     // Start or end of text
          keep_space = (keep_space ^ 1) & 1;

        default:
          if ( (ch != ' ') || keep_space )
          {
            input_JSON[in_JSON] = ch; // Add in the latest
            if ( in_JSON < (sizeof(input_JSON) - 1) )
            {
              in_JSON++;
            }
            input_JSON[in_JSON] = 0;  // Null terminate
          }
          break;
      } // End switch

    } // End if char available
    vTaskDelay(TICK_10ms);
  }

  /*
   *  Never get here
   */
}

/*-----------------------------------------------------
 *
 * @function: handle_json
 *
 * @brief:  Breakdown the JSON and handle it
 *
 * @return: None
 *
 *-----------------------------------------------------
 *
 * The input stream is parsed one JSON token at a time
 * and the JSON[] is used to determine the action
 *
 *-----------------------------------------------------*/
static void handle_json(void)
{
  int   x;
  float f;
  int   i, j, k;
  char  s[64];          // Place to store a string
  int   m;

  run_state |= IN_HTTP; // Parsing a JON string

  /*
   * Found out where the braces are, extract the contents.
   */
  not_found = true;
  k         = 0;

  for ( i = 0; i != got_right_bracket; i++ )                // Go across the JSON input
  {
    j = 0;                                                  // Index across the JSON token table

    while ( (JSON[j].token != 0) )                          // Cycle through the tokens
    {
      x = 0;
      if ( JSON[j].token != 0 )
      {
        k = instr(&input_JSON[i], JSON[j].token);           // Compare the input against the list of JSON tags
        if ( k > 0 )                                        // Non zero, found something
        {
          not_found = false;                                // Read and convert the JSON value
          if ( good_input(JSON[j].convert, input_JSON[i + k], JSON[j].show) == false )
          {
            SEND(ALL, sprintf(_xs, "\r\nInvalid input or locked: {%s}\r\n", input_JSON);)
            break;                                          // Invalid input
          }

          switch ( JSON[j].convert & IS_MASK )
          {
            default:
            case IS_VOID:                                   // Void, default to zero
            case IS_FIXED:                                  // Fixed cannot be changed
              x = 0;
              break;

            case IS_TEXT:                                   // Convert to text
            case IS_SECRET:
              while ( input_JSON[i + k] != '"' )            // Skip to the opening quote
              {
                k++;
              }
              k++;                                          // Advance to the text

              m    = 0;
              s[0] = 0;                                     // Put in a null
              while ( input_JSON[i + k] != '"' )            // Skip to the opening quote
              {
                s[m] = input_JSON[i + k];                   // Save the value
                m++;
                s[m] = 0;                                   // Null terminate
                k++;
              }

              if ( JSON[j].value != NULL )
              {
                strcpy((char *)JSON[j].value, s);           // Save the value
              }

              if ( JSON[j].non_vol != 0 )                   // Save to persistent storage if present
              {
                nvs_set_str(my_handle, JSON[j].non_vol, s); // Store into NON-VOL
              }

              break;

            case IS_MFS:
            case IS_INT32:                                  // Convert an integer
              if ( (input_JSON[i + k] == '0') && ((input_JSON[i + k + 1] == 'X') || (input_JSON[i + k + 1] == 'x')) ) // Is it Hex?
              {
                x = (to_int(input_JSON[i + k + 2]) << 4) + to_int(input_JSON[i + k + 3]);
              }
              else
              {
                x = atoi(&input_JSON[i + k]);
              }

              if ( JSON[j].value != 0 )
              {
                *JSON[j].value = x;                         // Save the value
              }
              if ( JSON[j].non_vol != 0 )
              {
                nvs_set_i32(my_handle, JSON[j].non_vol, x); // Store into NON-VOL
              }

              break;

            case IS_FLOAT:                                  // Convert a floating point number

              f = atof(&input_JSON[i + k]);                 // Float
              x = f * FLOAT_SCALE;                          // Integer
              if ( JSON[j].value != 0 )
              {
                *(double *)JSON[j].value = f;               // Working Value
              }
              if ( JSON[j].non_vol != 0 )
              {
                nvs_set_i32(my_handle, JSON[j].non_vol,
                            x);                             // Store into NON-VOL as an integer * 1000
              }

              break;
          }

          {
            if ( JSON[j].f != 0 ) // Call the handler if it is available
            {
              JSON[j].f(x);
            }
          }
        }

        j++;
      }
      nvs_commit(my_handle); // Save to memory
    }
  }
  /*
   * Report an error if input not found
   */
  if ( (not_found == true) )
  {
    SEND(ALL, sprintf(_xs, "\r\n\r\nCannot decode: {%s}\r\n", input_JSON);)
  }

  /*
   * All done
   */
  run_state &= ~IN_HTTP; // FInished parsing the JSON input
  in_JSON           = 0; // Start Over
  got_right_bracket = 0; // Need to wait for a new Right Bracket
  got_left_bracket  = false;
  input_JSON[0]     = 0; // Clear the input
  return;
}

/*-----------------------------------------------------
 *
 * @function: show_echo
 *
 * @brief: Display the current settings
 *
 * @return: None
 *
 *-----------------------------------------------------
 *
 * Loop and display the settings
 *
 *-----------------------------------------------------*/

void show_echo(void)
{
  int                    i, j;
  char                   str_c[32]; // String holding buffers
  mfs_action_t          *mfs_ptr;
  unsigned int           dip;
  char                  *ABCD[]            = {"A", "B", "C", "D"};
  const esp_partition_t *running_partition = esp_ota_get_running_partition();
  esp_app_desc_t         running_app_info;

  SEND(ALL, sprintf(_xs, "\r\n{\r\n");)
  target_name(str_c);
  SEND(ALL, sprintf(_xs, "\"NAME\":              \"%s\",\r\n", str_c);)

  /*
   * Loop through all of the JSON tokens
   */

  serial_to_all(NULL, EVEN_ODD_BEGIN);
  i = 0;
  while ( JSON[i].token != 0 )             // Still more to go?
  {
    if ( ((JSON[i].show & SHOW) != 0)      // The entry is visible
         && (JSON[i].value != NULL) )      // and it has a value ?
    {
      switch ( JSON[i].convert & IS_MASK ) // Display based on it's type
      {
        default:
        case IS_VOID:
          break;

        case IS_TEXT:
        case IS_SECRET:
          strcpy(str_c, (char *)(JSON[i].value));
          if ( (JSON[i].convert & IS_MASK) == IS_SECRET )
          {
            strncpy(str_c, "*************************************************", strlen(str_c));
          }

          SEND(ALL, sprintf(_xs, "%-18s \"%s\", ", JSON[i].token, str_c);)
          break;

        case IS_MFS: // Covert to a switch ID
          mfs_ptr = mfs_find(*JSON[i].value);
          if ( mfs_ptr != NULL )
          {
            SEND(ALL, sprintf(_xs, "%-18s \"(%d) - %s\", ", JSON[i].token, *JSON[i].value, mfs_ptr->text);)
          }
          break;

        case IS_INT32:
        case IS_FIXED:
          SEND(ALL, sprintf(_xs, "%-18s %d, ", JSON[i].token, *JSON[i].value);)
          break;

        case IS_FLOAT:
          SEND(ALL, sprintf(_xs, "%-18s %6.2f, ", JSON[i].token, *(double *)JSON[i].value);)
          break;
      }
      vTaskDelay(10);
    }
    i++;
  }

  /*
   * Finish up with the special cases
   */
  serial_to_all(_xs, EVEN_ODD_END);                                                    // End the even odd line
  SEND(ALL, sprintf(_xs, "\r\n*** STATUS ***\r\n");)
  serial_to_all(NULL, EVEN_ODD_BEGIN);                                                 // Start over again
  SEND(ALL, sprintf(_xs, "\"SN\":                %d", json_serial_number);)
  SEND(ALL, sprintf(_xs, "\"TRACE\":             %d,", is_trace);)                     //
  SEND(ALL, sprintf(_xs, "\"CALIBRATION\":       %d,", calibration_is_valid);)         //
  SEND(ALL, sprintf(_xs, "\"RUN_STATE\":         %d,", run_state);)                    // Internal running state is enabled
  SEND(ALL, sprintf(_xs, "\"CONNECTION_LIST\":   %02X,", connection_list);)            // Who is attached
  SEND(ALL, sprintf(_xs, "\"RUNNING_MINUTES\":   %0.2f,", run_time_seconds() / 60.0);) // On Time
  SEND(ALL, sprintf(_xs, "\"TIME_TO_SLEEP\":     %4.2f,", (float)power_save / (float)(ONE_SECOND * 60));) // How long until we sleep
  SEND(ALL, sprintf(_xs, "\"TEMPERATURE\":       %4.2f,", temperature_C());)                              // Temperature in degrees C
  SEND(ALL, sprintf(_xs, "\"RELATIVE_HUMIDITY\": %4.2f,", humidity_RH());)
  SEND(ALL, sprintf(_xs, "\"TIMER_COUNT\":       %d,",
                    (int)(SHOT_TIME * OSCILLATOR_MHZ));) // Maximum number of clock cycles to record shot (target dependent)
  SEND(ALL, sprintf(_xs, "\"V12\":               %4.2f,", v12_supply());)                   // 12 Volt LED supply
  if ( VREF_FB & board_mask )
  {
    SEND(ALL, sprintf(_xs, "\"VREF_LO\":           %4.2f,", vref_measure());)               // Reference voltage measurement
  }
  SEND(ALL, sprintf(_xs, "\"VBOARD_REV\":        %4.2f,", (real_t)vBD_measure() / 1000.0);) // Board Revision voltage measurement
  WiFi_MAC_address(str_c);
  SEND(ALL, sprintf(_xs, "\"WiFi_MAC\":          \"%02X:%02X:%02X:%02X:%02X:%02X\",", str_c[0], str_c[1], str_c[2], str_c[3], str_c[4],
                    str_c[5]);)
  WiFi_my_IP_address(str_c);
  SEND(ALL, sprintf(_xs, "\"WiFi_IP_ADDRESS\":   \"%s\",", str_c);)

  if ( json_wifi_ssid[0] == 0 )                                                     // The SSID is undefined
  {
    target_name(str_c);
    SEND(ALL, sprintf(_xs, "\"WiFi_MODE\":         \"Access Point: %s\",", str_c);) // Print out the IP address
  }
  else
  {
    SEND(ALL, sprintf(_xs, "\"WiFi_MODE\":         \"Connected to %s\",", (char *)&json_wifi_ssid);)
  }

  if ( json_token == TOKEN_NONE )
  {
    SEND(ALL, sprintf(_xs, "\"TOKEN_RING\":       %d,", my_ring);) // My token ring address
  }

  dip = read_DIP();
  strcpy(_xs, "\"DIP\":              \"");                         // Display the digital input
  for ( i = 0; i != 4; i++ )
  {
    if ( (dip & (1 << (3 - i))) == 0 )
    {
      strcat(_xs, ABCD[i]);
    }
    else
    {
      strcat(_xs, "-");
    }
  }
  strcat(_xs, "\"");
  serial_to_all(_xs, ALL);

  SEND(ALL, sprintf(_xs, "\"VERSION\":          %s, ", SOFTWARE_VERSION);)          // Current software version
  esp_ota_get_partition_description(running_partition, &running_app_info);
  SEND(ALL, sprintf(_xs, "\"OTA BUILD\":        %s, ", running_app_info.version);)  // Current OTA identifier
  SEND(ALL, sprintf(_xs, "\"LOCKED\":            \"%s\"", no_yes[json_lock != 0]);) // The JSON is locked

#if ( INCLUDE_OTA_ECHO )
  OTA_get_versions(running_app_version, new_app_version);
  SEND(ALL, sprintf(_xs, "Running OTA:          %s", running_app_version);)
  SEND(ALL, sprintf(_xs, "New OTA:              %s", new_app_version);)
#endif

  nvs_get_i32(my_handle, NONVOL_PS_VERSION, &j);
  SEND(ALL, sprintf(_xs, "\"PS_VERSION\":        %d,", j);)                                           // Current persistent storage version
  SEND(ALL, sprintf(_xs, "\"BD_REV\":            %d.%d.%d", (revision() / 100), ((revision() % 100) / 10),
                    (revision() % 10));)                                                              // Current board version
  SEND(ALL, sprintf(_xs, "\"SPLINE FIT\":        %s,", calibration_is_valid ? "\"Yes\"" : "\"No\"");) // Current persistent storage version
                                                                                                      /*
                                                                                                       *  All done, return
                                                                                                       */
  serial_to_all(_xs, EVEN_ODD_END);                                                                   // End the even odd line
  SEND(ALL, sprintf(_xs, "}\r\n");)

  return;
}

/*-----------------------------------------------------
 *
 * @function: show_names
 *
 * @brief: Display the list of names
 *
 * @return: None
 *
 *-----------------------------------------------------
 *
 * If the name is Loop and display the settings
 *
 *-----------------------------------------------------*/

static void show_names(int v)
{
  unsigned int i;

  if ( v != 0 )
  {
    return;
  }

  SEND(ALL, sprintf(_xs, "\r\nTarget Names\r\n");)

  i = 0;
  while ( names[i] != 0 )
  {
    SEND(ALL, sprintf(_xs, "%d: \"%s\", \r\n", i, names[i]);)
    i++;
  }

  if ( json_name_text[0] != 0 )
  {
    SEND(ALL, sprintf(_xs, "%d: \"%s\", \r\n", JSON_NAME_TEXT, json_name_text);) // Look for a user defined name
  }
  else
  {
    SEND(ALL, sprintf(_xs, "%d: \"FET-UserDefined\", \r\n", JSON_NAME_TEXT);)    // Look for a user defined name
    SEND(ALL, sprintf(_xs, "%d: \"Userdefined\", \r\n", JSON_NAME_CLIENT);)      // Look for a user defined name
    SEND(ALL, sprintf(_xs, "%d: \"FET-serialNumber\", \r\n", JSON_NAME_SN);)     // Use the serial number as the name
  }

  /*
   *  All done, return
   */
  return;
}

/*-----------------------------------------------------
 *
 * @function: set_trace
 *
 * @brief:    Turn the software trace on and off
 *
 * @return: None
 *
 *-----------------------------------------------------
 *
 * XOR the current trace level with the new input from
 * the user.
 *
 * XOR allows the user to turn settings off without
 * affecting the other settings.
 *
 *-----------------------------------------------------*/
static void set_trace(int trace)                     // Trace mask on or off
{
  unsigned int i;

  if ( trace == 0 )                                  // Used to turn off tracing
  {
    is_trace = 0;
  }
  is_trace ^= trace;                                 // XOR the input
  is_trace |= (DLT_FATAL | DLT_CRITICAL | DLT_INFO); // Info and critical is always enabled

  i = 0;
  while ( dlt_names[i].dlt_text != 0 )               // Print the help
  {
    if ( (is_trace & dlt_names[i].dlt_mask) != 0 )
    {
      SEND(ALL, sprintf(_xs, "\r\n+ ");)
    }
    else
    {
      SEND(ALL, sprintf(_xs, "\r\n  ");)
    }
    SEND(ALL, sprintf(_xs, "%03d %s", dlt_names[i].dlt_mask, dlt_names[i].dlt_text);)
    i++;
  }

  SEND(ALL, sprintf(_xs, "\r\n");)

  return;
}

/*-----------------------------------------------------
 *
 * @function: set_50m
 *
 * @brief:    Configure for 50m Pistol Target
 *
 * @return: None
 *
 *-----------------------------------------------------
 *
 * Change the settings for 50m target
 *
 *-----------------------------------------------------*/
static void set_50m(int x)
{
  int temp;

  json_paper_time = 0;
  nvs_set_i32(my_handle, NONVOL_PAPER_TIME, json_paper_time);

  json_sensor_dia = 707 * 1000;
  nvs_set_i32(my_handle, NONVOL_SENSOR_DIA, json_sensor_dia);

  json_step_count = 0;
  nvs_set_i32(my_handle, NONVOL_STEP_COUNT, json_step_count);

  json_z_offset = 18;
  nvs_set_i32(my_handle, NONVOL_Z_OFFSET, json_z_offset);

  json_vref_lo = 3.00; // Set the target reference voltage to 3.0 volts
  temp         = json_vref_lo * FLOAT_SCALE;
  nvs_set_i32(my_handle, NONVOL_VREF_LO, temp);

  /*
   *  Save the changes
   */
  if ( nvs_commit(my_handle) == ESP_OK )
  {
    SEND(ALL, sprintf(_xs, "\r\nTarget updated for 50m rifle");)
  }
  else
  {
    SEND(ALL, sprintf(_xs, "\r\nUpdate for 50m rifle failed");)
  }

  /*
   *  All done, return
   */
  return;
}

/*-----------------------------------------------------
 *
 * @function: lock_target
 *
 * @brief:    Lock the JSON commands
 *
 * @return: None
 *
 *-----------------------------------------------------
 *
 * If the target is unlocked, then we can set in a new
 * password and save it to non-volatile memory.
 *
 *-----------------------------------------------------*/
static void lock_target(unsigned int password) // Password entered by the user
{
  /*
   * First, test to see if there is a non-zero lock code?
   */
  if ( json_lock == 0 )
  {
    json_lock = password;                          // Set the lock code
    nvs_set_i32(my_handle, NONVOL_LOCK, password); // Save the lock code
    return;
  }

  if ( json_lock == password )                     // Password does not match
  {
    json_lock = 0;                                 // Unlock the target
    SEND(ALL, sprintf(_xs, "Target Unlocked\r\n");)
    return;
  }

  /*
   *  All done, return
   */
  return;
}

/*-----------------------------------------------------
 *
 * @function: unlock_target
 *
 * @brief:    Lock and unlock the JSON commands
 *
 * @return:  None
 *
 *-----------------------------------------------------
 *
 * The target will be unlocked if the user entered
 * password matches the one stored in nonvol.
 *
 *-----------------------------------------------------*/
static void unlock_target(unsigned int password) // Password entered by the user
{
  /*
   * If the password matches the programmed value, then
   * unlock the target
   */
  if ( json_lock == password )
  {
    json_lock = 0; // Unlock the target
    SEND(ALL, sprintf(_xs, "Configuration unlocked\r\n");)
    return;
  }

  if ( json_lock == 0 )
  {
    json_lock = password;                          // Lock the target
    nvs_set_i32(my_handle, NONVOL_LOCK, password); // Save the lock code
    SEND(ALL, sprintf(_xs, "Configuration locked\r\n");)
    return;
  }

  /*
   *  All done, return
   */
  return;
}

/*-----------------------------------------------------
 *
 * @function: good_input
 *
 * @brief:    Determine if the input is valid and can be used
 *
 * @return:   TRUE if the input is valid
 *
 *-----------------------------------------------------
 *
 * The input is valid if
 *
 * 1 - No input is required
 * 2 - The input text is not empty
 * 3 - The JSON is not locked
 * 4 - The JSON does not require a lock
 *
 *-----------------------------------------------------*/
static bool good_input(unsigned int conversion, // What kind of input is it?
                       char         next,       // Next input character
                       unsigned int show        // Item display status
)
{

  if ( (conversion == IS_VOID) || (conversion == IS_FIXED) )
  {
    return true;                                // No input required
  }

  if ( (next == ',') || (next == '}') )         // Empty field
  {
    return false;
  }

  if ( json_lock == 0 )                         // The JSON is not locked
  {
    return true;
  }

  if ( (show & LOCK) == 0 )                     // This item is not locked
  {
    return true;
  }

  return false;                                 // Must be locked
}

/*-----------------------------------------------------
 *
 * @function: json_find_first
 *
 * @brief:    Read a number from the input stream
 *
 * @return:   Next number from the input stream
 *
 *-----------------------------------------------------
 *
 * The input stream is a JSON array of numbers, ex:
 * [1, 2, 3, 4, 5]
 *
 * This function will read the next number from the array and return it.
 *
 * Exceptions.
 *
 * Quotes are removed.
 * Double quotes are converted to a space and comma
 *
 *-----------------------------------------------------*/
static int next_value;     // Index to the next value to read

bool json_find_first(void) // Find the first element starting with [
{
  int i;
  next_value = 0;
  DLT(DLT_CALIBRATION, SEND(CONSOLE, sprintf(_xs, "json_find_first()");))

  /*
   *  Find the start of the JSON
   */
  while ( input_JSON[next_value] != '[' ) // Look for an opening array
  {
    if ( input_JSON[next_value] == 0 )
    {
      next_value = 0;                     // Reached the end, exit
      return false;                       // Report nothing here
    }
    next_value++;                         // Try the next
  }

  /*
   *  Found it, advance and return
   */
  next_value++; // Skip past the opening [
  DLT(DLT_CALIBRATION, SEND(CONSOLE, sprintf(_xs, "Start of array @%d characters", next_value);))
  return true;  // Show we have something
}

/*----------------------------------------------------------------
 *
 * function: json_get_array_next()
 *
 * brief: Extract the next number from an array
 *
 * return: Value extracted from the array
 *
 *----------------------------------------------------------------
 *
 * The input is a text array of numbers in the form
 *
 * 1, 2, 3, 4....<NULL>
 *
 * The function looks for the first comma and then does an atof
 * conversion of the text.
 *
 * The function also handles the case where the text array is
 * of the form "1", "2", "3""4" by converting the quotes to spaces
 * and "" to <space><comma>
 *
 *----------------------------------------------------------------*/
bool json_get_array_next(int   type,  //  Expected input type
                         void *value) // Where to put the result
{
  int i;

  /*
   *  Check to see if this is the first time through and if so, filter the data
   */
  if ( type == IS_FIRST )
  {
    i = 0;
    while ( (input_JSON[i] != 0) && (input_JSON[i] != '!') )
    {
      if ( input_JSON[i] == '"' )       // The next character is a quote
      {
        input_JSON[i] = ' ';            // Make it a space
        if ( input_JSON[i + 1] == '"' ) // And check that the one after that
        {                               // isn't another quote
          input_JSON[i + 1] = ',';      // And if it is, make it a comma
        }
      }

      if ( input_JSON[i] == '\r' )      // The next character is a carriage return
        input_JSON[i] = ',';            // Make it a comma
      i++;
    }
    next_value = 0;
    return 0;
  }

  /*
   *  Check to see if it is time to leave
   */
  if ( (input_JSON[next_value] == 0) || (input_JSON[next_value] == ']') || (input_JSON[next_value] == '!') ) // Bumped up to the end
  {
    return false;
  }

  /*
   *  Convert the next field
   */
  switch ( type )
  {
    case IS_FLOAT:
      *(real_t *)value = atof(&input_JSON[next_value]); // Float
      break;

    case IS_VOID:
      break;
  }

  /*
   *  Prepare the next field
   */
  while ( input_JSON[next_value] != ',' )                                                                      // Got the next field
  {
    next_value++;
    if ( (input_JSON[next_value] == 0) || (input_JSON[next_value] == ']') || (input_JSON[next_value] == '!') ) // Bumped up to the end
    {
      return true;
    }
  }

  next_value++;

  /*
   * All done, return
   */
  return true;
}

void json_tabata(bool enable) // Enable or disable Tabata mode
{
  if ( enable == true )
  {
    set_status_LED(LED_TABATA_ENABLED);
  }
  else
  {
    set_status_LED(LED_READY);
  }

  return;
}
