ten-point-nine/freETarget/Software/ESP32/main/TCPIP/OTA.c

/*-------------------------------------------------------
 *
 * file: OTA.c
 *
 * Over the Air Update
 *
 *-------------------------------------------------------
 *
 * Over the air update
 *
 * See:https://docs.espressif.com/projects/esp-idf/en/stable/esp32/api-reference/system/ota.html
 *
 * ----------------------------------------------------*/
#include <string.h>
#include <inttypes.h>
#include "esp_system.h"
#include "esp_event.h"
#include "esp_ota_ops.h"
#include "esp_app_format.h"
#include "esp_http_client.h"

#include "esp_flash_partitions.h"
#include "esp_partition.h"
#include "errno.h"
#include "gpio_types.h"
#include "driver\gpio.h"

#include "freETarget.h"
#include "board_assembly.h"
#include "helpers.h"
#include "diag_tools.h"
#include "ota.h"
#include "json.h"
#include "gpio.h"
#include "gpio_define.h"
#include "serial_io.h"
#include "timer.h"

/*
 *  Macros
 */
#define BUFFSIZE              1024
#define HASH_LEN              32                              /* SHA-256 digest length */
#define OTA_URL_SIZE          256
#define OTA_SERIAL_BLOCK_SIZE (sizeof(ota_write_data) - 32)   // Number of bytes we can accept at once
#define OTA_SERIAL_TIMEOUT    ((time_count_t)10 * ONE_SECOND) // 10 second timeout

/*
 *  Local functions
 */
static void http_cleanup(esp_http_client_handle_t client);
static void OTA_halt_process(char *LED_status, char *error_message);
static void OTA_check_header(char *ota_write_data, int data_read, const esp_partition_t *update_partition,
                             const esp_partition_t *running_partition, const esp_partition_t *boot_partition);

/*
 * Variables
 */
static char          ota_write_data[BUFFSIZE + 1] = {0};
static char          download_url[OTA_URL_SIZE];
extern const uint8_t server_cert_pem_start[] asm("_binary_ca_cert_pem_start");
extern const uint8_t server_cert_pem_end[] asm("_binary_ca_cert_pem_end");

/*----------------------------------------------------------------
 *
 * @function: OTA_load()
 *
 * @brief:    Over The Air Update
 *
 * @return: None
 *---------------------------------------------------------------
 *
 * An OTA update consists of the following steps:
 *
 * 1 - Connect to the server and begin to download the file
 * 2 - On the first packet, verify the header against the current
 * 3 - Line by line, write the data to the OTA partition
 * 4 - When the file is complete, close the file
 * 5 - Set the new partition as the boot partition
 * 6 - Halt and wait for a power cycle to start the new firmware
 *
 * TEST:
 *   {"OTA_URL":"targetbin.app/OTA"}
 *
 *------------------------------------------------------------*/
void OTA_load(void)
{
  esp_ota_handle_t         update_handle = 0;
  const esp_partition_t   *update_partition;
  const esp_partition_t   *boot_partition           = esp_ota_get_boot_partition();
  const esp_partition_t   *running_partition        = esp_ota_get_running_partition();
  bool                     image_header_was_checked = false;
  int                      data_read;
  int                      binary_file_length = 0;
  esp_http_client_handle_t client;
  int                      http_count = 0; // How many records have we read in

  esp_http_client_config_t config = {
      .cert_pem          = (char *)server_cert_pem_start,
      .timeout_ms        = OTA_TIMEOUT,
      .keep_alive_enable = true,
  };

  /*
   *  Start
   */
  DLT(DLT_OTA, SEND(CONSOLE, sprintf(_xs, "OTA_load()");))
  set_status_LED(LED_OTA_DOWNLOAD);

  if ( boot_partition == NULL )
  {
    DLT(DLT_CRITICAL, SEND(CONSOLE, sprintf(_xs, "Boot partition not available");))
    return;
  }

  if ( running_partition == NULL )
  {
    DLT(DLT_CRITICAL, SEND(CONSOLE, sprintf(_xs, "Running partition not available");))
    return;
  }

#if ( 0 )
  if ( boot_partition != running_partition )
  {
    DLT(DLT_OTA, SEND(CONSOLE, sprintf(_xs, "Configured OTA boot partition at offset 0x%08" PRIx32 ", but running from offset 0x%08" PRIx32,
                                       configured->address, running->address);))
    DLT(DLT_INFO,
        SEND(ALL, sprintf(_xs, "(This can happen if either the OTA boot data or preferred boot image become corrupted somehow.)");))
  }
  DLT(DLT_OTA, SEND(CONSOLE, sprintf(_xs, "Running partition type %d subtype %d (offset 0x%08" PRIx32 ")", running->type, running->subtype,
                                     running->address);))
#endif

  /*
   *  Prepare to open the file
   */
  sprintf(download_url, "%s/freeETarget.bin", json_ota_url);
  config.url = download_url;

  DLT(DLT_OTA, SEND(CONSOLE, sprintf(_xs, "OTA download URL: \"%s\"", config.url);))

  client = esp_http_client_init(&config);

  if ( client == NULL )
  {
    OTA_halt_process(LED_OTA_FAILED_CONNECT, "Failed to initialise HTTP connection");
  }

  if ( esp_http_client_open(client, 0) != ESP_OK )
  {
    OTA_halt_process(LED_OTA_FAILED_CONNECT, "Failed to open HTTP connection");
  }

  /*
   *  Successsfully got the file
   */
  update_partition = esp_ota_get_next_update_partition(NULL);
  assert(update_partition != NULL);
  DLT(DLT_OTA, SEND(CONSOLE, sprintf(_xs, "Writing to partition subtype %d at offset 0x%" PRIx32, update_partition->subtype,
                                     update_partition->address);))

  esp_http_client_fetch_headers(client);
#if ( OTA_FETCH_HEADER == true )
  esp_http_client_read(client, ota_write_data, BUFFSIZE); // Throw away the HTTP header
  printf("\r\nHeader data_read: %s\n", ota_write_data);
#endif

  /*
   *  Prepare for the update
   */
  if ( esp_ota_begin(update_partition, OTA_WITH_SEQUENTIAL_WRITES, &update_handle) != ESP_OK )
  {
    http_cleanup(client);
    esp_ota_abort(update_handle);
    OTA_halt_process(LED_OTA_FAILED_CONNECT, "esp_ota_begin failed");
  }

  DLT(DLT_OTA, SEND(CONSOLE, sprintf(_xs, "esp_ota_begin succeeded");))

  /*
   * Loop here and bring in the file
   */
  http_count = 0;
  while ( 1 )
  {
    http_count++;
    if ( (http_count & 32) == 0 )
    {
      set_status_LED(LED_OTA_DOWNLOAD); // Slowly blink the LED
    }
    else
    {
      set_status_LED(LED_OTA_DOWNLOAD_T);
    }

    data_read = esp_http_client_read(client, ota_write_data, BUFFSIZE); // Read the data from the server

    if ( data_read < 0 )                                                // Error getting data
    {
      esp_http_client_close(client);
      esp_http_client_cleanup(client);
      OTA_halt_process(LED_OTA_FAILED_CONNECT, "Error: HTTP data read error");
    }

    if ( data_read > 0 )                       // Have a payload to process
    {
      if ( image_header_was_checked == false ) // First time through, check the header
      {
        OTA_check_header(ota_write_data, data_read, update_partition, running_partition, boot_partition);
        image_header_was_checked = true;
      }
      /*
       * flash the received data into OTA memory. esp_
       */
      if ( esp_ota_write(update_handle, (const void *)ota_write_data, data_read) != ESP_OK )
      {
        http_cleanup(client);
        esp_ota_abort(update_handle);
        OTA_halt_process(LED_OTA_FAILED_CONNECT, "esp_ota_write() failed");
      }
      binary_file_length += data_read;
    }

    if ( data_read == 0 )
    {
      break;
    }
  }

  /*
   *  The download is complete, make sure we have the complete file
   */
  if ( (binary_file_length == 0)                                        // Nothing was read
       || (esp_http_client_is_complete_data_received(client) != true) ) // Not all data was received
  {
    http_cleanup(client);
    esp_ota_abort(update_handle);
    OTA_halt_process(LED_OTA_FAILED_CONNECT, "Error in receiving complete file");
  }

  esp_http_client_cleanup(client);
  set_status_LED(LED_OTA_FINSHED); // Show we are part way done
  DLT(DLT_OTA, SEND(CONSOLE, sprintf(_xs, "Total Write binary data length: %d", binary_file_length);))

  if ( esp_ota_end(update_handle) != ESP_OK )
  {
    OTA_halt_process(LED_OTA_FATAL, "Failed to complete OTA update");
  }

  DLT(DLT_OTA, SEND(CONSOLE, sprintf(_xs, "esp_ota_end succesful");))

  /*
   * Looks good, setup the registers
   */
  if ( esp_ota_set_boot_partition(update_partition) != ESP_OK )
  {
    OTA_halt_process(LED_OTA_FATAL, "esp_ota_set_boot_partition failed");
  }

  /*
   *  All done, halt and wait for the user to restart
   */
  OTA_halt_process(LED_OTA_READY, "Cycle power to start new firmware"); // Reboot the system
  return;
}

void OTA_load_json(int empty)                                           // Shim between JSON and push buttons
{
  OTA_load();                                                           // Load the OTA image from the server
  return;
}

/*----------------------------------------------------------------
 *
 * @function: OTA_serial()
 *
 * @brief:    Take in an OTA file over the serial port
 *
 * @return:   None
 *
 *---------------------------------------------------------------
 *
 * OTA_serial)() takes in an OTA image over the serial port
 *
 * OTA_serial() is almost identical to OTA_load() except that
 * the data comes in over the serial port instead of HTTP.
 * Conseuently, we have to manage the serial port reads and timeouts.
 *
 * The sequence is:
 *
 * PC Client sends message {"DOWNLOAD":size}
 * where size is the number of bytes to follow
 *
 * This function starts and sends a respoinse to incidate the
 * number of bytes that can be sent with each packet.
 *
 * PC                                Target
 * {"DOWNLOAD":size_of_file"}
 *                                   {"DOWNLOAD_BLOCK":Size of download block}
 * Image data records...
 * Image data records...
 * Image data records...
 *
 * Last record
 *                                  {"RESPONSE":"PASS> Cycle power to start new firmware"}
 *
 * An error at any stage results in:
 *                                 {"RESPONSE":"FAIL> Reason for failure"}
 *
 * Debugging information is sent as:
 *                                {"RESPONSE":"INFO> Informational message"}
 *
 *------------------------------------------------------------*/
void OTA_serial(unsigned int OTA_download_size) // Size of the incoming file
{
  esp_ota_handle_t       update_handle = 0;
  const esp_partition_t *update_partition;
  const esp_partition_t *boot_partition           = esp_ota_get_boot_partition();
  const esp_partition_t *running_partition        = esp_ota_get_running_partition();
  bool                   image_header_was_checked = false;
  int                    data_read;          // How many bytes in the record
  int                    record_number  = 0; // Number of records received
  int                    bytes_received = 0; // Total bytes received

  /*
   *  Start, check that the partitions are available
   */
  DLT(DLT_OTA, SEND(CONSOLE, sprintf(_xs, "OTA_serial(%d)", OTA_download_size);))
  set_status_LED(LED_OTA_DOWNLOAD);

  if ( boot_partition == NULL )
  {
    DLT(DLT_CRITICAL, SEND(CONSOLE, sprintf(_xs, "{\"RESPONSE\": \"FAIL> Boot partition not available\"}");))
    return;
  }

  if ( running_partition == NULL )
  {
    DLT(DLT_CRITICAL, SEND(CONSOLE, sprintf(_xs, "{\"RESPONSE\": \"FAIL> Running partition not available\"}");))
    return;
  }

#if ( 0 )
  if ( boot_partition != running_partition )
  {
    DLT(DLT_OTA, SEND(CONSOLE, sprintf(_xs,
                                       "{\"RESPONSE\": \"INFO> Configured OTA boot partition at offset 0x%08" PRIx32
                                       ", but running from offset 0x%08\"}" PRIx32,
                                       configured->address, running->address);))
        SEND(LAST, sprintf(_xs, "(This can happen if either the OTA boot data or preferred boot image become corrupted somehow.)");))
  }
  DLT(DLT_OTA, SEND(LAST, sprintf(_xs, "{\"RESPONSE\": \"INFO> Running partition type %d subtype %d (offset 0x%08" PRIx32 ")\"}",
                                  running->type, running->subtype, running->address);))
#endif

  update_partition = esp_ota_get_next_update_partition(NULL);
  assert(update_partition != NULL);
  DLT(DLT_OTA, SEND(CONSOLE, sprintf(_xs, "{\"RESPONSE\":\"INFO> Writing to partition subtype %d at offset 0x%" PRIx32,
                                     update_partition->subtype, update_partition->address);))
  /*
   *  Prepare for the update
   */
  if ( esp_ota_begin(update_partition, OTA_WITH_SEQUENTIAL_WRITES, &update_handle) != ESP_OK )
  {
    SEND(ALL, sprintf(_xs, "{\"RESPONSE\":\"FAIL> Download begin failed\"}");)
    vTaskDelay(10); // Wait for the message to leave the buffer
    esp_ota_abort(update_handle);
    OTA_halt_process(LED_OTA_FAILED_CONNECT, "esp_ota_begin failed");
  }

  DLT(DLT_OTA, SEND(CONSOLE, sprintf(_xs, "{\"RESPONSE\":\"INFO> esp_ota_begin succeeded\"}");))

  /*
   *  Acknowledge the request and send the packet size
   */
  vTaskDelay(10);                                                            // Wait for the initial message to leave the buffer
  serial_flush(ALL);                                                         // Flush the serial port
  SEND(ALL, sprintf(_xs, "{\"DOWNLOAD_BLOCK\":%d}", OTA_SERIAL_BLOCK_SIZE);) // Packet size

  /*
   * Loop here and bring in the file
   */
  while ( bytes_received < OTA_download_size )                          // Loop for each block
  {
    data_read = OTA_SERIAL_BLOCK_SIZE;
    if ( (OTA_download_size - bytes_received) < OTA_SERIAL_BLOCK_SIZE ) // Last block?
    {
      printf("\r\nLast block\r\n");
      data_read = OTA_download_size - bytes_received;                   // Yes, use a shorter block
    }

    data_read = get_OTA_serial(data_read, &ota_write_data);             // String to return the S-record
    if ( data_read < 0 )                                                // Error getting data
    {
      set_status_LED(LED_OTA_FATAL);                                    // Show the error on the LED
      SEND(ALL, sprintf(_xs, "{\"RESPONSE\":\"FAIL> Download failed to receive data\"}");)
      vTaskDelay(10);                                                   // Wait for the message to leave the buffer
      esp_ota_abort(update_handle);
      OTA_halt_process(LED_OTA_FAILED_CONNECT, "OTA_serial: Error receiving OTA file");
      return;
    }

    bytes_received += data_read;                                        // Keep track of how many bytes we have received

    if ( image_header_was_checked == false )                            // First time through, check the header
    {
      OTA_check_header(ota_write_data, data_read, update_partition, running_partition, boot_partition);
      image_header_was_checked = true;
    }

    /*
     * flash the received data into OTA memory.
     */
    if ( esp_ota_write(update_handle, (const void *)ota_write_data, data_read) != ESP_OK )
    {
      SEND(ALL, sprintf(_xs, "{\"RESPONSE\":\"FAIL> esp_ota_write() failed\"");)
      vTaskDelay(10); // Wait for the message to leave the buffer
      esp_ota_abort(update_handle);
      OTA_halt_process(LED_OTA_FAILED_CONNECT, "esp_ota_write() failed");
      return;
    }
  }

  /*
   *  The download is complete, make sure we have the complete file
   */
  set_status_LED(LED_OTA_FINSHED); // Show we are part way done
  DLT(DLT_OTA, SEND(CONSOLE, sprintf(_xs, "{\"RESPONSE\":\"INFO> Total Write binary data length: %d\"}", bytes_received);))

  if ( esp_ota_end(update_handle) != ESP_OK )
  {
    SEND(ALL, sprintf(_xs, "{\"RESPONSE\":\"FAIL> Failed to complete OTA update\"}");)
    vTaskDelay(10);                // Wait for the message to leave the buffer
    OTA_halt_process(LED_OTA_FATAL, "Failed to complete OTA update");
  }

  DLT(DLT_OTA, SEND(CONSOLE, sprintf(_xs, "{\"RESPONSE\":\"INFO> esp_ota_end succesful\"}");))

  /*
   * Looks good, setup the registers
   */
  if ( esp_ota_set_boot_partition(update_partition) != ESP_OK )
  {
    DLT(DLT_OTA, SEND(CONSOLE, sprintf(_xs, "{\"RESPONSE\":\"FAIL> Failed to set boot partition\"}");))
    vTaskDelay(10); // Wait for the message to leave the buffer
    OTA_halt_process(LED_OTA_FATAL, "esp_ota_set_boot_partition failed");
  }

  /*
   *  All done, halt and wait for the user to restart
   */
  DLT(DLT_CRITICAL, SEND(CONSOLE, sprintf(_xs, "{\"RESPONSE\":\"PASS> Cycle power to start new firmware\"}");))
  vTaskDelay(10);                                                       // Wait for the message to leave the buffer
  OTA_halt_process(LED_OTA_READY, "Cycle power to start new firmware"); // Reboot the system
  return;
}

/*----------------------------------------------------------------
 *
 * @function: OTA_check_header()
 *
 * @brief:    Check the header for the OTA image
 *
 * @return:   Generate an assert if the fil cannot be used
 *---------------------------------------------------------------
 *
 * Check the header for the OTA image
 *
 * Then verify the version so that we don't load the same or
 * older version of the image.
 *
 * An error in this function is fatal, ie we cannot recover
 * and trying to load it again will result in the same error.
 *
 *------------------------------------------------------------*/
static void OTA_check_header(char                  *ota_write_data,    // Data read from server
                             int                    data_read,         // Number of bytes in record
                             const esp_partition_t *update_partition,  // Update partition
                             const esp_partition_t *running_partition, // Running partition
                             const esp_partition_t *boot_partition     // Boot partition
)
{
  esp_app_desc_t         new_app_info;
  esp_app_desc_t         running_app_info;
  const esp_partition_t *last_invalid_app;
  esp_app_desc_t         invalid_app_info;
  int                    i;

  /*
   *  Check that we read enough bytes
   */
  if ( data_read < sizeof(esp_image_header_t) + sizeof(esp_image_segment_header_t) + sizeof(esp_app_desc_t) )
  {
    DLT(DLT_CRITICAL, SEND(CONSOLE, sprintf(_xs, "{\"RESPONSE\": \"FAIL> OTA data size too small\"}");))
    OTA_halt_process(LED_OTA_FATAL, "OTA data size too small");
  }

  /*
   *  Extract the data and print it out
   */
  memcpy(&new_app_info, &ota_write_data[sizeof(esp_image_header_t) + sizeof(esp_image_segment_header_t)], sizeof(esp_app_desc_t));
  DLT(DLT_OTA, SEND(CONSOLE, sprintf(_xs, "New firmware version: %s", new_app_info.version);))

  if ( esp_ota_get_partition_description(running_partition, &running_app_info) == ESP_OK )
  {
    DLT(DLT_OTA, SEND(CONSOLE, sprintf(_xs, "Running firmware version: %s", running_app_info.version);))
  }

  last_invalid_app = esp_ota_get_last_invalid_partition();
  if ( last_invalid_app != NULL )
  {
    if ( esp_ota_get_partition_description(last_invalid_app, &invalid_app_info) == ESP_OK )
    {
      DLT(DLT_OTA, SEND(CONSOLE, sprintf(_xs, "Last invalid firmware version: %s", invalid_app_info.version);))
    }

    if ( memcmp(invalid_app_info.version, new_app_info.version, sizeof(new_app_info.version)) == 0 )
    {
      OTA_halt_process(LED_OTA_FATAL, "New version is the same as invalid version. Rolled back to previous version.");
    }
  }

  /*
   *  Make sure the new software is NEWER than the running software
   */
  i = 0;
  while ( new_app_info.version[i] != 0 )
  {
    if ( new_app_info.version[i] < running_app_info.version[i] )
    {
      DLT(DLT_OTA, SEND(CONSOLE, sprintf(_xs, "{\"RESPOSE\":\"FAIL> New version is older thatn the running version.\"}");))
      vTaskDelay(10);                                            // Wait for the message to leave the buffer
      OTA_halt_process(LED_OTA_FATAL, "New version is older than running version. Abandoning the update.");
    }
    if ( new_app_info.version[i] > running_app_info.version[i] ) // The new is 'bigger' than the old
    {
      return;                                                    // Nothing more to do,
    }
    i++;
  }

  /*
   *  Got to the end and identical all the way along
   */
  DLT(DLT_OTA, SEND(CONSOLE, sprintf(_xs, "{\"RESPOSE\":\"FAIL> New version is older thatn the running version.\"}");))
  vTaskDelay(10); // Wait for the message to leave the buffer
  OTA_halt_process(LED_OTA_FATAL, "New version is the same as running version. Abandoning the update.");
}

/*----------------------------------------------------------------
 *
 * @function: ota_rollback()
 *
 * @brief:    Undo the current partition and go back to the last
 *
 * @return: None
 *---------------------------------------------------------------
 *
 * Check the stored nonvol value against the current persistent
 * storage version and update if needed.
 *
 *------------------------------------------------------------*/
void OTA_rollback(void)
{
  if ( esp_ota_mark_app_invalid_rollback_and_reboot() != ESP_OK )
  {
    OTA_halt_process(LED_OTA_FATAL, "Rollback failed.");   // Reboot the system
  }

  OTA_halt_process(LED_OTA_READY, "Rollbback succesful."); // Reboot the system
}

/*----------------------------------------------------------------
 *
 * @function: http_cleanup()
 *
 * @brief:    Clean up the HTTP client
 *
 * @return:   Nothing
 *---------------------------------------------------------------
 *
 *------------------------------------------------------------*/
static void http_cleanup(esp_http_client_handle_t client)
{
  esp_http_client_close(client);
  return;
}

/*----------------------------------------------------------------
 *
 * @function: ota_partitions
 *
 * @brief:  Show the partition data
 *
 * @return: None
 *---------------------------------------------------------------
 *
 * Display the partition data for the ESP32
 *
 * After a download the partitions are:
 *
 *
 * Boot Partition
 * Type:ESP_PARTITION_TYPE_APP  Subtype:16
 * Address: 0X210000  Size 0x200000
 * Lable: ota_0
 *
 * Running Partition
 * Type:ESP_PARTITION_TYPE_APP  Subtype:16
 * Address: 0X210000 Size :0x200000
 * Lable: ota_0
 *
 * Update Partition
 * Type:ESP_PARTITION_TYPE_APP  Subtype:17
 * Address: 0X410000  Size 0x200000
 * Lable: ota_1
 *
 *------------------------------------------------------------*/
static char *partition_type[] = {"ESP_PARTITION_TYPE_APP", "ESP_PARTITION_TYPE_DATA"};

void OTA_partitions(void)
{
  const esp_partition_t *boot_partition    = esp_ota_get_boot_partition();
  const esp_partition_t *running_partition = esp_ota_get_running_partition();
  const esp_partition_t *update_partition  = esp_ota_get_next_update_partition(NULL);
  esp_app_desc_t         running_app_info;

  esp_ota_get_partition_description(running_partition, &running_app_info);
  SEND(ALL, sprintf(_xs, "\r\nApplication Version: %s\r\n", running_app_info.version);)

  SEND(ALL, sprintf(_xs, "\r\nBoot Partition");)
  if ( boot_partition != NULL )
  {
    SEND(ALL, sprintf(_xs, "\r\nType:%s  Subtype:%d", partition_type[boot_partition->type], boot_partition->subtype);)
    SEND(ALL, sprintf(_xs, "\r\nAddress: 0X%lX  Size: 0x%lX", boot_partition->address, boot_partition->size);)
    SEND(ALL, sprintf(_xs, "\r\nLable: %s\r\n", boot_partition->label);)
  }
  else
  {
    SEND(ALL, sprintf(_xs, " Not available\r\n");)
  }

  SEND(ALL, sprintf(_xs, "\r\nRunning Partition");)
  if ( running_partition != NULL )
  {
    SEND(ALL, sprintf(_xs, "\r\nType:%s  Subtype:%d", partition_type[running_partition->type], running_partition->subtype);)
    SEND(ALL, sprintf(_xs, "\r\nAddress: 0X%lX Size: 0x%lX", running_partition->address, running_partition->size);)
    SEND(ALL, sprintf(_xs, "\r\nLable: %s\r\n", running_partition->label);)
  }
  else
  {
    SEND(ALL, sprintf(_xs, " Not available"); SEND(ALL, sprintf(_xs, "\r\n");))
  }

  SEND(ALL, sprintf(_xs, "\r\nUpdate Partition");)
  if ( update_partition != NULL )
  {
    SEND(ALL, sprintf(_xs, "\r\nType:%s  Subtype:%d", partition_type[update_partition->type], update_partition->subtype);)
    SEND(ALL, sprintf(_xs, "\r\nAddress: 0X%lX  Size: 0x%lX", update_partition->address, update_partition->size);)
    SEND(ALL, sprintf(_xs, "\r\nLable: %s\r\n", update_partition->label);)
  }
  else
  {
    SEND(ALL, sprintf(_xs, " Not available\r\n");)
  }

  return;
}

/*----------------------------------------------------------------
 *
 * @function: OTA_halt_process()
 *
 * @brief:    Manage a situation we can't recover from
 *
 * @return: None
 *---------------------------------------------------------------
 *
 * Display the error LEDs and halt the system.
 *
 * Stay halted until either or the button are pressed.
 *
 *------------------------------------------------------------*/
static void OTA_halt_process(char *LED_status,   // Indicator sent to LEDs
                             char *error_message // Why are we halting
)
{
  set_status_LED(LED_status);

  DLT(DLT_CRITICAL, SEND(CONSOLE, sprintf(_xs, "%s", error_message);))

  serial_flush(ALL);                       // Purge anthing that may be present

  while ( 1 )
  {
    vTaskDelay(ONE_SECOND);
    if ( (DIP_SW_A == 1)                   // Switch A pressed
         || (DIP_SW_B == 1)                // Switch B pressed
         || (serial_available(ALL) != 0) ) // Something on the serial port
    {
      DLT(DLT_CRITICAL, SEND(CONSOLE, sprintf(_xs, "Restarting target");))
      esp_restart();
    }
  }
}

/*----------------------------------------------------------------
 *
 * @function: OTA_compare_versions()
 *
 * @brief:    Find out the version and report if it
 *
 * @return:   None
 *
 *---------------------------------------------------------------
 *
 * Get the OTA version and dsplay them
 *
 *------------------------------------------------------------*/
void OTA_get_versions(char *running_version, // Current running version
                      char *OTA_version)     // Version watiting in OTA
{
  esp_app_desc_t           new_app_info;
  esp_app_desc_t           running_app_info;
  esp_http_client_handle_t client;

  const esp_partition_t *running_partition;

  esp_http_client_config_t config = {
      .cert_pem          = (char *)server_cert_pem_start,
      .timeout_ms        = OTA_TIMEOUT,
      .keep_alive_enable = true,
  };

  /*
   *  Go and fetch the header for the current OTA update
   */
  sprintf(download_url, "%s/freeETarget.bin", json_ota_url);
  config.url = download_url;
  DLT(DLT_OTA, SEND(CONSOLE, sprintf(_xs, "\r\nOTA download URL: \"%s\"", config.url);))

  client = esp_http_client_init(&config);
  if ( client == NULL )
  {
    DLT(DLT_OTA, SEND(CONSOLE, sprintf(_xs, "Cannot start HTTP connection");))
    return;
  }
  if ( esp_http_client_open(client, 0) != ESP_OK )
  {
    DLT(DLT_OTA, SEND(CONSOLE, sprintf(_xs, "Cannot start HTTP connection");))
    return;
  }

  esp_http_client_fetch_headers(client);
  esp_http_client_read(client, ota_write_data, BUFFSIZE); // Read the data from the server
  memcpy(&new_app_info, &ota_write_data[sizeof(esp_image_header_t) + sizeof(esp_image_segment_header_t)], sizeof(esp_app_desc_t));
  strcpy(OTA_version, new_app_info.version);

  /*
   *  Get the current application vesion
   */
  running_partition = esp_ota_get_running_partition();
  esp_ota_get_partition_description(running_partition, &running_app_info);
  strcpy(running_version, running_app_info.version);

  http_cleanup(client);

  return;
}

void OTA_compare_versions(void) // Version watiting in OTA
{
  char new_app_version[sizeof(esp_app_desc_t)];
  char running_app_version[sizeof(esp_app_desc_t)];

  OTA_get_versions(running_app_version, new_app_version);

  SEND(ALL, sprintf(_xs, "\r\nNew firmware version: %s", new_app_version);)
  SEND(ALL, sprintf(_xs, "\r\nRunning firmware version: %s\r\n", running_app_version);)
  if ( strcmp(new_app_version, running_app_version) != 0 )
  {
    SEND(ALL, sprintf(_xs, "\r\nUpdate Available\r\n");)
  }

  return;
}
