ten-point-nine/freETarget/Software/ESP32/main/TCPIP/http_client.c

/*-------------------------------------------------------
 *
 * http_client.c
 *
 * General purpose file to perform HTTP/HTTPS transfers
 * to/from a client
 *
 *------------------------------------------------------
 *
 * This is a generic HTTP/HTTPS client to a server
 *
 * The softwareis based on
 * https://github.com/espressif/esp-idf/blob/8760e6d2a7e19913bc40675dd71f374bcd51b0ae/examples/protocols/esp_http_client/main/esp_http_client_example.c
 *
 *
 * See http_client.h for the various compilation options
 *
 *-----------------------------------------------------*/

#include <string.h>
#include <sys/param.h>
#include <stdlib.h>
#include <ctype.h>
#include "esp_log.h"
#include "nvs_flash.h"
#include "esp_event.h"
#include "esp_netif.h"
#include "esp_tls.h"
#if CONFIG_MBEDTLS_CERTIFICATE_BUNDLE
#include "esp_crt_bundle.h"
#endif

#include "freertos/FreeRTOS.h"
#include "freertos/task.h"
#include "esp_system.h"

#include "esp_http_client.h"

#include "serial_io.h"
#include "freETarget.h"
#include "http_client.h"
#include "diag_tools.h"
#include "json.h"

#define MAX_HTTP_RECV_BUFFER   512
#define MAX_HTTP_OUTPUT_BUFFER 2048

/* Root cert for howsmyssl.com, taken from howsmyssl_com_root_cert.pem

   The PEM file was extracted from the output of this command:
   openssl s_client -showcerts -connect www.howsmyssl.com:443 </dev/null

   The CA root cert is the last cert given in the chain of certs.

   To embed it in the app binary, the PEM file is named
   in the component.mk COMPONENT_EMBED_TXTFILES variable.
*/
#if ( BUILD_HTTPS )
const char howsmyssl_com_root_cert_pem_start[] asm("_binary_howsmyssl_com_root_cert_pem_start");
const char howsmyssl_com_root_cert_pem_end[] asm("_binary_howsmyssl_com_root_cert_pem_end");

const char postman_root_cert_pem_start[] asm("_binary_postman_root_cert_pem_start");
const char postman_root_cert_pem_end[] asm("_binary_postman_root_cert_pem_end");
#endif

/*----------------------------------------------------------------
 *
 * @function: http_client_init
 *
 * @brief:    Initialize the HTTP client and prepare it for operation
 *
 * @return:   TRUE if the client is ready for operation
 *
 *---------------------------------------------------------------
 *
 * Read the nonvol into RAM.
 *
 * If the results is uninitalized then force the factory default.
 * Then check for out of bounds and reset those values
 *
 *------------------------------------------------------------*/
void http_client_init(void)
{
  ESP_ERROR_CHECK(esp_netif_init());
#if ( BUILD_HTTP )
  ESP_ERROR_CHECK(esp_event_loop_create_default());
#endif
}

#if ( BUILD_HTTP )
/*----------------------------------------------------------------
 *
 * @function: _http_event_handler
 *
 * @brief:    Initialize the HTTP client and prepare it for operation
 *
 * @return:   Error state
 *
 *---------------------------------------------------------------
 *
 * Event handler call back for HTTP events
 *
 *------------------------------------------------------------*/
esp_err_t _http_event_handler(esp_http_client_event_t *evt // Event being processed
)
{
  static char *output_buffer;                              // Buffer to store response of http request from event handler
  static int   output_len;                                 // Stores number of bytes read

                                                           /*
                                                            *  Switch to the event that got us here
                                                            */
  switch ( evt->event_id )
  {
    case HTTP_EVENT_ERROR:
      DLT(DLT_COMMUNICATION, printf("HTTP_EVENT_ERROR");)
      break;

    case HTTP_EVENT_ON_CONNECTED:
      DLT(DLT_COMMUNICATION, printf("HTTP_EVENT_ON_CONNECTED");)
      break;

    case HTTP_EVENT_HEADER_SENT:
      DLT(DLT_COMMUNICATION, printf("HTTP_EVENT_HEADER_SENT");)
      break;

    case HTTP_EVENT_ON_HEADER:
      DLT(DLT_COMMUNICATION, printf("HTTP_EVENT_ON_HEADER, key=%s, value=%s", evt->header_key, evt->header_value);)
      break;

    case HTTP_EVENT_ON_DATA:
      DLT(DLT_COMMUNICATION, printf("HTTP_EVENT_ON_DATA, len=%d", evt->data_len);)
      // Clean the buffer in case of a new request
      if ( output_len == 0 && evt->user_data )
      {
        // we are just starting to copy the output data into the use
        memset(evt->user_data, 0, MAX_HTTP_OUTPUT_BUFFER);
      }
      /*
       *  Check for chunked encoding is added as the URL for chunked encoding used in this example returns binary data.
       *  However, event handler can also be used in case chunked encoding is used.
       */
      if ( !esp_http_client_is_chunked_response(evt->client) )
      {
        // If user_data buffer is configured, copy the response into the buffer
        int copy_len = 0;
        if ( evt->user_data )
        {
          // The last byte in evt->user_data is kept for the NULL character in case of out-of-bound access.
          copy_len = MIN(evt->data_len, (MAX_HTTP_OUTPUT_BUFFER - output_len));
          if ( copy_len )
          {
            memcpy(evt->user_data + output_len, evt->data, copy_len);
          }
        }
        else
        {
          int content_len = esp_http_client_get_content_length(evt->client);
          if ( output_buffer == NULL )
          {
            // We initialize output_buffer with 0 because it is used by strlen() and similar functions therefore should be null terminated.
            output_buffer = (char *)calloc(content_len + 1, sizeof(char));
            output_len    = 0;
            if ( output_buffer == NULL )
            {
              DLT(DLT_COMMUNICATION, printf("Failed to allocate memory for output buffer");)
              return ESP_FAIL;
            }
          }
          copy_len = MIN(evt->data_len, (content_len - output_len));
          if ( copy_len )
          {
            memcpy(output_buffer + output_len, evt->data, copy_len);
          }
        }
        output_len += copy_len;
      }

      break;

    case HTTP_EVENT_ON_FINISH:
      DLT(DLT_COMMUNICATION, printf("HTTP_EVENT_ON_FINISH");)
      if ( output_buffer != NULL )
      {
        free(output_buffer);
        output_buffer = NULL;
      }
      output_len = 0;
      break;

    case HTTP_EVENT_DISCONNECTED:
      DLT(DLT_COMMUNICATION, printf("HTTP_EVENT_DISCONNECTED");)
      int       mbedtls_err = 0;
      esp_err_t err         = esp_tls_get_and_clear_last_error((esp_tls_error_handle_t)evt->data, &mbedtls_err, NULL);
      if ( err != 0 )
      {
        DLT(DLT_COMMUNICATION, printf("Last esp error code: 0x%x", err);)
        DLT(DLT_COMMUNICATION, printf("Last mbedtls failure: 0x%x", mbedtls_err);)
      }
      if ( output_buffer != NULL )
      {
        free(output_buffer);
        output_buffer = NULL;
      }
      output_len = 0;
      break;

    case HTTP_EVENT_REDIRECT:
      DLT(DLT_COMMUNICATION, printf("HTTP_EVENT_REDIRECT");)
      esp_http_client_set_header(evt->client, "From", "user@example.com");
      esp_http_client_set_header(evt->client, "Accept", "text/html");
      esp_http_client_set_redirection(evt->client);
      break;
  }
  return ESP_OK;
}

/*----------------------------------------------------------------
 *
 * @function: http_rest_with_url
 *
 * @brief:    REST server called by a URL
 *
 * @return:   None
 *
 *---------------------------------------------------------------
 *
 * Event handler call back for HTTP events
 *
 * The url is of the form http://my_url.com/option/option...
 *
 *------------------------------------------------------------*/
void http_rest_with_url(char *url,    // URL being accessed
                        int   method, // Method being used
                        char *payload // Payload being transferred
)
{
  esp_http_client_config_t config = {
      .host  = url,
      .path  = "/get",
      .query = "esp",
#if ( BUILD_EVENT_HDR )
      .event_handler = _http_event_handler,
#endif
      .user_data             = payload, // Where data comes from and goes to
      .disable_auto_redirect = true,
  };
  esp_http_client_handle_t client = esp_http_client_init(&config);

                                        /*
                                         *  Switch to the method being used
                                         */
  switch ( method )
  {
#if ( INCLUDE_GET )
    case METHOD_GET:
      esp_http_client_set_method(client, HTTP_METHOD_GET);
      if ( esp_http_client_perform(client) == ESP_OK )
      {
        DLT(DLT_COMMUNICATION, SEND(CONSOLE, sprintf(_xs, "HTTP GET Status = %d, content_length = %lld",
                                                     esp_http_client_get_status_code(client), esp_http_client_get_content_length(client));))
      }
      else
      {
        DLT(DLT_COMMUNICATION, SEND(CONSOLE, sprintf(_xs, "HTTP GET request failed %s", url);))
      }
      break;
#endif

#if ( INCLUDE_POST )
    case METHOD_POST:
      esp_http_client_set_url(client, url);
      esp_http_client_set_method(client, HTTP_METHOD_POST);
      esp_http_client_set_header(client, "Content-Type", "application/json");
      esp_http_client_set_post_field(client, payload, strlen(payload));
      if ( esp_http_client_perform(client) == ESP_OK )
      {
        DLT(DLT_COMMUNICATION, SEND(CONSOLE, sprintf(_xs, "HTTP POST Status = %d, content_length = %" PRId64,
                                                     esp_http_client_get_status_code(client), esp_http_client_get_content_length(client));))
      }
      else
      {
        DLT(DLT_COMMUNICATION, SEND(CONSOLE, sprintf(_xs, "HTTP POST request failed:");))
      }
      break;
#endif

#if ( INCLUDE_PUT )
    case METHOD_PUT:
      esp_http_client_set_url(client, url);
      esp_http_client_set_method(client, HTTP_METHOD_PUT);
      err = esp_http_client_perform(client);
      if ( err == ESP_OK )
      {
        DLT(DLT_COMMUNICATION, SEND(CONSOLE, sprintf(_xs, "HTTP PUT Status = %d, content_length = %lld",
                                                     esp_http_client_get_status_code(client), esp_http_client_get_content_length(client));))
      }
      else
      {
        DLT(DLT_COMMUNICATION, SEND(CONSOLE, sprintf(_xs, "HTTP PUT request failed:");))
      }
      break;
#endif

#if ( INCLUDE_PATCH )
    case METHOD_PATCH:
      esp_http_client_set_url(client, url);
      esp_http_client_set_method(client, HTTP_METHOD_PATCH);
      esp_http_client_set_post_field(client, NULL, 0);
      err = esp_http_client_perform(client);
      if ( err == ESP_OK )
      {
        ESP_LOGI(TAG, "HTTP PATCH Status = %d, content_length = %" PRId64, esp_http_client_get_status_code(client),
                 esp_http_client_get_content_length(client));
      }
      else
      {
        DLT(DLT_CRITICAL, printf("HTTP PATCH request failed: %s", esp_err_to_name(err));)
      }
      break;
#endif

#if ( INCLUDE_DELETE )
    case METHOD_DELETE:
      esp_http_client_set_url(client, url);
      esp_http_client_set_method(client, HTTP_METHOD_DELETE);
      err = esp_http_client_perform(client);
      if ( err == ESP_OK )
      {
        ESP_LOGI(TAG, "HTTP DELETE Status = %d, content_length = %" PRId64, esp_http_client_get_status_code(client),
                 esp_http_client_get_content_length(client));
      }
      else
      {
        DLT(DLT_CRITICAL, printf("HTTP DELETE request failed: %s", esp_err_to_name(err));)
      }
      break;
#endif

#if ( INCLUDE_HEAD )
    case METHOD_HEAD:
      esp_http_client_set_url(client, url);
      esp_http_client_set_method(client, HTTP_METHOD_HEAD);
      err = esp_http_client_perform(client);
      if ( err == ESP_OK )
      {
        ESP_LOGI(TAG, "HTTP HEAD Status = %d, content_length = %" PRId64, esp_http_client_get_status_code(client),
                 esp_http_client_get_content_length(client));
      }
      else
      {
        DLT(DLT_CRITICAL, printf("HTTP HEAD request failed: %s", esp_err_to_name(err));)
      }
      break;
#endif
  }
  /*
   *  Method complete, clean up and go back
   */
  esp_http_client_cleanup(client);
  return;
}
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
