ten-point-nine/freETarget/Documentation/Pictures/Target Door.jpg

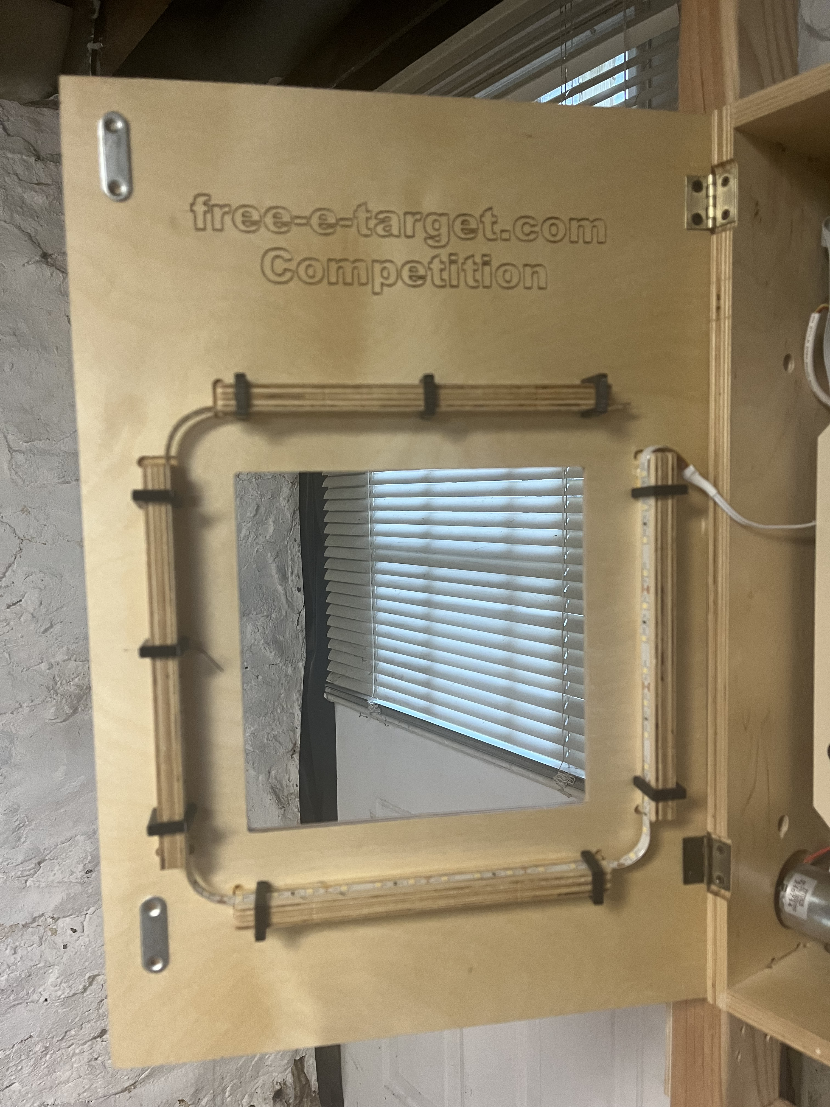
Documentation/Pictures/Target Door.jpg
